magnus188/trimix-analysator/hardware/system-review/electrical/final-power-layout-review/README.md

# Final power-layout review — frozen 9f274 checkpoint

**The board is connected, but its power layout still merits targeted refinement before ordering.** Prioritize the U701 feedback/output-capacitor routes and the U101 bootstrap path; also attempt a properly grounded local REGN capacitor arrangement. These are observed departures from TI's short-loop guidance, not demonstrated instability, damage or invented numerical trace-length failures. No authoritative EDA, CAM or previous receipt was changed by this review.

Source: `hardware/pcb/analyzer/Trimix_Analyzer.kicad_pcb`, SHA256 `9f274fdf198f1bcb871a4fc360e76693f8a5b048553e6a02998141737956514f`. Exact selected parts are U101 BQ25895RTWR, U201 TPS63020DSJR, **U701 TPS61023DRLR**, U114 TPS22950CQDDCRQ1 and U115 TPS259470ARPWR. TPS62840 is absent and was excluded after the requested part name was corrected. The final XML SHA is `4512ae125c98cf091a24bf806f0ca78e14d59bcaffe59626d95386f100e0e609`.

## Four specific refinements

All distances below sum complete native track items along direct pad/track/barrel adjacency witnesses. They are **not** exact clipped terminal-to-terminal lengths, loop inductance, equivalent resistance or current ratings. Pad overlap and segment-entry tails can overcount length; the long paths were also inspected geometrically. Every item UUID and layer is in [native-local-paths.json](native-local-paths.json).

| Priority | Actual frozen geometry | Recommendation and evidence limit |
|---|---|---|
| 1 — U701 feedback | U701.1→R702.1: 29.8415 mm, comprising 3.2866 mm F + 26.5549 mm B, two barrels, 0.15 mm. The pad centres are only about 3.06 mm apart. The B route extends to (25.9226,67.1833), far beyond the local divider. | Bring the divider junction/return close to FB and remove the unnecessary excursion after proving all three FB endpoints remain connected. TI's device-specific SLVAES4 §5 explicitly calls for a short feedback network away from SW/inductor noise. A ground plane between layers provides shielding, but does not justify this excursion. No exact maximum length or achieved regulation error is asserted. |
| 2 — U101 bootstrap C103 | C103 is 0805 F(19,82.3),90°. BTST21→C103.2: 9.1496 mm F/B, two barrels; SW19→C103.1: 9.8375 mm F. | Reposition C103 and coordinate both connections, preserving the direct SW→L101 power path. Straight connections at the existing pose are blocked by SW copper and C108 GND; simply drawing a shorter line would short the board. TI specifies the 47 nF bootstrap connection and short local decoupling; it gives no length-based failure threshold. |
| 3 — U701 output hot loop | U701.6→C702.1: 6.8026 mm of 0.15 mm F routing. It exits left/down, reaches Y58.3836, then returns to C702.1 at (21.9,56.15). C702 GND and U701 GND each have grounded barrel connections. | Review C702 and the SW escape together to shorten/widen the output-capacitor loop. The obvious direct segment intersects CO_SW and fails clearance, even at 0.15 mm; it is not a valid drop-in fix. The output-capacitor return is TI's highest-priority boost switching loop. No load rating follows from the current trace width. |
| 4 — U101 REGN C107 | C107 is 22 µF/25 V X5R1206 at F(8,74.5),90°. U101.22→C107.1: 8.8842 mm total, 2.7097 mm F + 6.1745 mm In2, two barrels; minimum width 0.15 mm. C107 GND reaches the grounded barrel at (8,71.775). | Attempt a local capacitor arrangement with **both** REGN and quiet ground returns completed; retain package/effective-capacitance qualification. The prior B1206 relocation had an unresolved ground return and is not an improvement to adopt. TI requests nearby 4.7 µF/10 V ceramic decoupling for the gate-drive/bias regulator. The nominal full-item DC estimate, 57.47 mΩ, does not bound switching pulse impedance or prove failure. |

Manufacturer basis: [TI TPS61023 datasheet §10.1](https://www.ti.com/lit/ds/symlink/tps61023.pdf), [TI TPS61022/TPS61023 layout application note SLVAES4 §§2,3,5](https://www.ti.com/lit/an/slvaes4/slvaes4.pdf), and [TI BQ25895 pin21/22 and §11.1](https://www.ti.com/lit/ds/symlink/bq25895.pdf). The downloaded application note is included as [slvaes4.pdf](slvaes4.pdf). Straight-segment blocker UUIDs are recorded separately; they prove only that those particular shortcuts fail, not that a local relocation is impossible.

## Switching, capacitors and ground

BQ SW→L101 is entirely F.Cu, with no SW vias or parallel inner-layer power path. L101.2→C104.1 has a direct 4.5358 mm/1.0 mm F witness. The bank is **C104+C105, 44 µF nominal**, plus distributed C201/C202 and the newer local C1084.7 µF. U101.15→C108.1 is 1.5375 mm F. The longer SYS sense/battery/distribution routes must not be mistaken for the complete buck switching hot loop. Nothing here supports adding another arbitrary bulk capacitor; [the existing capacitance audit](../current-path-review/charger-output-audit/README.md) distinguishes typical derating estimates from guaranteed effective capacitance.

U201's two inductor networks remain F-only with no vias. Input C201, output C204–C206 and L201 retain compact front-layer connections: U201.10→C201.1 is 2.6063 mm; U201.4→C204.1 is 2.8374 mm; the two inductor witnesses are 2.85/2.20 mm. Individual pad escapes remain narrower than the power spines. C202 is distributed bulk, not a substitute for C201. FB/VINA and ground connections are present. This accords better with the placement intent in [TI TPS63020 §10.1](https://www.ti.com/lit/ds/symlink/tps63020.pdf), without establishing ripple, stability, current capability or temperature.

The [final root ground/path review](../routing-candidate/final-cleanup/root-review/README.md), independently checked against this source, retains all29 load/monitor witnesses. In1 is one grounded region with105 annular contacts; In2 has eleven grounded regions with21 contacts and is **not continuous**. The final U115 ground barrel (20.75,88.3), C114 ground barrel (11.1,91.1) and C115 ground barrel (12.8,93.95) occupy different local In2 islands, all connected to In1. Global ground continuity does not establish an ideal Kelvin/star return or bound parasitic coupling. Actual ripple/noise remains a separate test.

## USB protection and thermal paths

U115 has C115100 nF input bypass and C1144.7 µF shared output/U114-input capacitance. Input bypass has a 3.5286 mm B witness; output→C114 takes 13.3633 mm over B/F with two barrels. U115 GND→nearest witnessed grounded barrel is 5.347 mm B. The control resistor/capacitor paths are locally connected, but these distances and the split local In2 regions keep bypass/ground transient impedance unqualified. U114 has nearby R119, while its output uses the remotely connected C101; its output→C101 witness is 15.0107 mm F/In2, two barrels. These are genuine limitations to include in the **existing EL11/EL13 source-transition tests**, not a new claim of 6.396 V failure. [TI TPS25947 §8.4](https://www.ti.com/lit/ds/symlink/tps25947.pdf), [TI TPS22950-Q1 §9.4](https://www.ti.com/lit/ds/symlink/tps22950-q1.pdf).

U101 and U201 exposed pads are grounded and have respectively9 and15 package thermal bores. The [separate27-hole process packet](../routing-candidate/final-cleanup/fill-cap-process/README.md) explicitly requires filled, planarized, copper-capped treatment of these24 holes plus3signal VIPPO sites; supplier acceptance and solder-void/flatness results remain pending. U115's heat path is through its IN/OUT lands, not an invented grounded exposed pad; U114 and U701 likewise do not have the U101/U201 exposed-pad arrangement. Geometry/via counts do not determine junction temperature. EL10 still needs the real source/load envelope, PCB copper thermal analysis and enclosure measurements; no current or thermal rating is inferred from DRC.

## Disposition

The four targeted refinements above should be explicitly resolved before ordering, rather than hidden inside the broad EL10 hold. The owner is preparing isolated trials; **this report accepts no new geometry**. Any accepted correction needs native clearance/parity, source-bound conductor/ground witnesses, updated CAM/BOM/process checks and mechanical clearance revalidation. The completed9f274 CAM checkpoint remains intact.

Existing EL10 covers load/thermal and broad ripple testing; EL11 covers the unbounded OVP/cable/short transient envelope; EL13 covers cold/depleted startup. Those holds remain necessary, but do not themselves close avoidable bootstrap/feedback/local-capacitor layout work. No physical test, factory upload, order or release occurred.

Reviewed actual projections: [BQ](bq.png), [TPS63020](tps63020.png), [CO boost](co.png), [USB protection](usb.png). Pale green is the In1 ground projection, not a current-density solution. Both F and B panels use top coordinates.
