magnus188/trimix-analysator/hardware/system-review/software/ota/README.md

# OTA, storage and controlled maintenance review

The existing GitHub/HTTPS updater is retained. Firmware selection now requires the exact pre-v3 or v3 application name for the release version, a matching HTTPS repository URL, a valid release SHA-256 digest and a size fitting the **installed** inactive slot. Metadata may arrive in chunks and is bounded at 32 KiB. The downloaded image descriptor and its flash contents are checked before activation. Normal updates never change partition tables or program the C6.

GitHub documents `digest` in its [release asset API](https://docs.github.com/en/rest/releases/assets). Old releases without this metadata are rejected with a recovery message. This validates integrity relative to the HTTPS release source; it introduces no permanent security fuses or repository signing changes.

## Digital evidence

The latest source-bound rerun and its additional real-ESP-branch storage fixture are documented in [`final-verification/REVIEW.md`](final-verification/REVIEW.md). That pass adds 35 NVS-adapter assertions and concurrent startup-expiry tests. Earlier receipts below remain historical evidence; use the latest source manifest when matching results to code.

- **67** production-core assertions cover metadata, image identity, C6 metadata, update sequencing, injected transfer/activation failures, cancellation, truncation, oversized writes, timeout across clock wrap, storage journal failures, maintenance ownership and whole-startup probation deadlines. AddressSanitizer and UndefinedBehaviorSanitizer pass; the latest run is `ota-startup-sanitizers.log`.
- **24** history checks cover V1/V2 migration, distinct CO/CO₂ meaning, source provenance and new oxygen-cell identity. **13** cylinder checks include malformed input rejection. Both run under the same sanitizers.
- **17** concurrency checks exercise the production storage gate and maintenance coordinator, including 100 competing save/maintenance cycles. AddressSanitizer/UndefinedBehaviorSanitizer and a separate ThreadSanitizer run pass. The original **60** OTA/storage checks also pass after this correction. See `storage-maintenance-race-verification.json` and its three logs.
- `check_nvs_capacity.py` runs Espressif's NVS partition generator against full current journals plus both retained legacy history versions. The synthetic 24 KiB image has 261 free entries; the largest guarded write needs 202 entries including the 128-entry reserve. It contains dummy data and is never flashed.
- `verification.json` records source hashes. Root-level verification supplies fresh integrated firmware builds and the combined suite.
- **13** offline release-validator tests pass. Both existing P4 application binaries pass descriptor/revision/actual-partition checks, and generated release metadata passes the production OTA parser for both families. See `release-startup-review.md`; these checks never publish or install a release.

## Storage and update behavior

One initializer owns NVS and **never erases it automatically**. Settings, history, cylinder profiles and Wi-Fi use CRC-protected, versioned namespaces with inactive-slot writes, readback and a final selector commit. Legacy keys remain readable for rollback. Calibration retains its independent per-channel journal and acquisition compatibility checks. Explicit Forget Wi-Fi removes only credential keys; settings reset never erases calibration/history.

A new OTA image starts with persistence read only. An independent supervisor starts before NVS/LVGL initialization and gives a pending update 60 seconds for essential startup. Acceptance requires observed UI heartbeats, responsive system/acquisition workers and successful NVS initialization, with a 20-second health-check window after service startup inside that overall deadline. Completion and expiry have one atomic winner; late startup cannot accept itself. Optional Wi-Fi initialization runs in its own task. Optional sensors, network association and thermal warm-up are not acceptance requirements. A failing pending image rolls back when a previous image exists; otherwise available recovery UI and wired recovery remain, without erasing data or deliberately causing a reset loop. Changed acquisition revisions deliberately require recalibration rather than relabeling incompatible records.

Maintenance stops measurements and waits for completion before holding storage writes. Failed/cancelled OTA resumes normal work; successful OTA remains held until the coordinated reboot. The GPIO power controller remains responsible for independent held-button shutdown. Current commissioning firmware requires verified battery/charger reserve to install OTA; a bare display without those measurements must use wired recovery.

All application NVS mutations, including calibration slot/selector commits and explicit deletion of legacy Wi-Fi credentials, now use the same storage mutex. A pause request closes admission before waiting for an in-flight transaction. Maintenance reaches its held state only after that transaction completes. If draining exceeds the remaining maintenance budget, maintenance fails and reopens admission; it does not claim that storage is safe to interrupt. Pausing between calibration journal phases rejects the later selector commit and preserves the previous active calibration. A selector commit already in progress completes before the held state is reached.

The lock order is oxygen configuration, then calibration core, then storage. Storage callbacks perform only their low-level persistence operations and never acquire configuration/core locks or call another storage API. Maintenance invokes measurement/flush hooks before taking the storage mutex. This prevents the pause from waiting on a calibration lock while a calibration save waits on storage. The gate's timeout bounds waiting for the mutex, not the underlying flash operation, which cannot be cancelled safely in software.

The C6 recovery build remains separately enabled, hash-pinned and dependent on the staged `slave_fw` partition. Its descriptor checks are now bounded and verify C6 chip identity. No C6 update was performed.

## Remaining physical checks

No firmware flashing, live OTA, flash power cuts, real NVS endurance, C6 programming or device reset was performed. Interruption tests inject failures into the **same installer state machine used by the ESP-IDF adapter**, while the underlying network/flash hardware remains untested. The concurrency tests use the production mutex/gate/coordinator and controlled callbacks representing flash transactions; they do not exercise physical ESP flash timing. A selector commit whose acknowledgement is lost may leave either complete committed version; it must never produce a partial record. Bench-test restart, rollback, saved calibration, low-power updates and recovery with the assembled hardware before treating OTA as qualified.
