magnus188/trimix-analysator/hardware/system-review/electrical/routing-candidate/complete-controls-root-review/README.md

# Completed control routing — parent review

The frozen `b305a4c3…` candidate passes the scoped review needed for isolated final consolidation. Its native KiCad report has zero unconnected items, zero copper/courtyard errors and zero schematic-parity findings. **32 assembly/dangling warnings remain; this is not the manufacturing release.**

[The parent receipt](parent-controls-review.json) verifies every file bound by the controls handoff and records visual inspection of all four actual filled-plane overlays. In1 remains one connected ground region. In2 remains eleven grounded regions; it must not be described as a second continuous plane. The recorded native ground contacts are retained, and the 22 explicit conductor witnesses and seven ordinary-via surface-interface checks pass.

[The independent power-path comparison](power-path-comparison.json) preserves all 29 requested ordered power/monitor witnesses from the completed SYS baseline. Complete trace-item lengths and nominal resistance contributions are diagnostics, not actual equivalent circuit resistance or current/thermal ratings.

The owner may now consolidate exact part metadata, the Q110 manufacturer footprint, C708's ordinary ground-via correction, dead-copper cleanup and markings. That changed source needs fresh native connectivity, ground-contact, parity, ERC-exception, CAM and CAD checks. The three filled/capped interfaces require explicit factory process acceptance; neither their scoped clearance rules nor zero opens establish assembly yield or charging safety.
