magnus188/trimix-analysator/hardware/system-review/electrical/routing-candidate/final-cleanup/README.md

# Completed main routing review checkpoint

The frozen main source is `frozen-bundle/hardware/pcb/analyzer/Trimix_Analyzer.kicad_pcb`, SHA256 `9f274fdf198f1bcb871a4fc360e76693f8a5b048553e6a02998141737956514f`. Native KiCad reports zero violations, zero opens and zero schematic mismatches. It has 169 footprints, 2280 track segments and 301 routed vias. **Manufacturing/physical acceptance remains on HOLD.**

The [geometry manifest](frozen-bundle/review/geometry-handoff-manifest.json) binds PCB, XML, STEP and all 153 maximum-envelope rows. The STEP uses normal pad thickness and unit-scale purchased-part reference models. U110/L201/L701 model files are absent from the installed KiCad model library; their explicit maximum envelopes remain mandatory. No absent or generic model is treated as a dimensional pass.

- [Root power/ground review](root-review/final-power-ground-review.json): all 29 critical conductor witnesses retained, continuous In1, 105 In1 and 21 In2 anchors retained, every In2 region anchored.
- [Aggregate consolidation delta](aggregate-consolidation-delta.json): 519 structural checks; no part, pad, pose or model change during cleanup. The accepted C708 ordinary-via dogbone and dead-copper cleanup are explicit. All 195 physical pad-connectivity partitions are conserved. `prune2/REJECTED.txt` retains the negative control that caught a mistakenly removed live midpoint connection; the accepted source restored it and trimmed only its dead extension.
- [Native routing audit](frozen-bundle/review/routing-audit.json): 12 checks pass. [Via/paste interface audit](frozen-bundle/review/via-assembly-audit.json): all 301 routed vias checked; only the exact three VIPPO sites are permitted in populated SMT paste.
- [Root ERC/firmware contract review](root-review/final-contract-erc-review.json): one precisely reviewed TI-permitted LM66100 ST-ground ERC error, no unexpected ERC findings; all 70 logical firmware-contract checks pass. `source-validation/electrical/electrical-audit.json` has 217 passing assertions; `source-validation/audit-faults/audit-fault-tests.json` accepts the baseline and rejects all 12 injected wiring/value faults.
- [CAM input manifest](frozen-bundle/review/cam-input-manifest.json) binds the unmodified Gerbers, drills, all-component CPL and population ledgers. Independent final CAM results are under `../../main-final-independent/final-9f274fdf/`.

`frozen-bundle/cam/assembly-reference-map.csv` lists every reference, value, MPN, side and position. Separate lists contain 24 factory components, 121 manual components, 6 DNPs and 18 PCB/harness features. `marking-legend.csv` identifies the 146 printed references. The 23 dense assembly-only references have [four locator sheets](assembly-drawings/assembly-only-locators-1.svg); subsequent pages use suffixes 2–4. These show selected pads in blue and use explicit top-view coordinates for both sides. They complement actual CAM silk and the CSV. Raw native Fab exports are retained as diagnostics; their overlapping value text is not claimed to be the clear assembly drawing.

The [factory stencil supplement](factory-stencil/derivation-receipt.json) removes only non-factory paste apertures from a derived copy. The original routed source and full-board paste remain frozen for comparison. The [27-hole process map](fill-cap-process/README.md) requires resin fill and copper cap for all 24 package thermal bores plus 3 signal VIPPO. A quotation must establish drill classification, flatness, stencil thickness/apertures, void/coverage acceptance and double-sided reflow. Neither paste geometry nor a generic capability page proves assembled quality.

Final source-bound enclosure integration, actual sensor/host/harness mating and power entry, cell/NTC identity, USB transient/current/standby/true-off recovery, thermal, EMC, gas and calibration qualification remain separate acceptance gates. No physical test or purchase has been performed.
