magnus188/trimix-analysator/hardware/system-review/electrical/routing-candidate/lower-host-proposal/README.md

# Lower HOST routing scout

The frozen board is unchanged. No patch is proposed. See [blocker.json](blocker.json) for exact search bounds and copper barriers; baseline native DRC is [before-drc.json](before-drc.json). The finite grid search does not prove that every possible freeform route is impossible. The authoritative board was not written.
