magnus188/trimix-analysator/hardware/system-review/electrical/routing-candidate/monitor-root-review/README.md

# Independent review of voltage-monitor routing

The frozen combined candidate `b116e2cce2ee3c3fa5feace5b85cfb85bf47168ddc3b5d846f0f5b15e516bc93` passes this scoped saved-copper and connectivity review. It adds the raw/protected USB voltage-monitor connections and shortens the charger's narrow input-pad escape. The preceding source is `609a6241ce50cbe3d40f7a1676c455092db583875895eeb8236083bf2c5f0ef1`.

[geometry-review.json](geometry-review.json) records unchanged zone definitions, a continuous In1 ground region, anchored In2 ground regions and no lost ground contacts. All three new Ø0.50/0.25 mm vias pass an independent check against every surface-mount land, including same-net lands, with at least 0.05 mm separation. Their closest foreign-copper gaps are 0.2180, 0.4051 and 0.2065 mm, above the 0.20 mm rule. The root reviewer inspected the [ground comparison](ground-and-power.png) and [actual front/back copper overlays](outer-copper.png) on 2026-09-07.

[native-witnesses.json](native-witnesses.json) contains five separate native trace/barrel paths: J101 to R110 and TP1002, U115's protected output to R113, and U114's output to U101 and C101. These paths do not infer conduction through components or filled zones. The raw USB **load** path into U115 remains a separate unfinished connection.

The retained 0.25 mm CAD segment at U101 pin 1 is 0.5375 mm long, but that is not 0.5375 mm of exposed narrow conductor. The adjacent 0.40 mm track directly overlaps the actual pin land, confirmed with native copper shapes; the selected connectivity witness bypasses the nominal narrow segment. Neither track-width arithmetic nor this overlap establishes a thermal or current rating.

The captured owner DRC report has **seven unconnected items**, 14 dangling tracks, seven dangling vias, seven silkscreen overlaps and four silkscreen-over-copper warnings; schematic parity has no findings. These unfinished routes and markings still require correction. The review scripts only read the immutable board snapshots and do not rerun or suppress the owner's DRC.

This result permits continued integration of the bounded change. It is not a fabrication release. Final combined routing, actual electrical limits, manufacturing exports, CAD fit and physical charging/thermal/transient tests remain separate acceptance gates.
