magnus188/trimix-analysator/hardware/system-review/electrical/sensitive-layout-refinement/r504-independent/README.md

# R504 rear excitation-monitor placement — bounded independent review

**Accept the proposal for merged digital review and prototype noise testing; do not describe it as noise-qualified.** There is no demonstrated hard electrical violation from this placement. Keeping the trace outside the inductor projection would be preferable if a short, independently checked route becomes available, but the obvious northern B-layer detours cross the existingHE_3V0 feed. Reopening that topology solely to avoid this projection is not justified by measured evidence currently available.

The read-only source is root's `root-r504/candidate3/Trimix_Analyzer.kicad_pcb`, SHA`c13e2fc459b43f194a146776127d15c0c415135d9d243c21dad3bef570cfc53b`. It does **not** contain the proposed L701 relocation: this review projects the selected [Coilcraft XGL4020-102MEC](https://www.coilcraft.com/pdfs/xgl4020.pdf), max4.3×4.3mm, at the supplied futurecentre(19.5,50.65). Its north edge isY48.5 at maximum body size. The component is specified as a shielded power inductor; no guaranteed external magnetic-field limit was located in its datasheet.

R504 remains10k0.1%, physicallyB(18.25,48),180°. HE_EXC_DIVwrapY48.95 crosses beneath the projected northern part of L701: about.518mm² of the .15mm-wide routed copper lies under the maximum body projection. **Every part of that overlapping copper has continuous In1GND between the F-layer powerstage and B trace** in this frozen source. The local route has a small.084mm² area outside In1 elsewhere near its transition/antipad; the area under the inductor outsideIn1 iszero. A copperplane and shielded core reduce coupling risks but do not prove magnetic isolation or an interference-amplitude bound.

This node is the **excitation diagnostic** (R504/R50510kdivider, C504100nF, U502.7/AIN2); it is separate from the RN501 helium bridge midpoint and its differential measurement. Ideal low-frequencyThevenin resistance is5kΩ, nominaltimeconstant.5ms andcorner318Hz. That RC calculation does not bound noise coupled after the filter, ground bounce, high-frequency parasitics or rectification. [TI ADS122C04 §11.1](https://www.ti.com/lit/ds/symlink/ads122c04.pdf) recommends separating noisy and analog routing, minimizing source/return loop area and preserving good ground-return paths. No manufacturer numerical keep-out distance was found that makes this particular projection an automatic pass or failure.

Firmware `main/sensors/acquisition_engine.cpp:61` doubles the sampled monitor voltage; line65 latches an excitation fault outside2.9–3.1V. Consequently the practical failure to test is false or missed excitation qualification as the CO boost switches between start-up, light-load and normal-load operation. Exercise those states while logging rawAIN2, excitation fault behavior and helium raw differential samples. Observe REGN/HEsupply stability separately; do not infer concentration accuracy from absence of a fault. Check actual transient/ripple response at C504 with an appropriate short-ground probe and compare ADCreadings with COconverterdisabled/enabled.

Two purely geometric northern wraps atY47.2 andY46.4 both intersect HE_3V0copper at the required.20clearance. `review.json` records those blockers and the exact source/firmwarehash; these are read-only rejected suggestions, not new routes or nativeDRC results. No authoritative file or candidate was modified. The merged board still needs the owner's finalnativecheck and fresh source-bound plane coverage inspection.
