magnus188/trimix-analysator/hardware/system-review/electrical/routing-candidate/final-cleanup/root-review/README.md

# Independent final routing review

The frozen main board `9f274fdf…6514f` passes the scoped power and ground review. [The receipt](final-power-ground-review.json) binds all nine geometry-handoff files, the source board, reader, native path inventory and inspected renders. The source files were not modified.

All 29 requested power and voltage-monitor paths have explicit native pad/track/barrel witnesses, with the same ordered physical items as the completed routing checkpoint. One voltage-monitor branch has a shortened unused trace tail; its complete-item diagnostic decreases from 154.291 to 152.210 mΩ. This is not a measured or equivalent path resistance, load-current rating or thermal prediction.

The saved In1 ground fill remains one connected region with all 105 prior annular contacts. In2 has eleven separate grounded regions and retains all 21 prior contacts; it is not a second continuous ground plane. No In1 signal track was introduced. Source geometry shows effectively no removed ground fill beyond polygon numerical precision and 5.508 / 0.351 mm² additional fill on In1 / In2 after unused copper cleanup. Both comparison images were inspected.

Native DRC/parity, the exact ERC exception, manufacturing process inspection and Fusion fit have separate receipts. The manufacturing package is on hold, including explicit factory treatment of the selected signal and package-thermal holes, downstream transient evidence, power-entry qualification, actual cells and connector/seal measurements. This scoped result is not an order release.
