magnus188/trimix-analysator/hardware/system-review/electrical/routing-candidate/sensitive-layout-refinement/root-final-review/README.md

# Independent review of the local power-layout refinement

**Passed digitally for the stated electrical layout scope. Prototype order remains HOLD.**

This review binds the frozen PCB `0962ad86f9834ce71b6439d0f95db603753801153490e78f387a88521e582788`, compared with the preserved routed `9f274fdf…6514f` board. All nine files in its geometry handoff match their declared hashes and sizes. The authoritative board, final CAD integration, manufacturing exports and physical qualification have separate gates.

The four layout concerns identified in the previous inspection have been corrected. These are lengths of complete native trace items, including portions overlapping lands; they are **not extracted loop inductance, equivalent resistance or manufacturer distance limits**.

| Connection | Earlier trace length | Refined trace length |
|---|---:|---:|
| U101 bootstrap pin → C103 | 9.150 mm | 1.356 mm |
| U101 switch pin → C103 | 9.838 mm | 5.621 mm |
| U101 REGN pin → C107 | 8.884 mm | 2.921 mm |
| U701 output pin → C702 | 6.803 mm | 1.603 mm |
| U701 feedback pin → R702 | 29.841 mm | 1.040 mm |

C702 also has a direct front-layer ground connection to U701, independently traced without a barrel transition. The return uses a 0.35 mm trunk and a short 0.20 mm escape at the IC pin; its existing ground anchors are retained and an ordinary ground stitch is added. The feedback trace and output-capacitor connection also remain on the front layer. These changes follow the compact-loop guidance in the [TI BQ25895 datasheet](https://www.ti.com/lit/ds/symlink/bq25895.pdf), [TPS61023 datasheet](https://www.ti.com/lit/ds/symlink/tps61023.pdf) and [TI boost-converter layout note](https://www.ti.com/lit/an/slvaes4/slvaes4.pdf). No claim of measured stability or EMI performance follows from the geometry alone.

All **29 main power and voltage-monitor paths retain exactly the earlier ordered native copper edges**. All 35 inspected local paths are connected. The saved In1 ground fill remains one connected region with 107 grounded anchors. No retained anchor loses contact. The removed C107 front-ground via at (8,71.775) is replaced by the short rear connection to (16.05,78.05). The other new anchors serve the local CO feedback/ground-return area. In2 retains exactly its previous filled geometry: 11 grounded regions and 21 anchors; it is not described as a second continuous ground plane. No signal tracks were introduced on In1 and zone definitions are unchanged.

The full saved-ground comparisons and labeled BQ/CO copper views were visually inspected. Native KiCad reports zero violations, zero unconnected items and zero schematic mismatches for this frozen source. The root receipt is `root-power-layout-review.json`; reproducible native-contact and independent saved-polygon readers are bound there.

The exact C107 replacement, its typical DC-bias comparison and higher startup charge are reviewed separately in `electrical/sensitive-layout-refinement/c107-0805/`. Its 47 µF label must not be mistaken for guaranteed capacitance under voltage, temperature and aging. R504's rear-side excitation-monitor routing is covered by the primary ground plane where it crosses the inductor's northern projection; the separate review in `electrical/sensitive-layout-refinement/r504-independent/` retains switching-noise and false/missed excitation-limit tests. The gas sensors and RN501 bridge reference remain unchanged.

Fresh source/ ERC verification, independent manufacturing-file checks and the real carrier openings for C103/C107/R504 remain separately required. Source-current and transient protection, Guition power entry, actual cells and connector mates, supplier fill/cap/stencil approval and all physical testing remain open. This report does not release an order.
