magnus188/trimix-analysator/hardware/system-review/software/power/off-charge-review/standby-evidence/README.md

The current receipt.json was refreshed from ../../input-isolation/evidence/receipt.json after rerunning the complete prior standby/backlight/maintenance scope plus HIZ tests on current sources. Its log paths identify the authoritative current logs. Older log files in this directory are historical; the complete pre-HIZ receipt/log set is archived in ../archive-before-hiz/standby-evidence/.
