magnus188/trimix-analysator/hardware/cad/previews/front.png

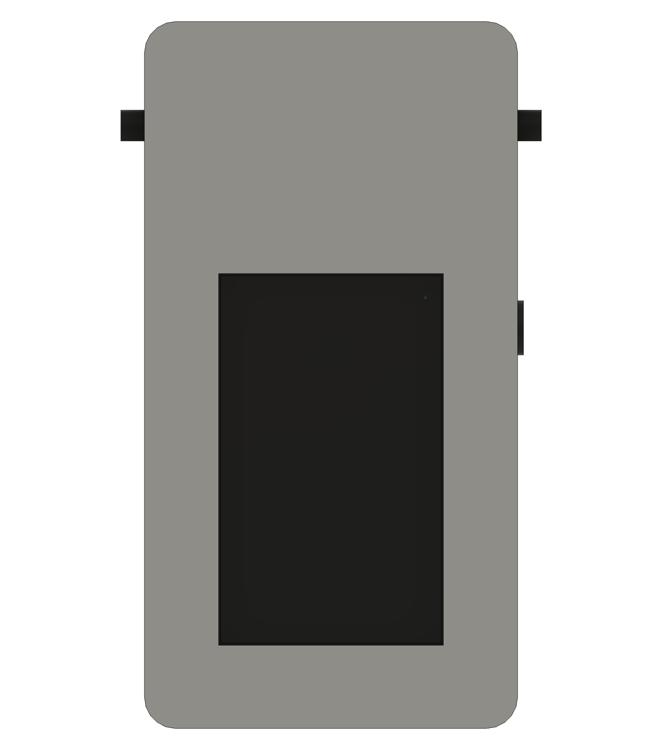
hardware/cad/previews/front.png
