magnus188/trimix-analysator/hardware/cad/previews/rear-open.png

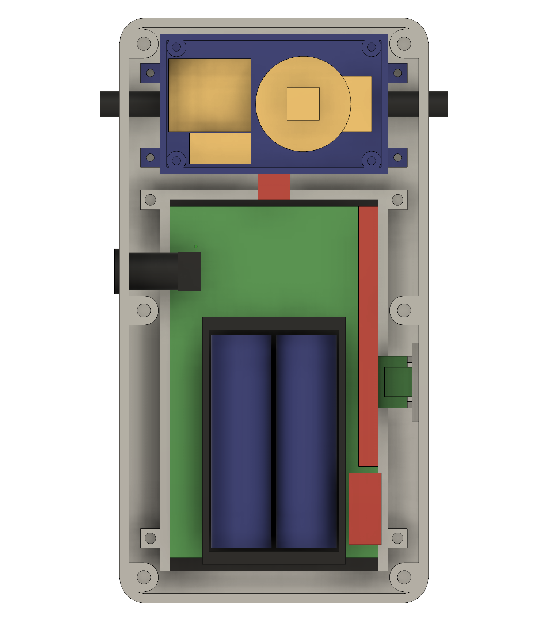
hardware/cad/previews/rear-open.png
