magnus188/trimix-analysator/hardware/cad/previews/rear.png

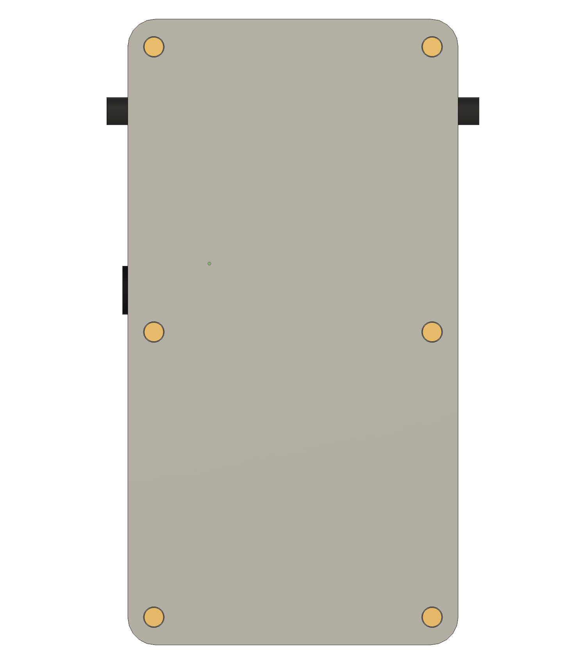
hardware/cad/previews/rear.png
