magnus188/trimix-analysator/hardware/cad/previews/section.png

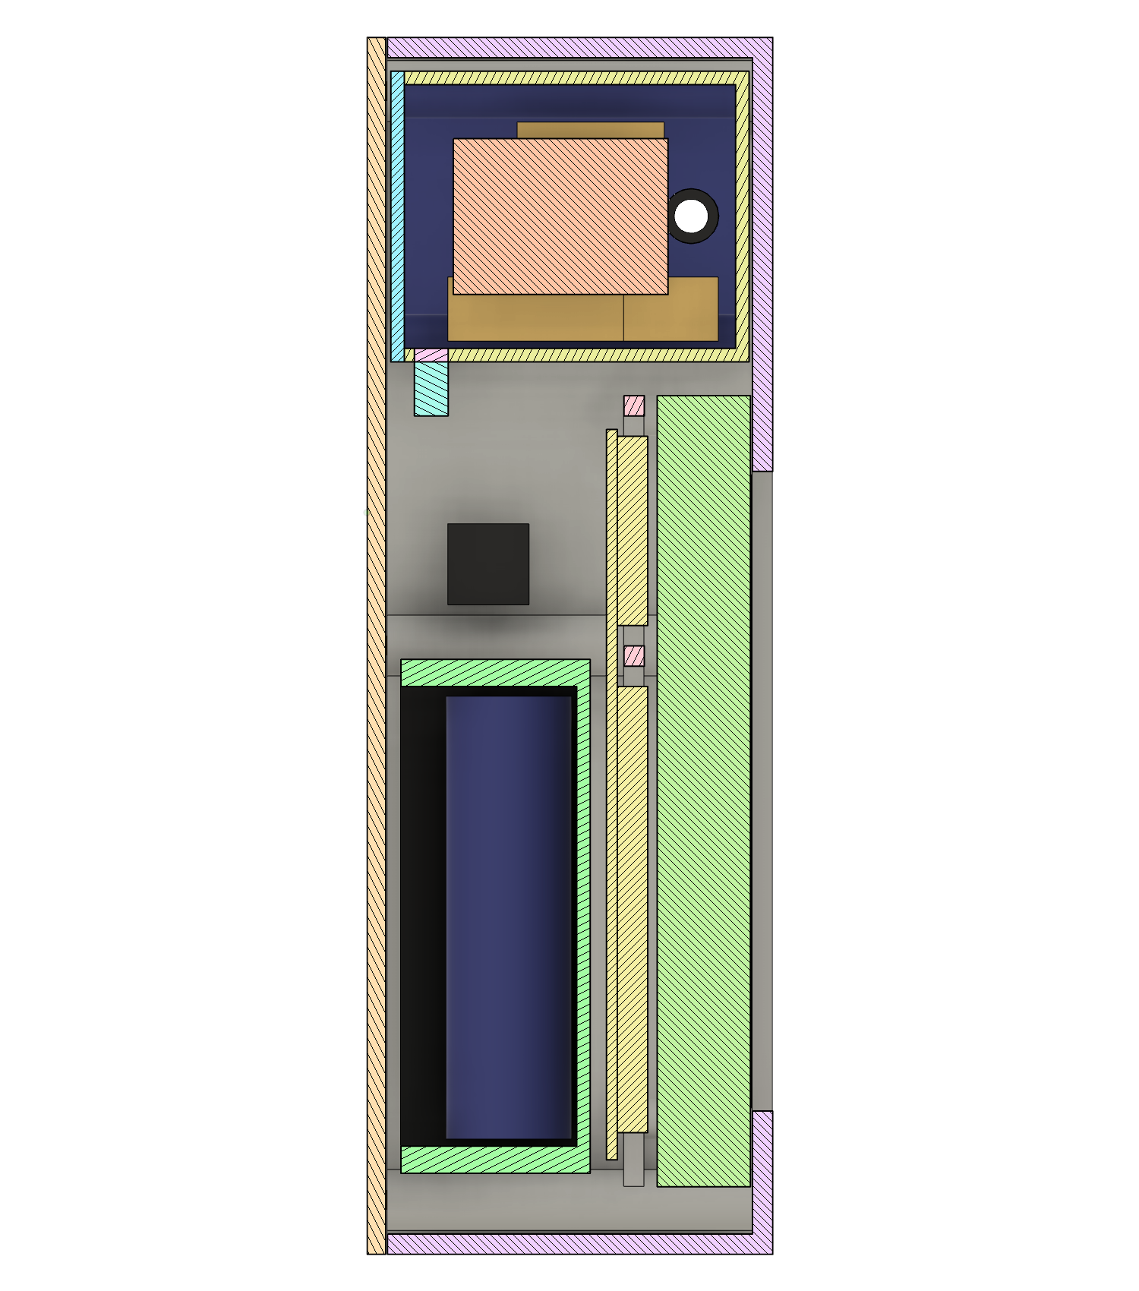
hardware/cad/previews/section.png
