magnus188/trimix-analysator/hardware/cad/rev04/previews/exploded.png

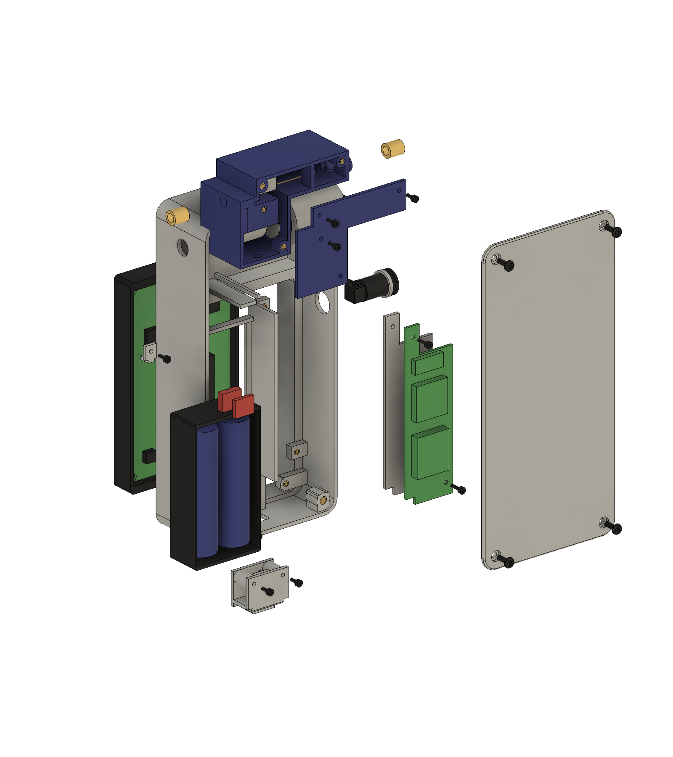
hardware/cad/rev04/previews/exploded.png
