magnus188/trimix-analysator/hardware/cad/rev04/previews/front.png

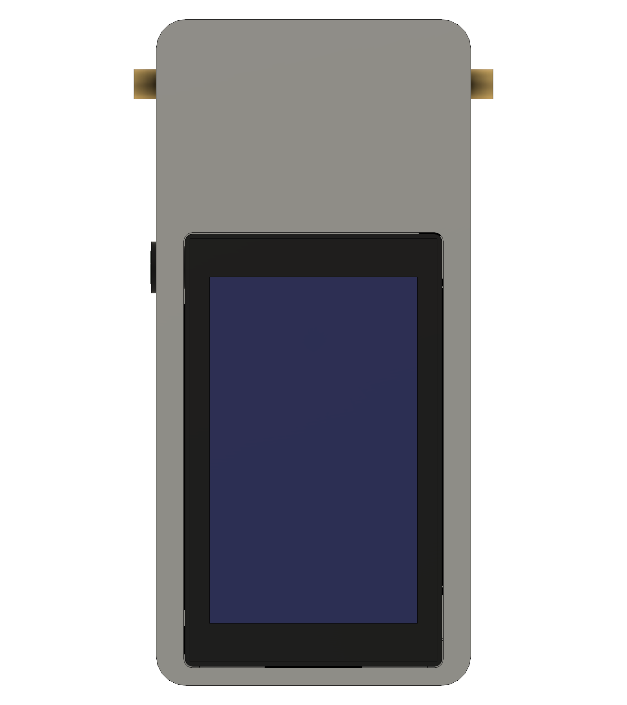
hardware/cad/rev04/previews/front.png
