magnus188/trimix-analysator/hardware/cad/rev04/previews/left.png

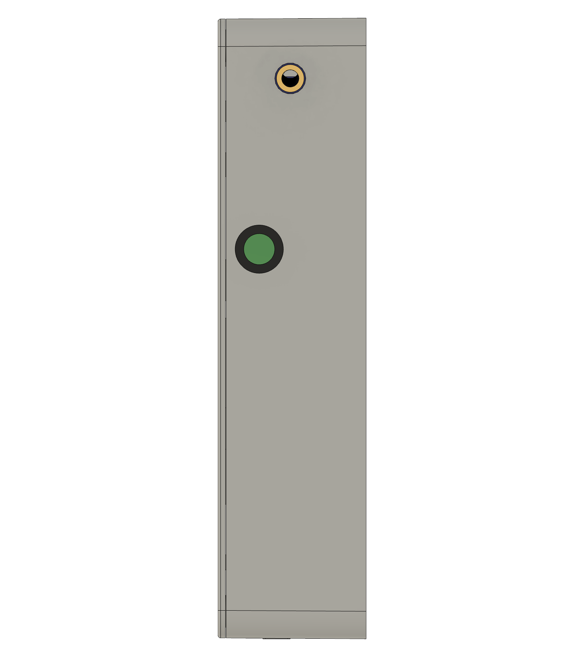
hardware/cad/rev04/previews/left.png
