magnus188/trimix-analysator/hardware/cad/rev04/previews/section-bb.png

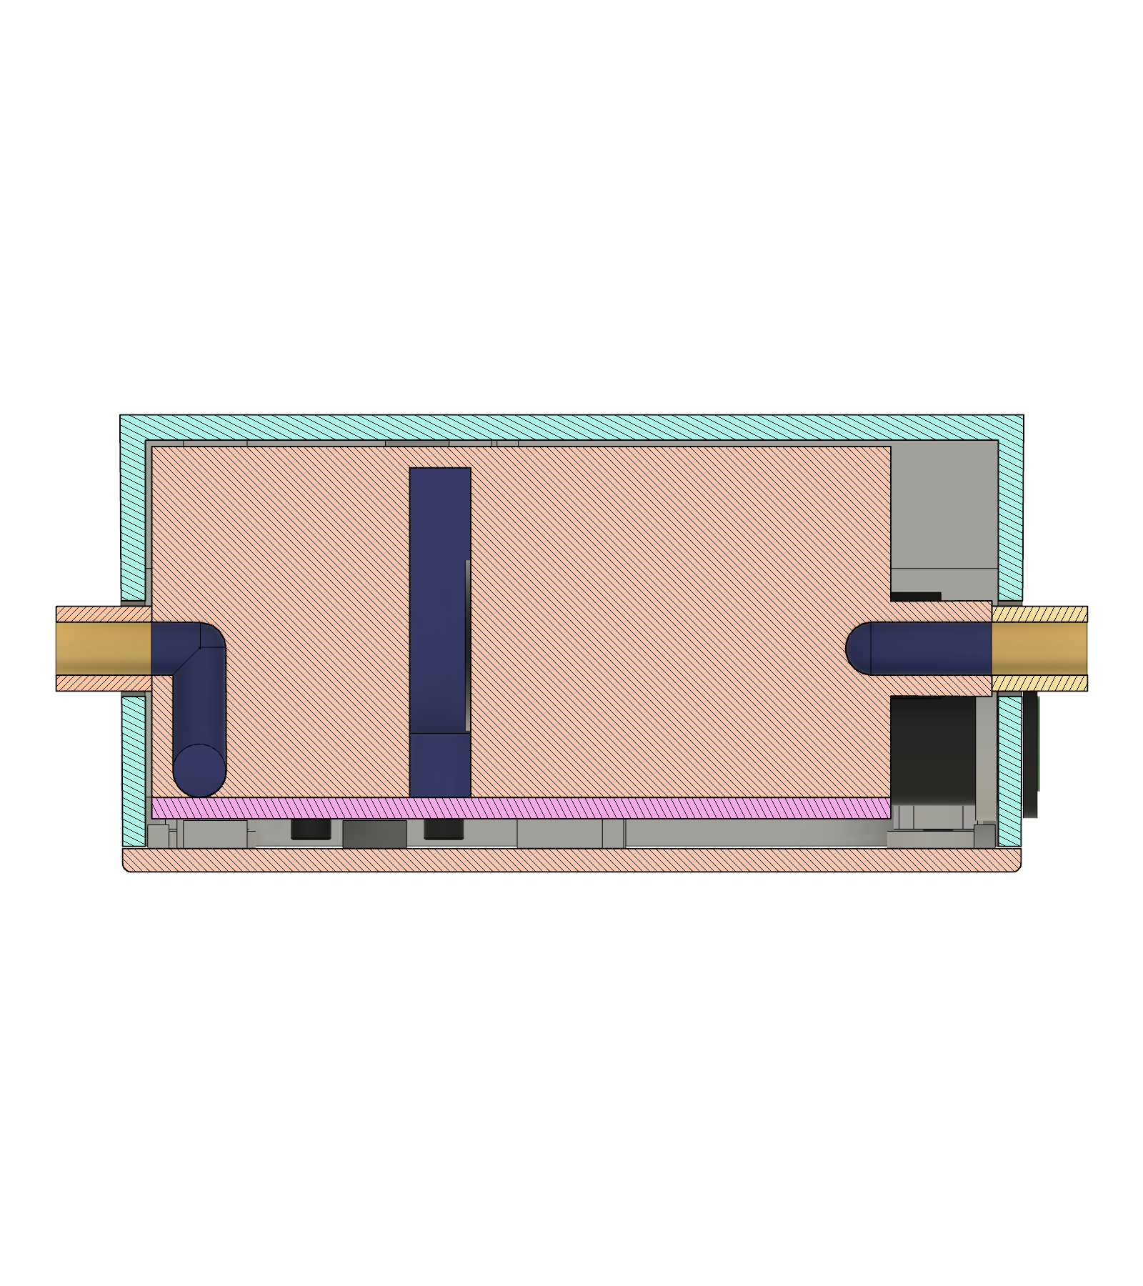
hardware/cad/rev04/previews/section-bb.png
