magnus188/trimix-analysator/hardware/pcb/integration/exports/USB_Input-top.png

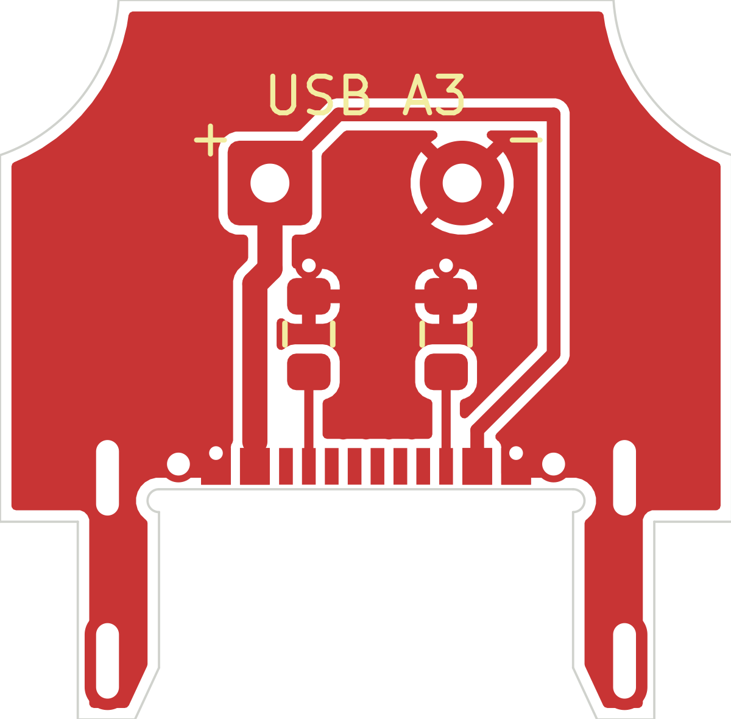
hardware/pcb/integration/exports/USB_Input-top.png
