magnus188/trimix-analysator/hardware/pcb/integration/reference/main-back.png

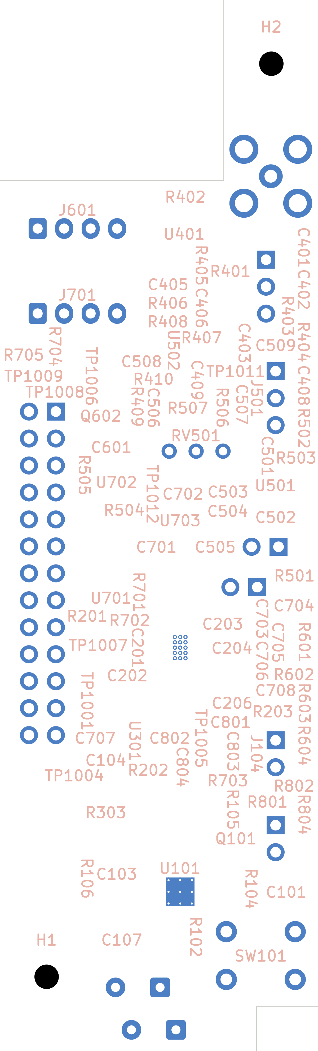
hardware/pcb/integration/reference/main-back.png
