magnus188/trimix-analysator/hardware/pcb/integration/reference/main-front.png

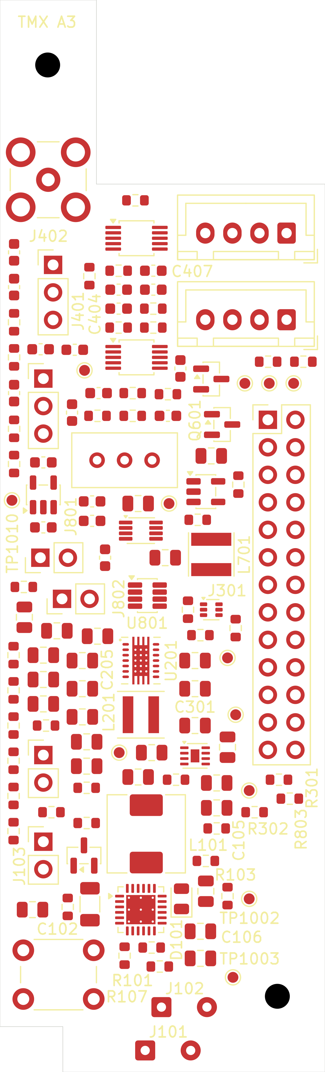
hardware/pcb/integration/reference/main-front.png
