magnus188/trimix-analysator/hardware/pcb/integration/reference/usb-back.png

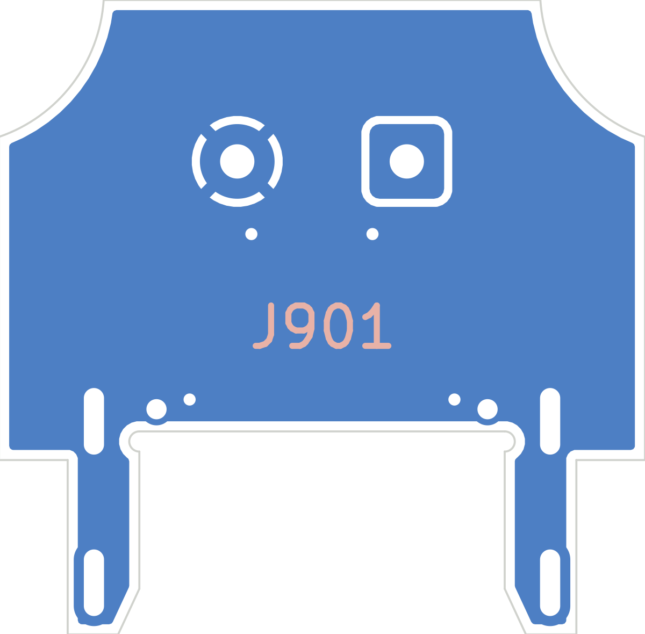
hardware/pcb/integration/reference/usb-back.png
