magnus188/trimix-analysator/hardware/pcb/integration/verification/software-calibration/schematic-views/Helium.png

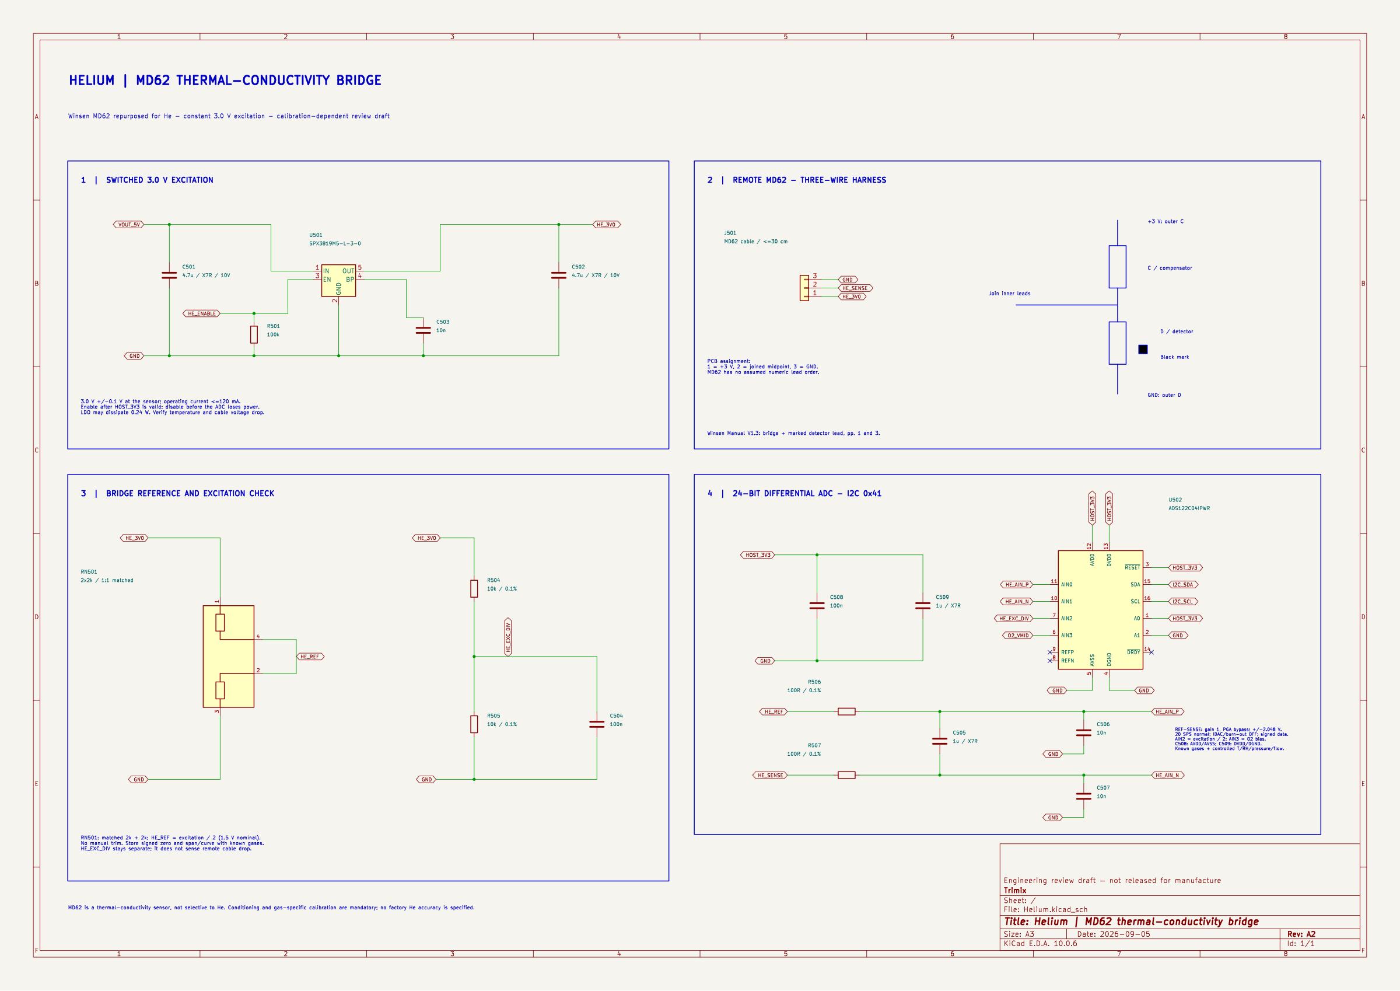
hardware/pcb/integration/verification/software-calibration/schematic-views/Helium.png
