magnus188/trimix-analysator/hardware/pcb/integration/verification/software-calibration/schematic-views/Trimix_Analyzer.png

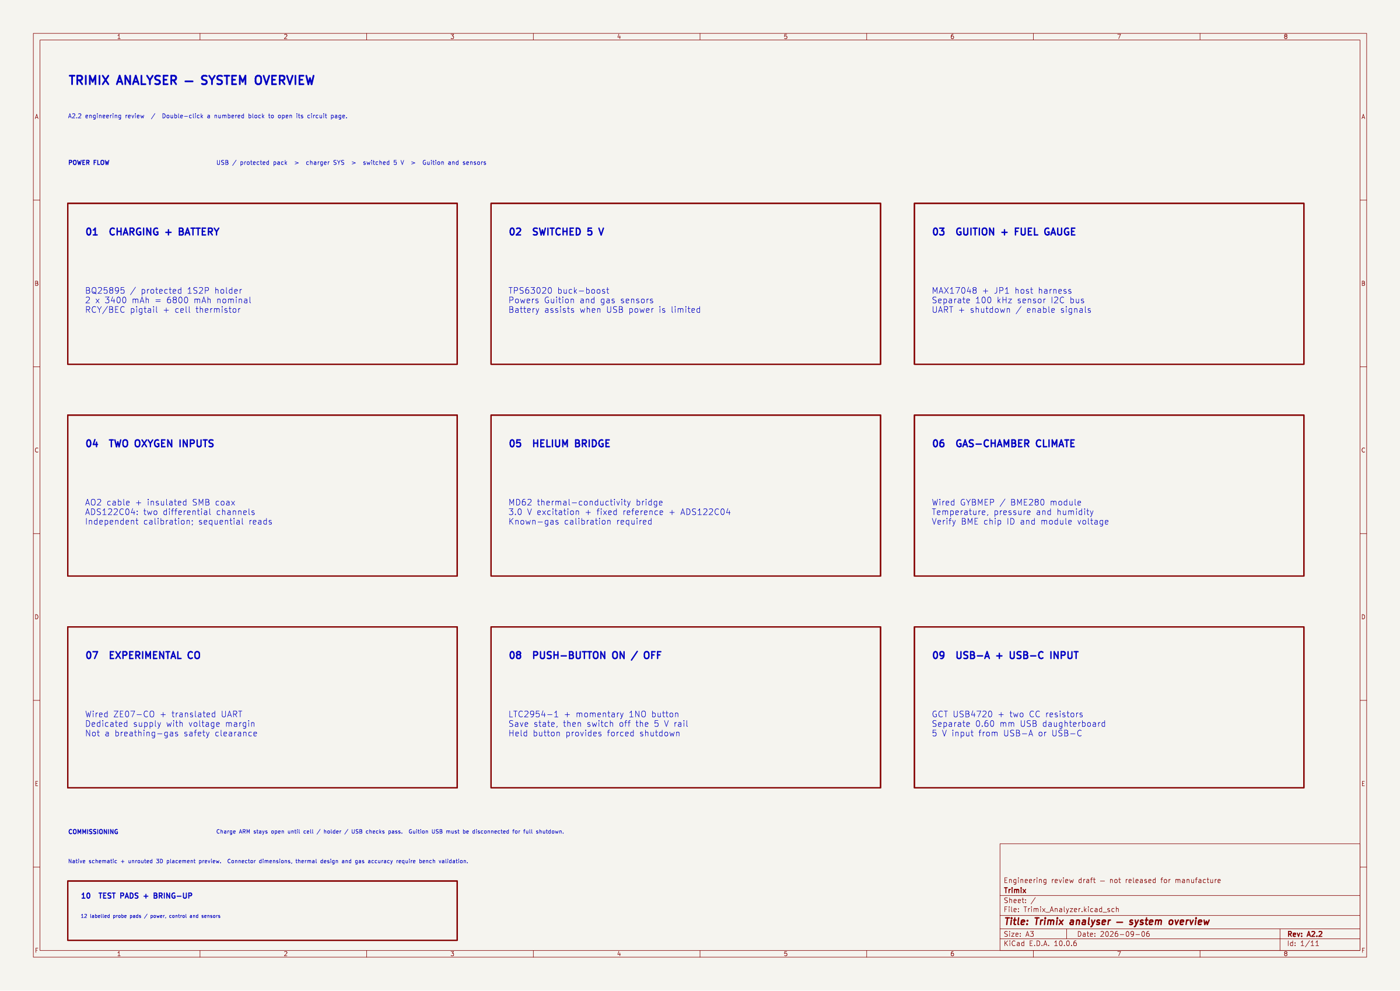
hardware/pcb/integration/verification/software-calibration/schematic-views/Trimix_Analyzer.png
