magnus188/trimix-analysator/hardware/pcb/verification/power/overview.png

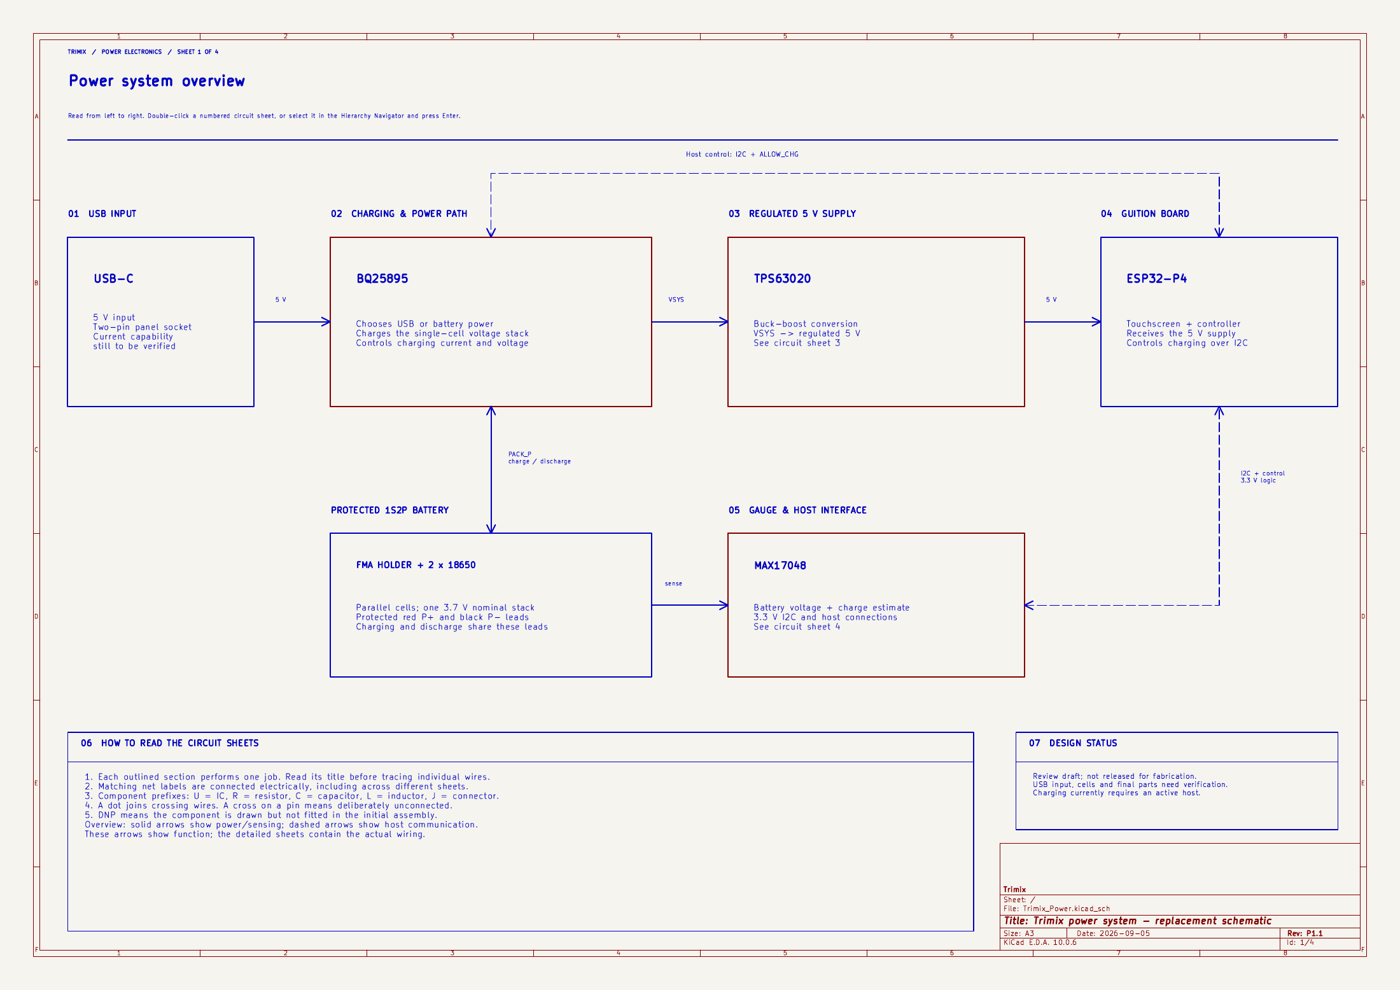
hardware/pcb/verification/power/overview.png
