magnus188/trimix-analysator/hardware/system-review/electrical/analogue-simulation/filter-study.png

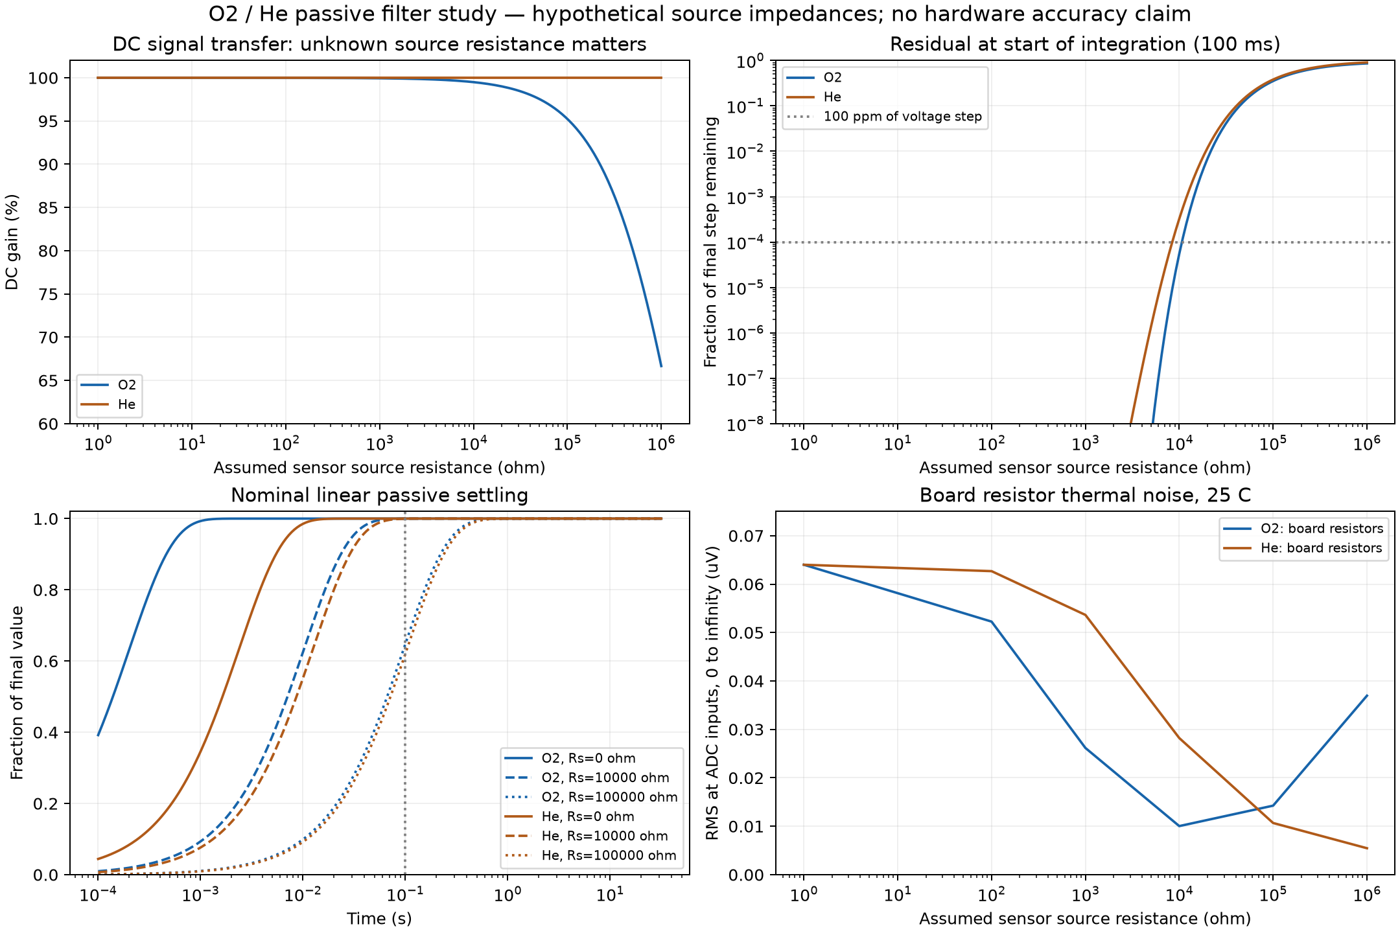
hardware/system-review/electrical/analogue-simulation/filter-study.png
