magnus188/trimix-analysator/hardware/system-review/electrical/capacitor-research/C0805C103K5RACTU-curves.png

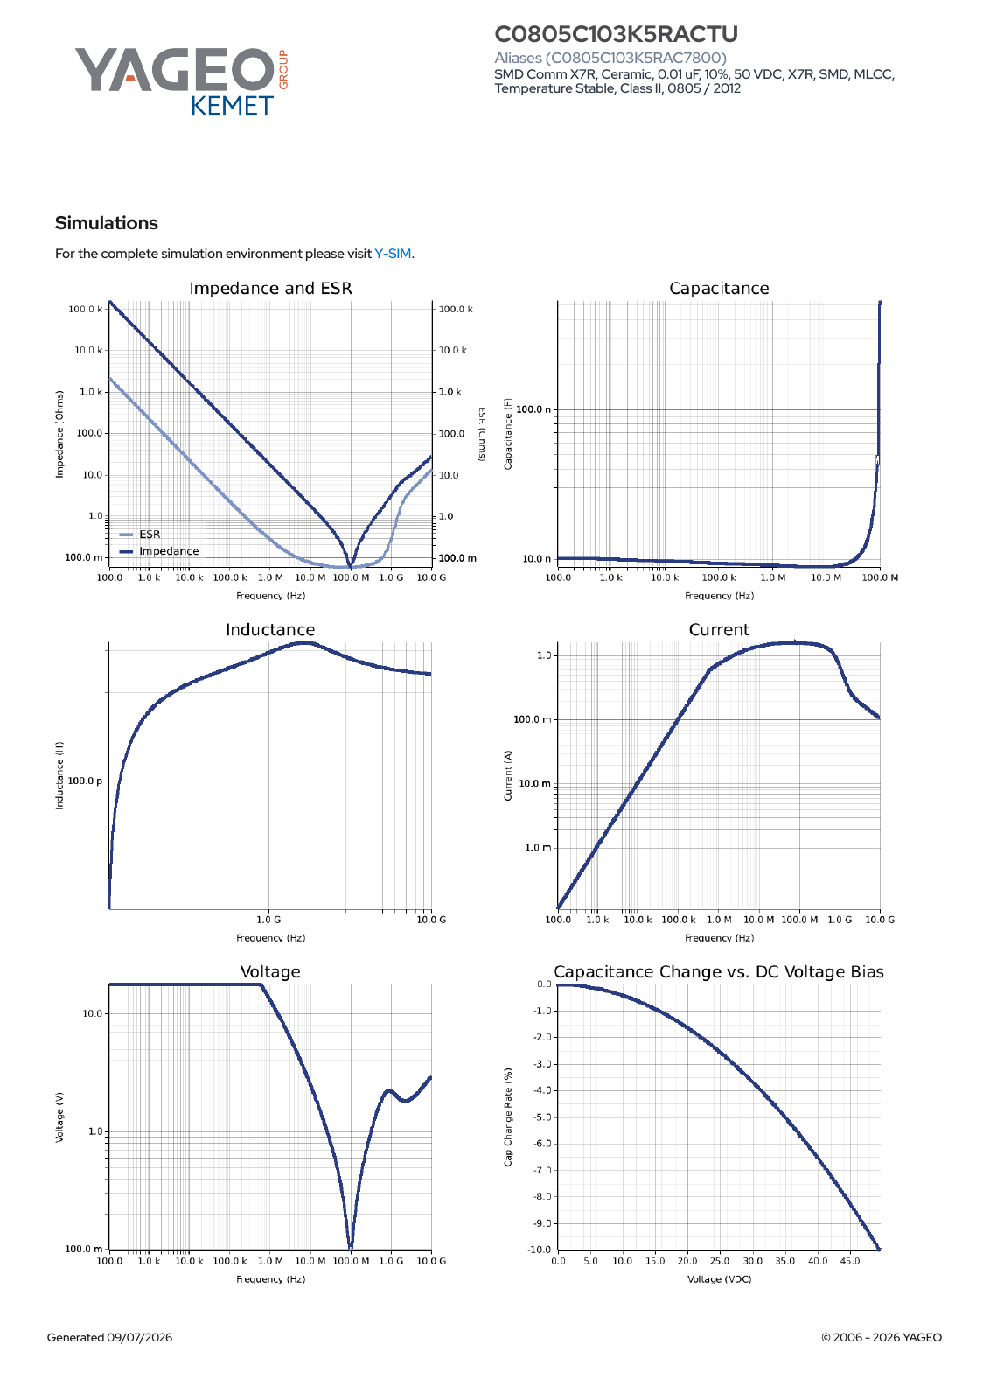
hardware/system-review/electrical/capacitor-research/C0805C103K5RACTU-curves.png
