magnus188/trimix-analysator/hardware/system-review/electrical/host-harness-review/harwin-drawing.png

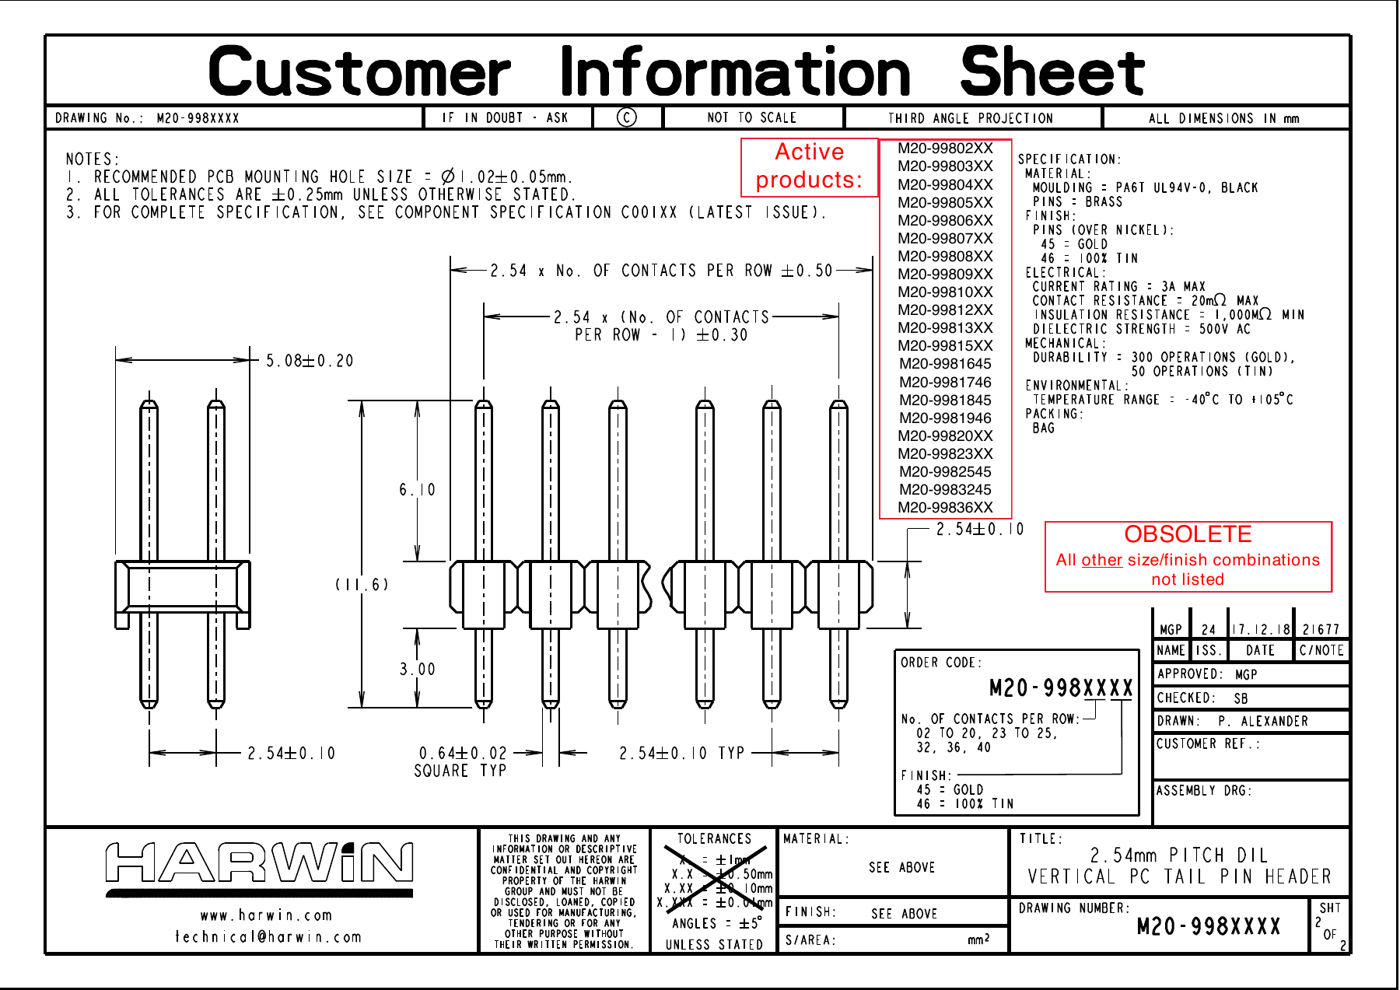
hardware/system-review/electrical/host-harness-review/harwin-drawing.png
