magnus188/trimix-analysator/hardware/system-review/electrical/host-harness-review/samtec-tsw-footprint.png

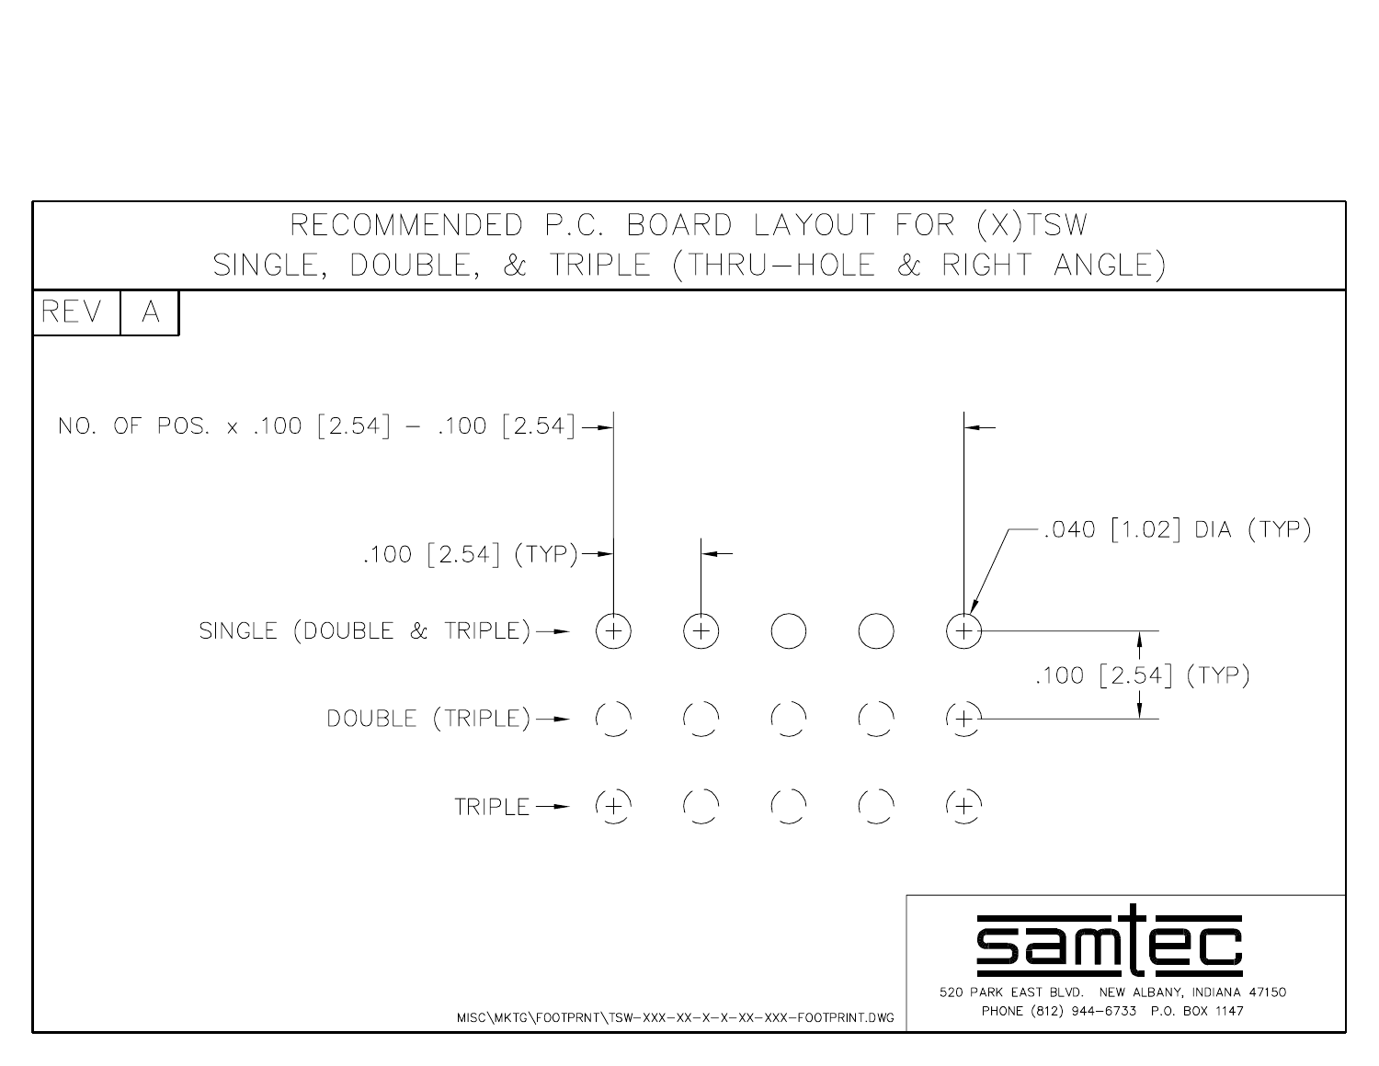
hardware/system-review/electrical/host-harness-review/samtec-tsw-footprint.png
