magnus188/trimix-analysator/hardware/system-review/electrical/host-harness-review/samtec-tsw-page6.png

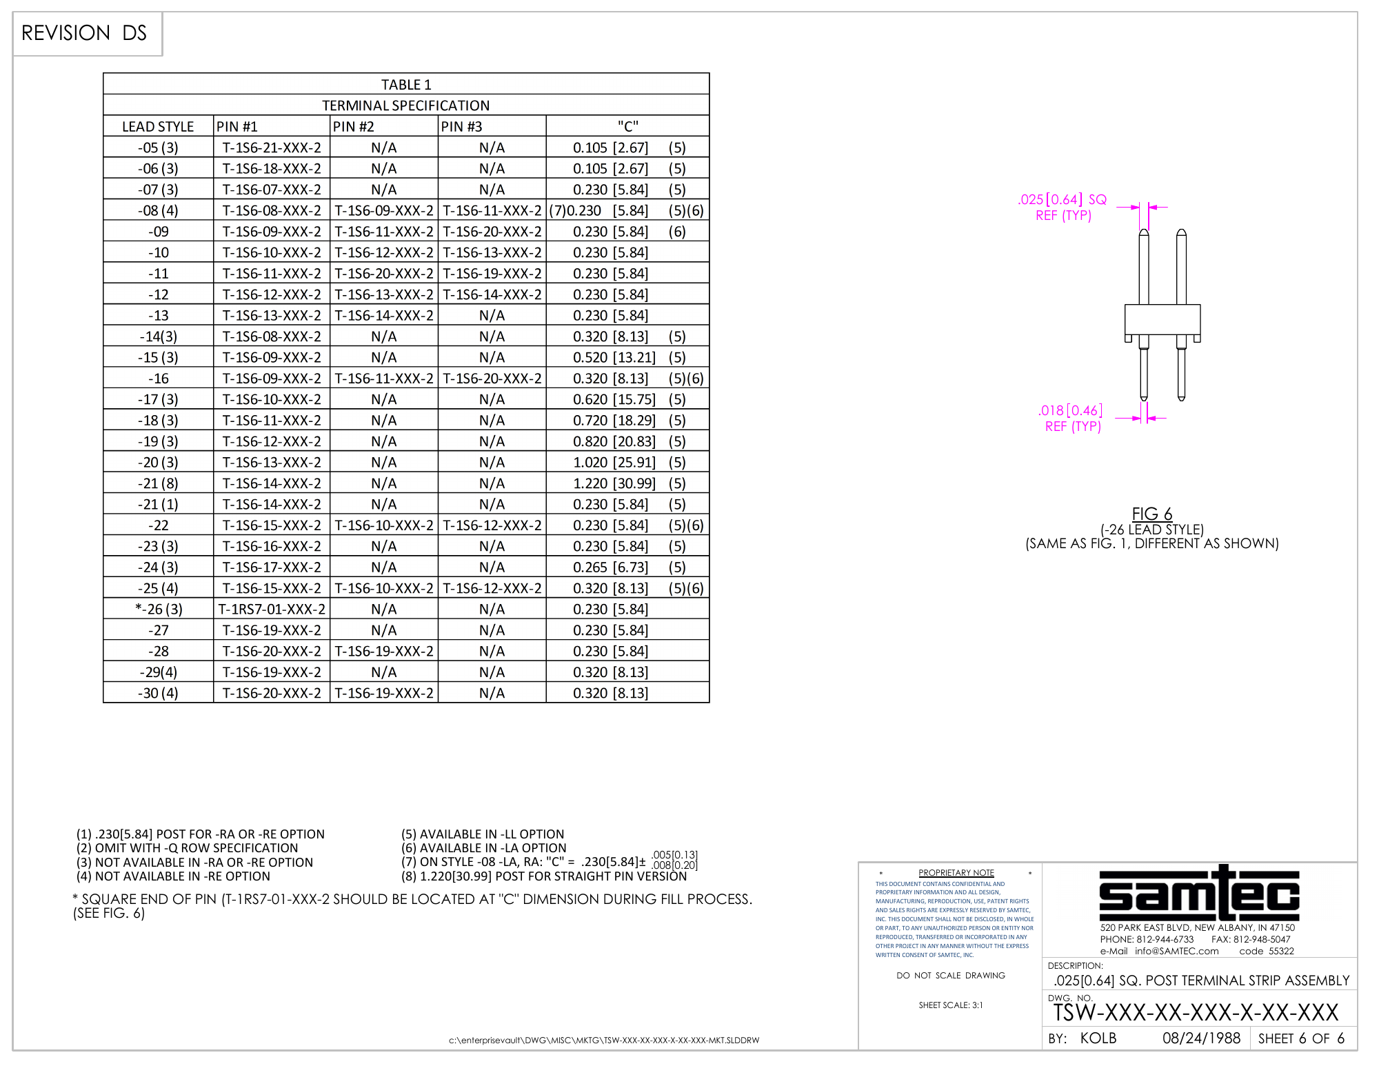
hardware/system-review/electrical/host-harness-review/samtec-tsw-page6.png
