magnus188/trimix-analysator/hardware/system-review/electrical/main-back-copper-review-power.png

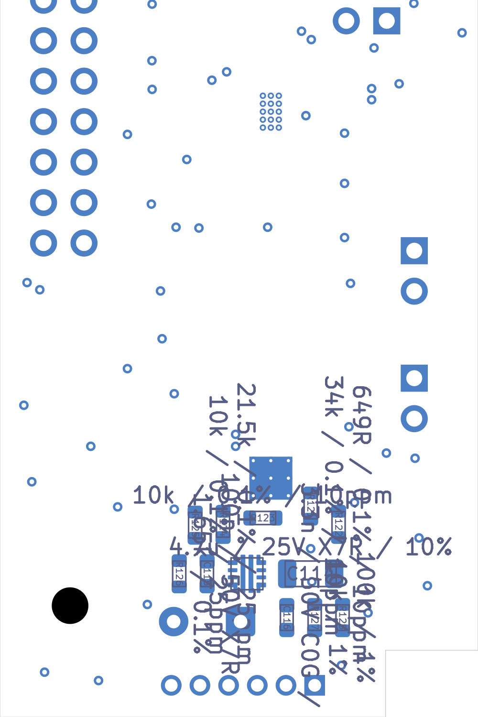
hardware/system-review/electrical/main-back-copper-review-power.png
