magnus188/trimix-analysator/hardware/system-review/electrical/main-final-independent/diagnostic/review/B-Cu.png

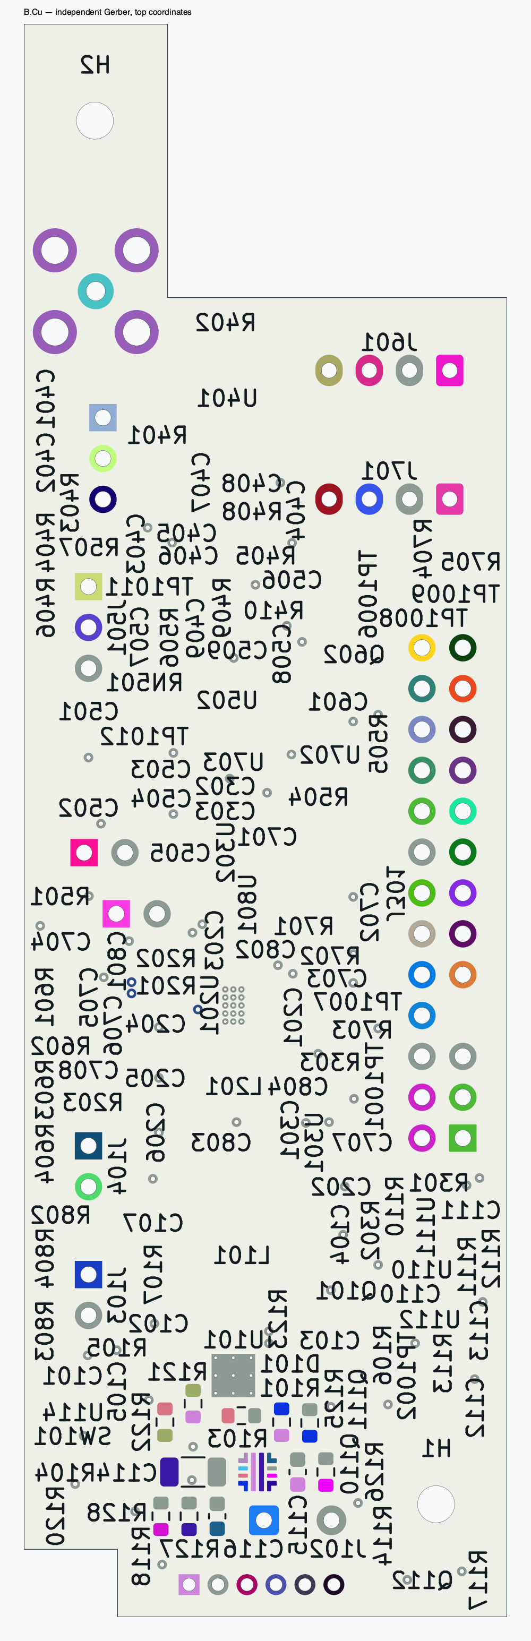
hardware/system-review/electrical/main-final-independent/diagnostic/review/B-Cu.png
