magnus188/trimix-analysator/hardware/system-review/electrical/main-final-independent/final-9f274fdf/U115-copper-paste.png

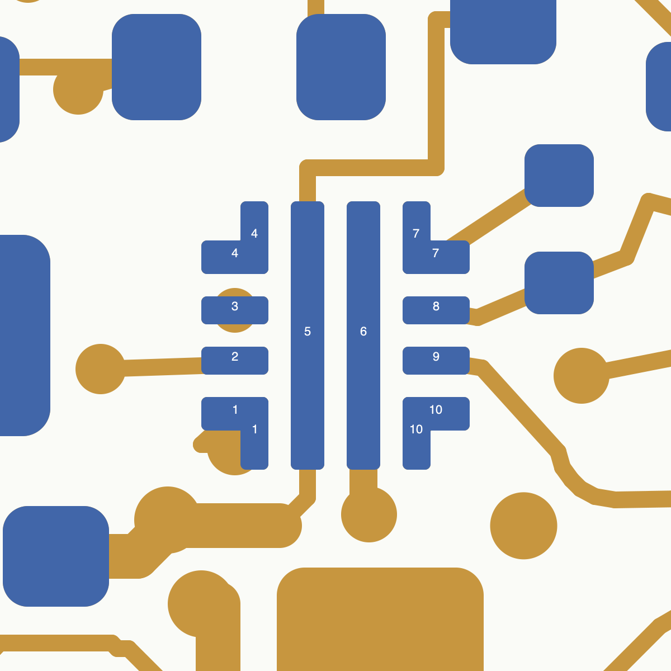
hardware/system-review/electrical/main-final-independent/final-9f274fdf/U115-copper-paste.png
