magnus188/trimix-analysator/hardware/system-review/electrical/main-final-independent/final-0962ad86/Factory-F-Paste.png

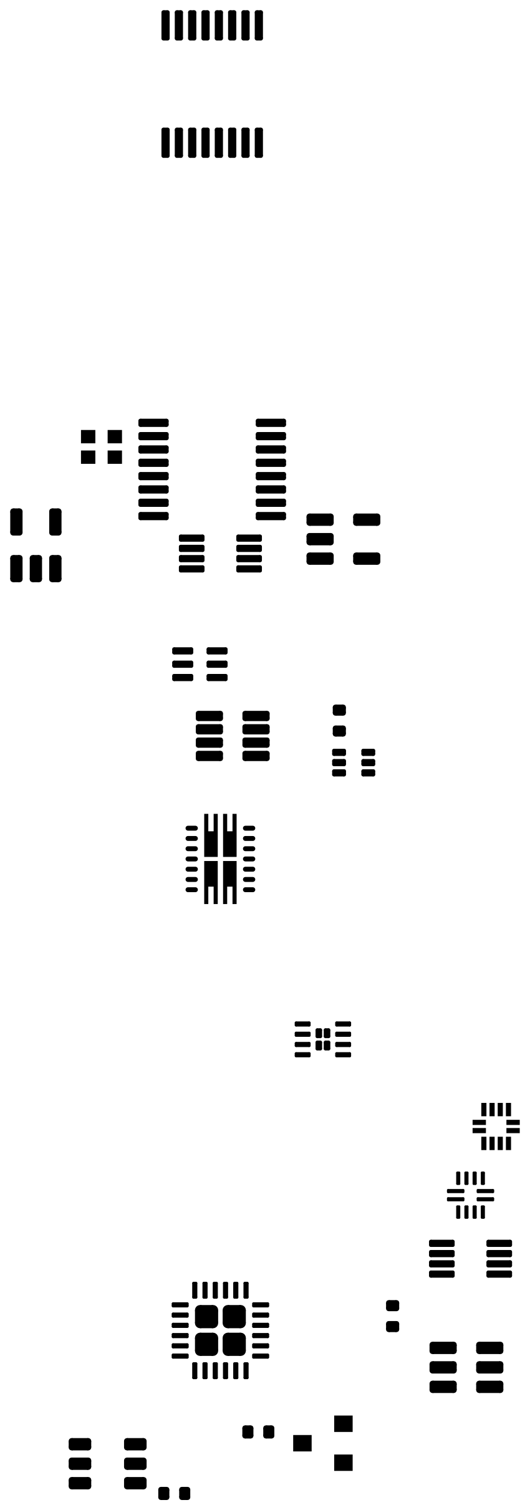
hardware/system-review/electrical/main-final-independent/final-0962ad86/Factory-F-Paste.png
