magnus188/trimix-analysator/hardware/system-review/electrical/main-final-independent/final-0962ad86/In2-Cu.png

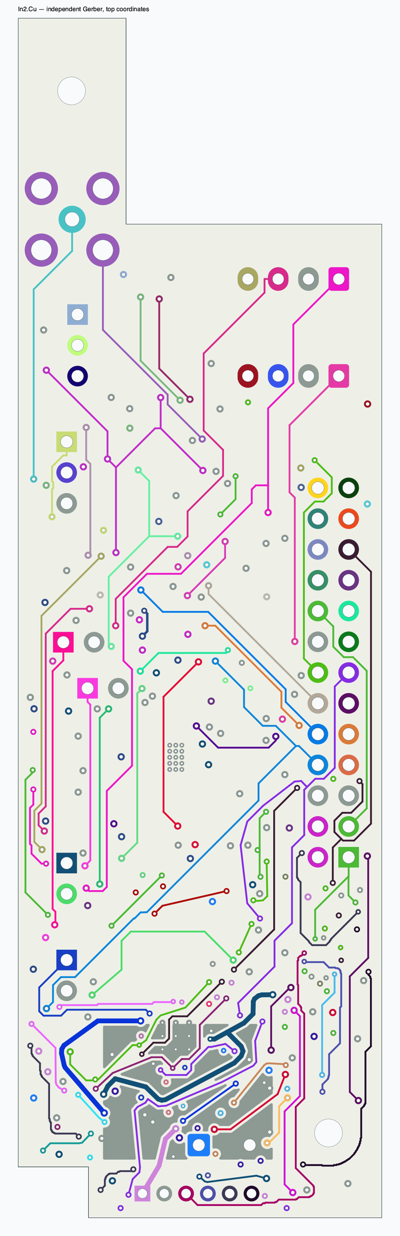
hardware/system-review/electrical/main-final-independent/final-0962ad86/In2-Cu.png
