magnus188/trimix-analysator/hardware/system-review/electrical/main-front-copper-review.png

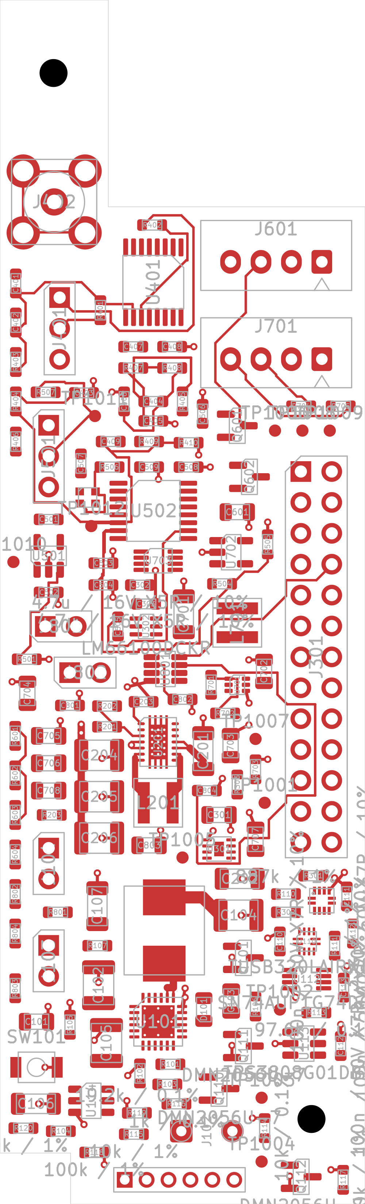
hardware/system-review/electrical/main-front-copper-review.png
