magnus188/trimix-analysator/hardware/system-review/electrical/routing-candidate/bq-stat-slot-proposal.png

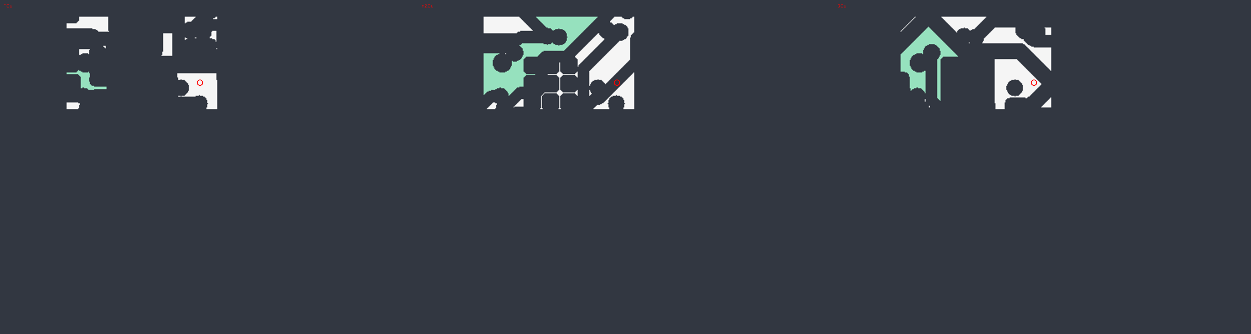
hardware/system-review/electrical/routing-candidate/bq-stat-slot-proposal.png
