magnus188/trimix-analysator/hardware/system-review/electrical/routing-candidate/bypass-route-proposal/power-final.png

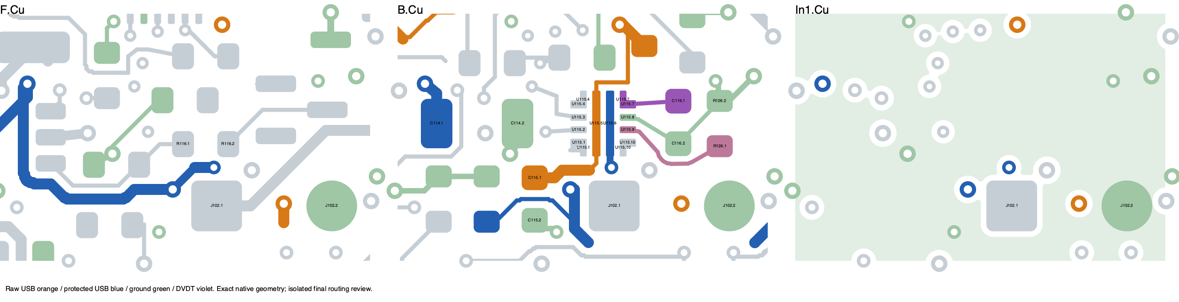
hardware/system-review/electrical/routing-candidate/bypass-route-proposal/power-final.png
