magnus188/trimix-analysator/hardware/system-review/electrical/routing-candidate/bypass-route-proposal/power-stage.png

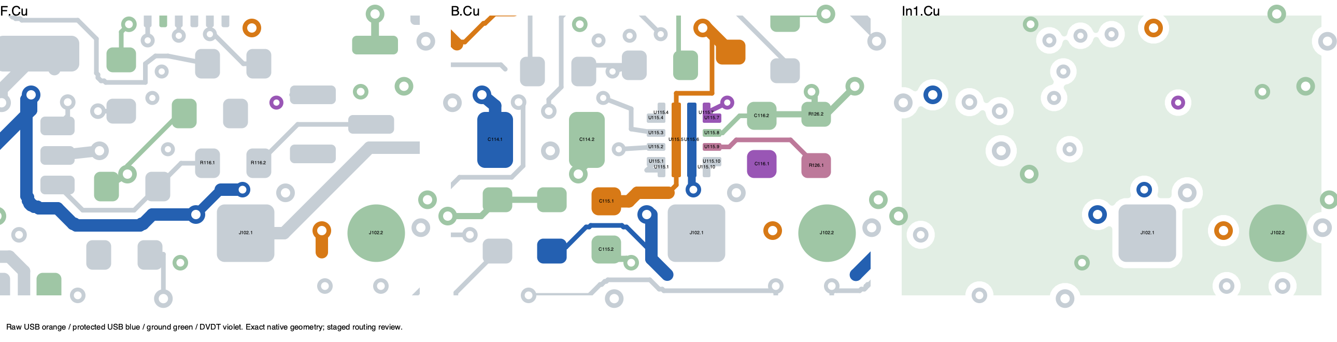
hardware/system-review/electrical/routing-candidate/bypass-route-proposal/power-stage.png
