magnus188/trimix-analysator/hardware/system-review/electrical/routing-candidate/c105-sys-route-proposal/synchronized-r101/ground-review/via-1-ligaments.png

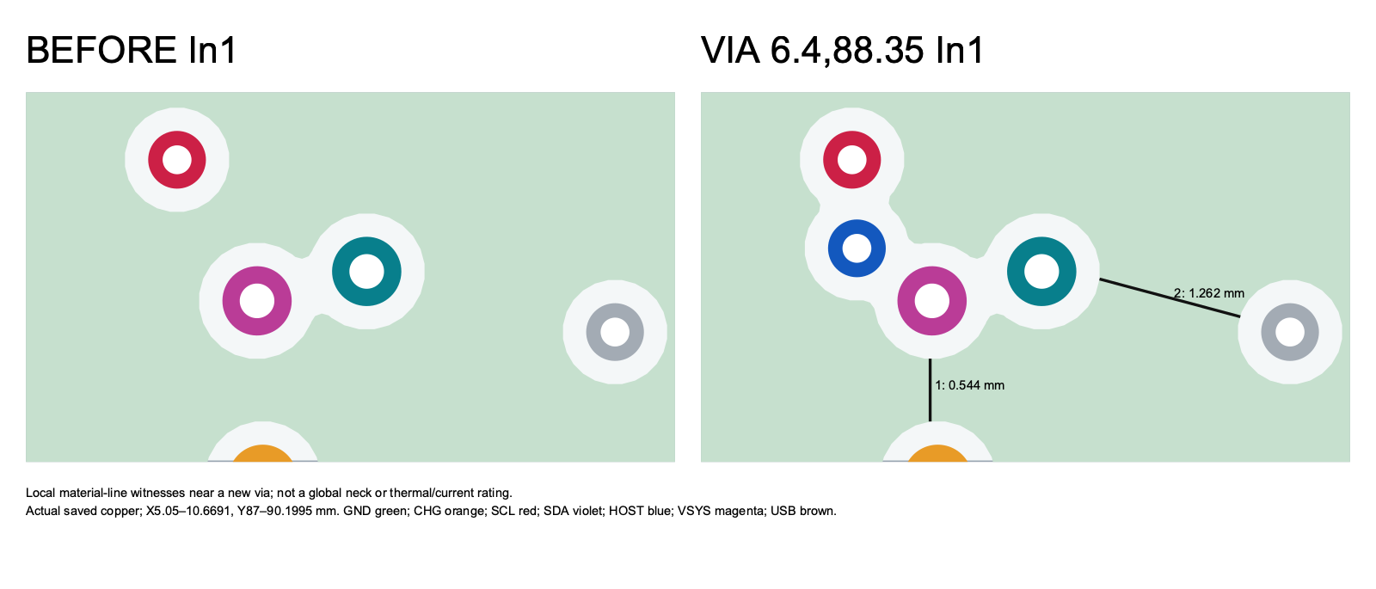
hardware/system-review/electrical/routing-candidate/c105-sys-route-proposal/synchronized-r101/ground-review/via-1-ligaments.png
