magnus188/trimix-analysator/hardware/system-review/electrical/routing-candidate/c105-upper-feed.png

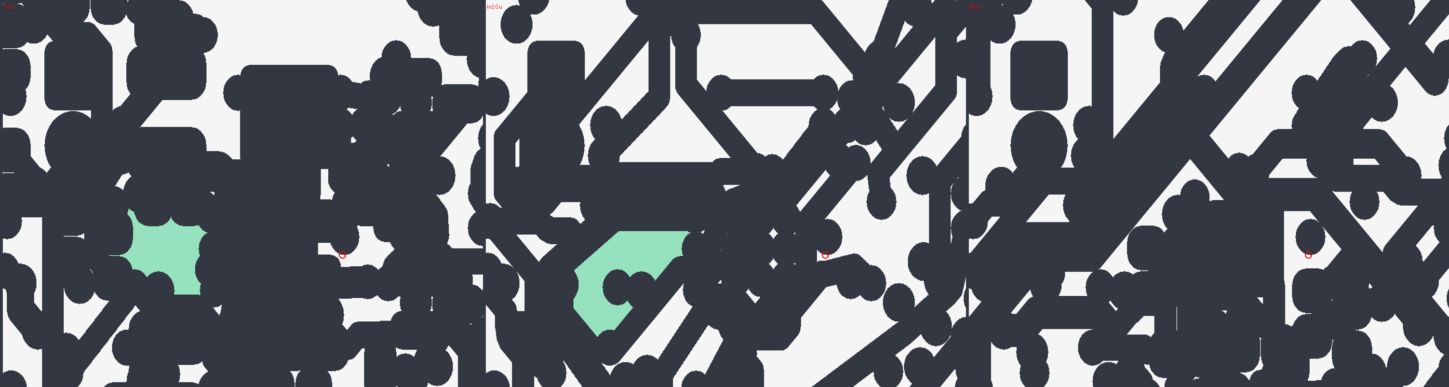
hardware/system-review/electrical/routing-candidate/c105-upper-feed.png
