magnus188/trimix-analysator/hardware/system-review/electrical/routing-candidate/c116-cc-source-route.png

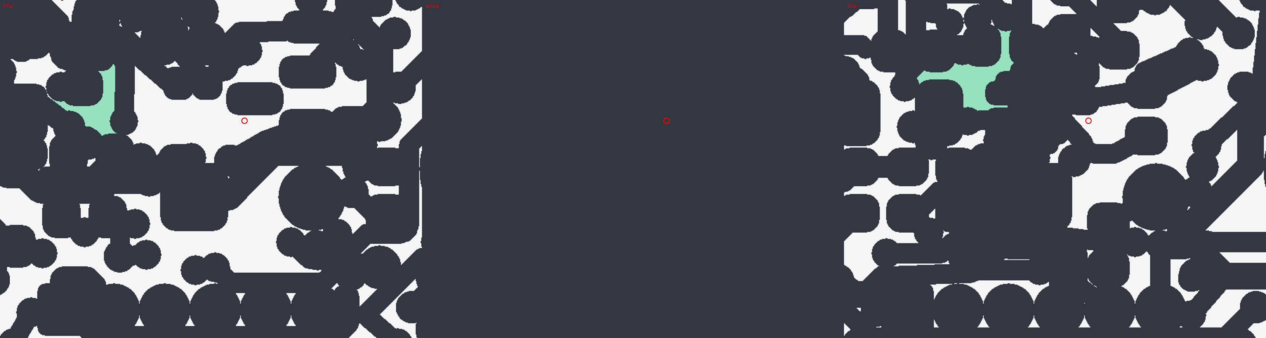
hardware/system-review/electrical/routing-candidate/c116-cc-source-route.png
