magnus188/trimix-analysator/hardware/system-review/electrical/routing-candidate/cap-signal-reconnect/pullup-swap/independent-ground/all-board-power-overlays.png

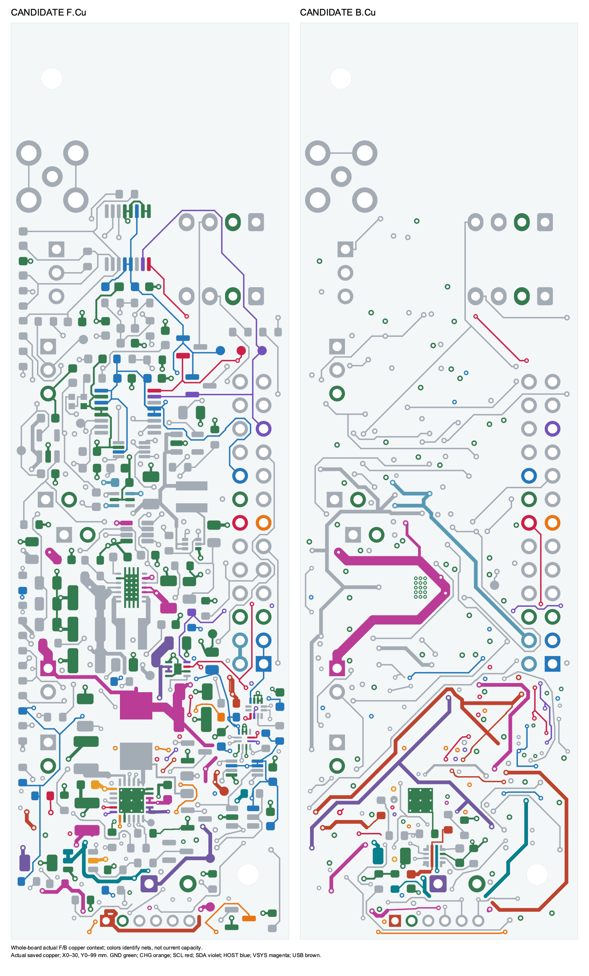
hardware/system-review/electrical/routing-candidate/cap-signal-reconnect/pullup-swap/independent-ground/all-board-power-overlays.png
