magnus188/trimix-analysator/hardware/system-review/electrical/routing-candidate/cap-signal-reconnect/pullup-swap/independent-ground/local-plane-comparison.png

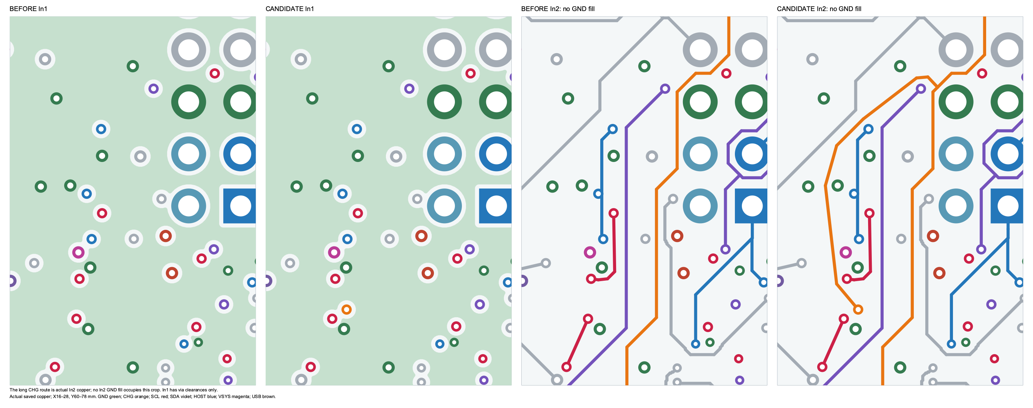
hardware/system-review/electrical/routing-candidate/cap-signal-reconnect/pullup-swap/independent-ground/local-plane-comparison.png
