magnus188/trimix-analysator/hardware/system-review/electrical/routing-candidate/cc-dense-via-scout.png

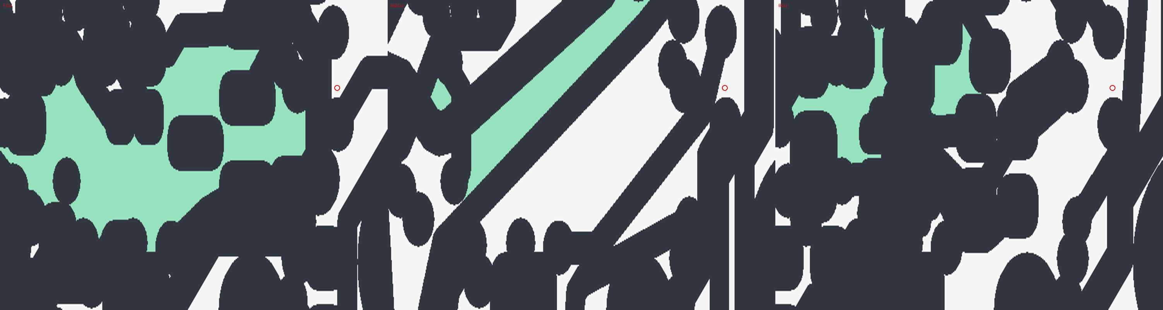
hardware/system-review/electrical/routing-candidate/cc-dense-via-scout.png
