magnus188/trimix-analysator/hardware/system-review/electrical/routing-candidate/ce-gateway-outer.png

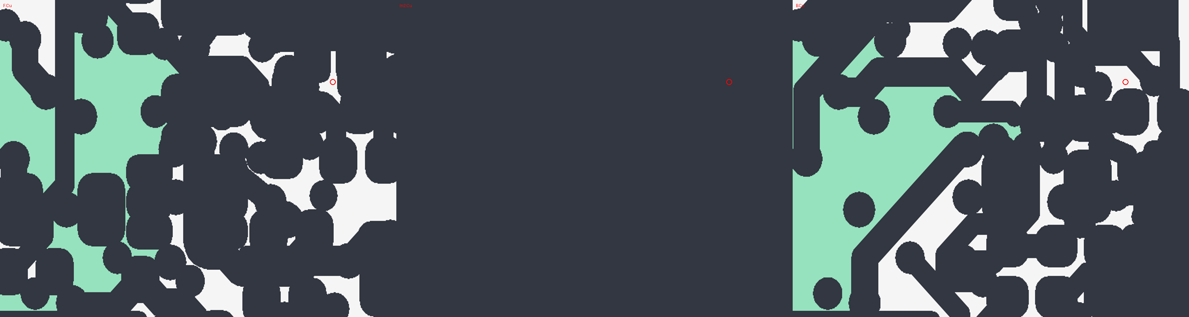
hardware/system-review/electrical/routing-candidate/ce-gateway-outer.png
