magnus188/trimix-analysator/hardware/system-review/electrical/routing-candidate/charger-cap-trunk.png

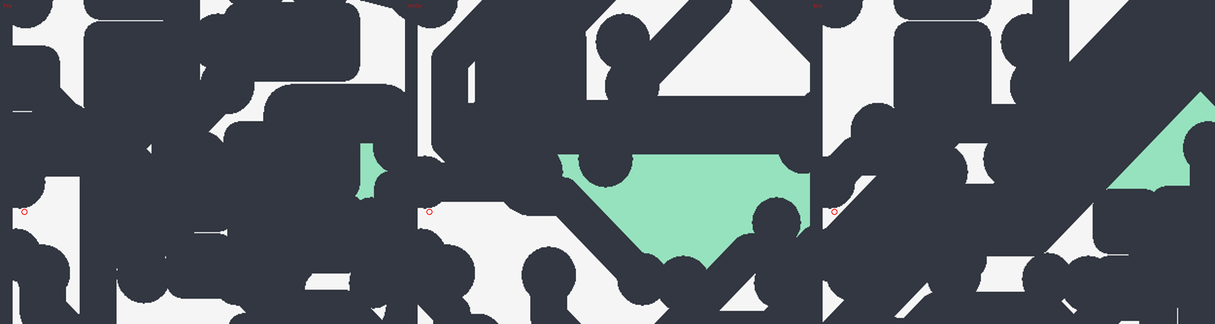
hardware/system-review/electrical/routing-candidate/charger-cap-trunk.png
