magnus188/trimix-analysator/hardware/system-review/electrical/routing-candidate/charger-output-cap-path.png

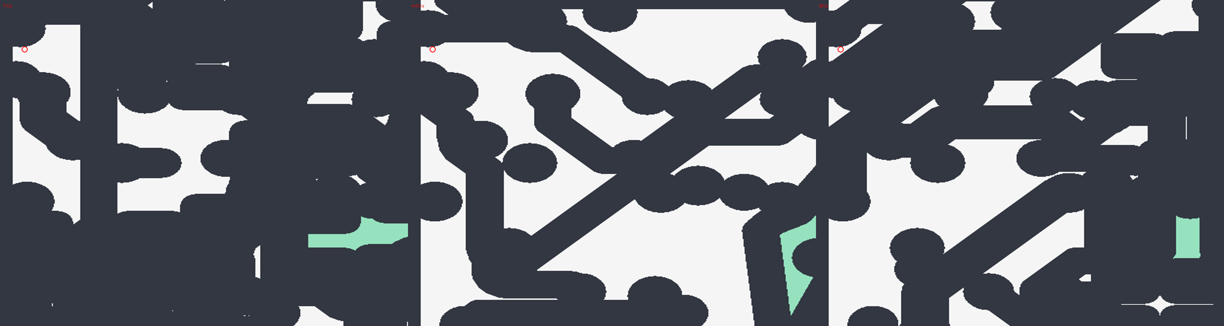
hardware/system-review/electrical/routing-candidate/charger-output-cap-path.png
