magnus188/trimix-analysator/hardware/system-review/electrical/routing-candidate/dm-ground-strip-proposal.png

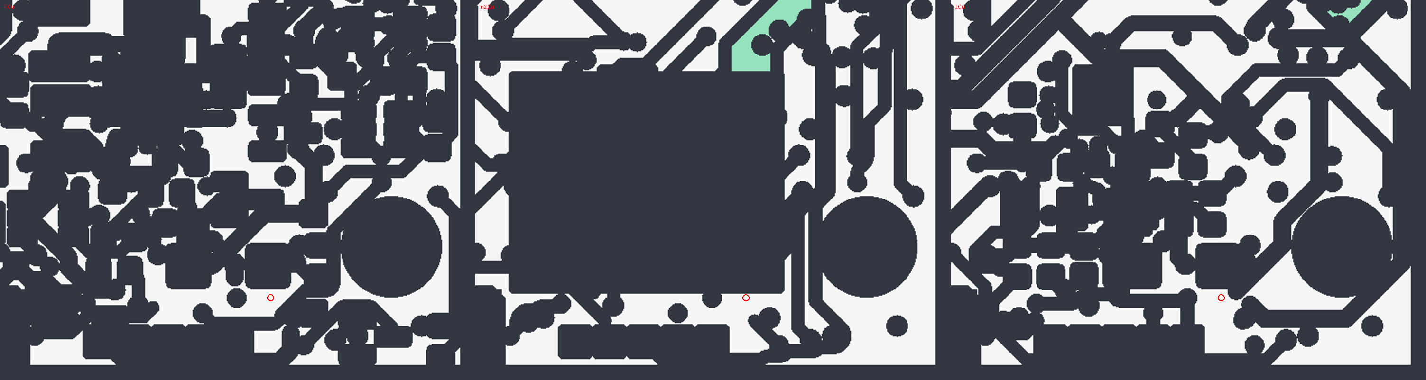
hardware/system-review/electrical/routing-candidate/dm-ground-strip-proposal.png
