magnus188/trimix-analysator/hardware/system-review/electrical/routing-candidate/final-cleanup/prune2a/c708-ground-comparison.png

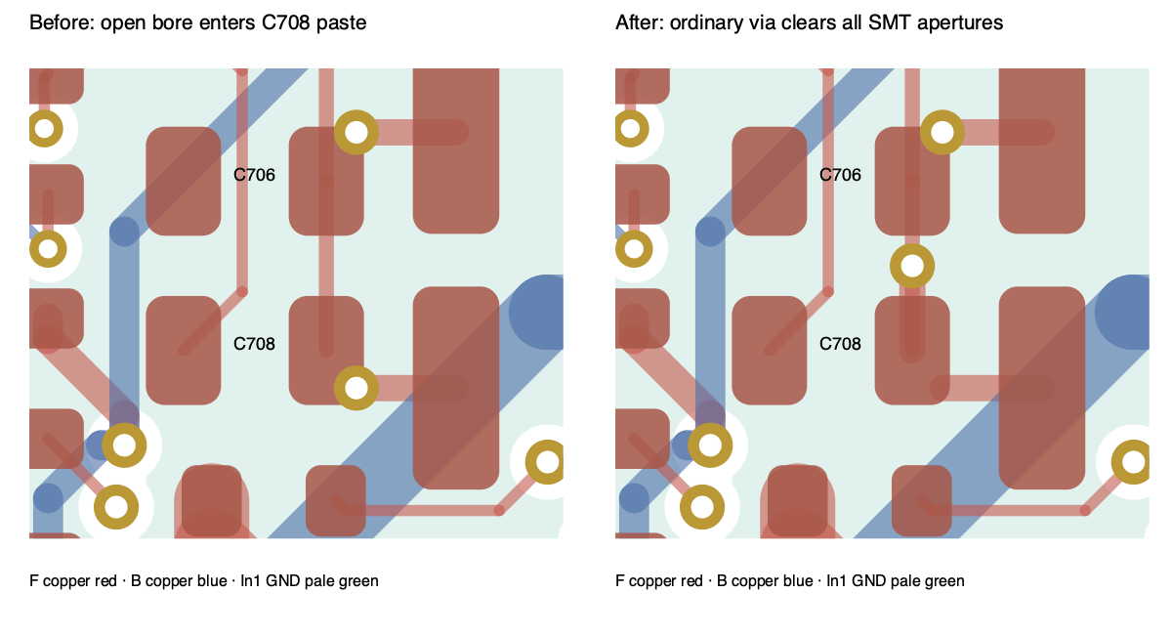
hardware/system-review/electrical/routing-candidate/final-cleanup/prune2a/c708-ground-comparison.png
