magnus188/trimix-analysator/hardware/system-review/electrical/routing-candidate/hypothetical-cc-series-only.png

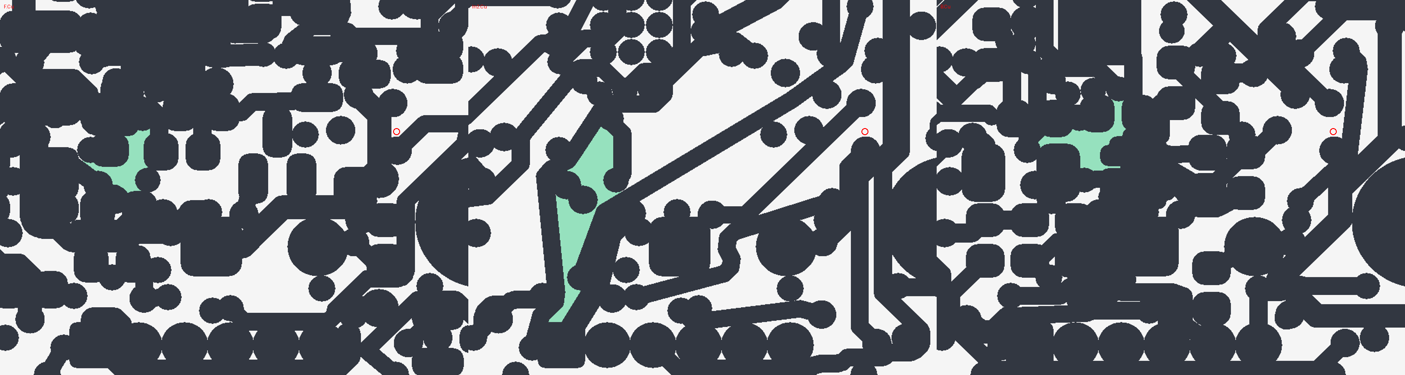
hardware/system-review/electrical/routing-candidate/hypothetical-cc-series-only.png
