magnus188/trimix-analysator/hardware/system-review/electrical/routing-candidate/hypothetical-regn-cc-bridge.png

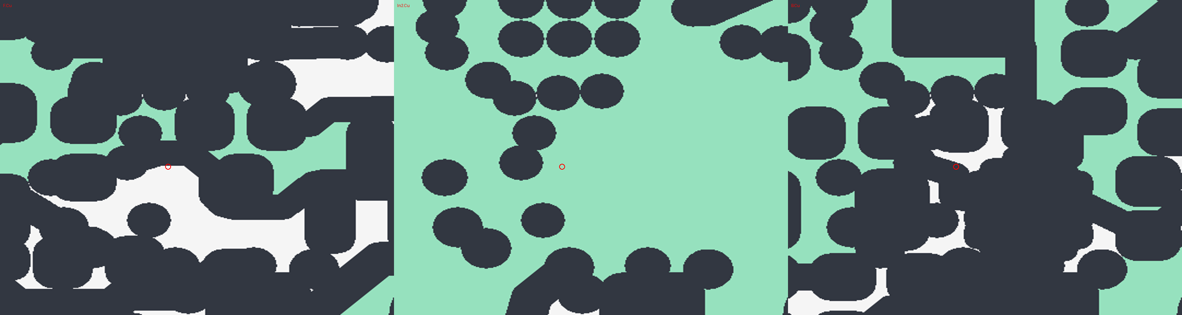
hardware/system-review/electrical/routing-candidate/hypothetical-regn-cc-bridge.png
