magnus188/trimix-analysator/hardware/system-review/electrical/routing-candidate/independent-bq/B-pocket.png

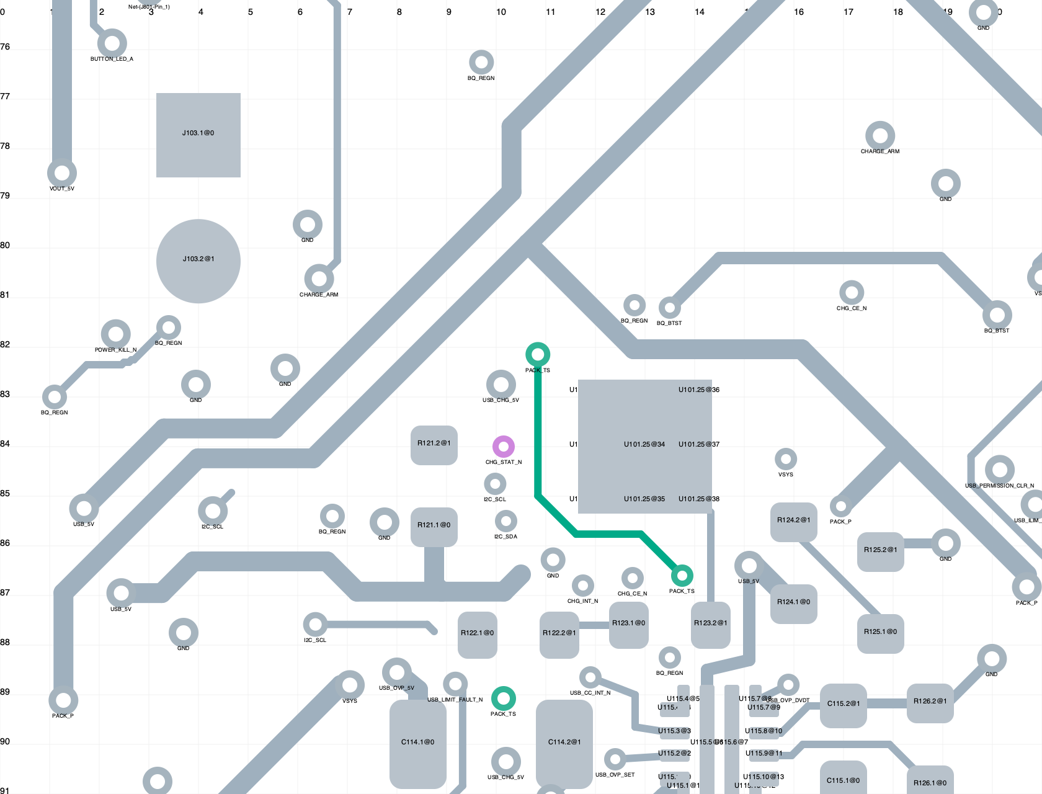
hardware/system-review/electrical/routing-candidate/independent-bq/B-pocket.png
