magnus188/trimix-analysator/hardware/system-review/electrical/routing-candidate/independent-bq/local.png

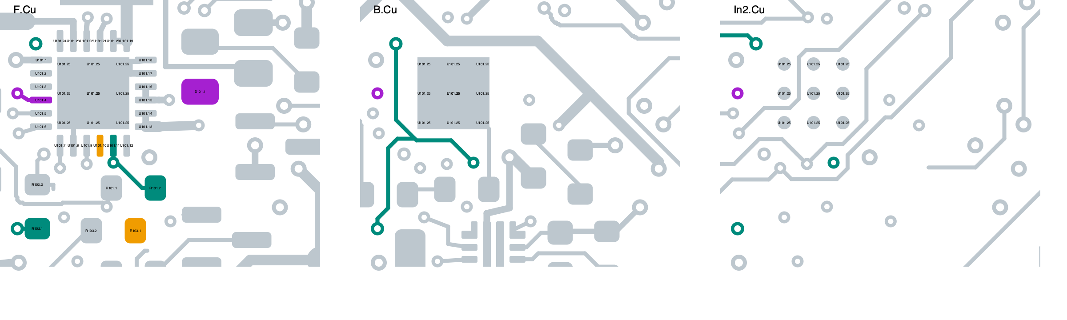
hardware/system-review/electrical/routing-candidate/independent-bq/local.png
