magnus188/trimix-analysator/hardware/system-review/electrical/routing-candidate/independent-dvdt/dvdt-copper.png

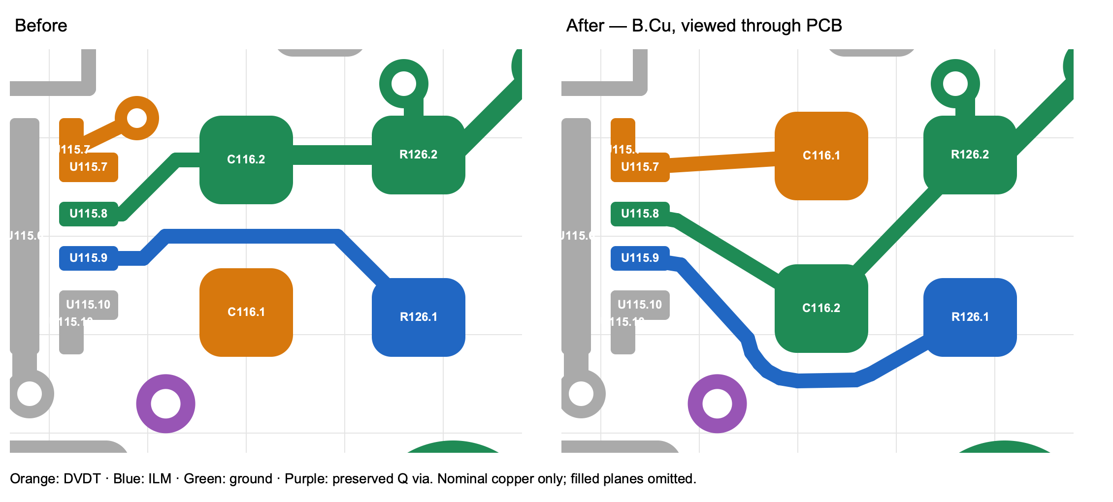
hardware/system-review/electrical/routing-candidate/independent-dvdt/dvdt-copper.png
