magnus188/trimix-analysator/hardware/system-review/electrical/routing-candidate/independent-upper-power/upper-copper.png

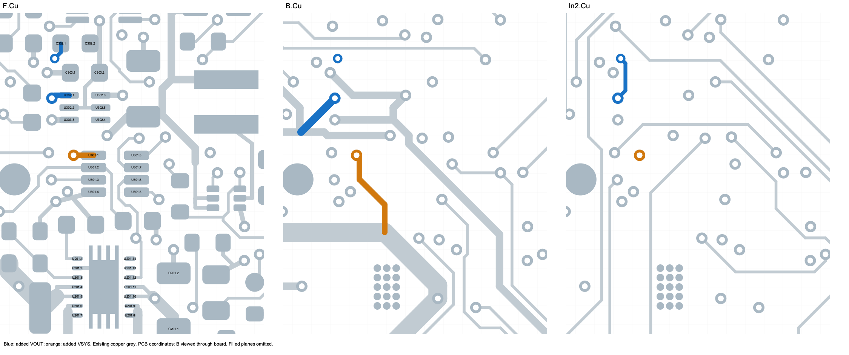
hardware/system-review/electrical/routing-candidate/independent-upper-power/upper-copper.png
