magnus188/trimix-analysator/hardware/system-review/electrical/routing-candidate/local-set-ground-bcopper-review.png

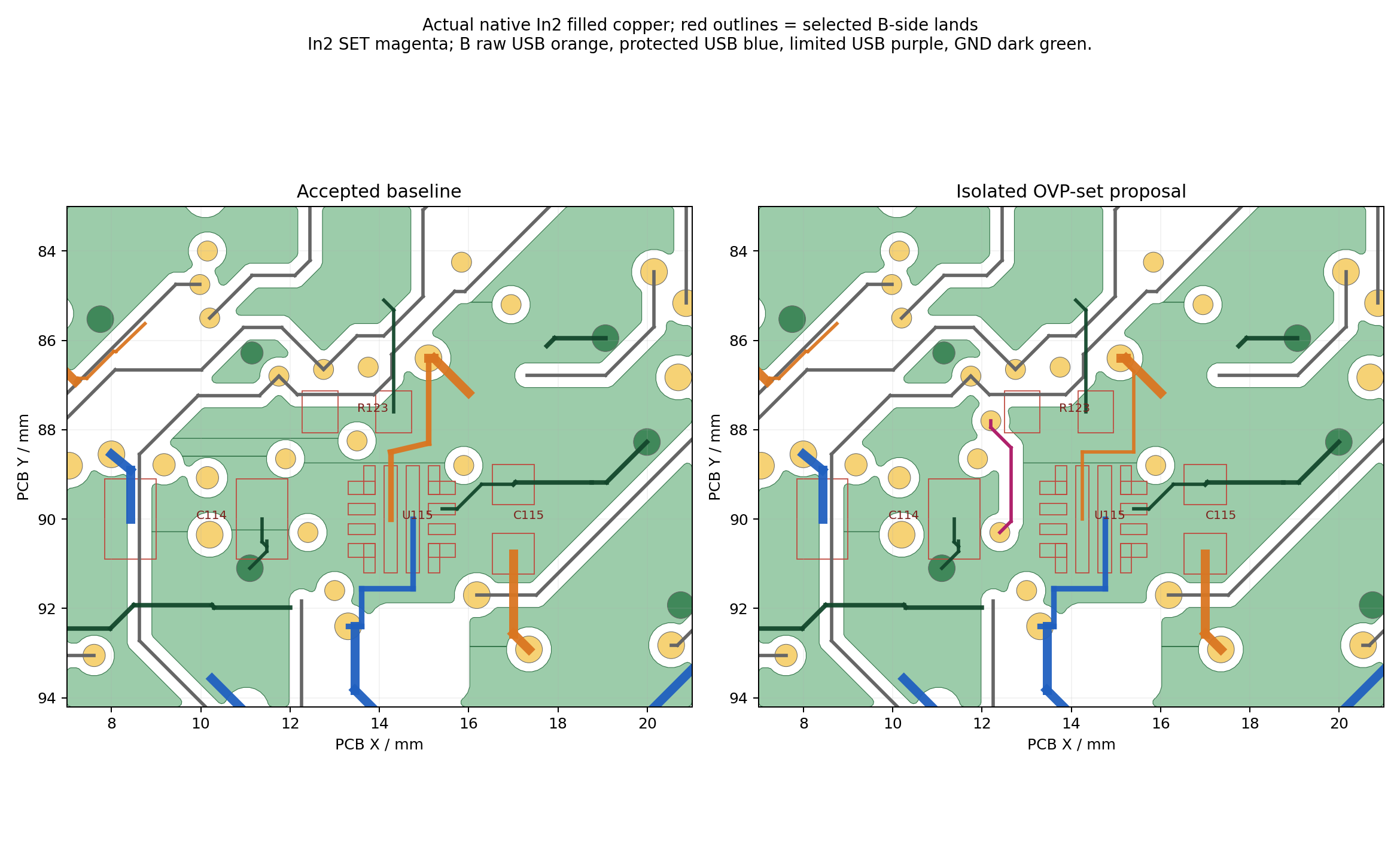
hardware/system-review/electrical/routing-candidate/local-set-ground-bcopper-review.png
