magnus188/trimix-analysator/hardware/system-review/electrical/routing-candidate/lower-chg-route-proposal/ground-comparison.png

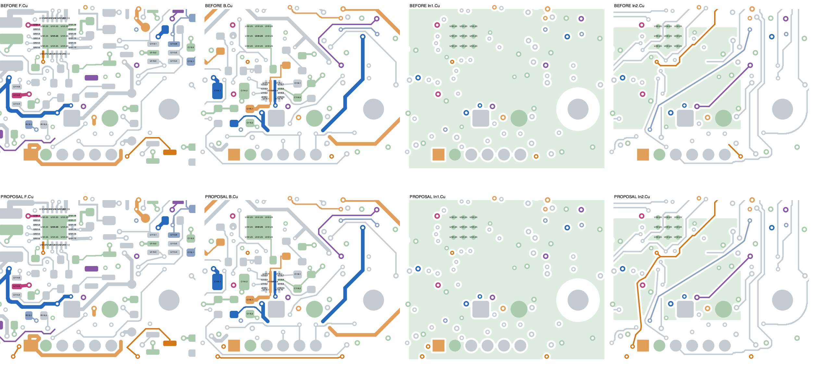
hardware/system-review/electrical/routing-candidate/lower-chg-route-proposal/ground-comparison.png
