magnus188/trimix-analysator/hardware/system-review/electrical/routing-candidate/ovp-sense-upper.png

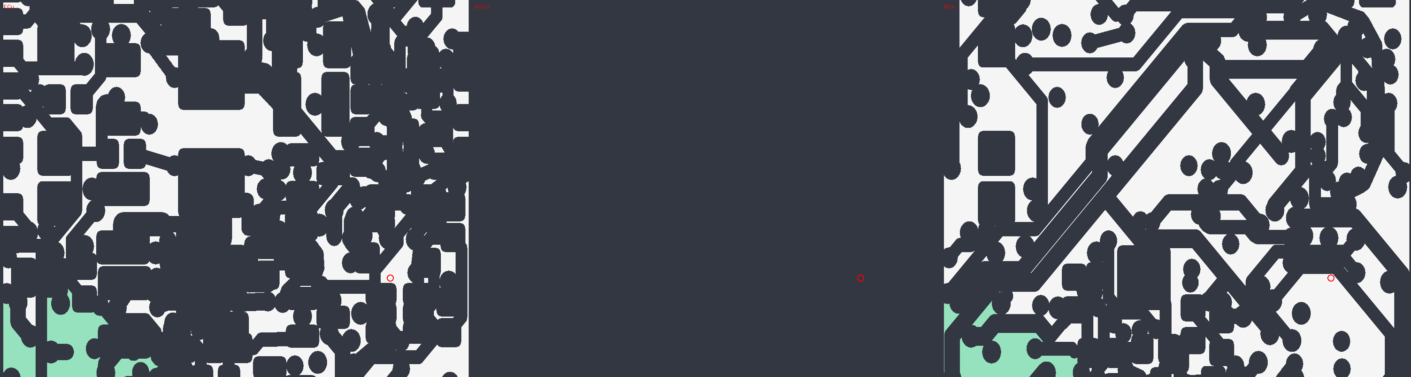
hardware/system-review/electrical/routing-candidate/ovp-sense-upper.png
