magnus188/trimix-analysator/hardware/system-review/electrical/routing-candidate/ovp-set-dense.png

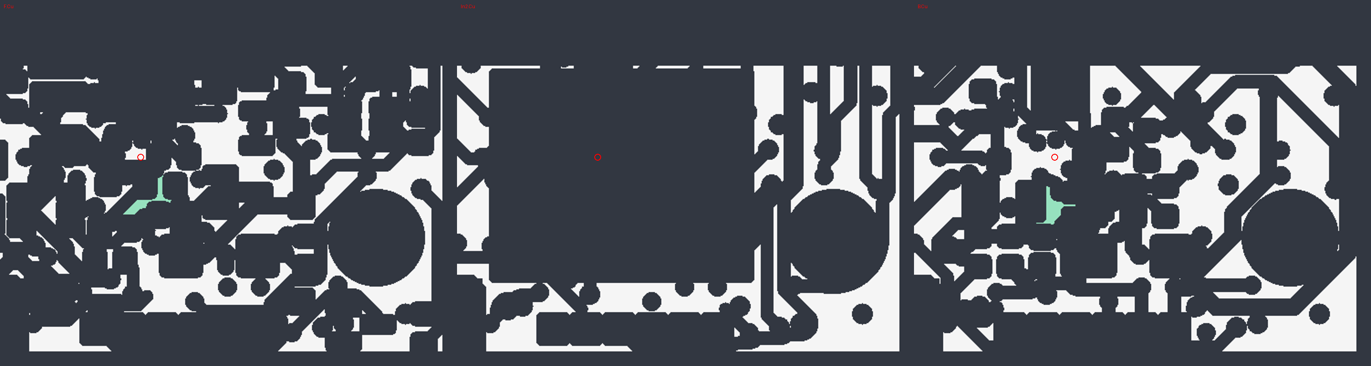
hardware/system-review/electrical/routing-candidate/ovp-set-dense.png
