magnus188/trimix-analysator/hardware/system-review/electrical/routing-candidate/ovp-set-slot.png

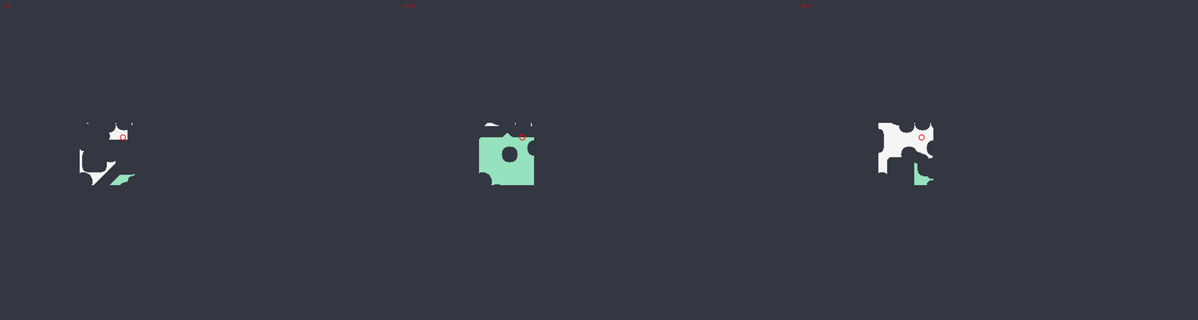
hardware/system-review/electrical/routing-candidate/ovp-set-slot.png
