magnus188/trimix-analysator/hardware/system-review/electrical/routing-candidate/permission-links-proposal/0402-fault-completion/now-In2-Cu.png

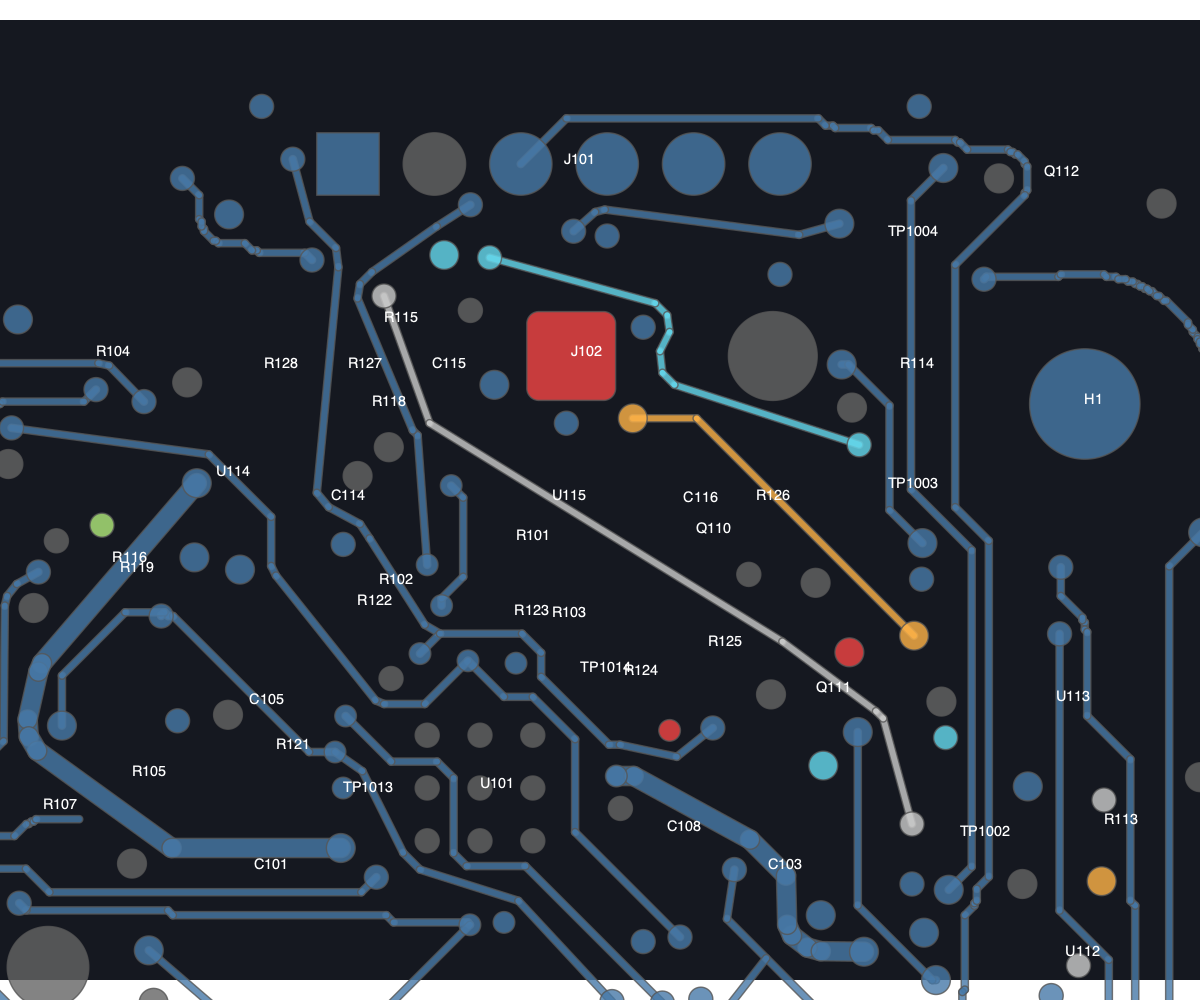
hardware/system-review/electrical/routing-candidate/permission-links-proposal/0402-fault-completion/now-In2-Cu.png
