magnus188/trimix-analysator/hardware/system-review/electrical/routing-candidate/permission-links-proposal/host-shared-bridge/r115-local/In1_Cu_B_Cu.png

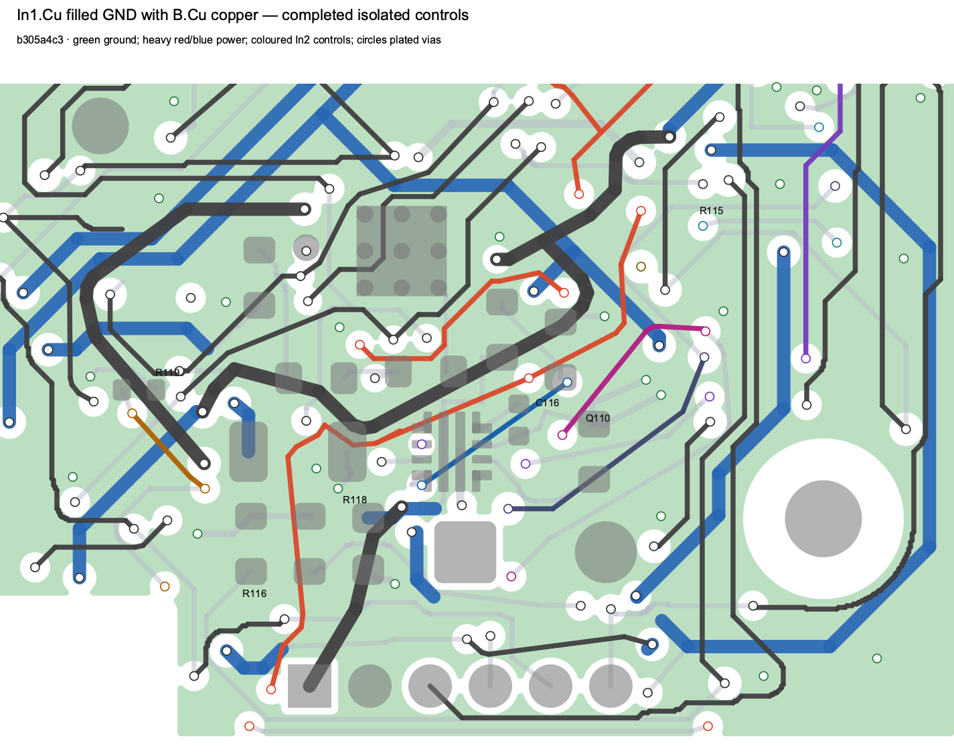
hardware/system-review/electrical/routing-candidate/permission-links-proposal/host-shared-bridge/r115-local/In1_Cu_B_Cu.png
