magnus188/trimix-analysator/hardware/system-review/electrical/routing-candidate/permission-links-proposal/local-pocket.png

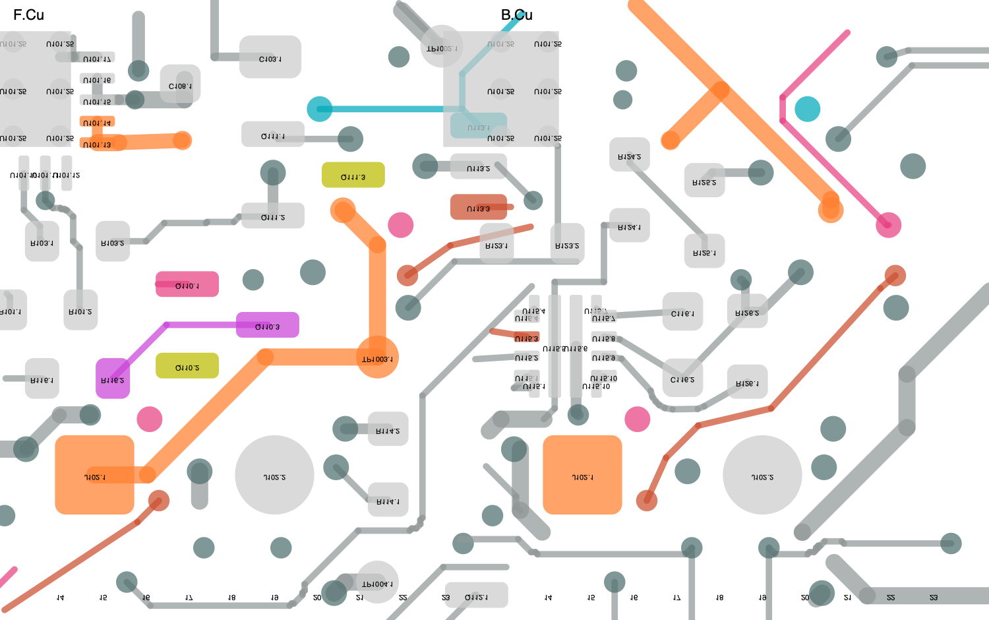
hardware/system-review/electrical/routing-candidate/permission-links-proposal/local-pocket.png
