magnus188/trimix-analysator/hardware/system-review/electrical/routing-candidate/permission-links-proposal/replanned/now-B-Cu.png

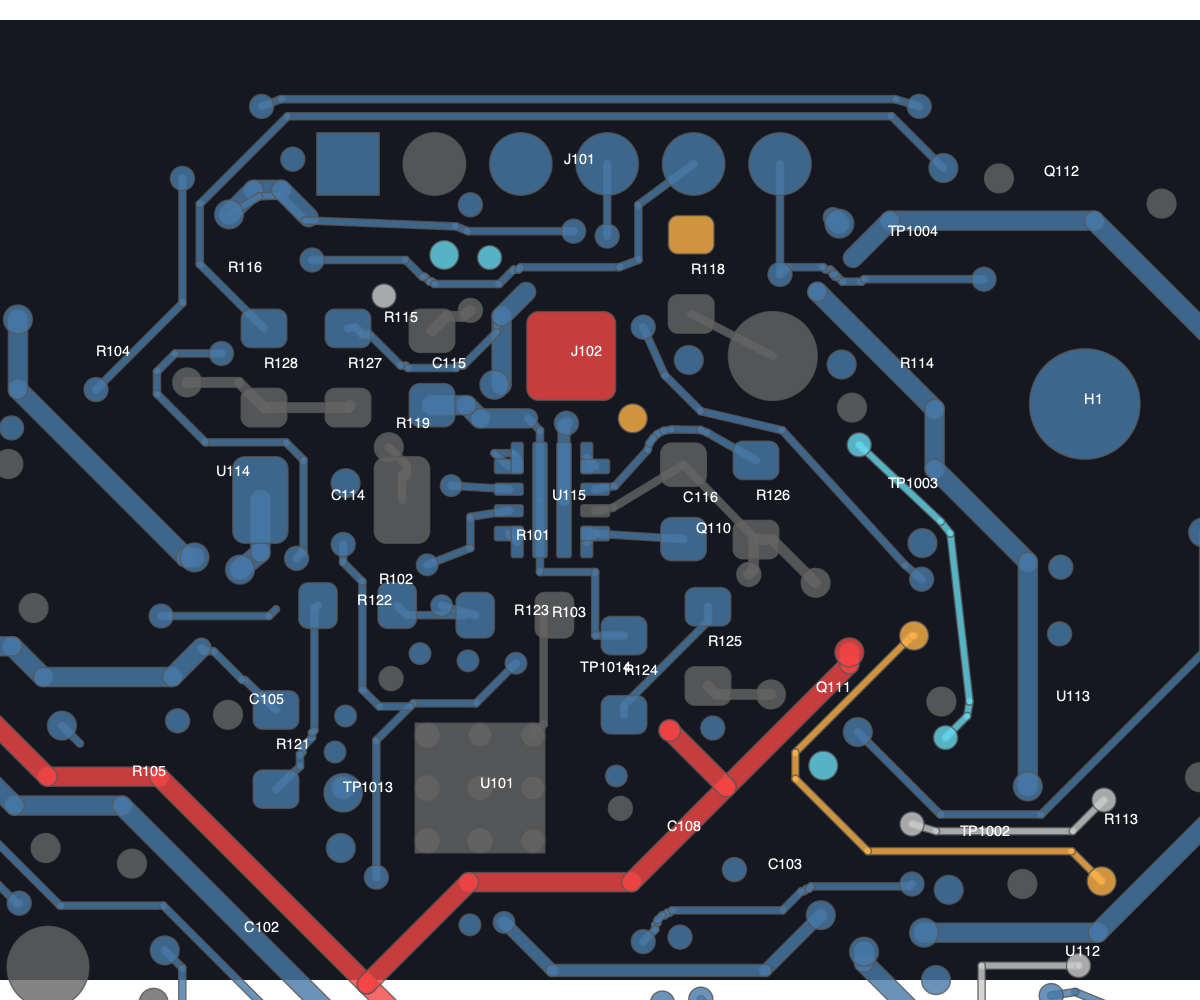
hardware/system-review/electrical/routing-candidate/permission-links-proposal/replanned/now-B-Cu.png
