magnus188/trimix-analysator/hardware/system-review/electrical/routing-candidate/power-local-1.png

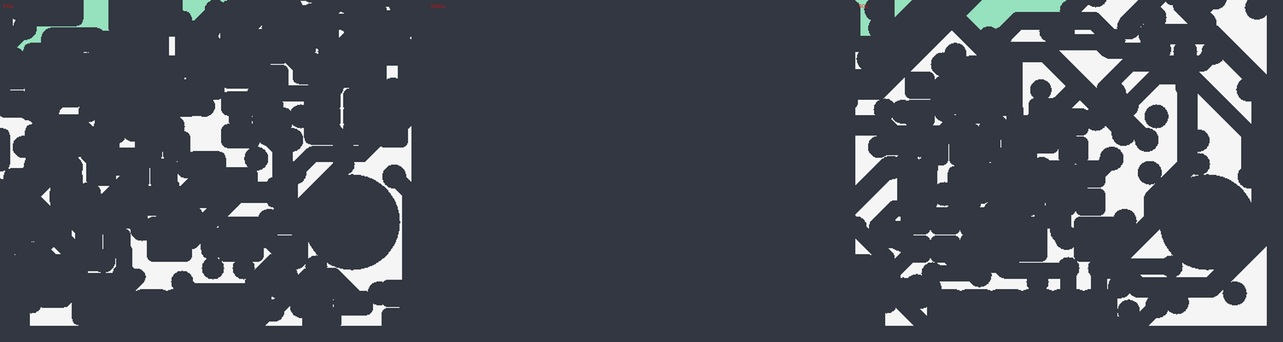
hardware/system-review/electrical/routing-candidate/power-local-1.png
