magnus188/trimix-analysator/hardware/system-review/electrical/routing-candidate/power-lower-review.png

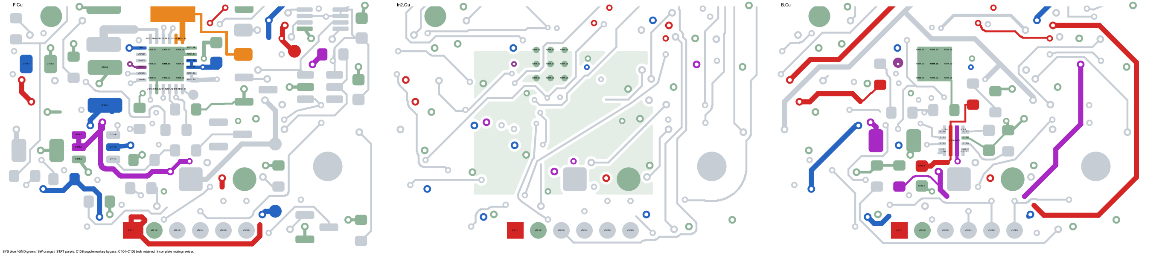
hardware/system-review/electrical/routing-candidate/power-lower-review.png
