magnus188/trimix-analysator/hardware/system-review/electrical/routing-candidate/qon-densevia-trial.png

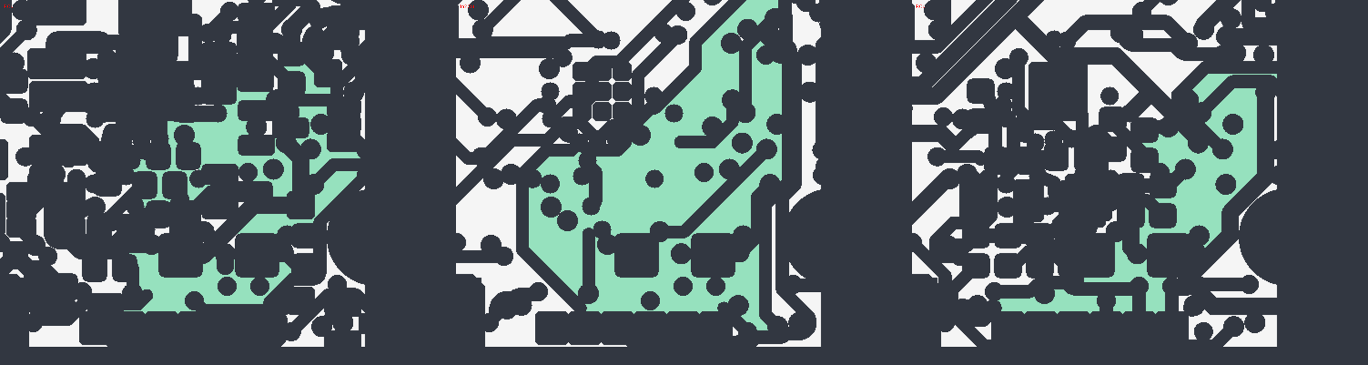
hardware/system-review/electrical/routing-candidate/qon-densevia-trial.png
