magnus188/trimix-analysator/hardware/system-review/electrical/routing-candidate/qon-neck-trial.png

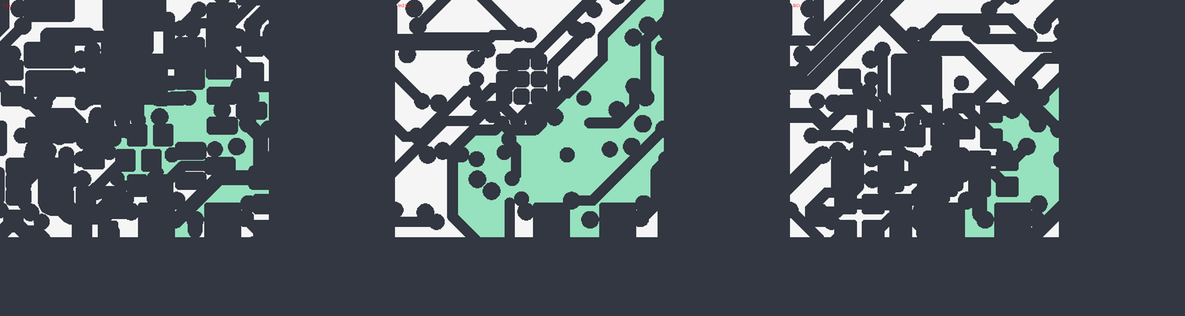
hardware/system-review/electrical/routing-candidate/qon-neck-trial.png
