magnus188/trimix-analysator/hardware/system-review/electrical/routing-candidate/r101-qcore-cc.png

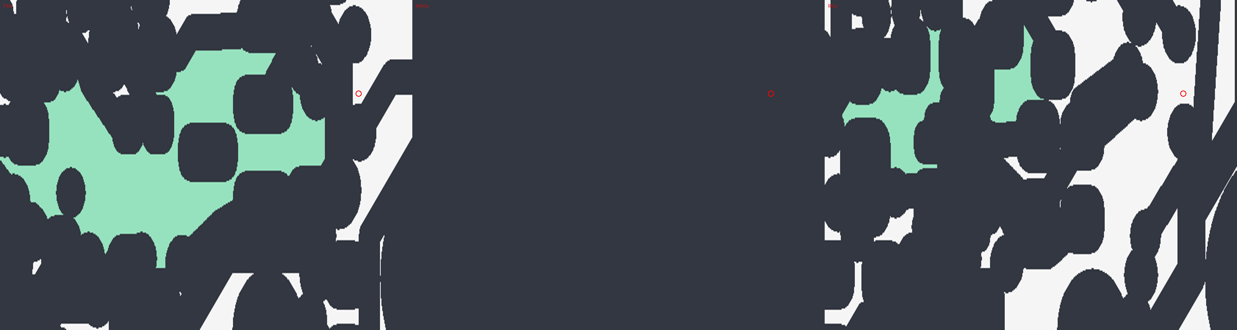
hardware/system-review/electrical/routing-candidate/r101-qcore-cc.png
