magnus188/trimix-analysator/hardware/system-review/electrical/routing-candidate/r101-right-regn.png

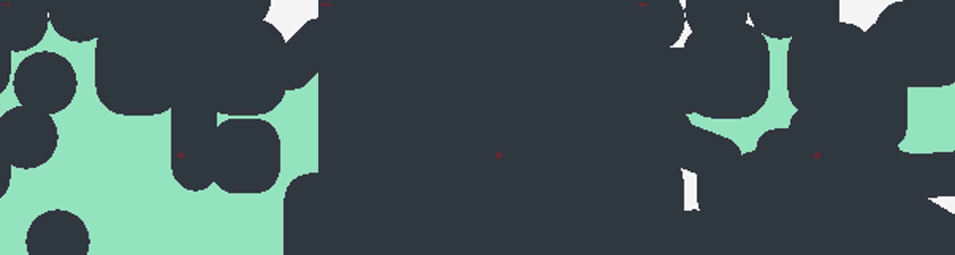
hardware/system-review/electrical/routing-candidate/r101-right-regn.png
