magnus188/trimix-analysator/hardware/system-review/electrical/routing-candidate/raw-cc-bridge.png

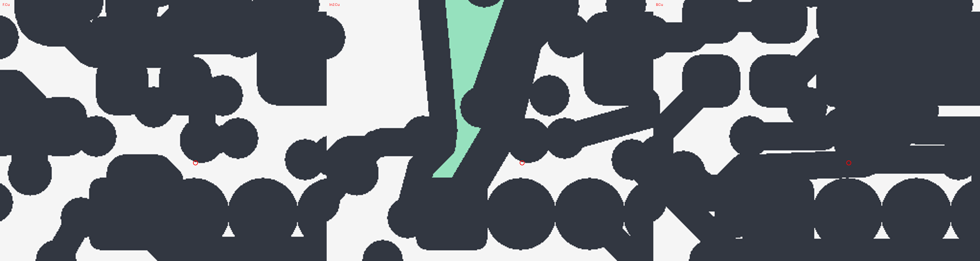
hardware/system-review/electrical/routing-candidate/raw-cc-bridge.png
