magnus188/trimix-analysator/hardware/system-review/electrical/routing-candidate/raw-cc-via-detour.png

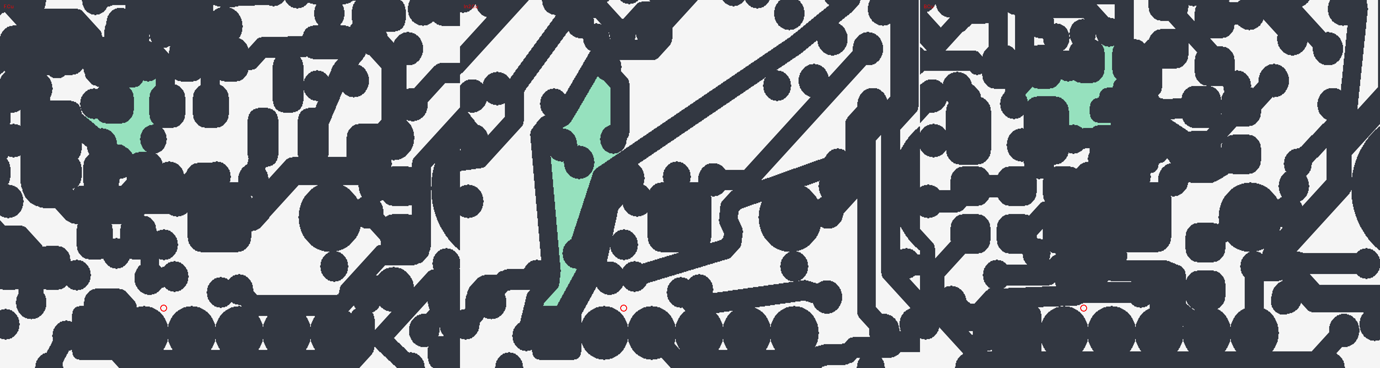
hardware/system-review/electrical/routing-candidate/raw-cc-via-detour.png
