magnus188/trimix-analysator/hardware/system-review/electrical/routing-candidate/raw-current-real-pads.png

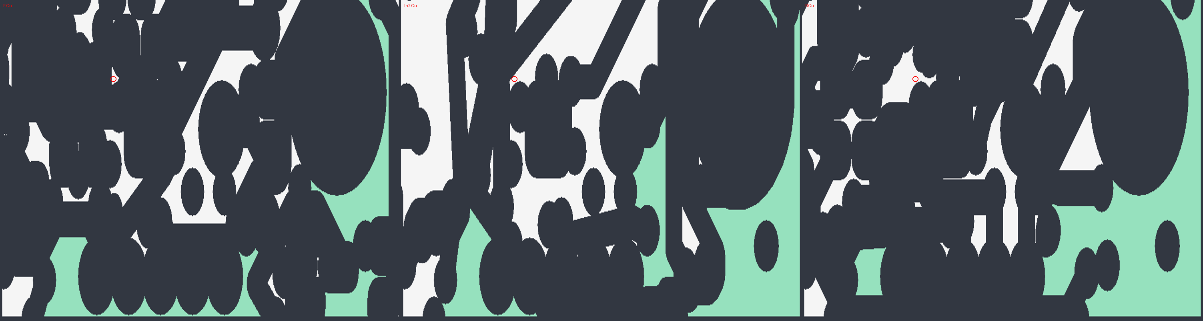
hardware/system-review/electrical/routing-candidate/raw-current-real-pads.png
