magnus188/trimix-analysator/hardware/system-review/electrical/routing-candidate/raw-current-trunk.png

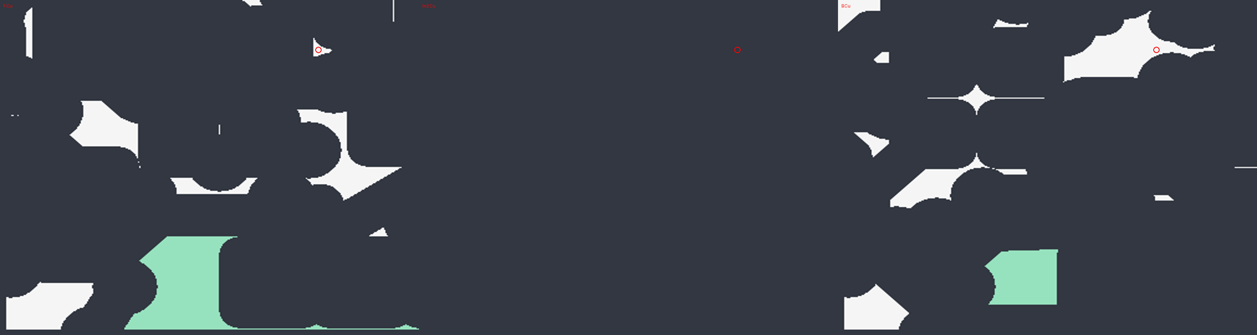
hardware/system-review/electrical/routing-candidate/raw-current-trunk.png
