magnus188/trimix-analysator/hardware/system-review/electrical/routing-candidate/raw-input-local.png

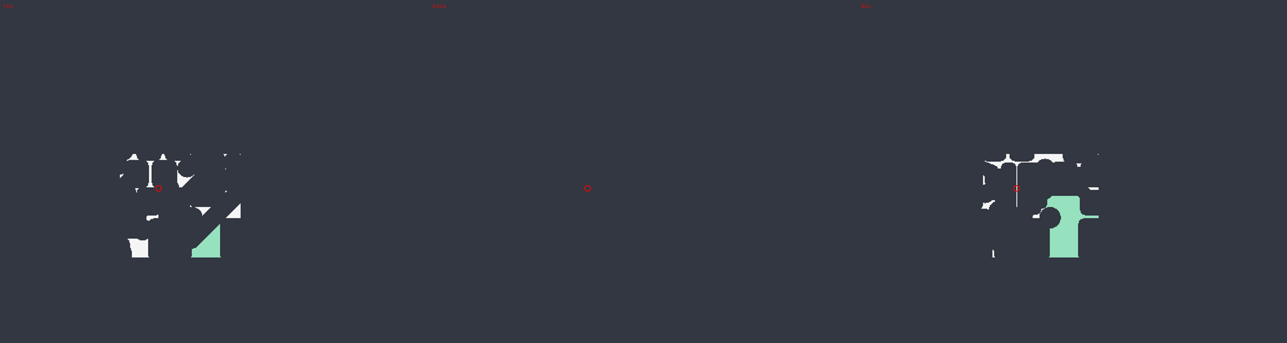
hardware/system-review/electrical/routing-candidate/raw-input-local.png
