magnus188/trimix-analysator/hardware/system-review/electrical/routing-candidate/regn-cc-bridge-scout.png

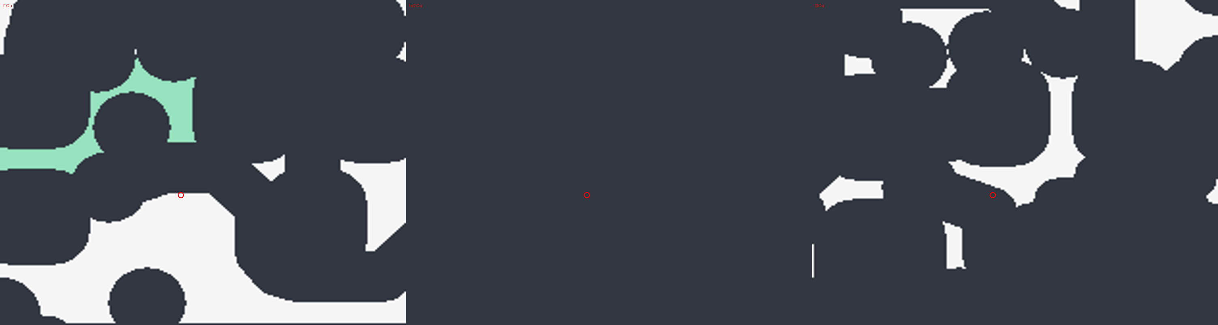
hardware/system-review/electrical/routing-candidate/regn-cc-bridge-scout.png
