magnus188/trimix-analysator/hardware/system-review/electrical/routing-candidate/regn-gateway-outer.png

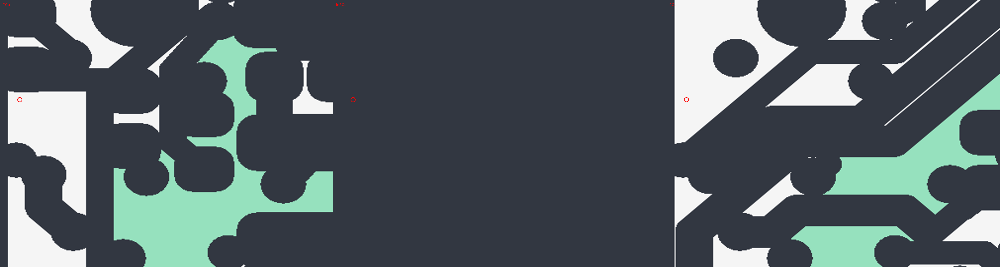
hardware/system-review/electrical/routing-candidate/regn-gateway-outer.png
