magnus188/trimix-analysator/hardware/system-review/electrical/routing-candidate/regn-slot-free-dogbone.png

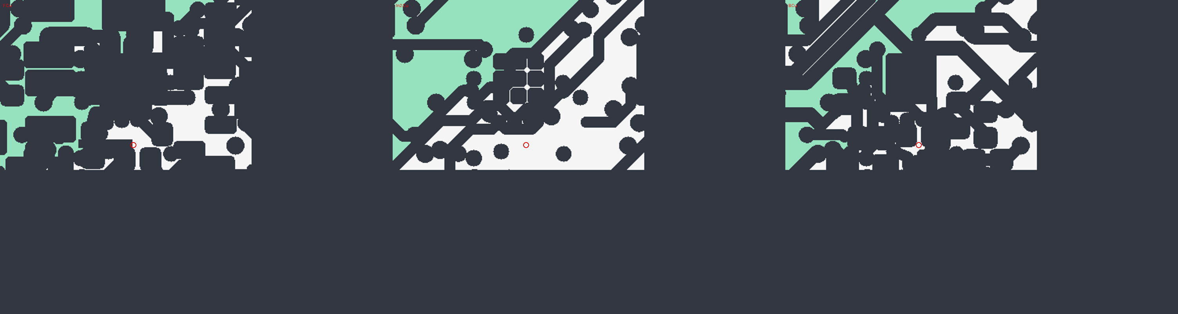
hardware/system-review/electrical/routing-candidate/regn-slot-free-dogbone.png
