magnus188/trimix-analysator/hardware/system-review/electrical/routing-candidate/regn-slot-in2-ts-proposal.png

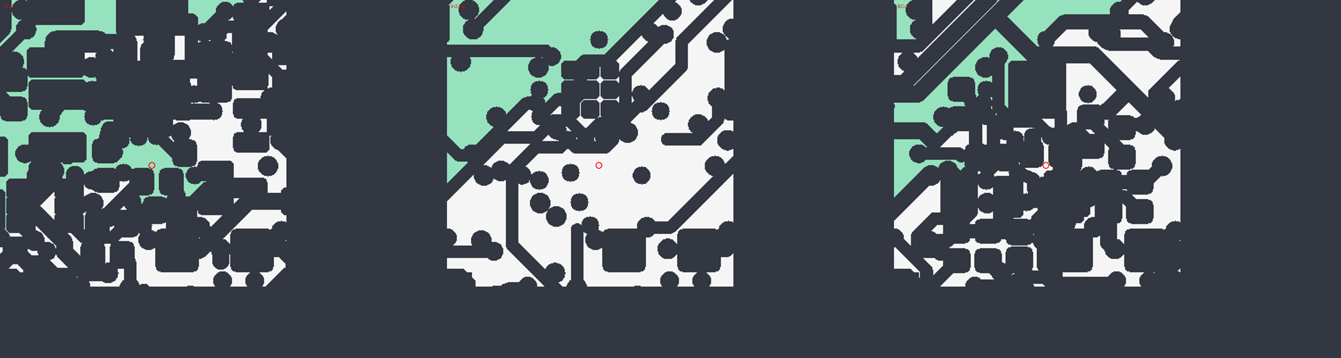
hardware/system-review/electrical/routing-candidate/regn-slot-in2-ts-proposal.png
