magnus188/trimix-analysator/hardware/system-review/electrical/routing-candidate/regn-slot-proposal.png

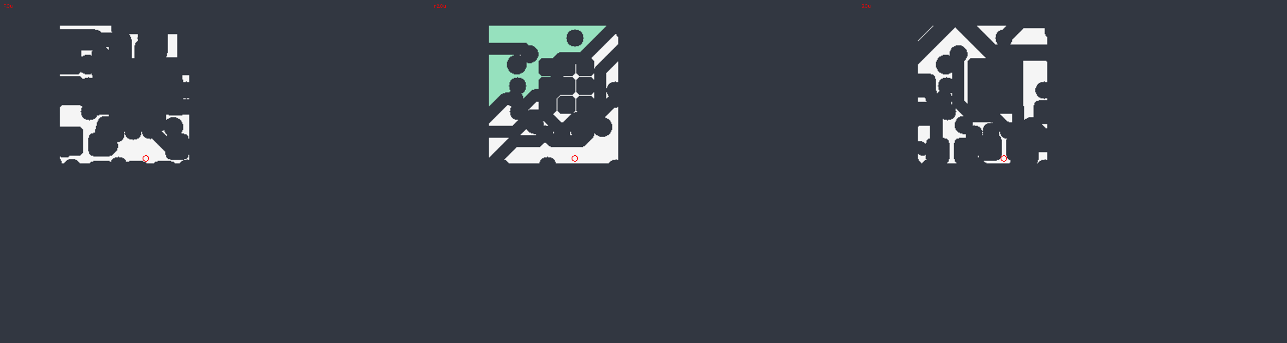
hardware/system-review/electrical/routing-candidate/regn-slot-proposal.png
