magnus188/trimix-analysator/hardware/system-review/electrical/routing-candidate/remote-cc-route-proposal/standalone-plane-views.png

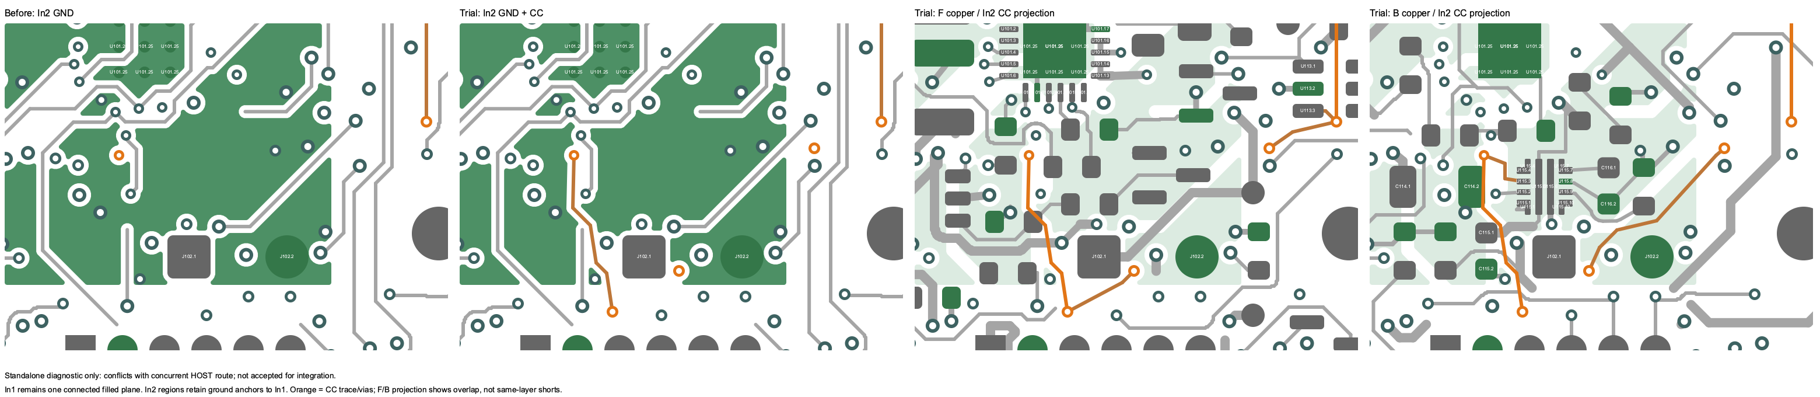
hardware/system-review/electrical/routing-candidate/remote-cc-route-proposal/standalone-plane-views.png
