magnus188/trimix-analysator/hardware/system-review/electrical/routing-candidate/sensitive-layout-refinement/before-local-promotion/main-final-9f274fdf/fill-cap-process/fill-cap-map.png

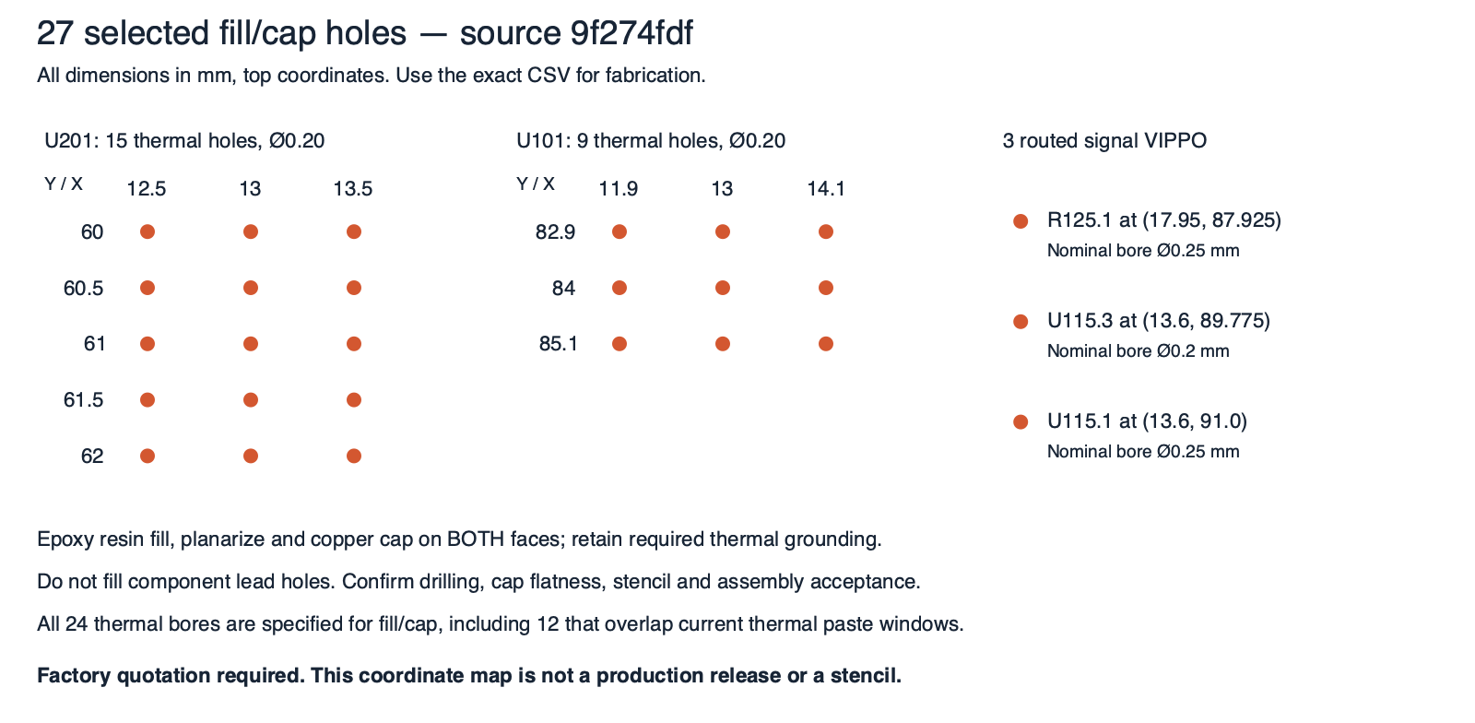
hardware/system-review/electrical/routing-candidate/sensitive-layout-refinement/before-local-promotion/main-final-9f274fdf/fill-cap-process/fill-cap-map.png
