magnus188/trimix-analysator/hardware/system-review/electrical/routing-candidate/sensitive-layout-refinement/c103-source/tdk-land.png

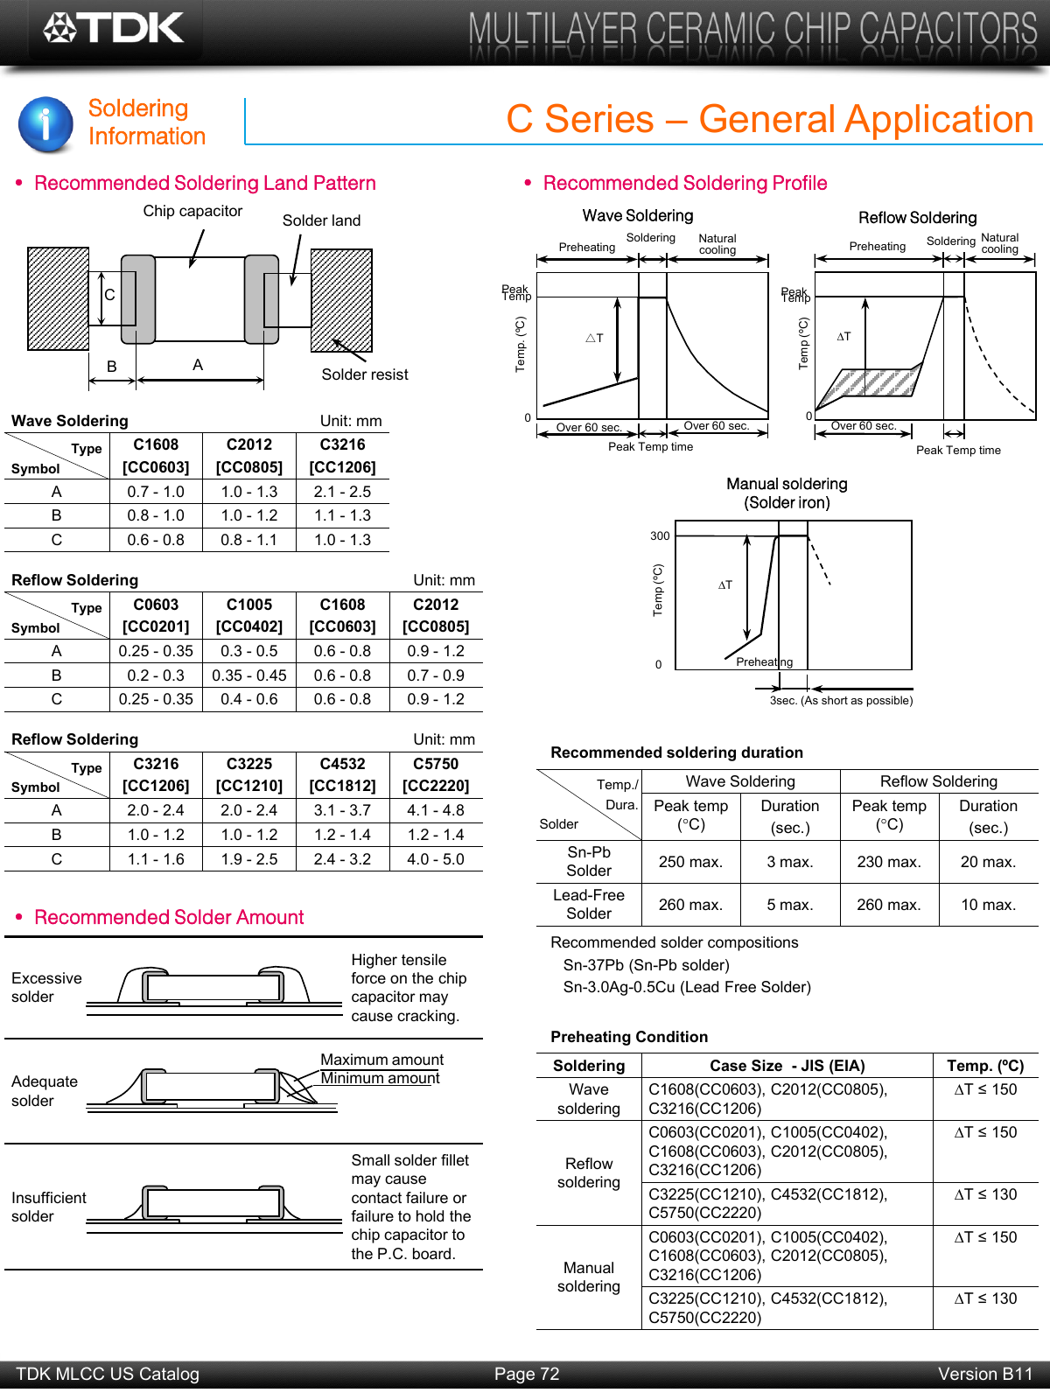
hardware/system-review/electrical/routing-candidate/sensitive-layout-refinement/c103-source/tdk-land.png
