magnus188/trimix-analysator/hardware/system-review/electrical/routing-candidate/sensitive-layout-refinement/frozen-local-bundle/review/co.png

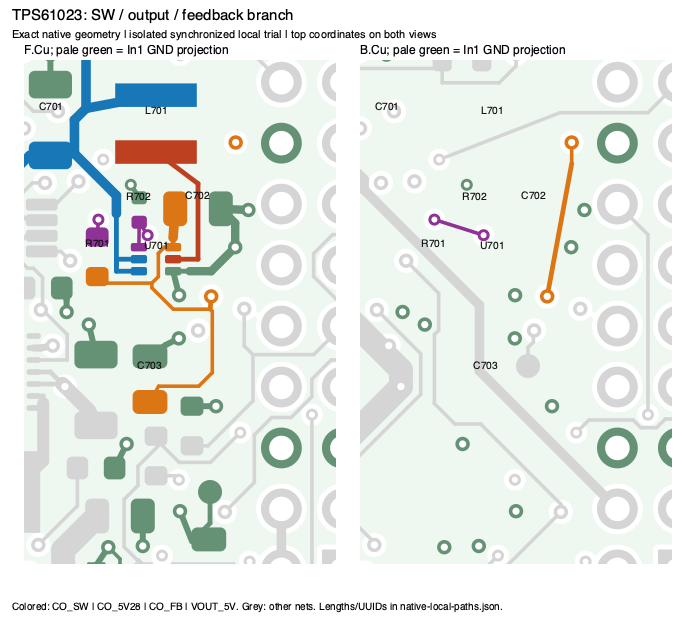
hardware/system-review/electrical/routing-candidate/sensitive-layout-refinement/frozen-local-bundle/review/co.png
