magnus188/trimix-analysator/hardware/system-review/electrical/routing-candidate/sensitive-layout-refinement/frozen-local-bundle/review/tps63020.png

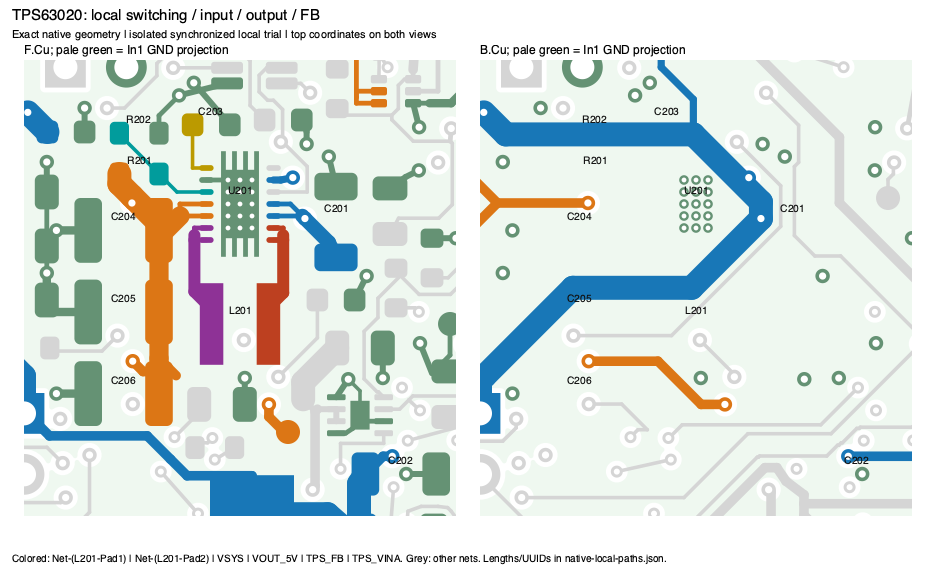
hardware/system-review/electrical/routing-candidate/sensitive-layout-refinement/frozen-local-bundle/review/tps63020.png
