magnus188/trimix-analysator/hardware/system-review/electrical/routing-candidate/sensitive-layout-refinement/synchronized-clean/bq.png

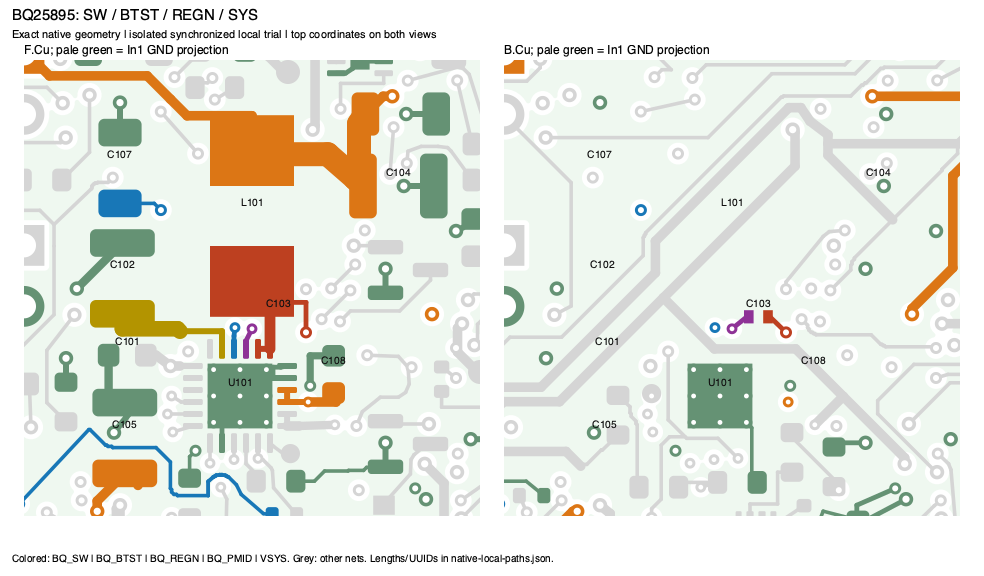
hardware/system-review/electrical/routing-candidate/sensitive-layout-refinement/synchronized-clean/bq.png
