magnus188/trimix-analysator/hardware/system-review/electrical/routing-candidate/set-cc-root-proposal/vippo-cc/ground-review/cc-ground-before-after.png

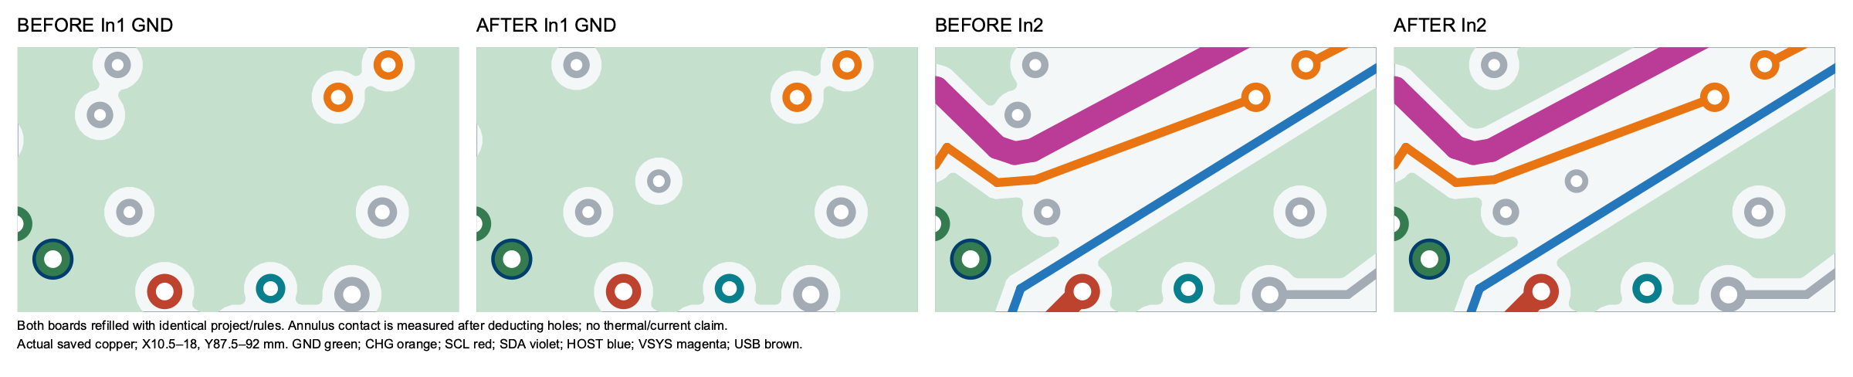
hardware/system-review/electrical/routing-candidate/set-cc-root-proposal/vippo-cc/ground-review/cc-ground-before-after.png
