magnus188/trimix-analysator/hardware/system-review/electrical/routing-candidate/sys-bulk-slot-scout.png

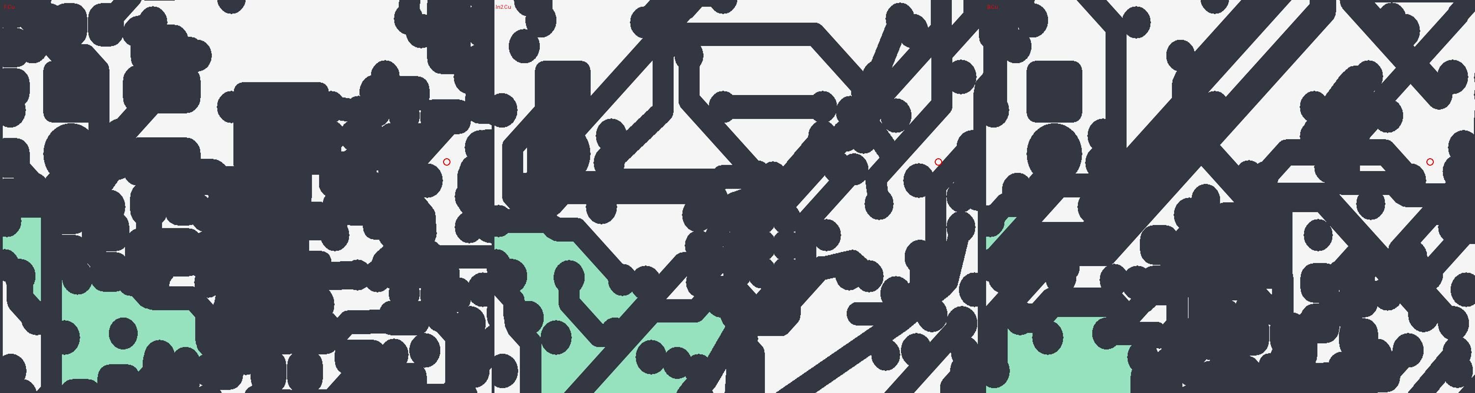
hardware/system-review/electrical/routing-candidate/sys-bulk-slot-scout.png
