magnus188/trimix-analysator/hardware/system-review/electrical/routing-candidate/uvlo-vippo-upper-inner.png

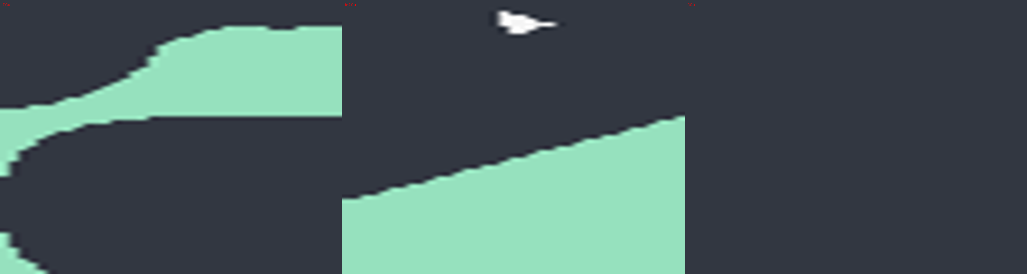
hardware/system-review/electrical/routing-candidate/uvlo-vippo-upper-inner.png
