magnus188/trimix-analysator/hardware/system-review/electrical/routing-candidate/uvlo-vippo-upper-route.png

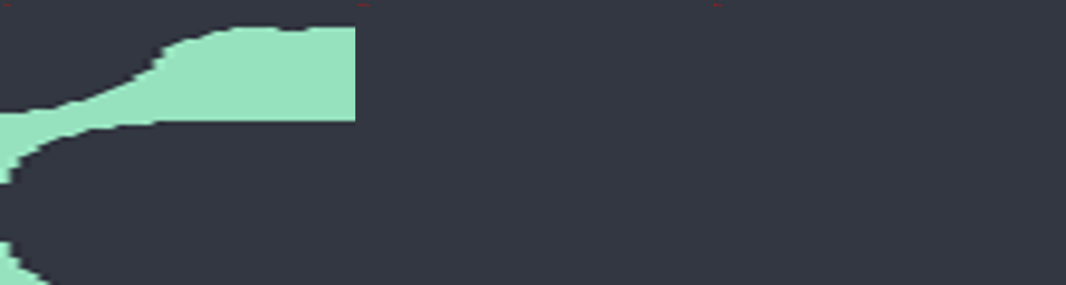
hardware/system-review/electrical/routing-candidate/uvlo-vippo-upper-route.png
