magnus188/trimix-analysator/hardware/system-review/electrical/sensitive-layout-refinement/c107-0805/c107.png

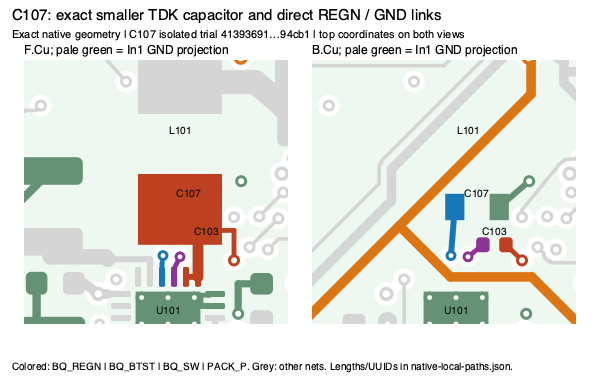
hardware/system-review/electrical/sensitive-layout-refinement/c107-0805/c107.png
