magnus188/trimix-analysator/hardware/system-review/electrical/sensitive-layout-refinement/c107-0805/sources/murata-typical.png

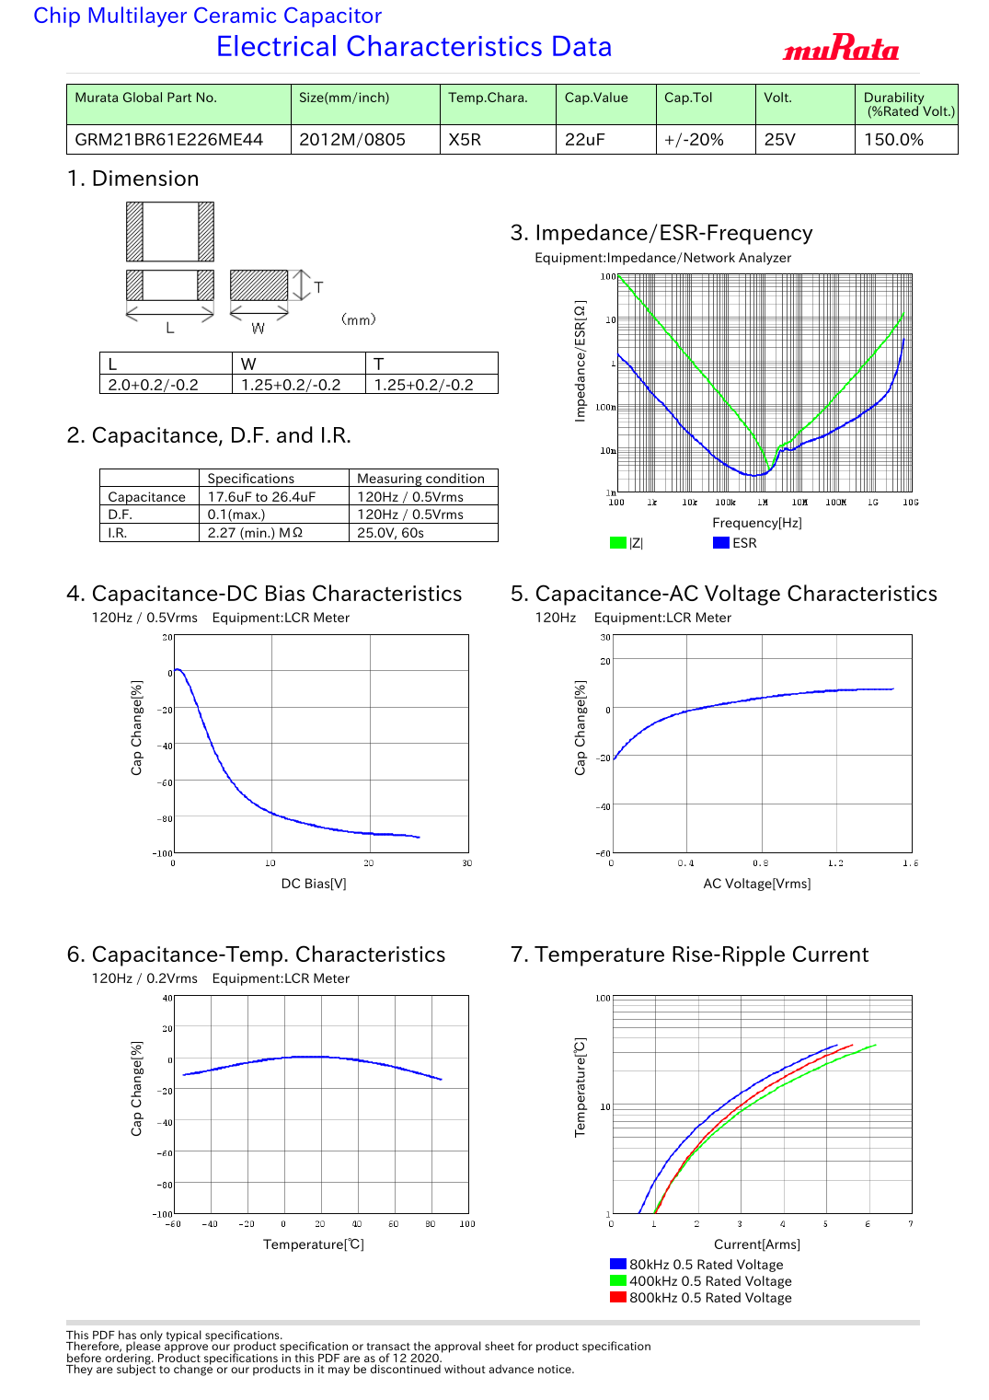
hardware/system-review/electrical/sensitive-layout-refinement/c107-0805/sources/murata-typical.png
