magnus188/trimix-analysator/hardware/system-review/electrical/sensitive-layout-refinement/c107-0805/sources/original-tdk-22u25v.png

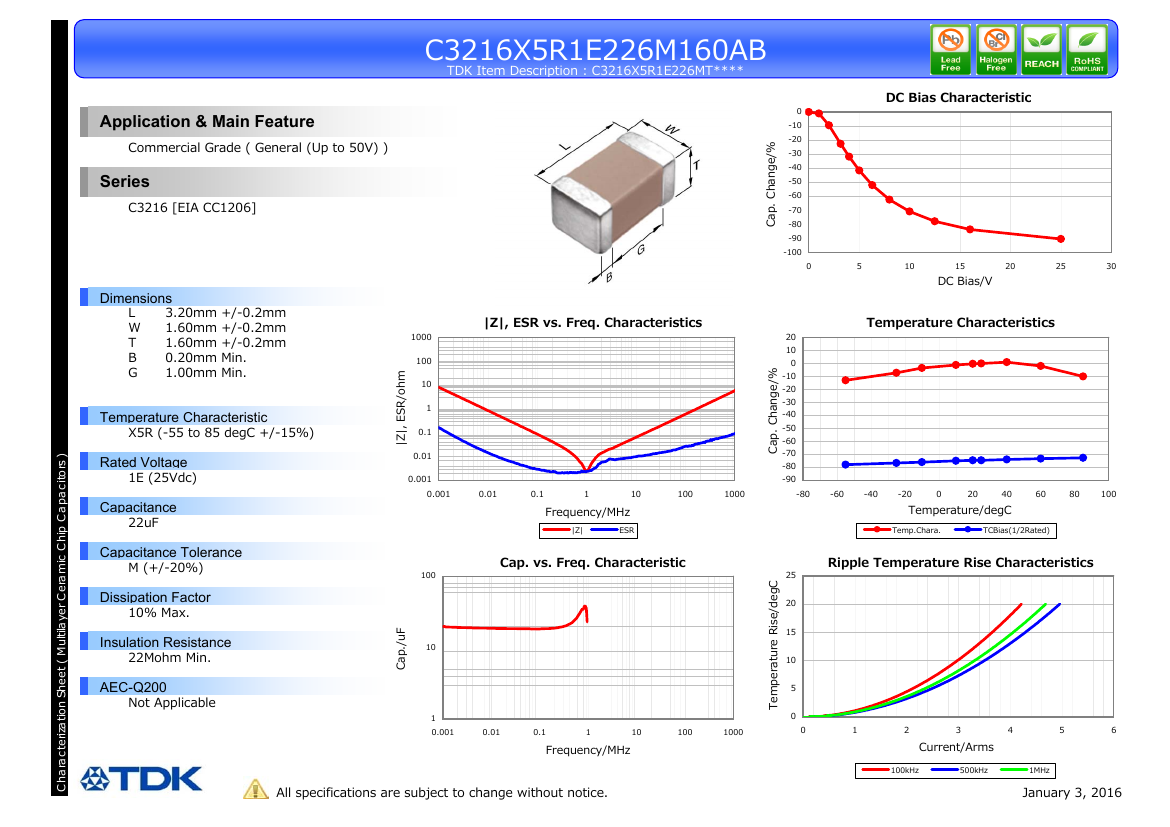
hardware/system-review/electrical/sensitive-layout-refinement/c107-0805/sources/original-tdk-22u25v.png
