magnus188/trimix-analysator/hardware/system-review/electrical/sources/c3216x5r1e476m160ac_20190710.png

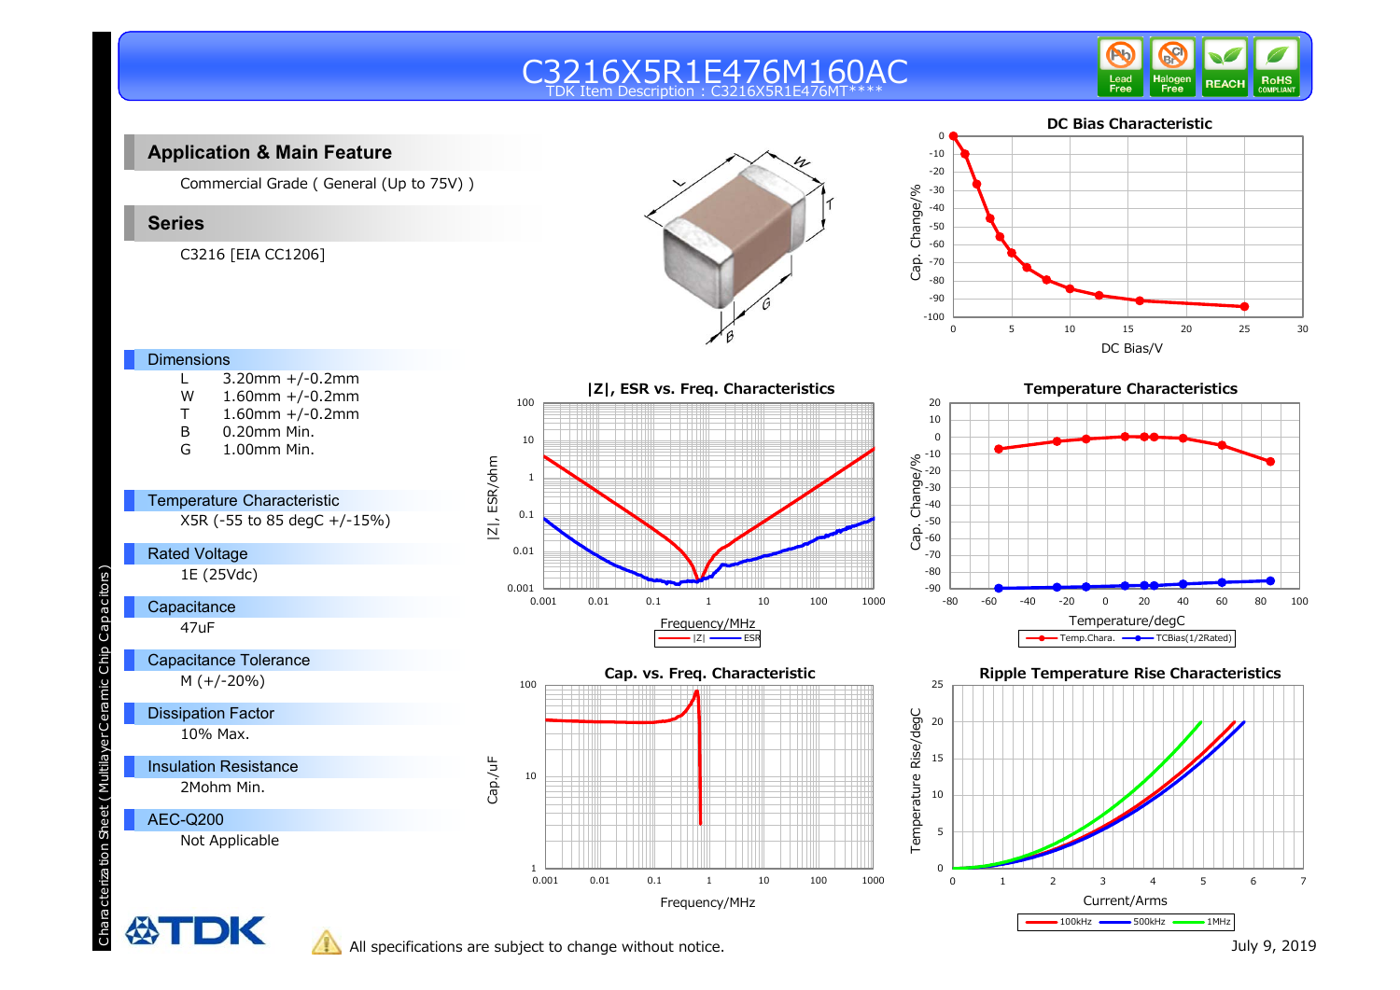
hardware/system-review/electrical/sources/c3216x5r1e476m160ac_20190710.png
