magnus188/trimix-analysator/hardware/system-review/electrical/sources/pi3usb9201-8.png

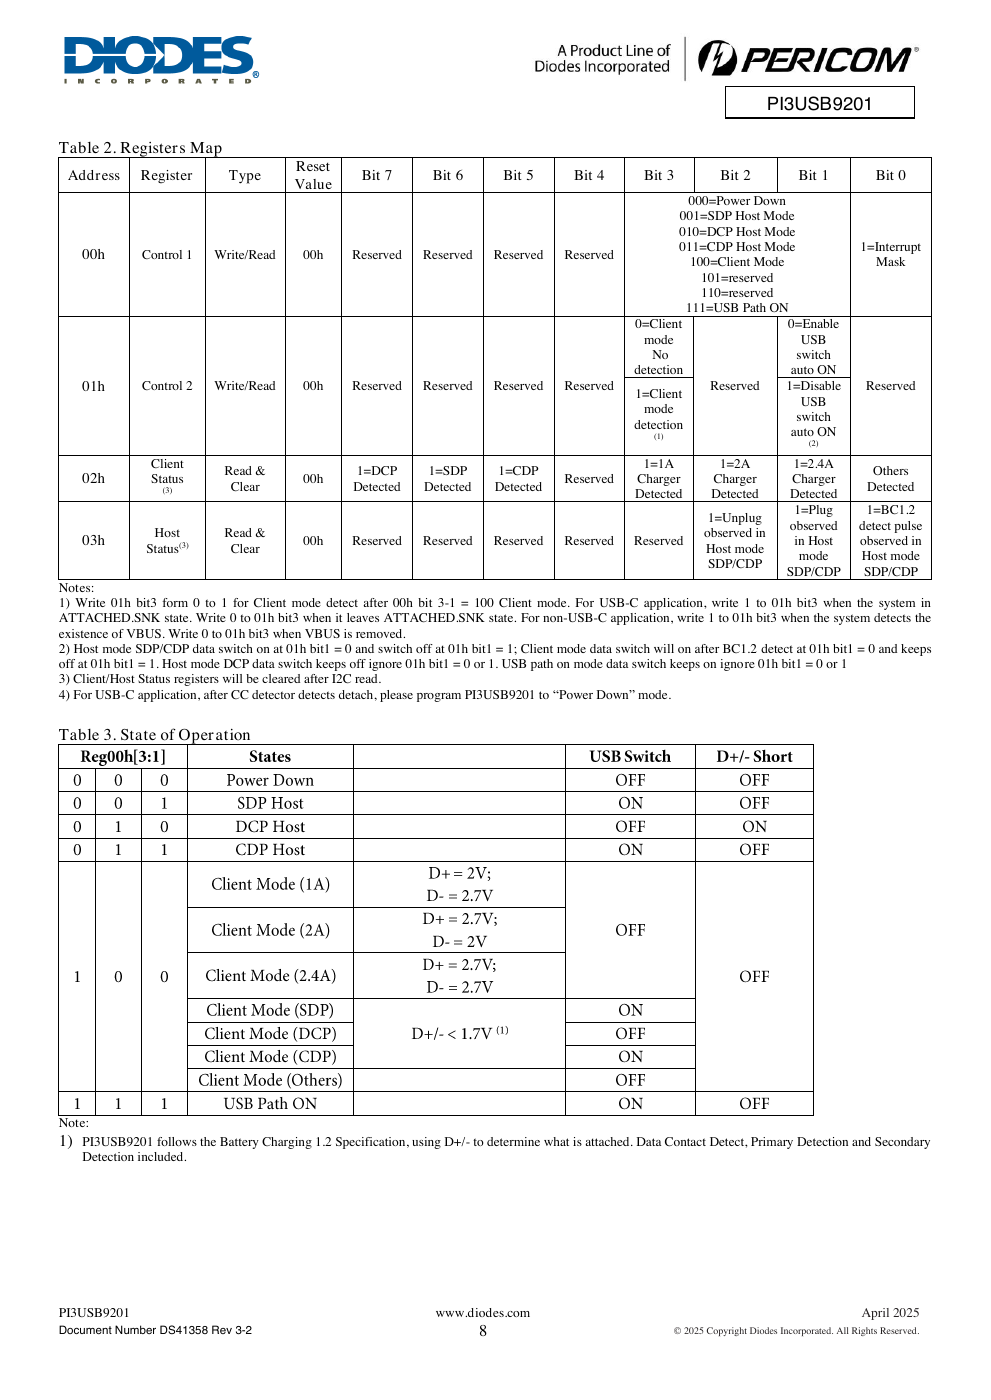
hardware/system-review/electrical/sources/pi3usb9201-8.png
