magnus188/trimix-analysator/hardware/system-review/electrical/sources/pi3usb9201-11.png

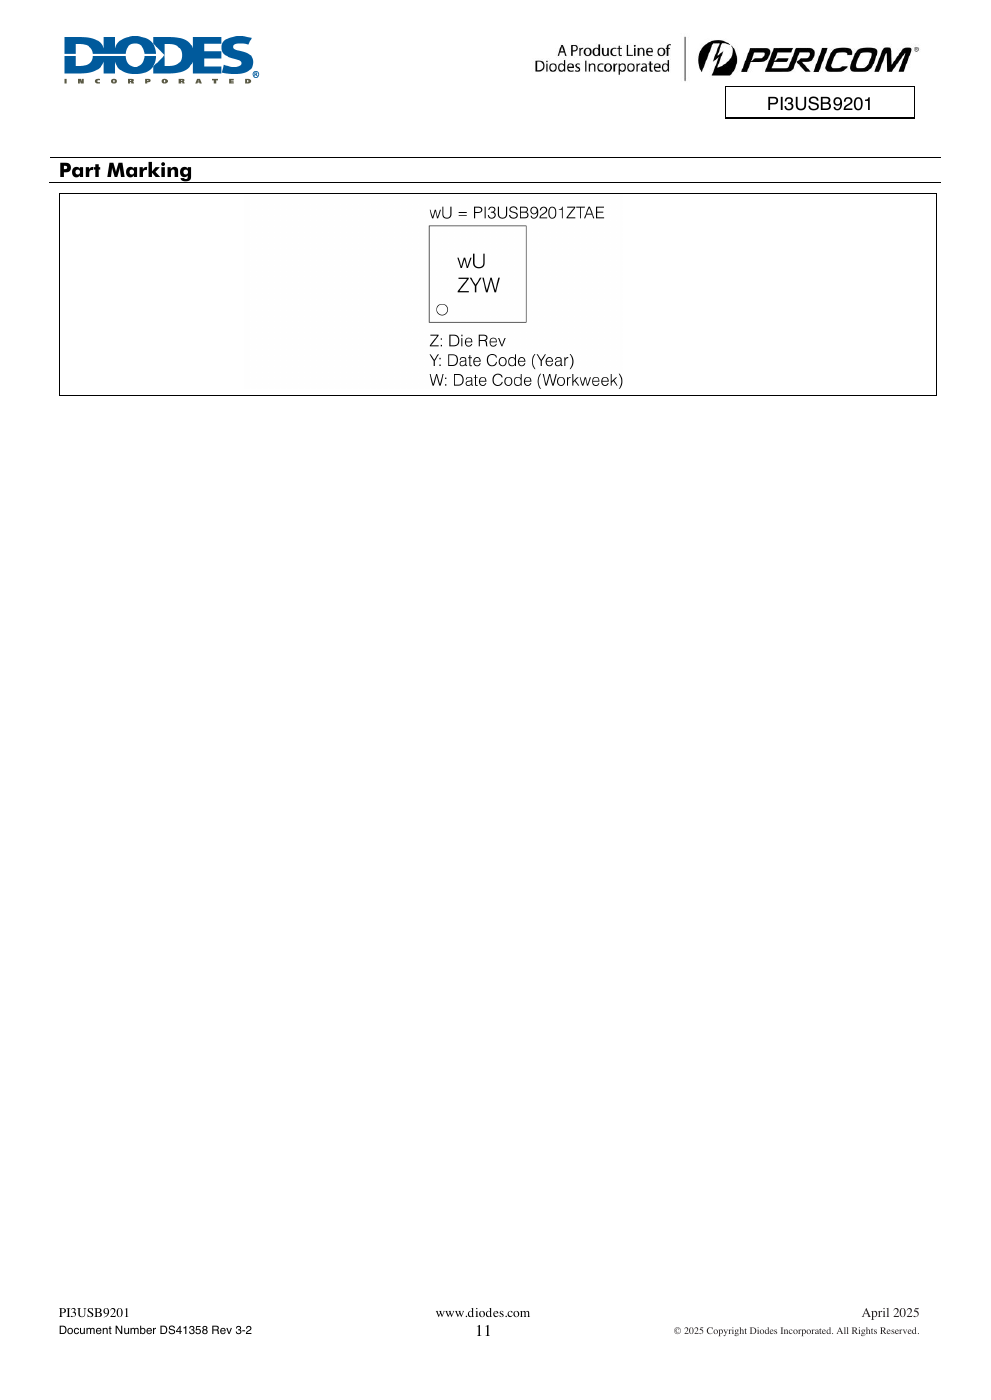
hardware/system-review/electrical/sources/pi3usb9201-11.png
