magnus188/trimix-analysator/hardware/system-review/electrical/usb-final-independent/gerber-bottom.png

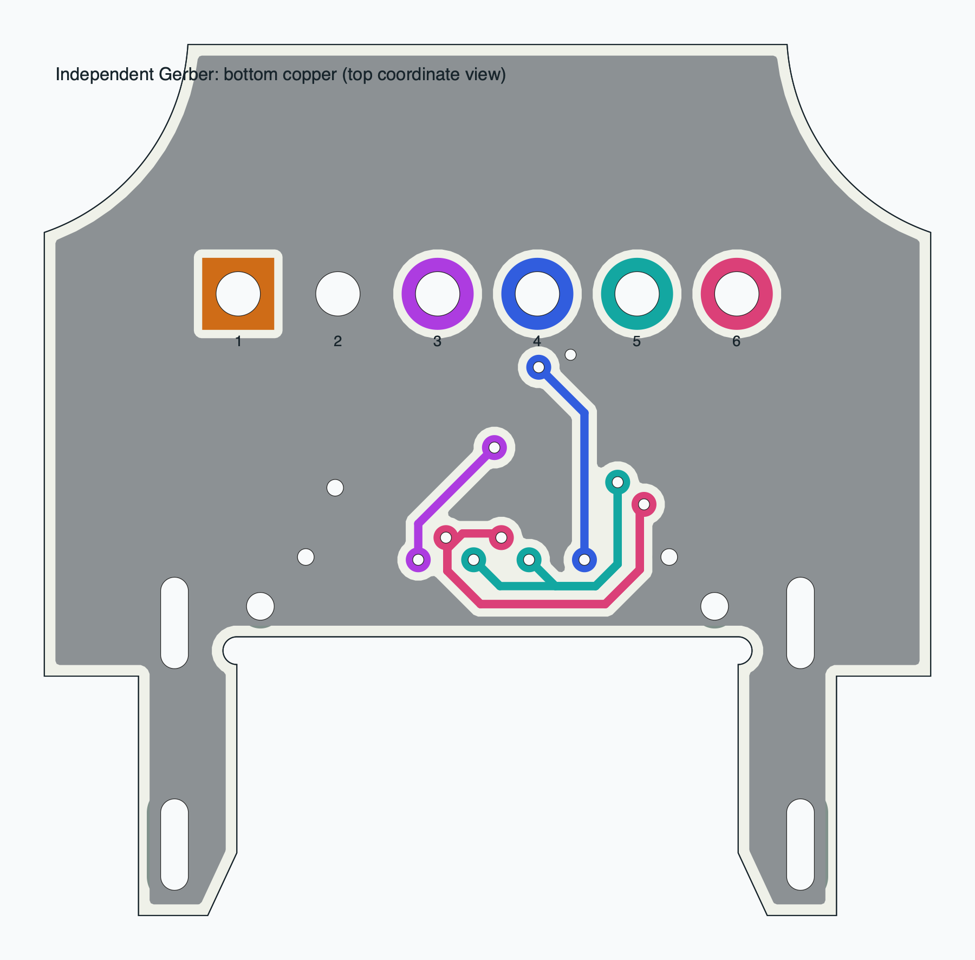
hardware/system-review/electrical/usb-final-independent/gerber-bottom.png
