magnus188/trimix-analysator/hardware/system-review/electrical/usb-final-independent/gerber-top.png

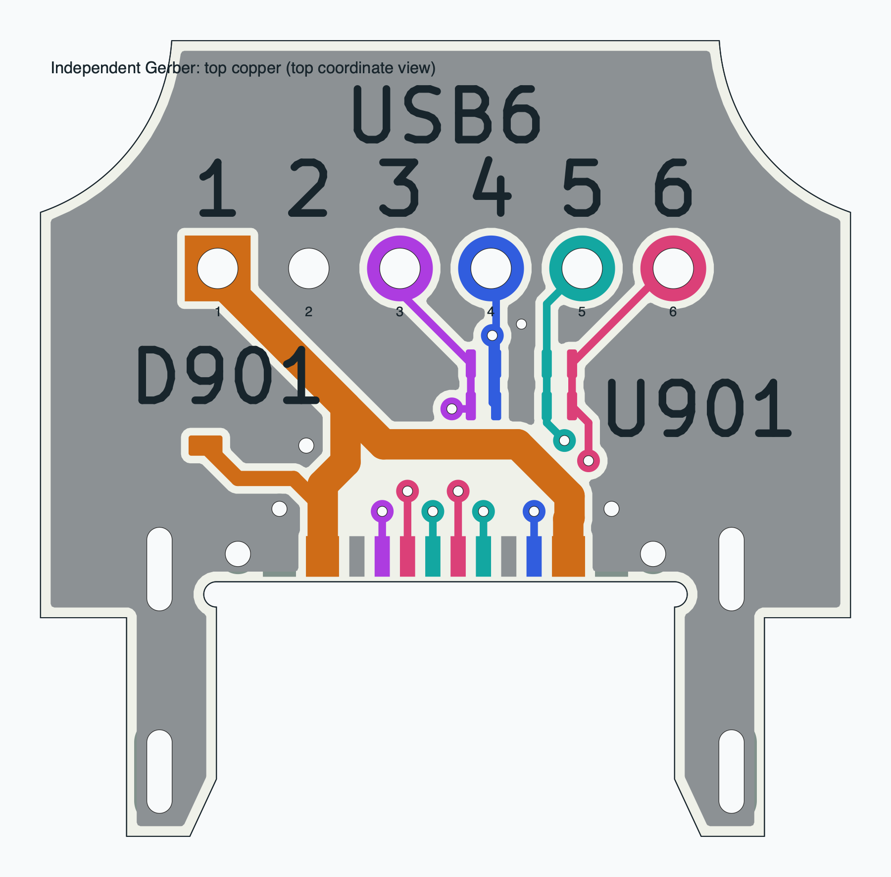
hardware/system-review/electrical/usb-final-independent/gerber-top.png
