magnus188/trimix-analysator/hardware/system-review/electrical/usb-final/usb-schematic.png

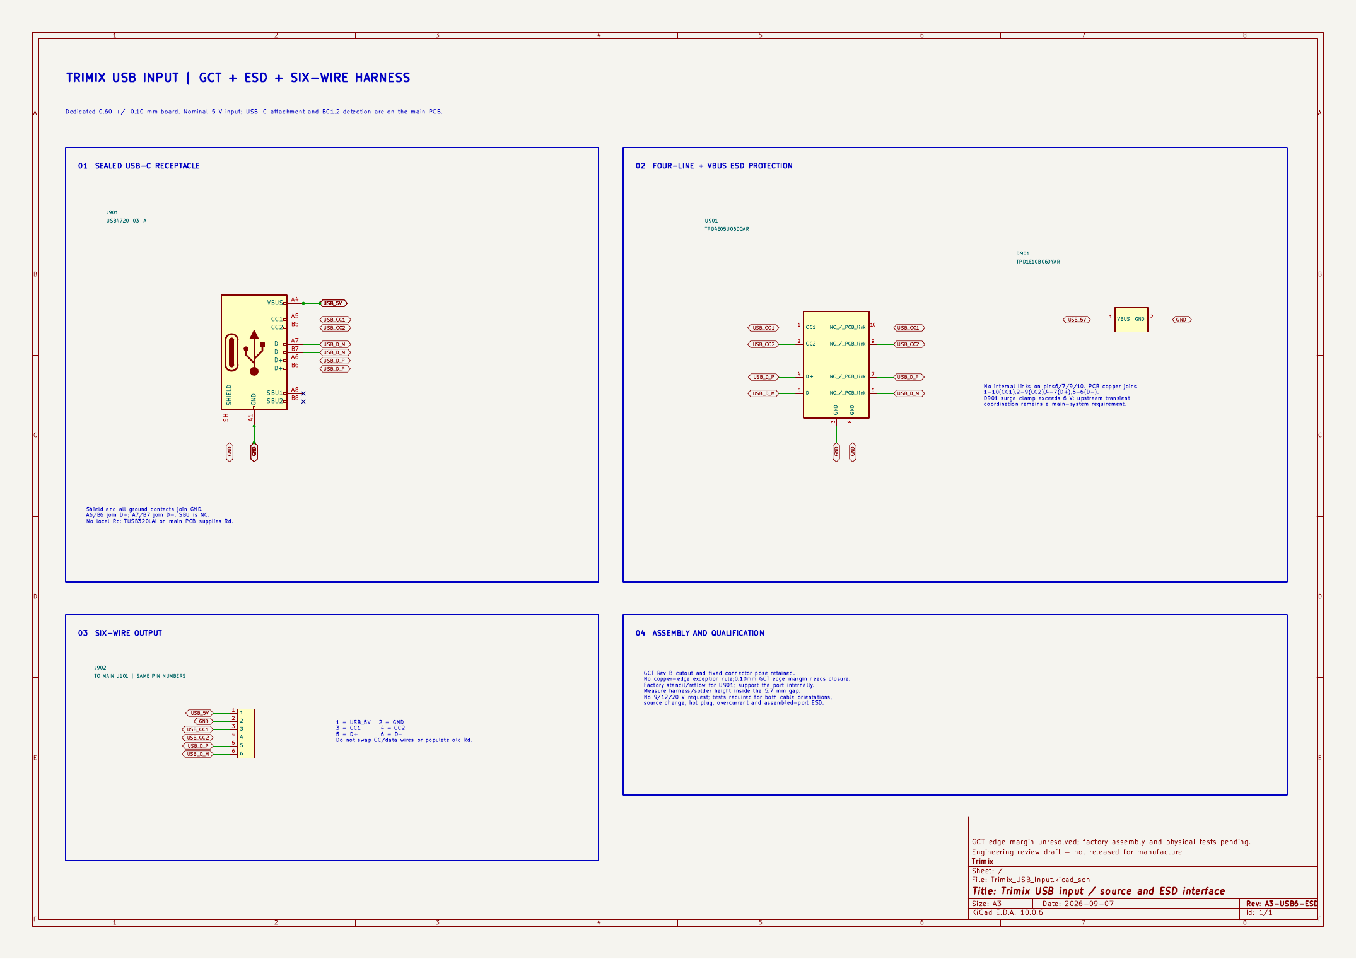
hardware/system-review/electrical/usb-final/usb-schematic.png
