magnus188/trimix-analysator/hardware/system-review/electrical/usb-final/usb-top.png

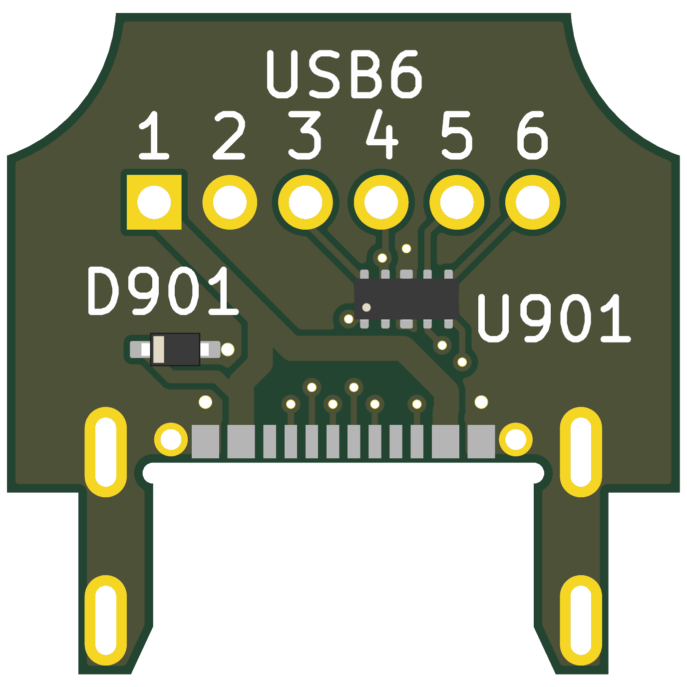
hardware/system-review/electrical/usb-final/usb-top.png
