magnus188/trimix-analysator/hardware/system-review/electrical/usb-protection-research/tps22950-q1-review-package.png

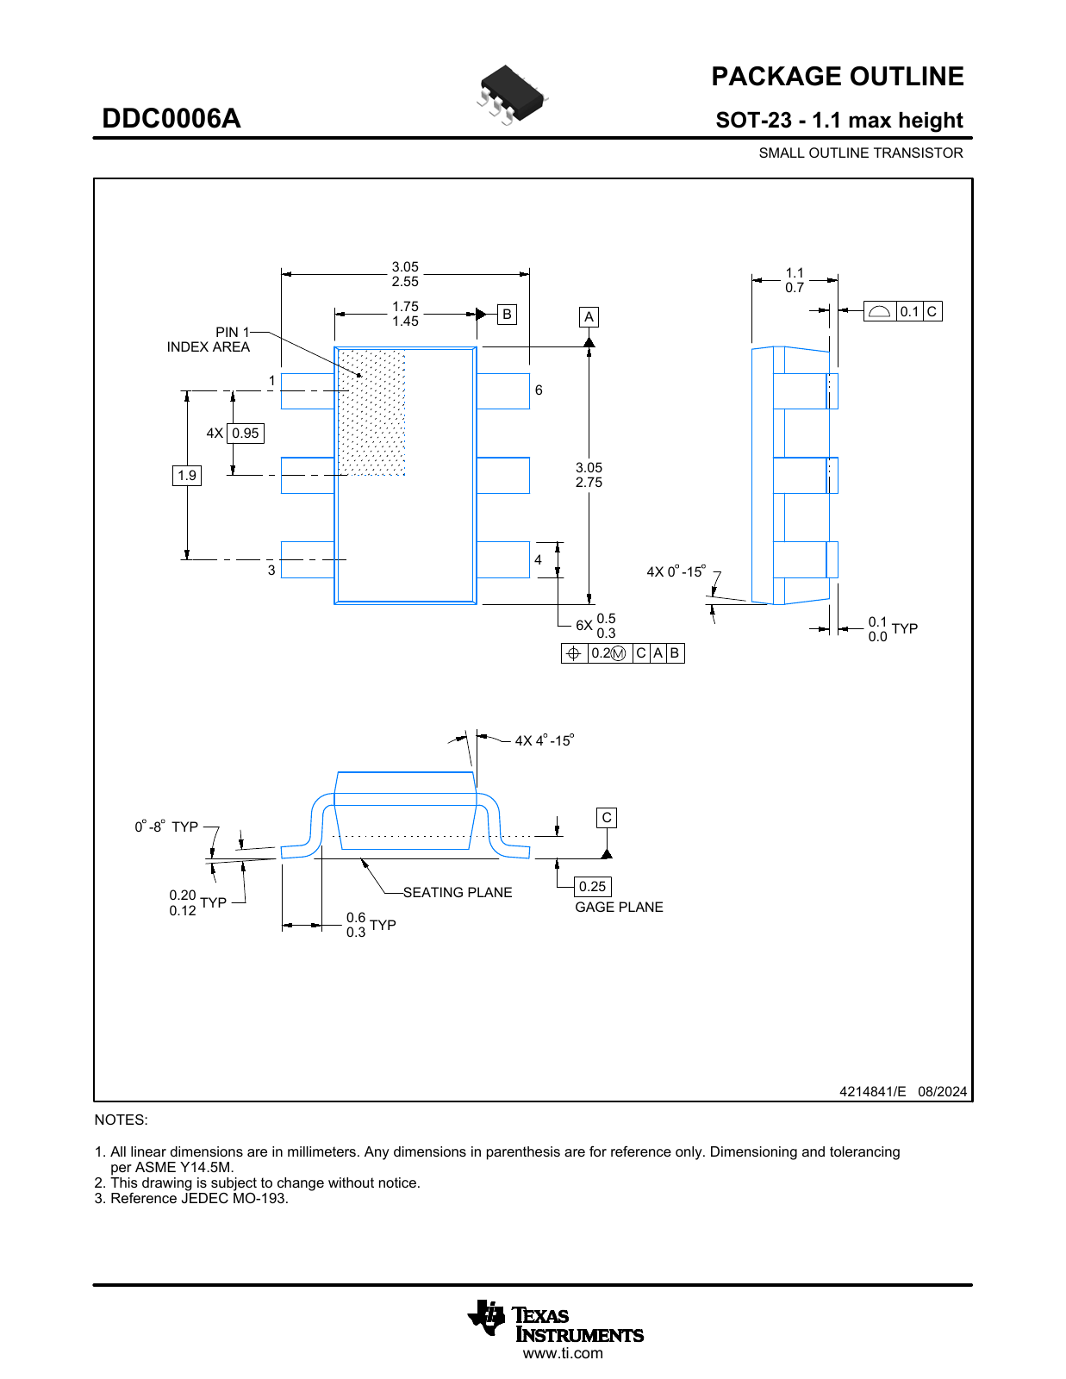
hardware/system-review/electrical/usb-protection-research/tps22950-q1-review-package.png
