magnus188/trimix-analysator/hardware/system-review/integration-photo/IMG_0571.png

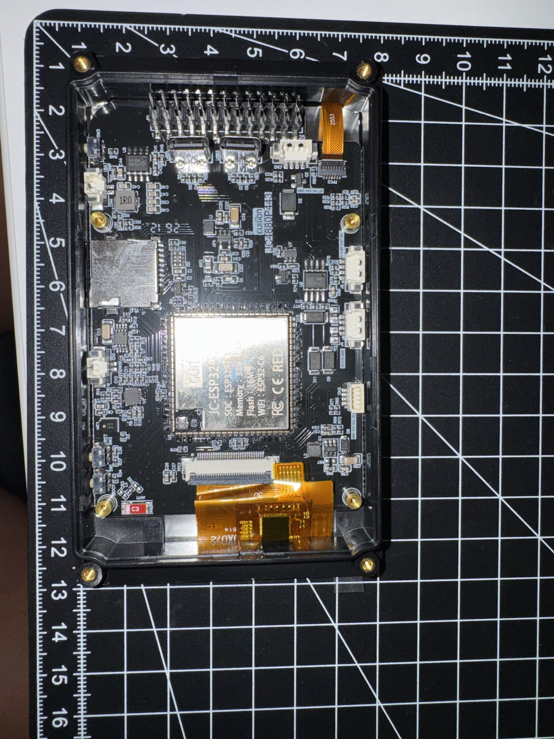
hardware/system-review/integration-photo/IMG_0571.png
