magnus188/trimix-analysator/hardware/system-review/interface-renders/page-1.png

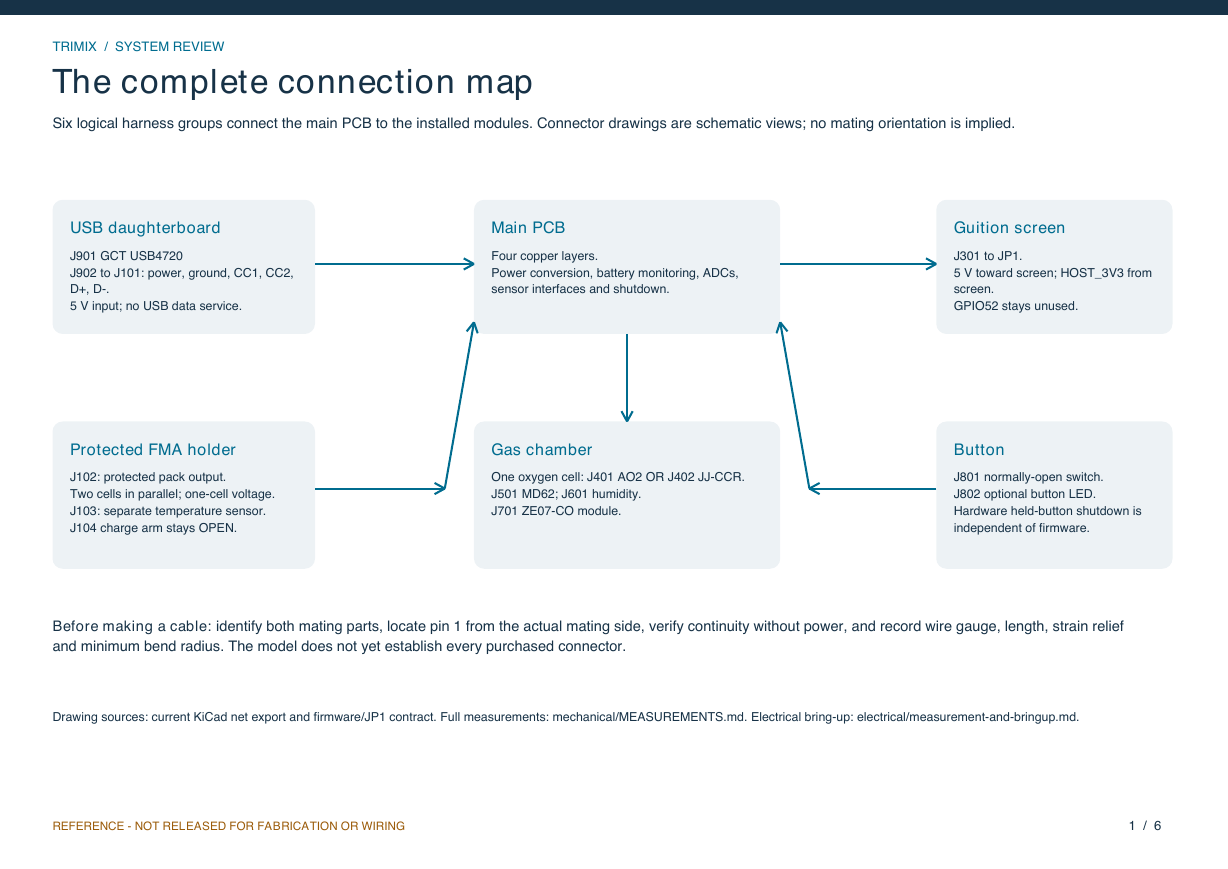
hardware/system-review/interface-renders/page-1.png
