magnus188/trimix-analysator/hardware/system-review/interface-renders/page-2.png

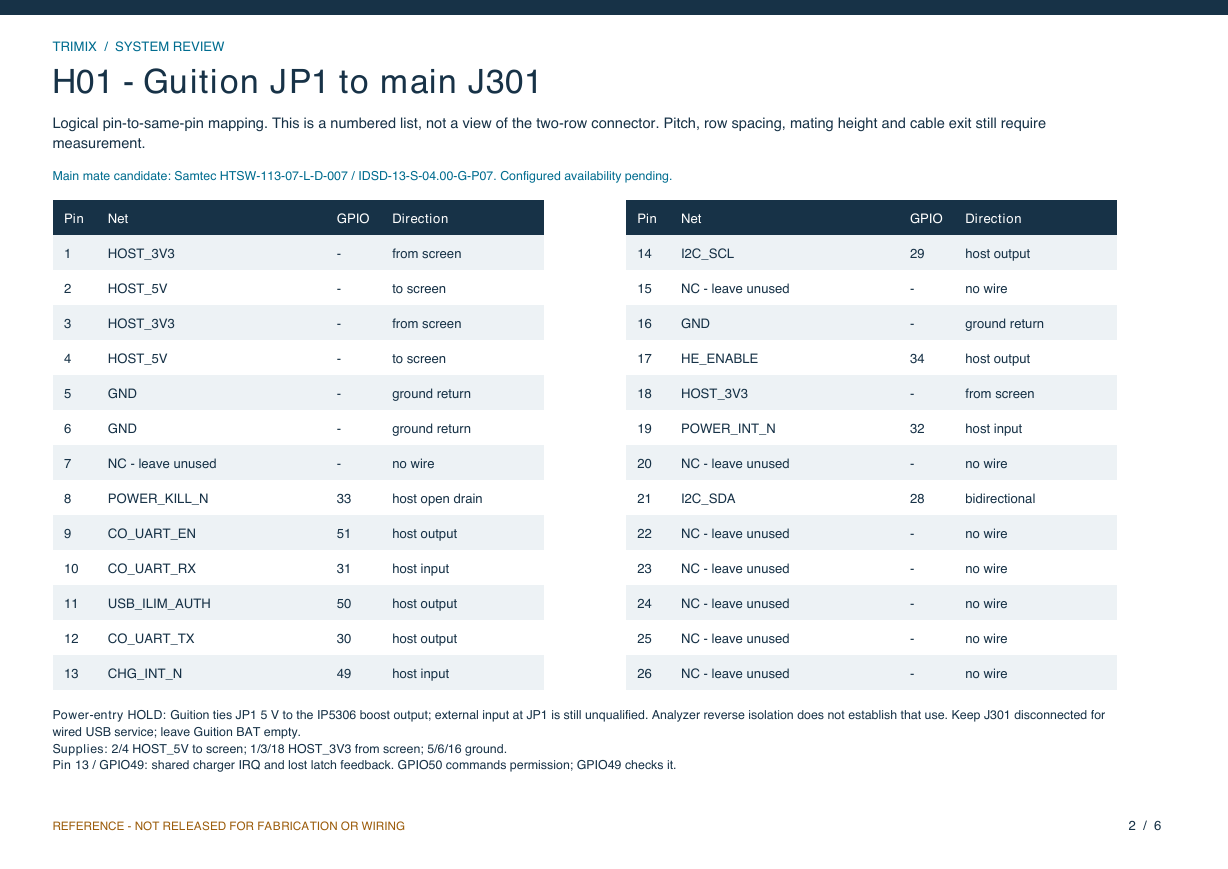
hardware/system-review/interface-renders/page-2.png
