magnus188/trimix-analysator/hardware/system-review/interface-renders/page-3.png

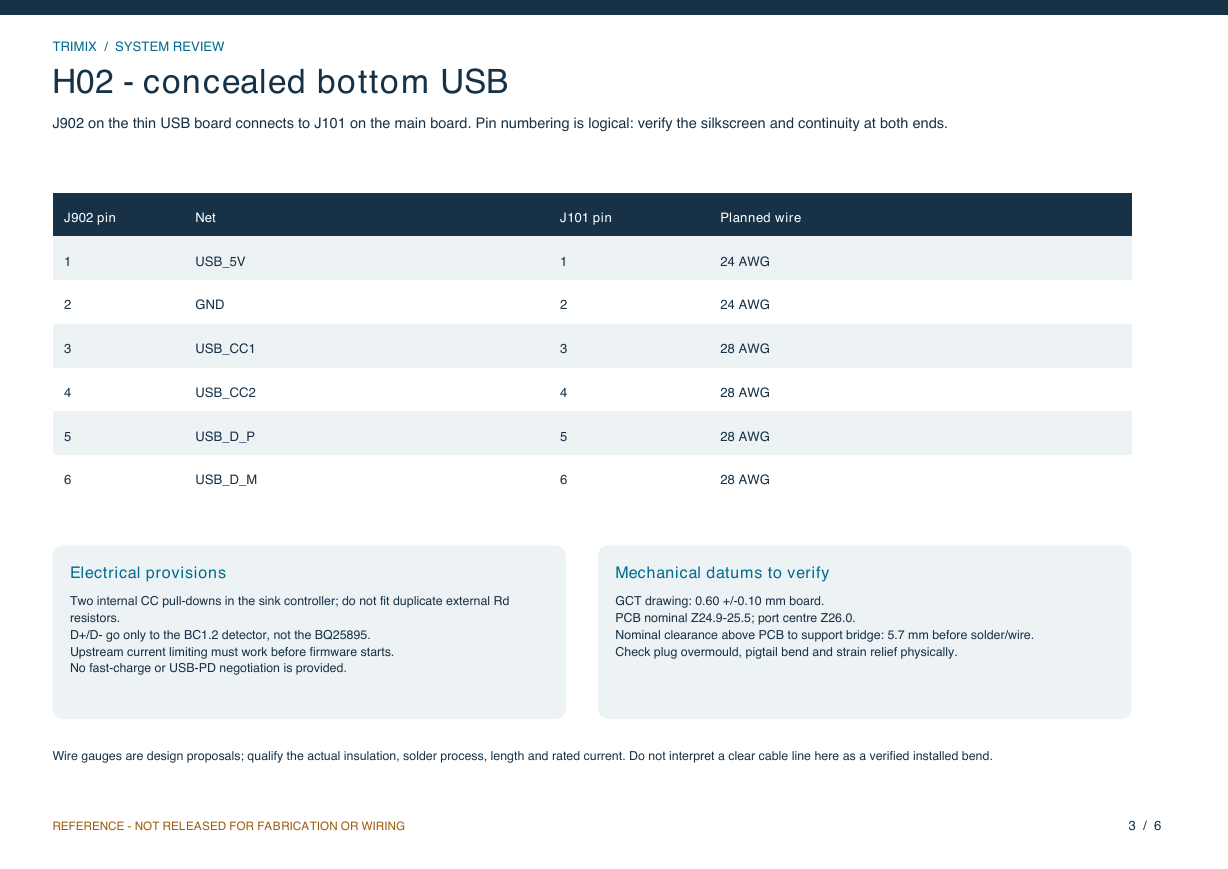
hardware/system-review/interface-renders/page-3.png
