magnus188/trimix-analysator/hardware/system-review/interface-renders/page-4.png

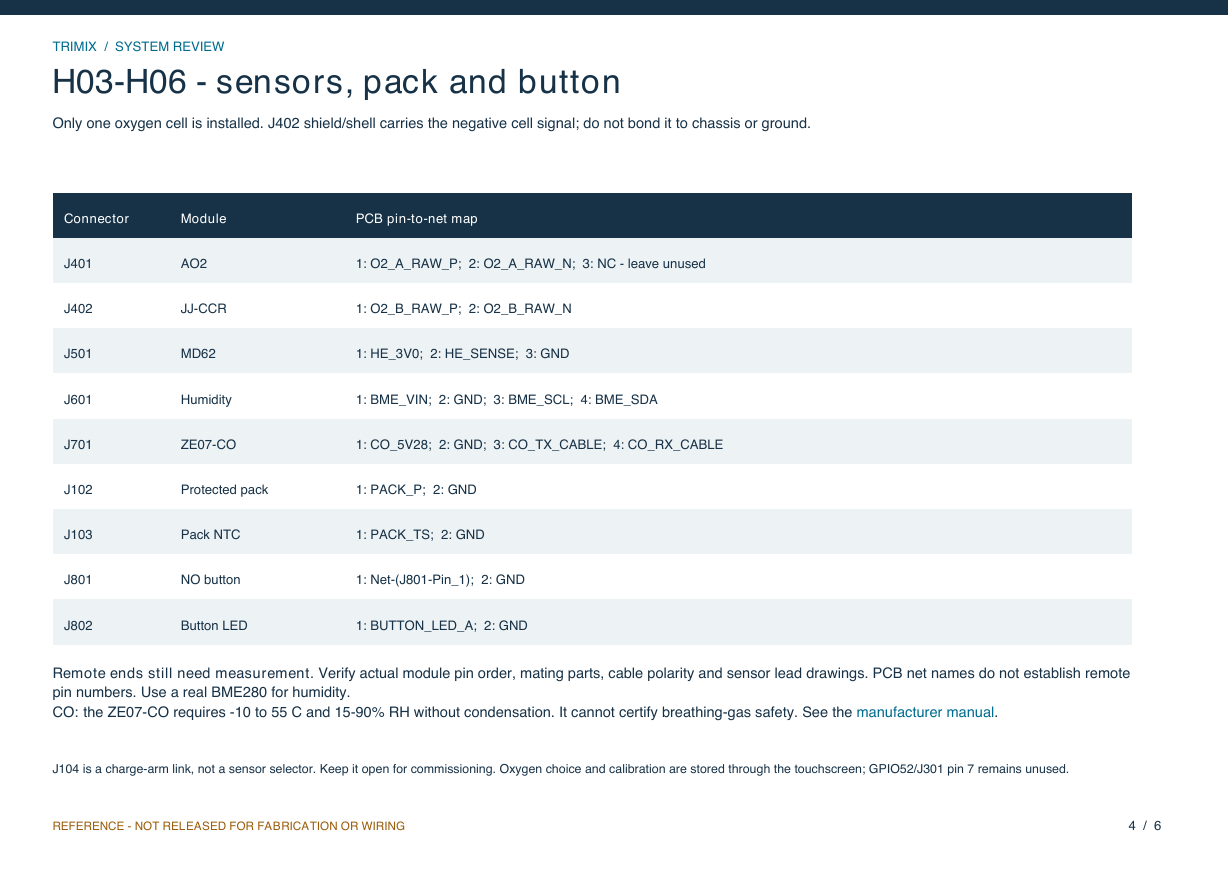
hardware/system-review/interface-renders/page-4.png
