magnus188/trimix-analysator/hardware/system-review/interface-renders/page-5.png

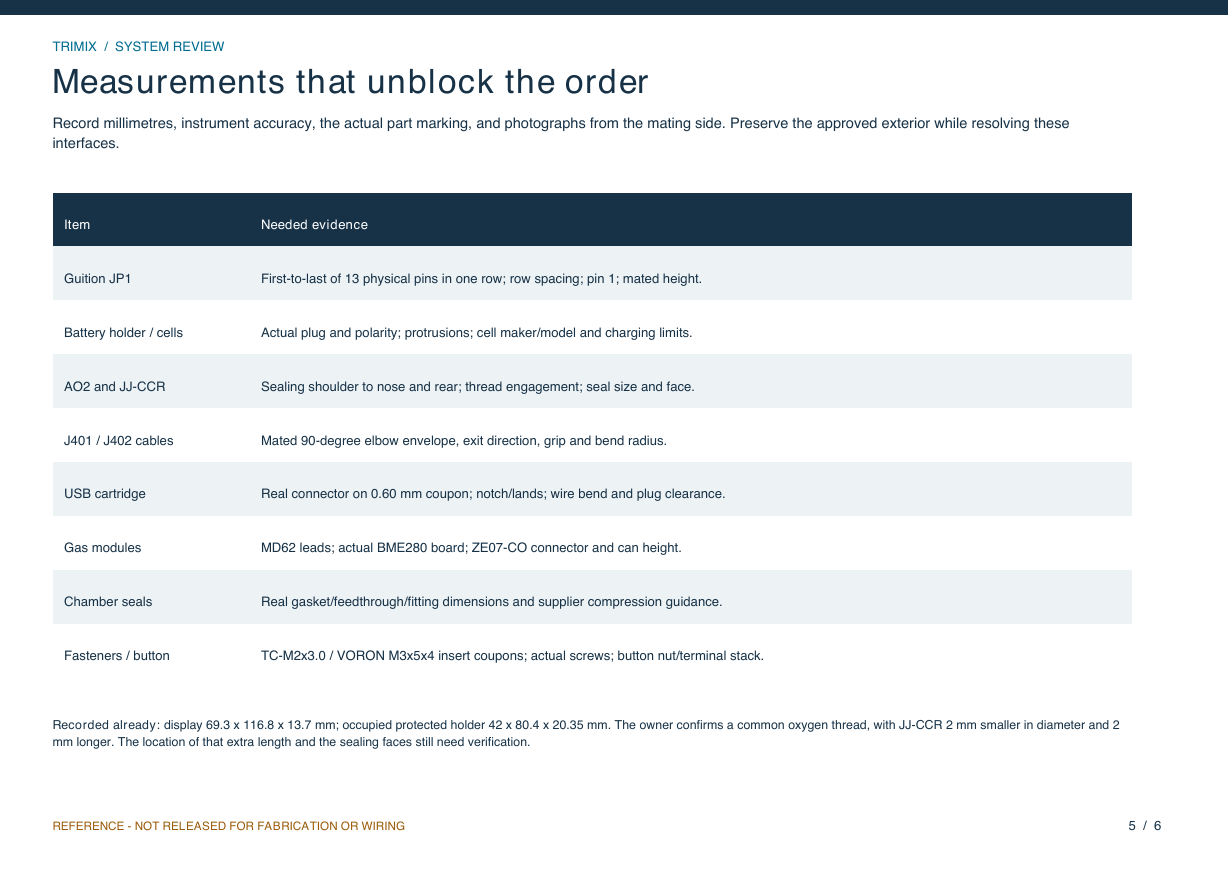
hardware/system-review/interface-renders/page-5.png
