magnus188/trimix-analysator/hardware/system-review/interface-renders/page-6.png

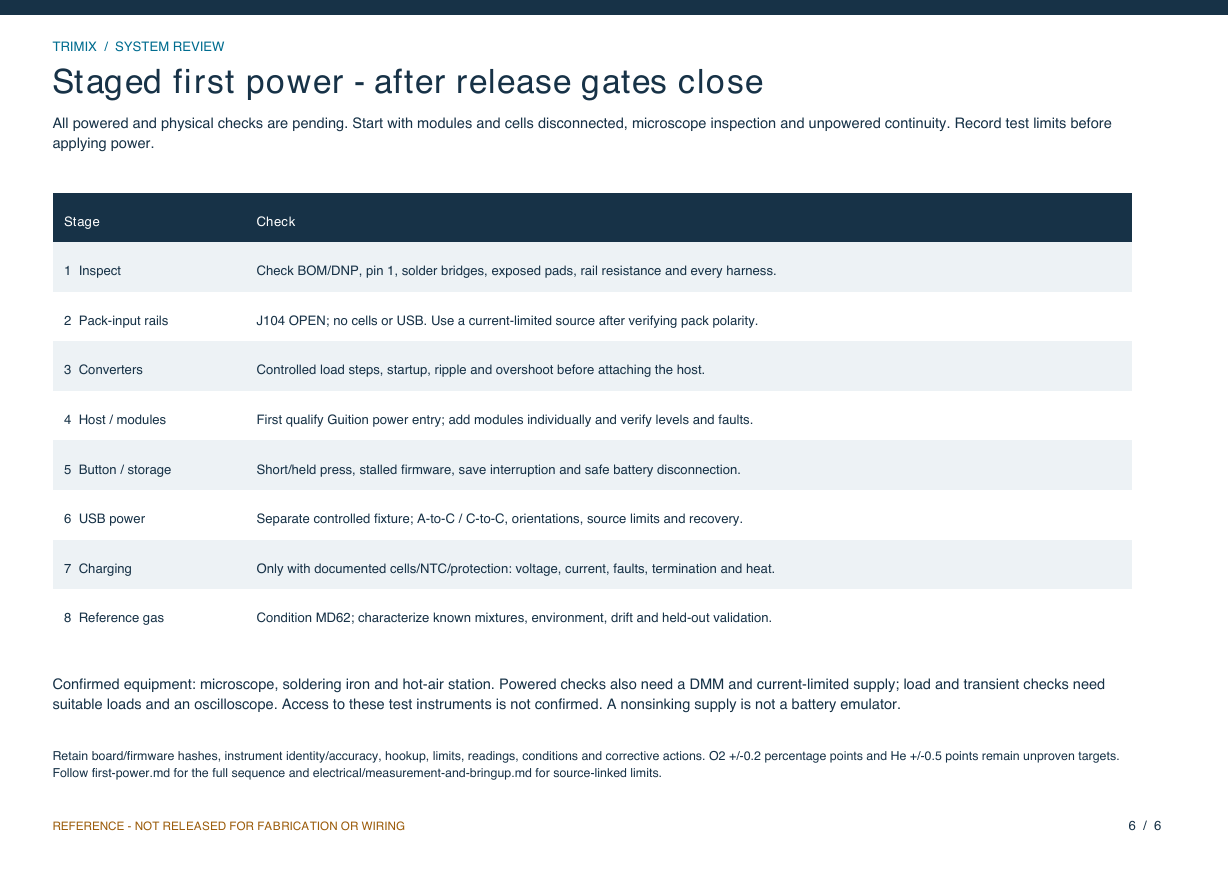
hardware/system-review/interface-renders/page-6.png
