magnus188/trimix-analysator/hardware/system-review/mechanical/connector-review/guition-photo-oblique.png

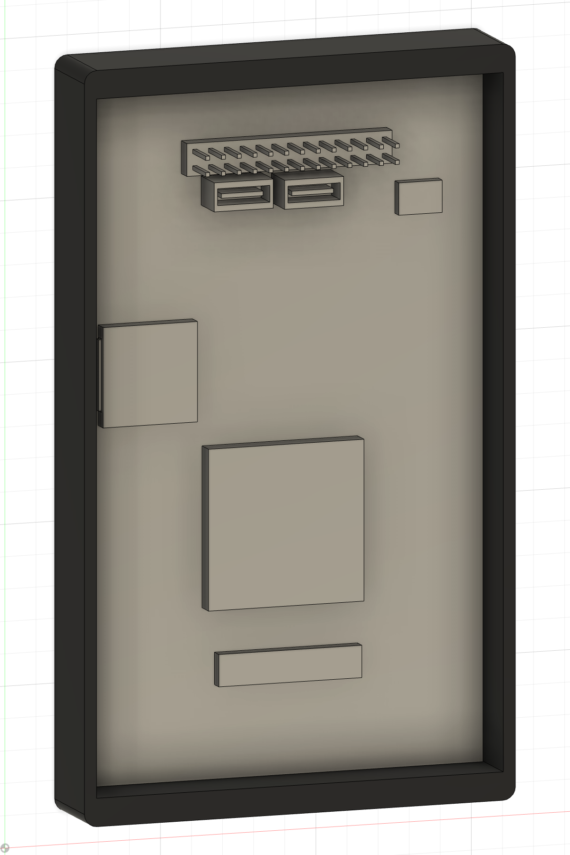
hardware/system-review/mechanical/connector-review/guition-photo-oblique.png
