magnus188/trimix-analysator/hardware/system-review/mechanical/views/carrier-backside-allocation.png

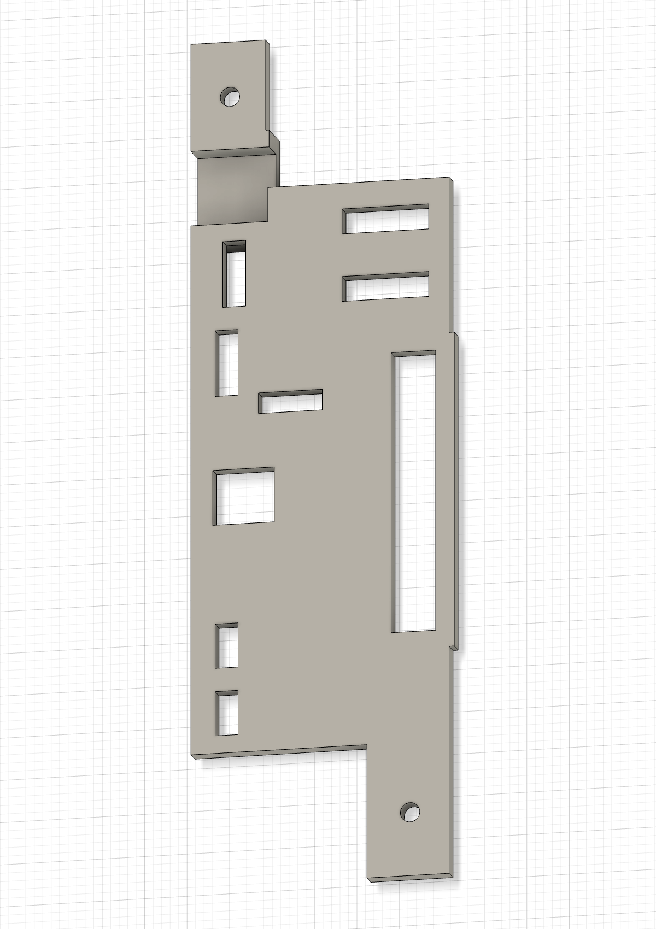
hardware/system-review/mechanical/views/carrier-backside-allocation.png
