magnus188/trimix-analysator/hardware/system-review/software/oxygen/views/oxygen-air-check.png

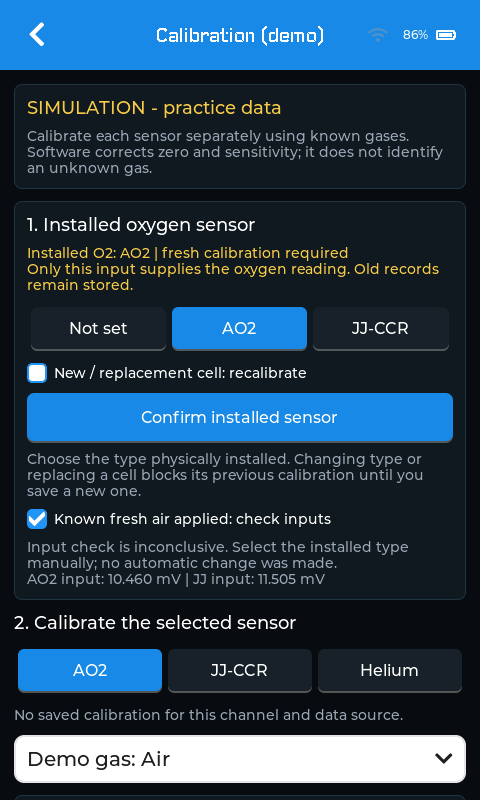
hardware/system-review/software/oxygen/views/oxygen-air-check.png
