magnus188/trimix-analysator/simulator/build-sanitize/Testing/Temporary/CTestCostData.txt

gas_calculator 10 0.00624043
analysis_calculator 10 0.00555965
sensor_interface 10 0.00609574
gas_acquisition 10 0.00549494
analysis_history 10 0.00532647
cylinder_profiles 10 0.0057319
ui_smoke 9 0.164645
test_oxygen_selection 10 0.00559976
test_ota_storage 10 0.00562209
test_power_environment 10 0.00561427
acquisition_engine 10 0.0485239
storage_maintenance_race 10 0.00986712
usb_source 10 0.00560118
bc12_source 10 0.00562405
usb_input_policy 10 0.00519569
esp_storage_no-free-pages 9 0.0061831
esp_storage_new-nvs-version 9 0.00566669
esp_storage_pending-rollback 9 0.00573391
esp_storage_accepted-upgrade 9 0.00568161
esp_storage_valid-image 9 0.00573383
system_review_tools 7 0.0286697
charge_standby 5 0.0120408
backlight_standby 5 0.0142273
power_worker_normal 5 0.0111963
power_worker_maintenance 5 0.0106674
power_worker_maintenance-last 5 0.0102817
power_worker_bus-loss 5 0.00980787
power_worker_probation 5 0.0105503
power_worker_charger-irq 5 0.0103497
power_worker_kill-retry 5 0.00983066
usb_input_path 4 0.0139021
power_worker_hiz-requalify 4 0.0134085
power_worker_hiz-ignored 4 0.0135869
power_worker_hiz-maintenance 4 0.013193
power_worker_hiz-maintenance-wait 4 0.0131174
power_worker_hiz-delay 4 0.0123387
power_worker_hiz-timeout 4 0.0136683
power_worker_hiz-adc-ignored 4 0.0123228
power_worker_legacy-dcp 3 0.116549
power_worker_legacy-cdp 3 0.116381
power_worker_legacy-gap 3 0.0170293
power_worker_legacy-detach 3 0.0185902
power_worker_legacy-replug 3 0.0170019
power_worker_legacy-reset 3 0.0170634
power_worker_legacy-before-detection 2 0.0246585
power_worker_legacy-during-detection 2 0.0254842
power_worker_legacy-after-collection 2 0.0245476
co_qualification 1 0.191244
co_hardware_worker 1 0.178551
co_optional_uart_absent 1 0.0610639
---
