magnus188/trimix-analysator/hardware/cad/rev04/3d-print/FILE_INDEX.csv

path | bytes | sha256 | format | role
README.md | 4536 | 3c3b2205b8ac59fc91670f10e6ee40a6aff08febc497b9339eaf8d6881901a33 | md | artifact or editable source
Trimix_Enclosure_A3_PrintReview.f3d | 2710489 | 4b96520e53cada5e54fdb7040b42f5d6c936345fef0a05a021a3819fd364bebb | f3d | artifact or editable source
Trimix_Enclosure_A3_PrintReview.step | 1842570 | 98d86d36f8525fa6acf3612a33275f23ef257cbfe873215dd1111ae29494d820 | step | artifact or editable source
VERIFICATION.md | 5506 | 864e9c5713dc26288398ece5d8a96a2126d16608efca6e26be0ecca0c8859fa7 | md | artifact or editable source
docs/EXPORT_NOTES.md | 1723 | 5475a9a2e9e8ce477040484ce58528669e38649f5b29351f815b68b98d06aabc | md | artifact or editable source
docs/FIT_CHECKLIST.md | 2957 | 3627e3724c5c9bf3ee798ce33cac327c74502346e5501ebe4a658d22608cb64c | md | artifact or editable source
docs/README.md | 5934 | 113d3b2e0d15183cffca84de7ea18049f0eff0dc0f800401aa1d85edf458987f | md | artifact or editable source
docs/source/assembly-supplies.csv | 958 | b1b02d5ade33d400374afc8752dc3af3cf445aec619b7df02ccf99cde938aa1b | csv | artifact or editable source
docs/source/printed-parts.csv | 4979 | b8fb09d0259a1c2cb8fed73873ce72ee0aa9e37d12d65b4aaa2d1120a4808efd | csv | artifact or editable source
docs/source/procurement-bom.csv | 9084 | 14001550755fd699340186274b4f58c9bad224e5ab04edb69fc62edce9873f5d | csv | artifact or editable source
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
scripts/release_inventory.py | 5266 | d4ceaf9a2cfbf81f03bc87373e021019b373d14a420c756a6f27efb15e636bf4 | py | artifact or editable source
scripts/release_step.py | 15231 | c7fe27a7f2b6084690ac4d136484ef843bfb161d106cf4e261b9d9cbc85a0713 | py | artifact or editable source
