magnus188/trimix-analysator/hardware/system-review/electrical/main-final/fill-cap-process/required-fill-cap-holes.csv

ID | Native_UUID | Reference | Pin | PCB_X_mm | PCB_Y_mm | Bore_mm | Net | Type | Bore_overlap_with_paste_mm2 | Required_process | Native_flag_note
via299 | 4a85dc30-3037-4222-be94-396b63231ef1 | R125 | 1 | 17.95 | 87.925 | 0.25 | USB_OVP_UVLO | routed signal VIPPO | see independent exported CAM audit | nonconductive epoxy resin fill, planarize and copper cap both faces; retain original SMT mask/paste | explicit native filling yes / capping yes; coordinate-bound audit separately checks flags
U101.25@28 | 54bc8f57-5ed8-4529-b1c5-414914b019c1 | U101 | 25 | 11.9 | 82.9 | 0.2 | GND | package thermal hole represented as a plated pad | 0.031102327331544076 | nonconductive epoxy resin fill, planarize and copper cap both faces; ENIG on exposed caps | represented as plated package pad; fill/cap must be specified by this coordinate list, not inferred from routed-via flags
U101.25@29 | e4ecb0fd-46de-43e9-9e0d-9b2b31e3a2e6 | U101 | 25 | 11.9 | 84.0 | 0.2 | GND | package thermal hole represented as a plated pad | 0.0 | nonconductive epoxy resin fill, planarize and copper cap both faces; ENIG on exposed caps | represented as plated package pad; fill/cap must be specified by this coordinate list, not inferred from routed-via flags
U101.25@30 | 391e0442-fb4a-427e-b000-55be960bc76b | U101 | 25 | 11.9 | 85.1 | 0.2 | GND | package thermal hole represented as a plated pad | 0.031102327331544062 | nonconductive epoxy resin fill, planarize and copper cap both faces; ENIG on exposed caps | represented as plated package pad; fill/cap must be specified by this coordinate list, not inferred from routed-via flags
U101.25@31 | dae1696b-bcc5-4b35-b050-705de09a8636 | U101 | 25 | 13.0 | 82.9 | 0.2 | GND | package thermal hole represented as a plated pad | 0.0 | nonconductive epoxy resin fill, planarize and copper cap both faces; ENIG on exposed caps | represented as plated package pad; fill/cap must be specified by this coordinate list, not inferred from routed-via flags
U101.25@32 | f685e1fc-4f48-4058-8428-b30b40526df7 | U101 | 25 | 13.0 | 84.0 | 0.2 | GND | package thermal hole represented as a plated pad | 0.0 | nonconductive epoxy resin fill, planarize and copper cap both faces; ENIG on exposed caps | represented as plated package pad; fill/cap must be specified by this coordinate list, not inferred from routed-via flags
U101.25@35 | 159cd6c8-d9ce-4edc-8fce-219cf1acc933 | U101 | 25 | 13.0 | 85.1 | 0.2 | GND | package thermal hole represented as a plated pad | 0.0 | nonconductive epoxy resin fill, planarize and copper cap both faces; ENIG on exposed caps | represented as plated package pad; fill/cap must be specified by this coordinate list, not inferred from routed-via flags
U101.25@36 | 8f24e3f9-48bd-4221-91d2-a86ae10c441a | U101 | 25 | 14.1 | 82.9 | 0.2 | GND | package thermal hole represented as a plated pad | 0.03110232733154408 | nonconductive epoxy resin fill, planarize and copper cap both faces; ENIG on exposed caps | represented as plated package pad; fill/cap must be specified by this coordinate list, not inferred from routed-via flags
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
