magnus188/trimix-analysator/hardware/cad/rev04/3d-print/printing/bambu-studio/petg/C08_ao2_thread/C08_ao2_thread_petg.3mf

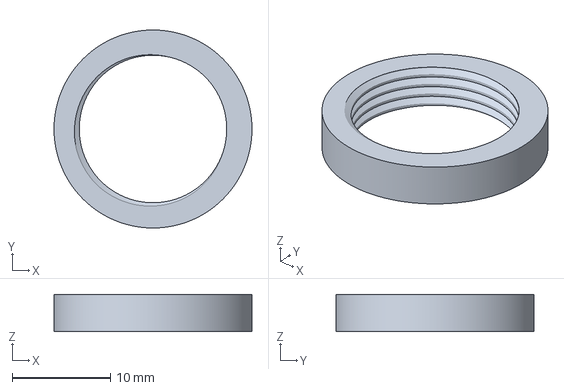
[picture p134: CAD file, 2026-09-07]
hardware/cad/rev04/3d-print/printing/bambu-studio/petg/C08_ao2_thread/C08_ao2_thread_petg.3mf
20.2 x 20.2 x 3.80 mm
