magnus188/trimix-analysator/hardware/cad/rev04/3d-print/printing/bambu-studio/petg/TMX-A3-P01/TMX-A3-P01_petg.3mf

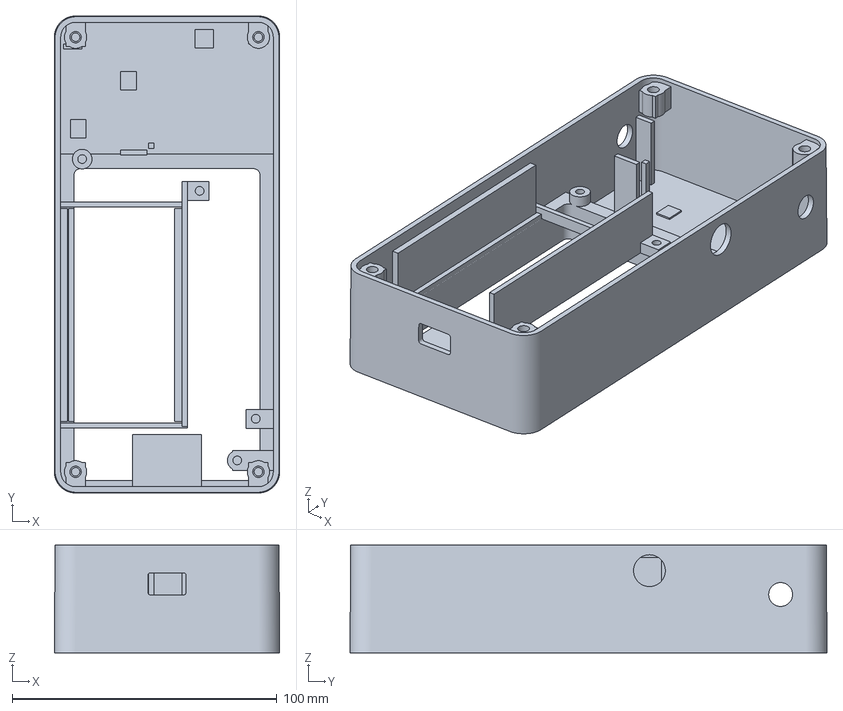
[picture p135: CAD file, 2026-09-07]
hardware/cad/rev04/3d-print/printing/bambu-studio/petg/TMX-A3-P01/TMX-A3-P01_petg.3mf
85.0 x 180.0 x 40.6 mm
