magnus188/trimix-analysator/hardware/cad/rev04/3d-print/printing/bambu-studio/petg/TMX-A3-P02/TMX-A3-P02_petg.3mf

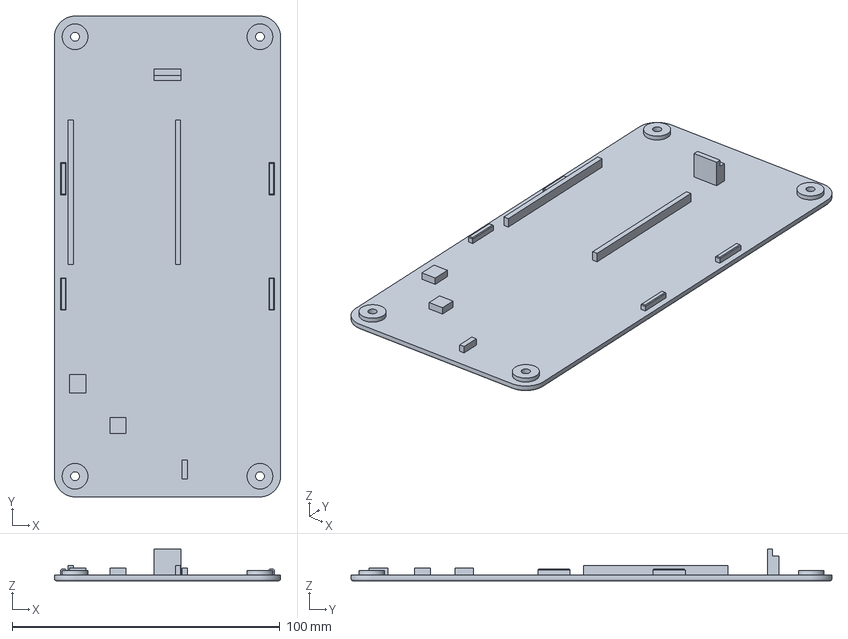
[picture p136: CAD file, 2026-09-07]
hardware/cad/rev04/3d-print/printing/bambu-studio/petg/TMX-A3-P02/TMX-A3-P02_petg.3mf
84.5 x 179.5 x 11.8 mm
