magnus188/trimix-analysator/hardware/cad/rev04/3d-print/printing/bambu-studio/petg/TMX-A3-P03/TMX-A3-P03_petg.3mf

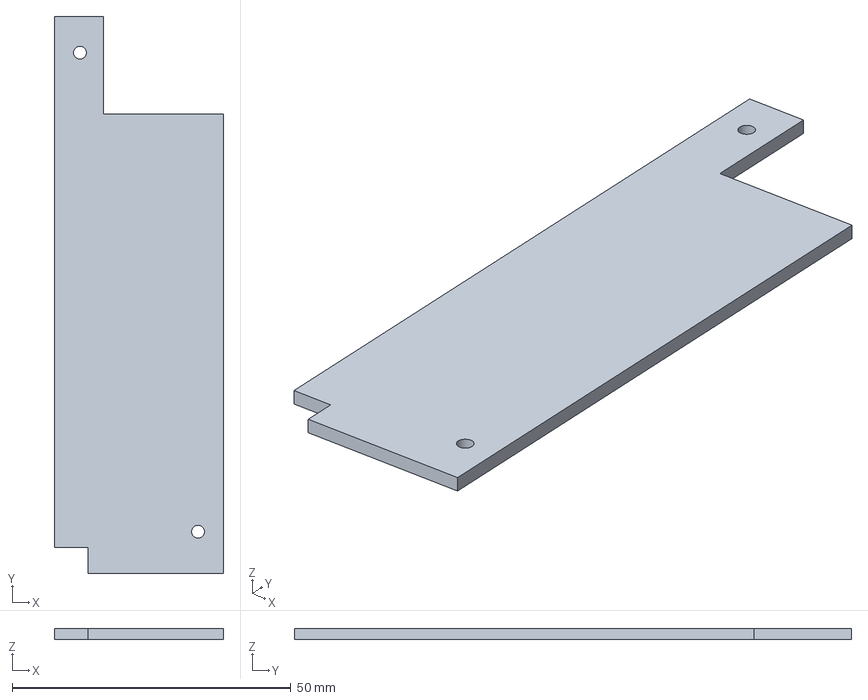
[picture p137: CAD file, 2026-09-07]
hardware/cad/rev04/3d-print/printing/bambu-studio/petg/TMX-A3-P03/TMX-A3-P03_petg.3mf
30.4 x 100.0 x 2.00 mm
