magnus188/trimix-analysator/hardware/cad/rev04/3d-print/printing/bambu-studio/petg/TMX-A3-P04/TMX-A3-P04_petg.3mf

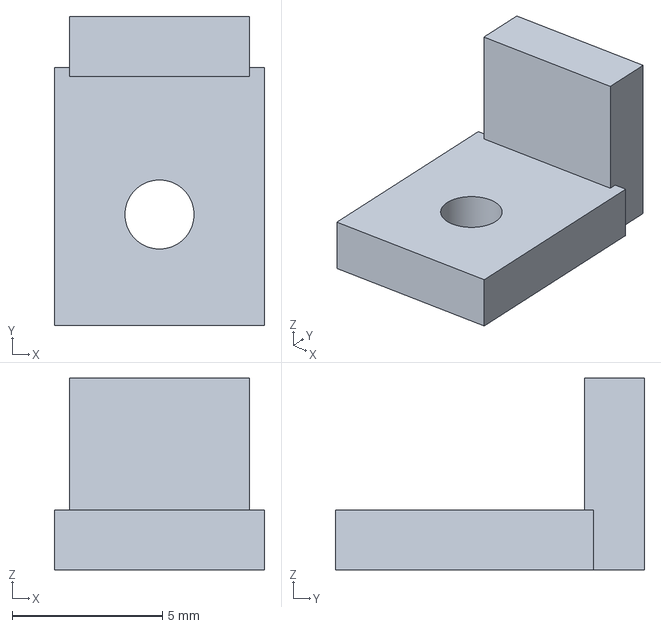
[picture p138: CAD file, 2026-09-07]
hardware/cad/rev04/3d-print/printing/bambu-studio/petg/TMX-A3-P04/TMX-A3-P04_petg.3mf
7.00 x 10.3 x 6.40 mm
