magnus188/trimix-analysator/hardware/cad/rev04/3d-print/printing/bambu-studio/petg/TMX-A3-P05/TMX-A3-P05_petg.3mf

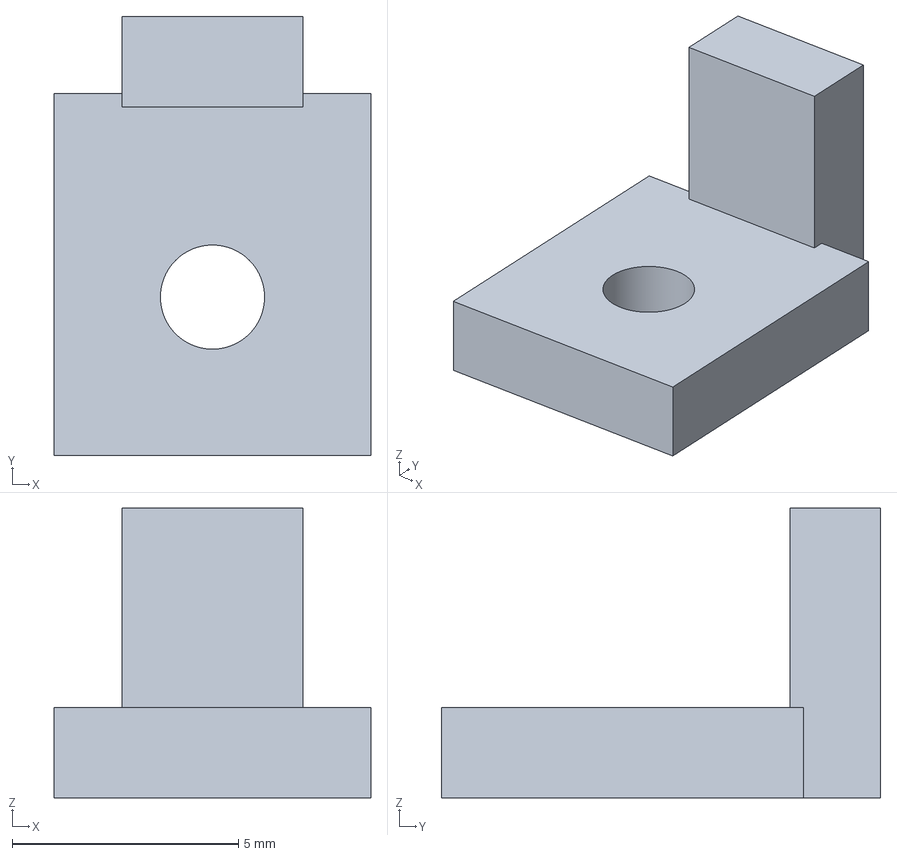
[picture p139: CAD file, 2026-09-07]
hardware/cad/rev04/3d-print/printing/bambu-studio/petg/TMX-A3-P05/TMX-A3-P05_petg.3mf
7.00 x 9.70 x 6.40 mm
