magnus188/trimix-analysator/hardware/cad/rev04/3d-print/printing/bambu-studio/petg/TMX-A3-P07/TMX-A3-P07_petg.3mf

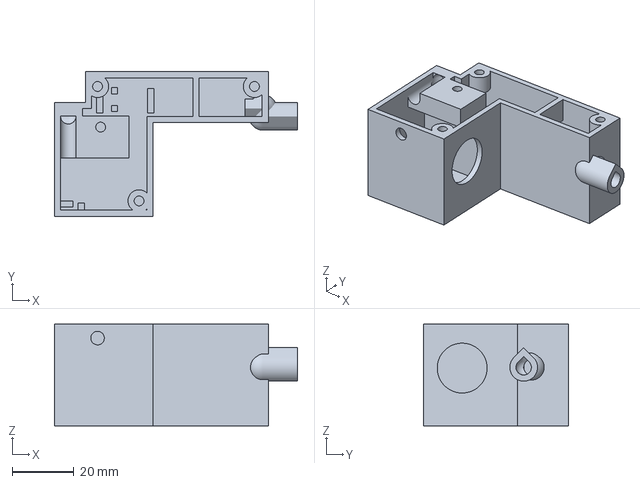
[picture p140: CAD file, 2026-09-07]
hardware/cad/rev04/3d-print/printing/bambu-studio/petg/TMX-A3-P07/TMX-A3-P07_petg.3mf
79.0 x 47.0 x 33.0 mm
