magnus188/trimix-analysator/hardware/cad/rev04/3d-print/printing/bambu-studio/petg/TMX-A3-P08/TMX-A3-P08_petg.3mf

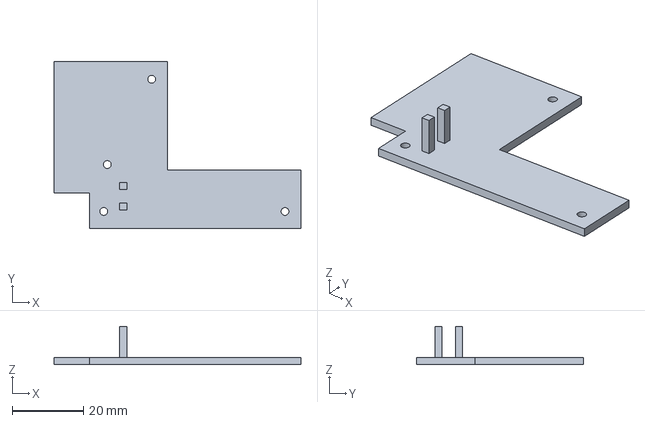
[picture p141: CAD file, 2026-09-07]
hardware/cad/rev04/3d-print/printing/bambu-studio/petg/TMX-A3-P08/TMX-A3-P08_petg.3mf
69.5 x 47.0 x 10.7 mm
