magnus188/trimix-analysator/hardware/cad/rev04/3d-print/printing/bambu-studio/petg/TMX-A3-P10/TMX-A3-P10_petg.3mf

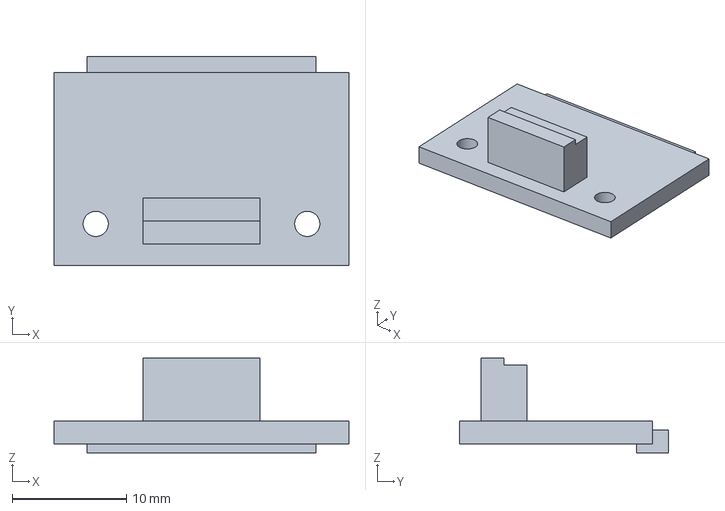
[picture p142: CAD file, 2026-09-07]
hardware/cad/rev04/3d-print/printing/bambu-studio/petg/TMX-A3-P10/TMX-A3-P10_petg.3mf
25.8 x 18.3 x 8.30 mm
