magnus188/trimix-analysator/hardware/cad/rev04/3d-print/printing/diagnostics/projects/petg/pipeline_cube/pipeline_cube_petg.3mf

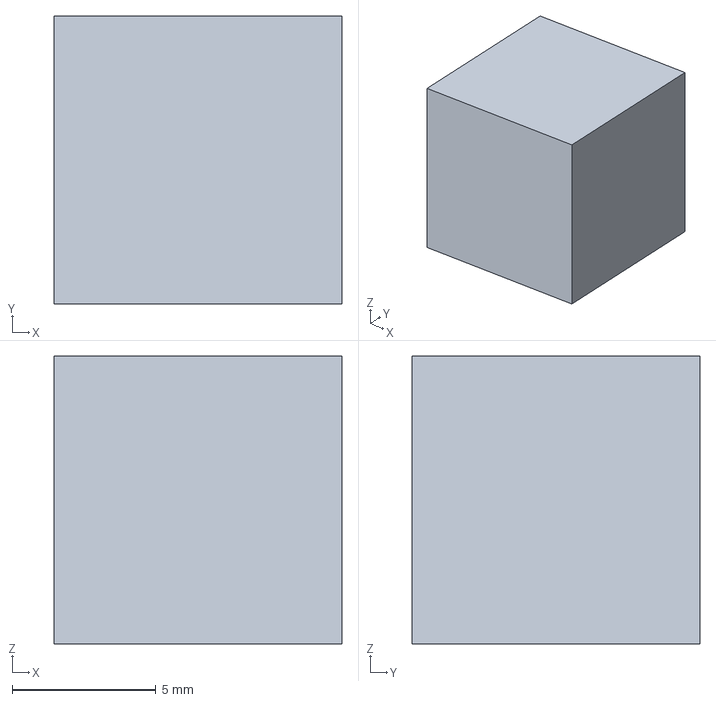
[picture p143: CAD file, 2026-09-07]
hardware/cad/rev04/3d-print/printing/diagnostics/projects/petg/pipeline_cube/pipeline_cube_petg.3mf
10.0 x 10.0 x 10.0 mm
