magnus188/trimix-analysator/hardware/cad/rev04/3d-print/printing/diagnostics/projects/pla/pipeline_blocker/pipeline_blocker_pla.3mf

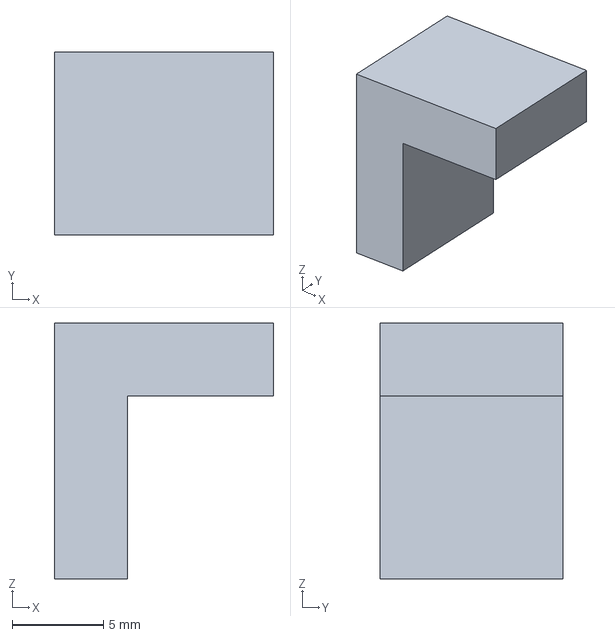
[picture p144: CAD file, 2026-09-07]
hardware/cad/rev04/3d-print/printing/diagnostics/projects/pla/pipeline_blocker/pipeline_blocker_pla.3mf
12.0 x 10.0 x 14.0 mm
