magnus188/trimix-analysator/hardware/cad/rev04/3d-print/Trimix_Enclosure_A3_PrintReview.step

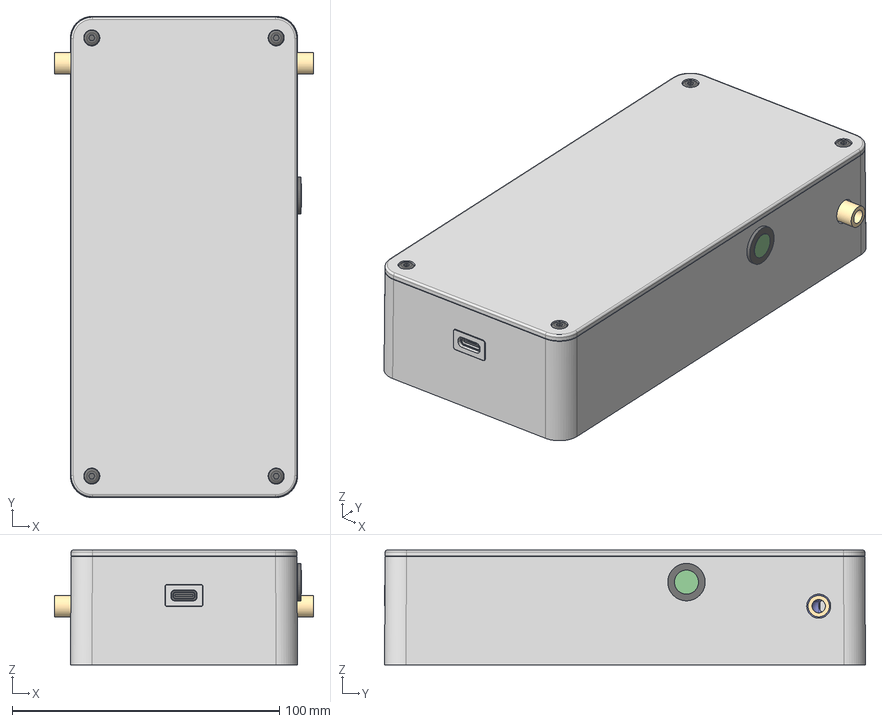
[picture p145: CAD file, 2026-09-07]
hardware/cad/rev04/3d-print/Trimix_Enclosure_A3_PrintReview.step
97.0 x 180.0 x 43.0 mm
TMX-A3-P01
TMX-A3-P02
TMX-A3-F01 x 4
TMX-A3-F04 x 4
TMX-A3-P03
TMX-A3-B01
TMX-A3-F03 x 2
TMX-A3-F05 x 10
TMX-A3-P04
TMX-A3-P05
TMX-A3-F02 x 8
TMX-A3-C02
TMX-A3-C03-V01
TMX-A3-C03-V02
TMX-A3-C10-V01
TMX-A3-C10-V02
TMX-A3-P09
TMX-A3-P06
TMX-A3-P10
TMX-A3-B02
TMX-A3-P07
TMX-A3-P08
TMX-A3-P11
TMX-A3-C06
TMX-A3-C12
TMX-A3-C09
TMX-A3-C07
TMX-A3-C08
TMX-A3-C11-V01
TMX-A3-C11-V02
TMX-A3-S02
TMX-A3-S01
TMX-A3-C01-V01
TMX-A3-C01-V02
TMX-A3-C01-V03
TMX-A3-C01-V04
TMX-A3-C04-V01
TMX-A3-C04-V02
TMX-A3-C04-V03
TMX-A3-C05-V01
TMX-A3-C05-V02
TMX-A3-C05-V03
TMX-A3-C05-V04
