magnus188/trimix-analysator/hardware/cad/Trimix_Enclosure_A1.step

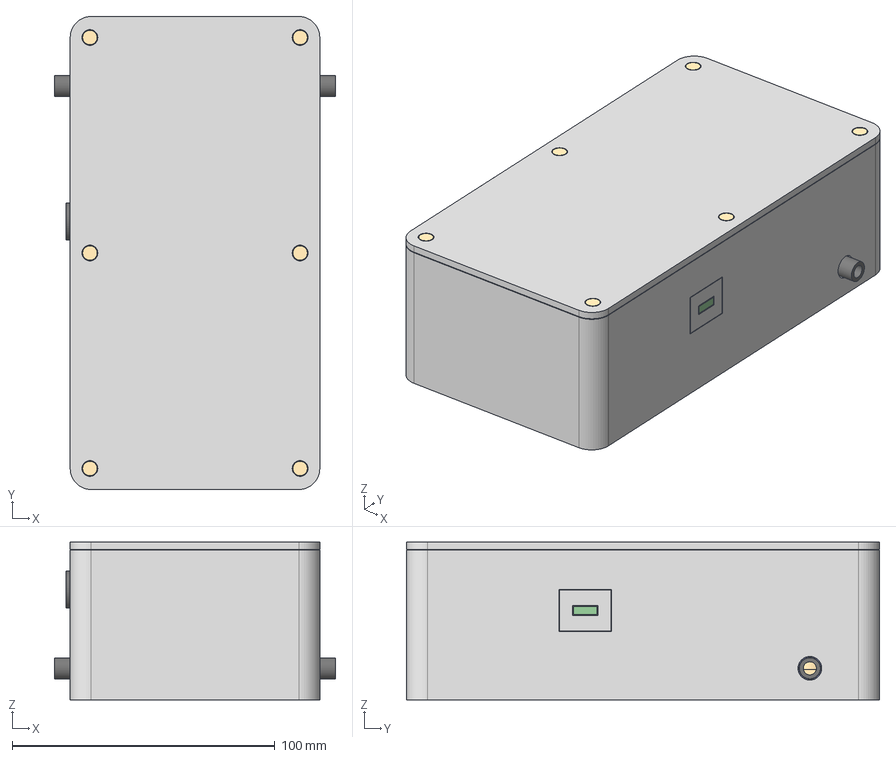
[picture p146: CAD file, 2026-09-07]
hardware/cad/Trimix_Enclosure_A1.step
107.0 x 180.0 x 60.0 mm
01 Main housing
02 Single rear cover
03 Removable sampling chamber
04 Internal chamber lid
05 Feedthrough seal envelope TBD
06 Gas fitting envelopes TBD
07 Guition 4.3in envelope — depth TBD
08 Active display reference
09 Removable electronics carrier
10 Future PCB and component envelope TBD
11 Protected FMA holder envelope TBD
12 Two 18650 cell envelopes
13 Battery plug and cable clearance TBD
14 Supported USB-C mounting insert TBD
15 USB daughterboard envelope 0.60mm
16 Right momentary button envelope TBD
18 Wiring route clearance envelopes
17 Chamber sensor envelopes TBD
19 Rear M3 fastener envelopes TBD
