magnus188/trimix-analysator/hardware/system-review/electrical/routing-candidate/final-cleanup/frozen-bundle/hardware/system-review/mechanical/components/Samtec_HTSW_113_07_L_D_007_Drawing_Reconstruction.step

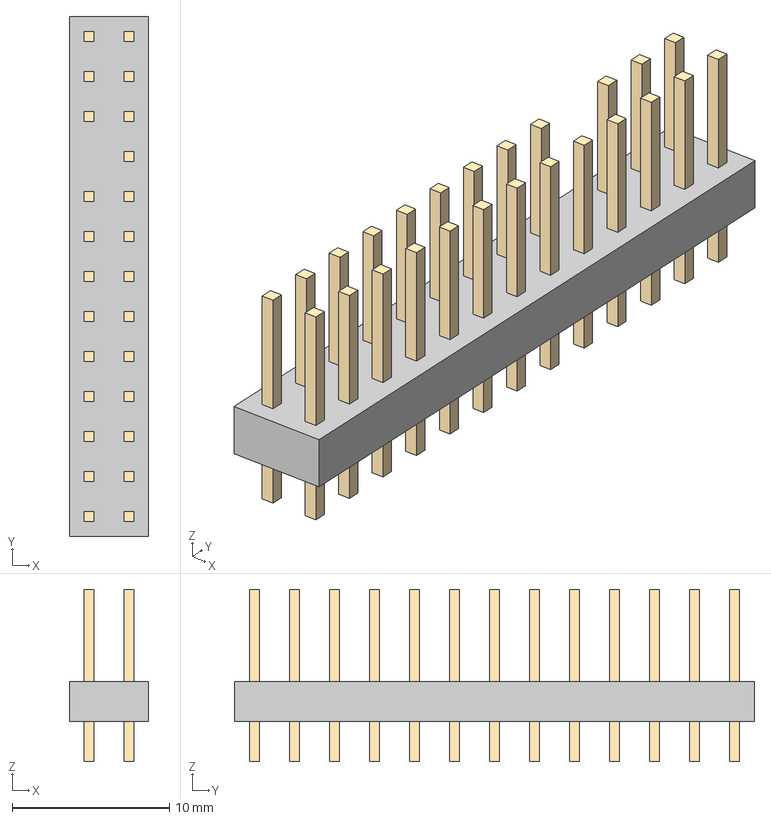
[picture p147: CAD file, 2026-09-09]
hardware/system-review/electrical/routing-candidate/final-cleanup/frozen-bundle/hardware/system-review/mechanical/components/Samtec_HTSW_113_07_L_D_007_Drawing_Reconstruction.step
5.03 x 33.0 x 10.9 mm
