magnus188/trimix-analysator/hardware/system-review/electrical/routing-candidate/sensitive-layout-refinement/frozen-local-bundle/hardware/system-review/mechanical/components/Amphenol_RF_142138_Drawing_Reconstruction.step

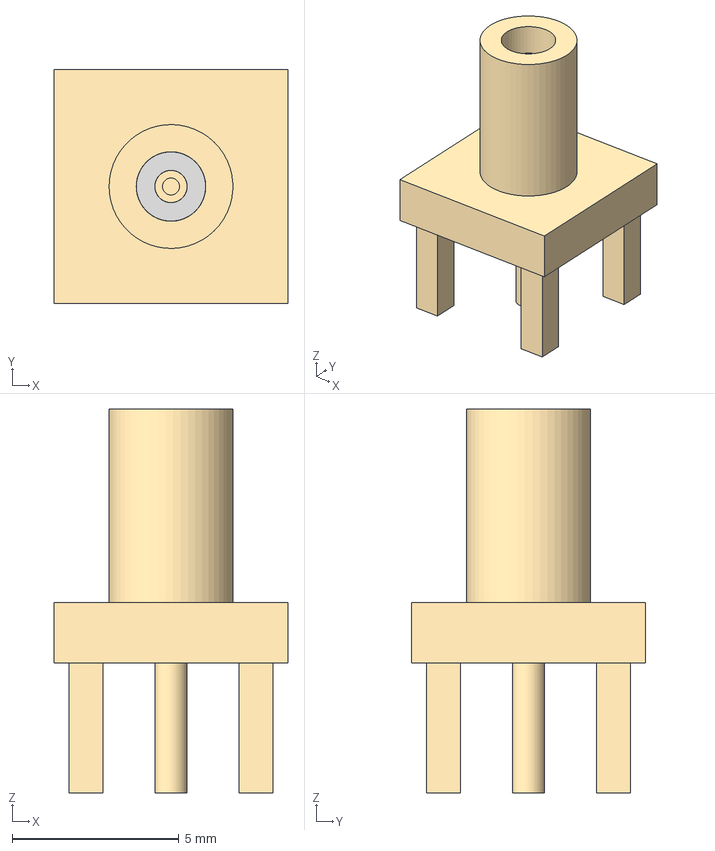
[picture p148: CAD file, 2026-09-09]
hardware/system-review/electrical/routing-candidate/sensitive-layout-refinement/frozen-local-bundle/hardware/system-review/mechanical/components/Amphenol_RF_142138_Drawing_Reconstruction.step
7.00 x 7.00 x 11.5 mm
