magnus188/trimix-analysator/hardware/system-review/electrical/usb-final/Trimix_USB_Input.step

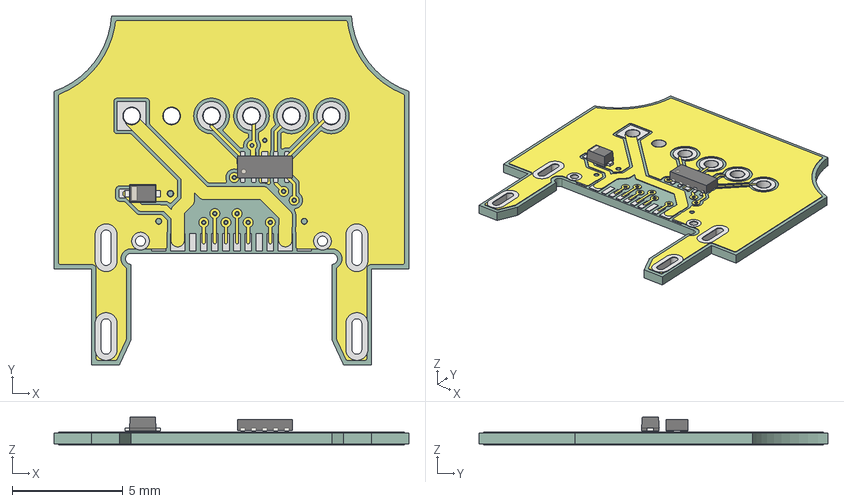
[picture p149: CAD file, 2026-09-09]
hardware/system-review/electrical/usb-final/Trimix_USB_Input.step
16.0 x 15.7 x 1.26 mm
D_SOD_523
USON_10_25x10mm_Pitch05mm
Trimix_USB_Input_copper
Trimix_USB_Input_pad
Trimix_USB_Input_via
Trimix_USB_Input_PCB
