magnus188/trimix-analysator/hardware/system-review/mechanical/components/cnckitchen-m2-review/TC-M2x3.0_manufacturer.step

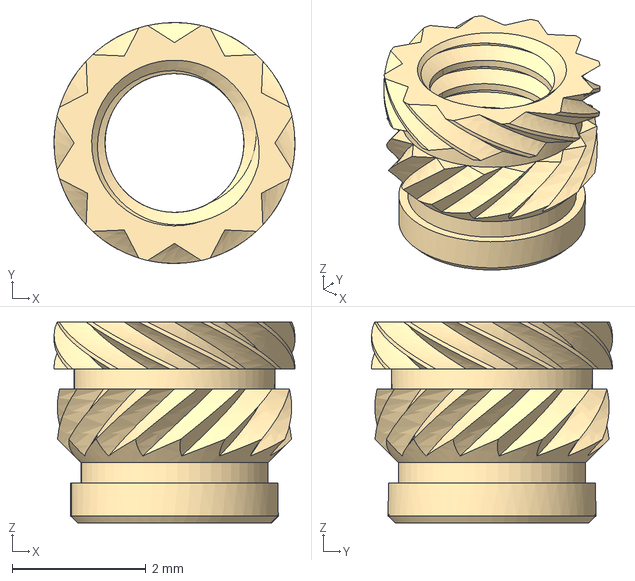
[picture p150: CAD file, 2026-09-09]
hardware/system-review/mechanical/components/cnckitchen-m2-review/TC-M2x3.0_manufacturer.step
3.60 x 3.60 x 3.00 mm
