magnus188/trimix-analysator/hardware/system-review/mechanical/components/ruthex-review/ruthex_RX-M2x4.step

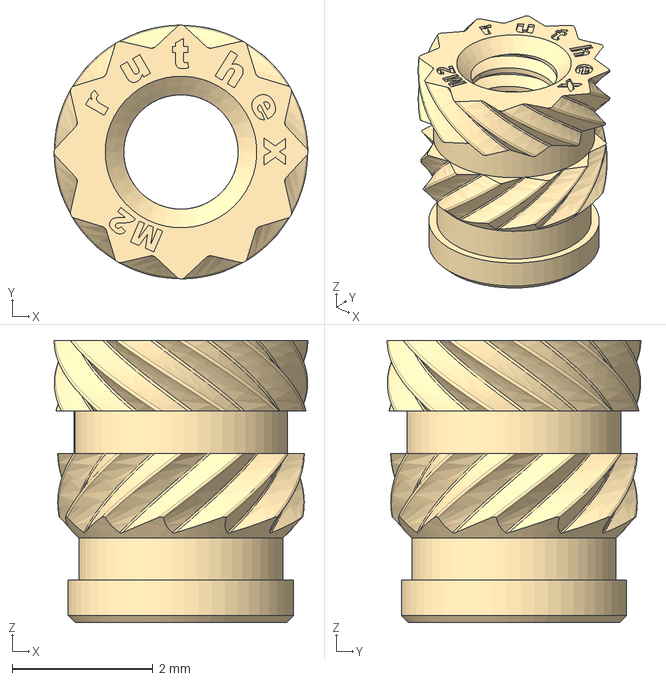
[picture p151: CAD file, 2026-09-09]
hardware/system-review/mechanical/components/ruthex-review/ruthex_RX-M2x4.step
3.60 x 3.60 x 4.00 mm
