magnus188/trimix-analysator/hardware/system-review/mechanical/diagnostic-printing/backside-allocation/oriented-stl/TMX-A3-P03_rear_down.stl

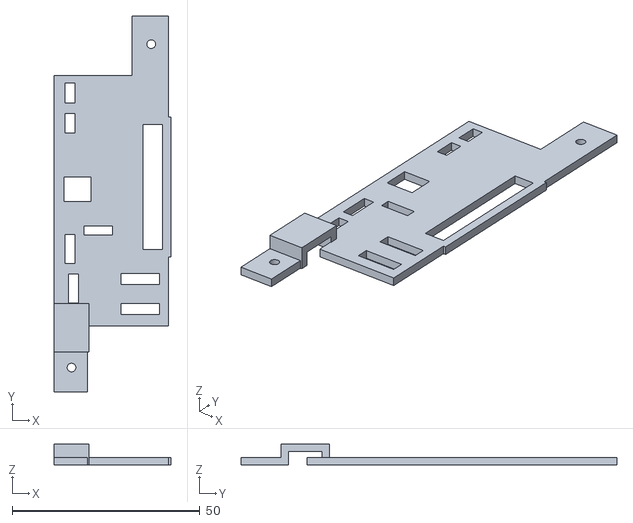
[picture p152: CAD file, 2026-09-09]
hardware/system-review/mechanical/diagnostic-printing/backside-allocation/oriented-stl/TMX-A3-P03_rear_down.stl
31.0 x 100.0 x 5.50
