magnus188/trimix-analysator/hardware/system-review/mechanical/diagnostic-printing/projects/petg/TMX-A3-P03_systemreview_diagnostic/TMX-A3-P03_systemreview_diagnostic_petg.3mf

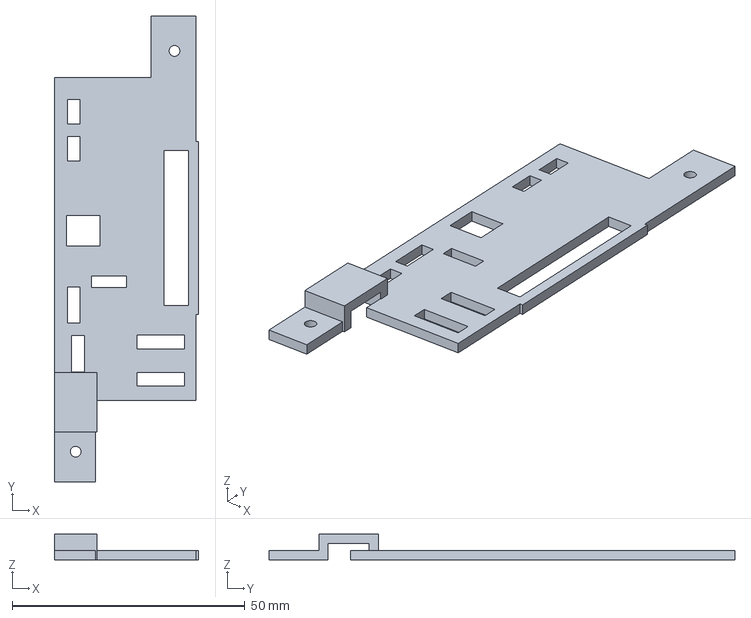
[picture p153: CAD file, 2026-09-09]
hardware/system-review/mechanical/diagnostic-printing/projects/petg/TMX-A3-P03_systemreview_diagnostic/TMX-A3-P03_systemreview_diagnostic_petg.3mf
31.0 x 100.0 x 5.50 mm
