magnus188/trimix-analysator/hardware/system-review/mechanical/diagnostic-printing/projects/petg/TMX-A3-P10_systemreview_diagnostic/TMX-A3-P10_systemreview_diagnostic_petg.3mf

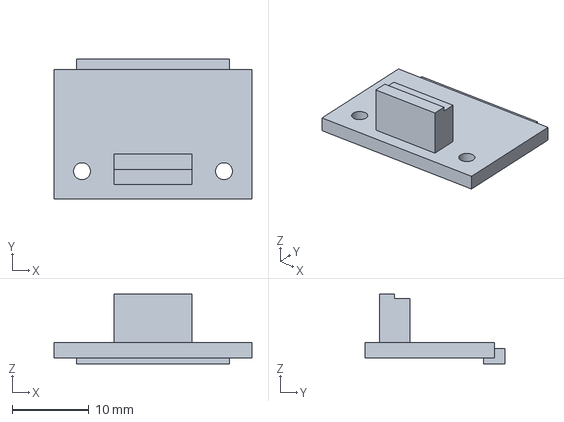
[picture p154: CAD file, 2026-09-09]
hardware/system-review/mechanical/diagnostic-printing/projects/petg/TMX-A3-P10_systemreview_diagnostic/TMX-A3-P10_systemreview_diagnostic_petg.3mf
25.8 x 18.3 x 9.10 mm
