magnus188/trimix-analysator/hardware/system-review/mechanical/diagnostic-printing/source-stl/TMX-A3-P06.stl

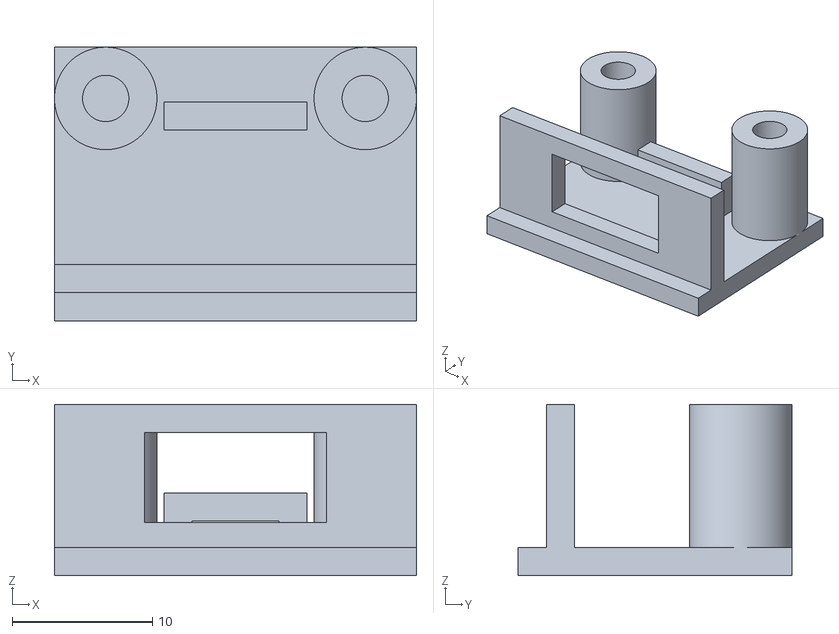
[picture p155: CAD file, 2026-09-09]
hardware/system-review/mechanical/diagnostic-printing/source-stl/TMX-A3-P06.stl
25.8 x 19.5 x 12.2
