magnus188/trimix-analysator/hardware/pcb/integration/exports/Trimix_Enclosure_A3_PCBFit.step

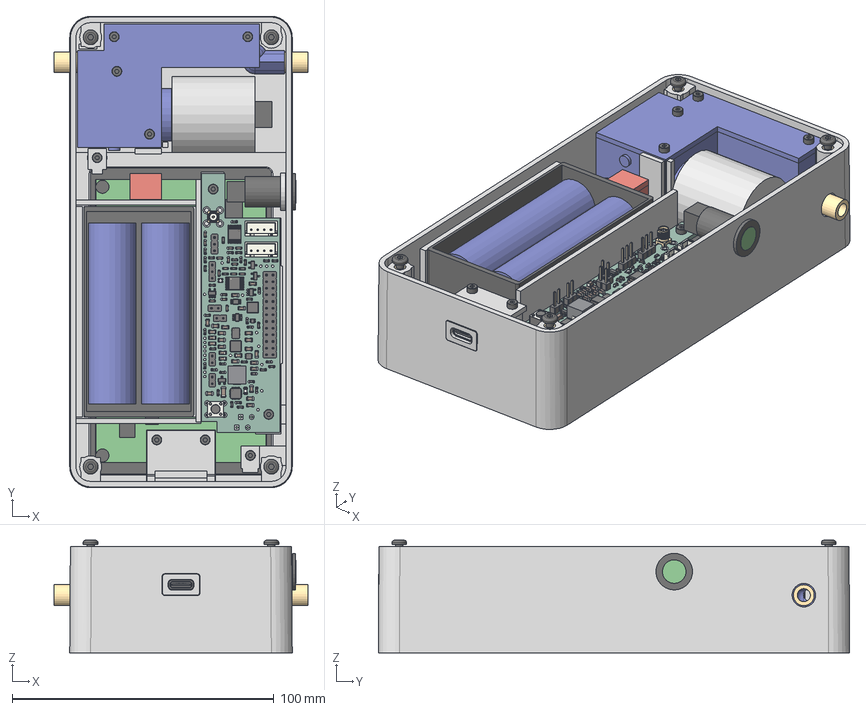
[picture p156: CAD file, 2026-09-09]
hardware/pcb/integration/exports/Trimix_Enclosure_A3_PCBFit.step
97.0 x 180.0 x 43.0 mm
TMX-A3-P01
TMX-A3-F01 x 4
TMX-A3-F04 x 4
TMX-A3-P03
TMX-A3-F03 x 2
TMX-A3-F05 x 10
TMX-A3-P04
TMX-A3-P05
TMX-A3-F02 x 8
TMX-A3-C02
TMX-A3-C03-V01
TMX-A3-C03-V02
TMX-A3-C10-V01
TMX-A3-C10-V02
TMX-A3-P09
TMX-A3-P06
TMX-A3-P10
TMX-A3-P07
TMX-A3-P08
TMX-A3-P11
TMX-A3-C06
TMX-A3-C12
TMX-A3-C09
TMX-A3-C07
TMX-A3-C08
TMX-A3-C11-V01
TMX-A3-C11-V02
TMX-A3-S02
TMX-A3-S01
TMX-A3-C01-V01
TMX-A3-C01-V02
TMX-A3-C01-V03
TMX-A3-C01-V04
TMX-A3-C04-V01
TMX-A3-C04-V02
TMX-A3-C04-V03
TMX-A3-C05-V01
TMX-A3-C05-V02
TMX-A3-C05-V03
TMX-A3-C05-V04
R_0603_1608Metric_1 x 2
Trimix_USB_Input_pad
Trimix_USB_Input_PCB
C_0603_1608Metric_1 x 18
C_0805_2012Metric_1 x 26
R_0603_1608Metric_3 x 37
PinHeader_1x03_P254mm_Vertical x 2
JST_B4B_XH_A x 2
SW_PUSH_6mm_1
SOT-23_1 x 3
SOT-23-5_1 x 2
L_Wuerth_HCM-7050_1
LED_0805_2012Metric_1
PinHeader_1x02_P254mm_Vertical x 4
SMA_Amphenol_132134-10_Vertical_1
(Unsaved)
SOT_563
L_Coilcraft_XAL4020-XXX_1 x 2
VSSOP-8_2.3x2mm_P0.5mm_1
TSOT-23-8_1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
