magnus188/trimix-analysator/hardware/system-review/mechanical/components/Amphenol_RF_142138_Nominal_Upper_Envelope.step

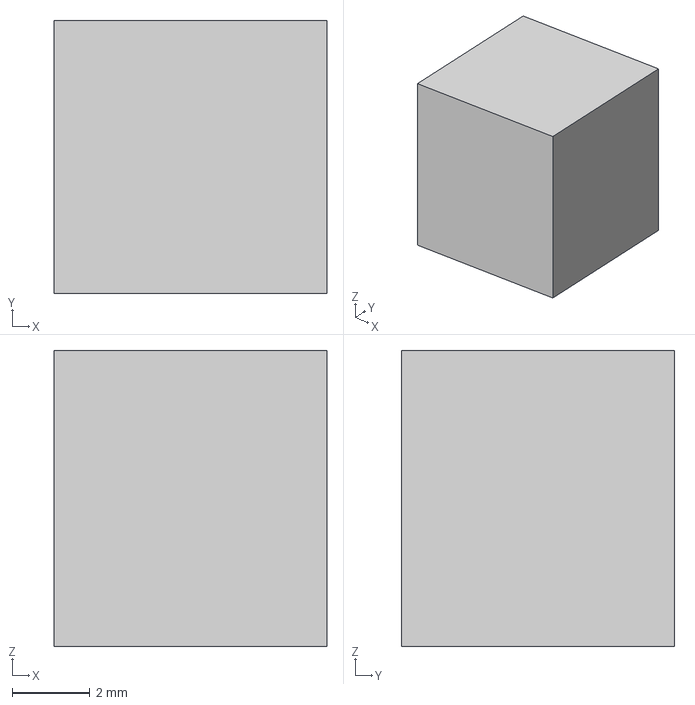
[picture p157: CAD file, 2026-09-09]
hardware/system-review/mechanical/components/Amphenol_RF_142138_Nominal_Upper_Envelope.step
7.00 x 7.00 x 7.60 mm
