magnus188/trimix-analysator/hardware/pcb/integration/exports/Trimix_USB_Input.step

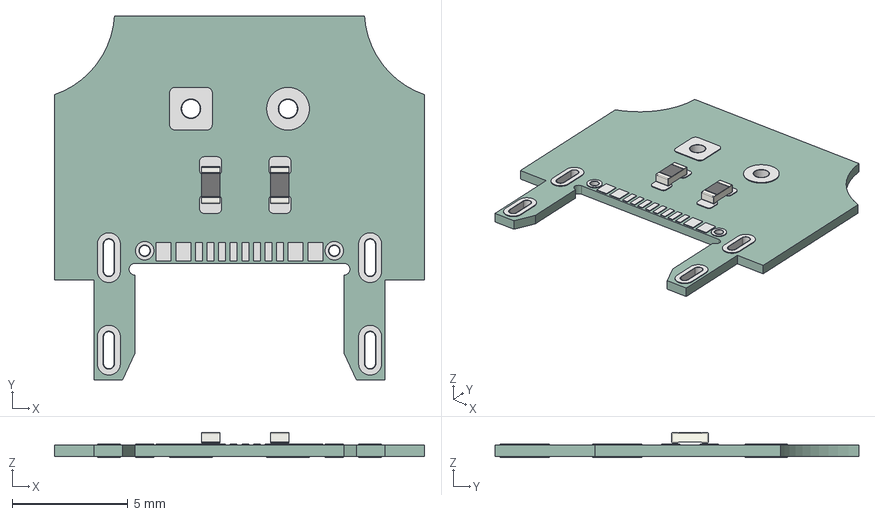
[picture p158: CAD file, 2026-09-07]
hardware/pcb/integration/exports/Trimix_USB_Input.step
16.0 x 15.7 x 1.08 mm
R_0603_1608Metric x 2
Trimix_USB_Input_pad
Trimix_USB_Input_PCB
