magnus188/trimix-analysator/hardware/cad/rev04/3d-print/docs/FIT_CHECKLIST.md

# A3 enclosure fit record

Release / native design revision:

Builder / date:

Printer / nozzle / filament / profile:

Use an unpowered assembly for the first fit. Record actual values rather than a
pass alone. Leave untested items pending. Photograph interference before
changing a printed part, and identify it using its TMX-A3 part ID.

Use the PLA project for dimensional fit and the PETG project for the target
material trial. Select the actual insert SKU and qualify its coupon before
heat installation in full parts. Current M2 holes around 3.2/3.3 mm and M3
holes around 4.3 mm are clearance references. Record the qualified hole size
and update the part before installing the inserts.

| Check | Actual value or observation | Status |
| --- | --- | --- |
| Print scale, main dimensions and warping | | Pending |
| P01/P02 rear locating interface and screw alignment | | Pending |
| C01 actual factory-cased display and frame lip | | Pending |
| P04/P05 frame contact, glass clearance and movement | | Pending |
| Display removal forward after retainer release | | Pending |
| C02 occupied holder, protection PCB and wire exit | | Pending |
| C03 exact cell model, dimensions and manufacturer limits | | Pending |
| C10 battery connector mate and accessible release | | Pending |
| P03 carrier and actual/dummy PCB with both notches | | Pending |
| C04 button barrel, nut and terminals | | Pending |
| C05/P06/P09/P10 USB fit, plug overmould and load path | | Pending |
| USB cartridge inward 2.5 mm, then rearward removal | | Pending |
| Selected F01-F05 SKUs, insert coupon retention and qualified hole size | | Pending |
| Full-part pilot update before heat installation and engagement test | | Pending |
| Actual sensor faces, leads, connectors and support areas | | Pending |
| P11 actual AO2 thread, stop and sealing datum | | Pending |
| P07/P08 land flatness and divider sealing | | Pending |
| Harness closure, insulation, routing and strain relief | | Pending |
| Both gas fittings, tubing and disconnection method | | Pending |
| Cover closes without moving parts or trapping wires | | Pending |
| Closed cartridge withdraws with fittings/harness free | | Pending |
| Sensor and cartridge installation on the bench | | Pending |

Keep the following physical qualification records separate from dimensional fit:

| Qualification | Method, conditions and result | Status |
| --- | --- | --- |
| Seal material, compression and leak test | | Pending |
| Gas flow, sample renewal, pressure and thermal response | | Pending |
| Final service material and environmental exposure | | Pending |
| Electrical layout and manufacturing checks | | Pending |
| USB attachment, charging, temperature and power isolation | | Pending |
| Real firmware, fault handling and calibration | | Pending |

For a useful change proposal, include the measured issue, affected part ID,
photographs, printer settings, proposed dimension change and its retest result.
