magnus188/trimix-analysator/hardware/system-review/electrical/vippo-process-review/native-v3-independent/baseline/NOT_FOR_FABRICATION.txt

Independent process counterexample or diagnostic. Never fabricate.
