magnus188/trimix-analysator/hardware/cad/previews/assembled.png

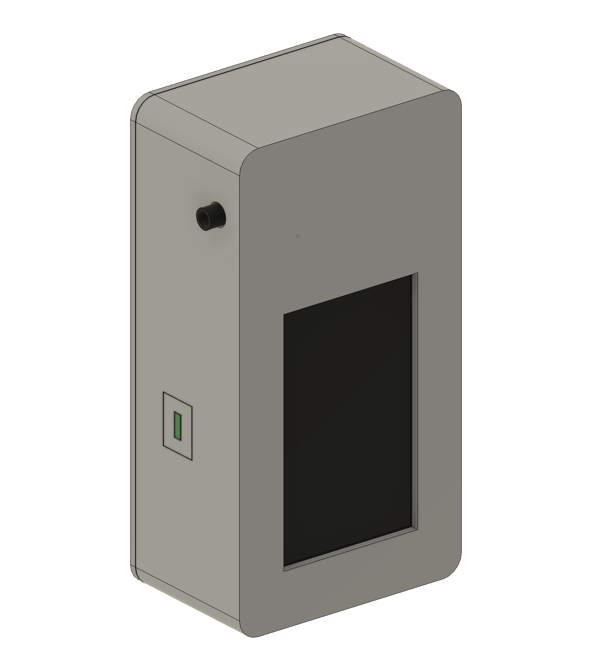
hardware/cad/previews/assembled.png
