magnus188/trimix-analysator/hardware/cad/rev04/3d-print/previews/button_carrier.png

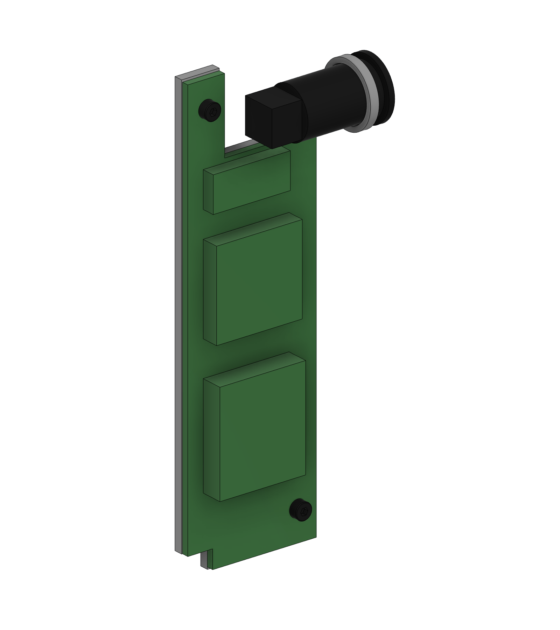
hardware/cad/rev04/3d-print/previews/button_carrier.png
