magnus188/trimix-analysator/hardware/cad/rev04/3d-print/previews/chamber_open_rear.png

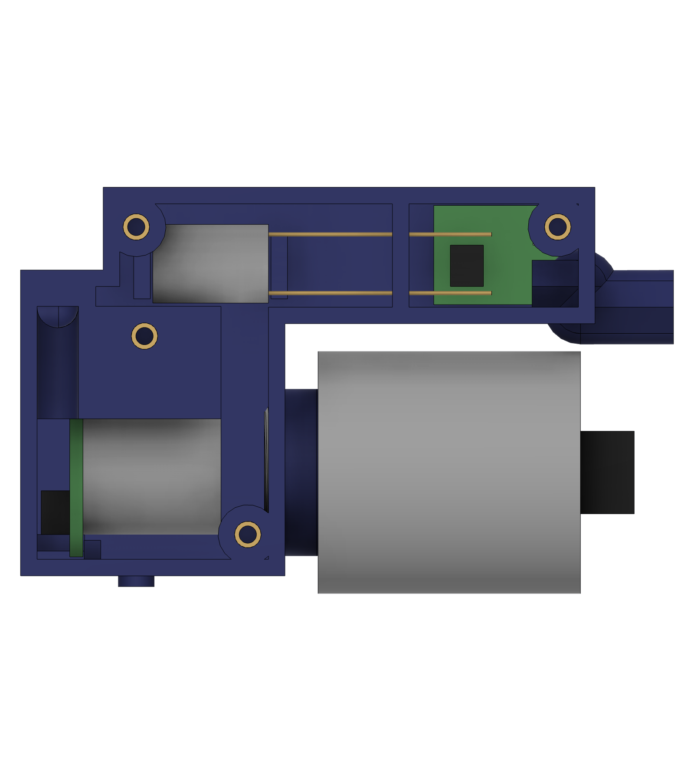
hardware/cad/rev04/3d-print/previews/chamber_open_rear.png
