magnus188/trimix-analysator/hardware/cad/rev04/3d-print/previews/cover_leadins.png

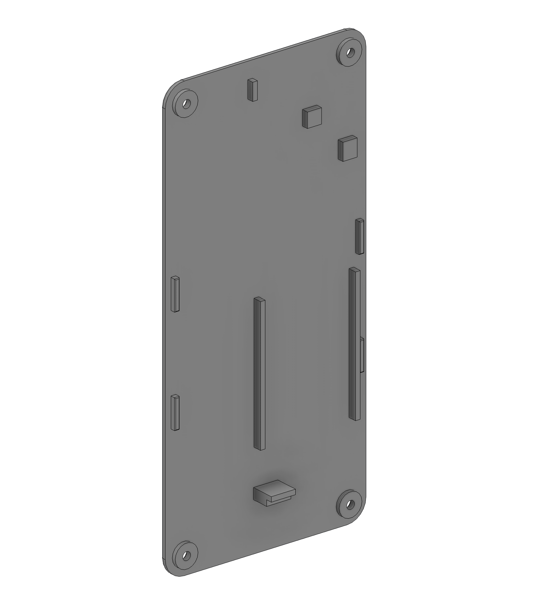
hardware/cad/rev04/3d-print/previews/cover_leadins.png
