magnus188/trimix-analysator/hardware/cad/rev04/3d-print/previews/display_install.png

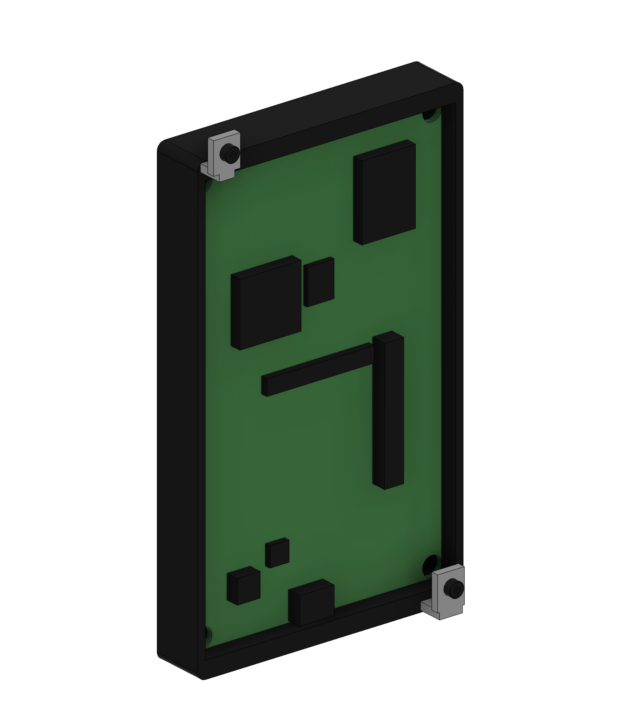
hardware/cad/rev04/3d-print/previews/display_install.png
