magnus188/trimix-analysator/hardware/cad/rev04/3d-print/previews/lid_adapter.png

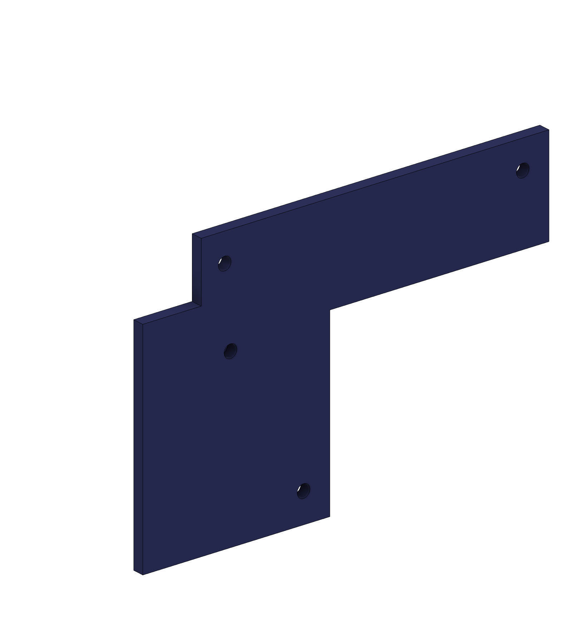
hardware/cad/rev04/3d-print/previews/lid_adapter.png
