magnus188/trimix-analysator/hardware/cad/rev04/3d-print/previews/rear_cable_space.png

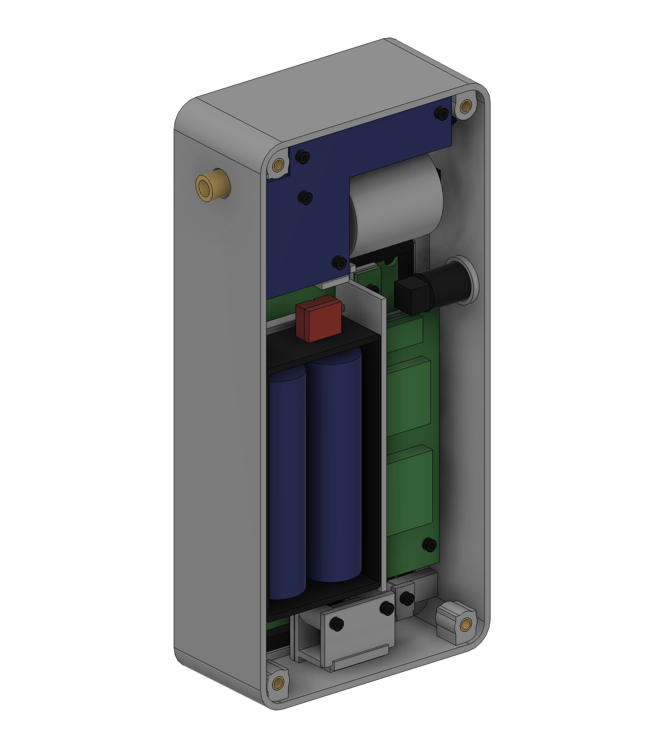
hardware/cad/rev04/3d-print/previews/rear_cable_space.png
