magnus188/trimix-analysator/hardware/cad/rev04/3d-print/previews/sensor_layout.png

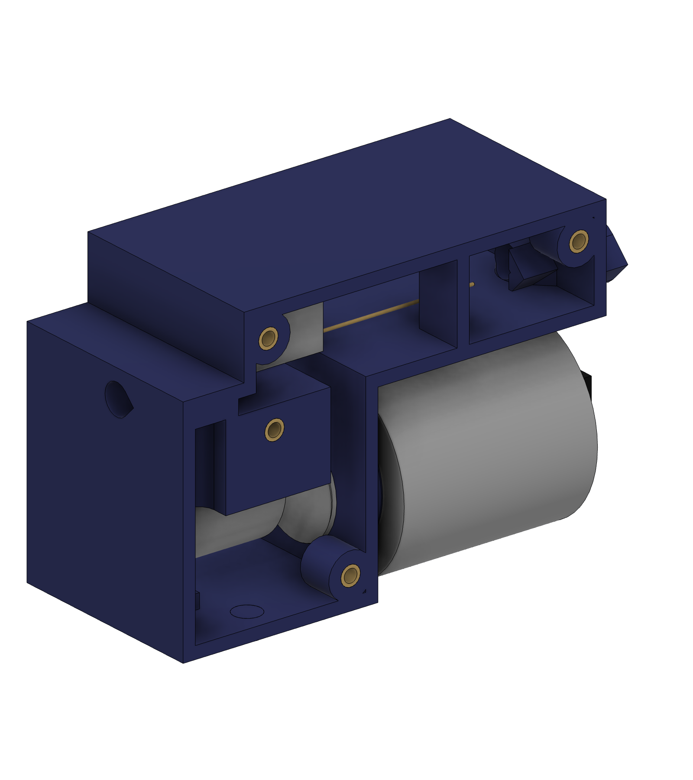
hardware/cad/rev04/3d-print/previews/sensor_layout.png
