magnus188/trimix-analysator/hardware/cad/rev04/3d-print/previews/sensors_only.png

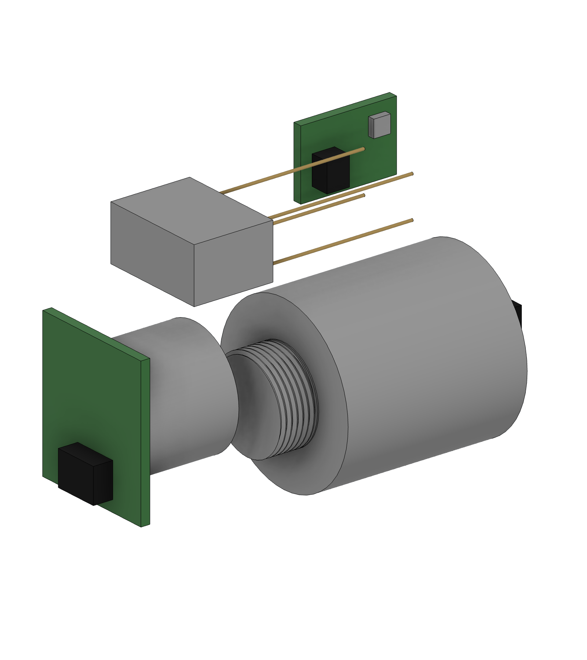
hardware/cad/rev04/3d-print/previews/sensors_only.png
