magnus188/trimix-analysator/hardware/cad/rev04/3d-print/previews/TMX-A3-P09.png

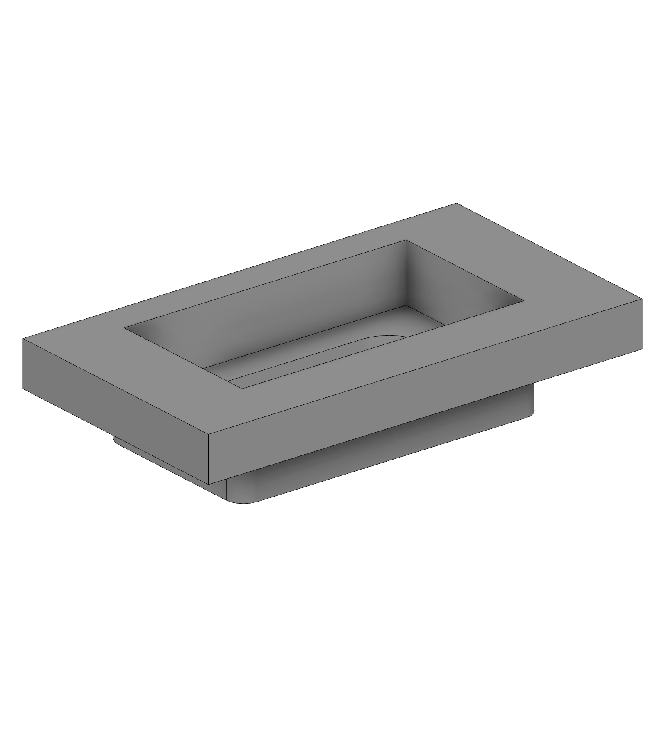
hardware/cad/rev04/3d-print/previews/TMX-A3-P09.png
