magnus188/trimix-analysator/hardware/cad/rev04/3d-print/previews/usb_cartridge.png

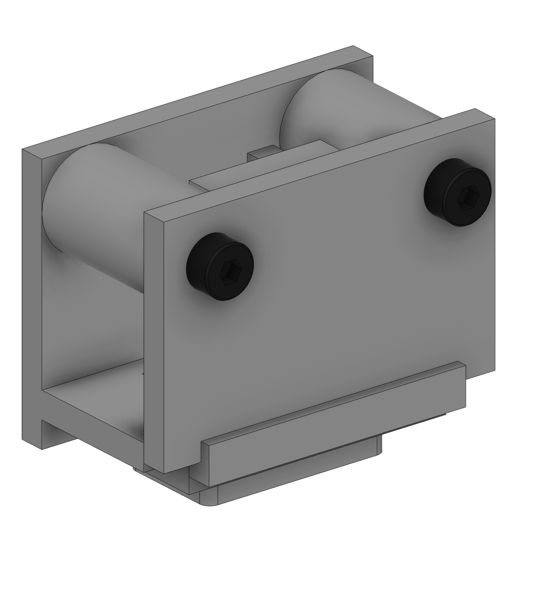
hardware/cad/rev04/3d-print/previews/usb_cartridge.png
