magnus188/trimix-analysator/hardware/cad/rev04/3d-print/printing/bambu-studio/petg/C01_gas_inlet/inspection/layers.png

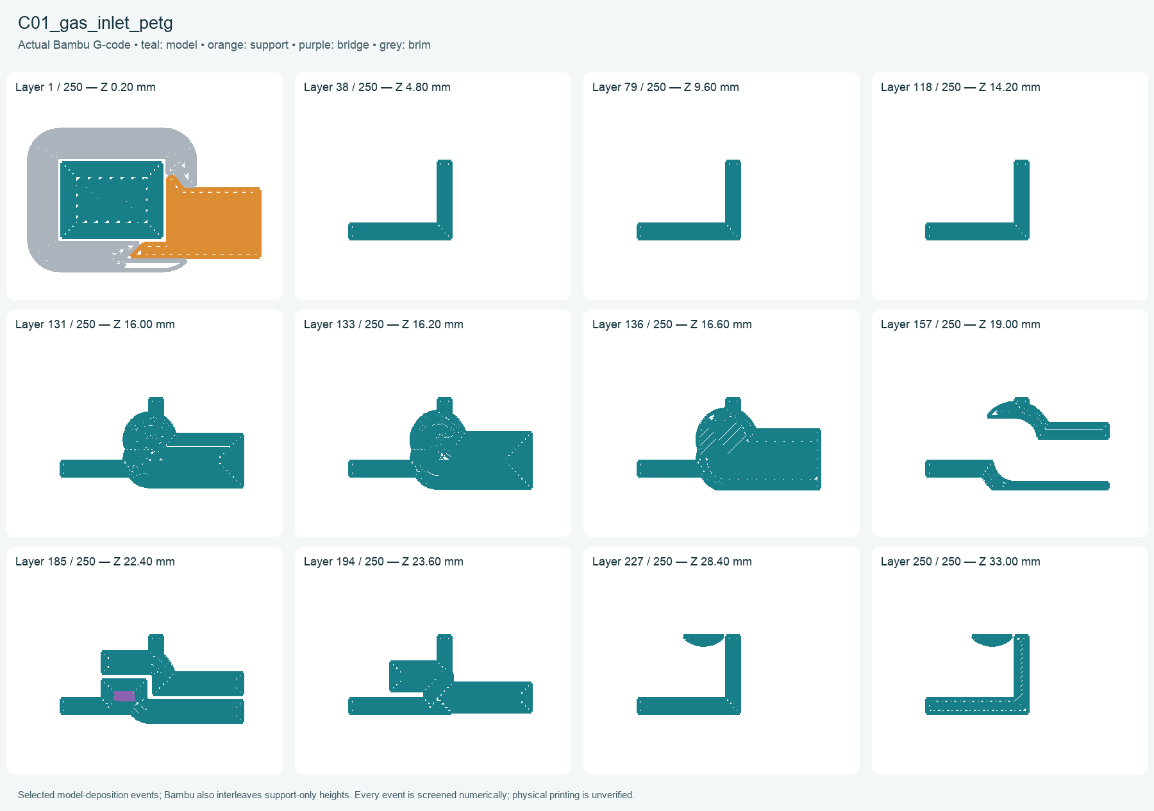
hardware/cad/rev04/3d-print/printing/bambu-studio/petg/C01_gas_inlet/inspection/layers.png
