magnus188/trimix-analysator/hardware/cad/rev04/3d-print/printing/bambu-studio/petg/C02_gas_return/inspection/top_1.png

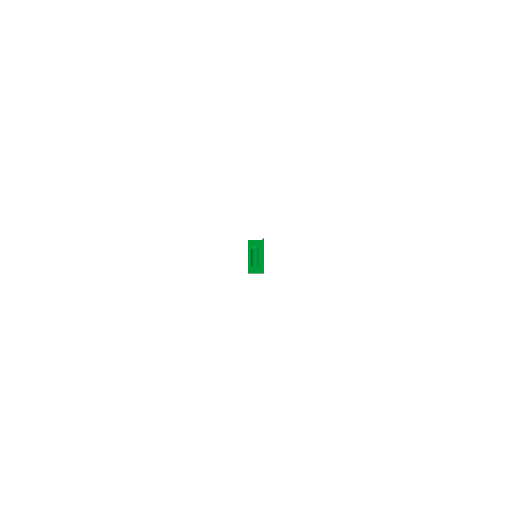
hardware/cad/rev04/3d-print/printing/bambu-studio/petg/C02_gas_return/inspection/top_1.png
