magnus188/trimix-analysator/hardware/cad/rev04/3d-print/printing/bambu-studio/petg/C03_m3_boss/inspection/layers.png

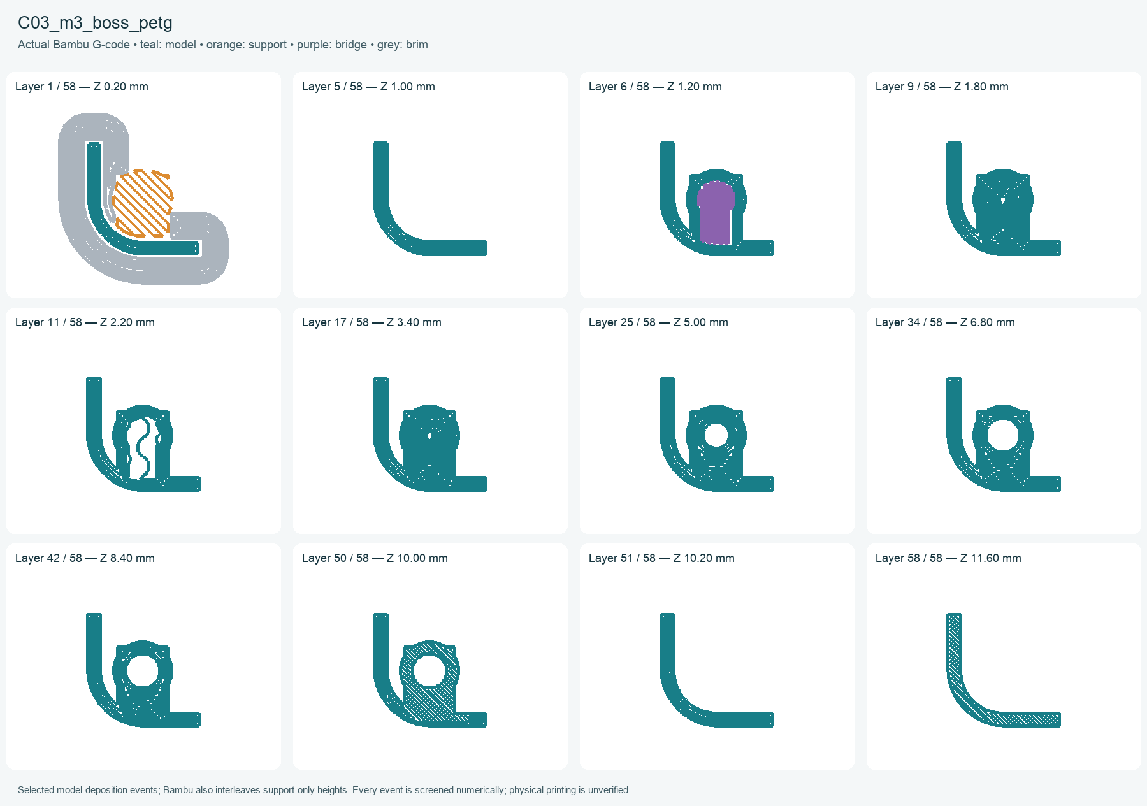
hardware/cad/rev04/3d-print/printing/bambu-studio/petg/C03_m3_boss/inspection/layers.png
