magnus188/trimix-analysator/hardware/cad/rev04/3d-print/printing/bambu-studio/petg/C04_holder_rail/inspection/plate_1.png

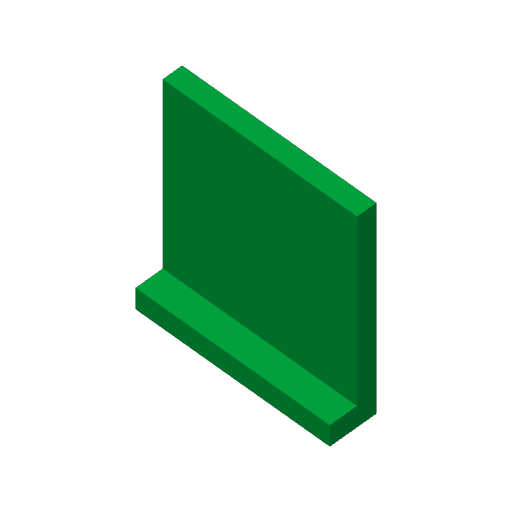
hardware/cad/rev04/3d-print/printing/bambu-studio/petg/C04_holder_rail/inspection/plate_1.png
