magnus188/trimix-analysator/hardware/cad/rev04/3d-print/printing/bambu-studio/petg/C06_usb_m2_frame/inspection/layers.png

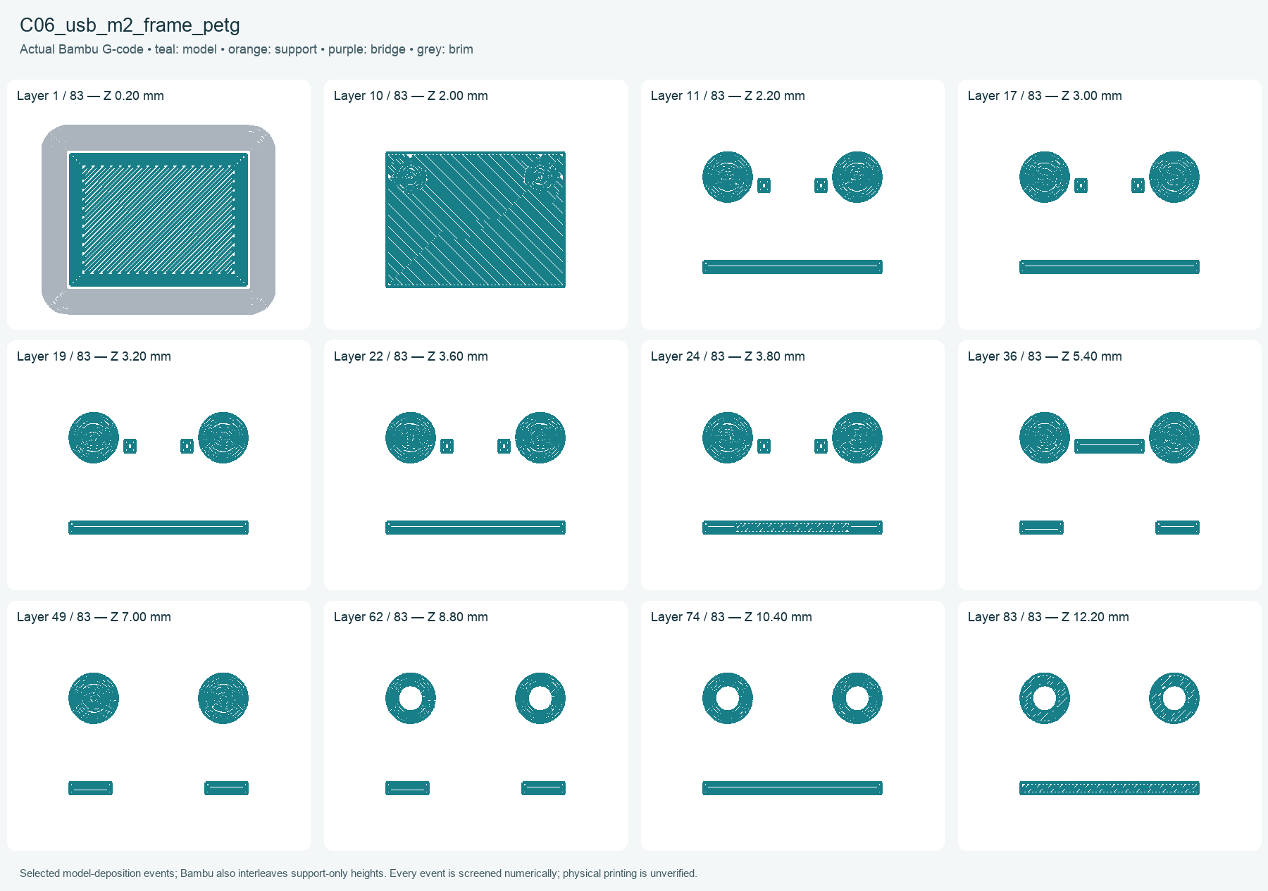
hardware/cad/rev04/3d-print/printing/bambu-studio/petg/C06_usb_m2_frame/inspection/layers.png
