magnus188/trimix-analysator/hardware/cad/rev04/3d-print/printing/bambu-studio/petg/C07_usb_bezel/inspection/layers.png

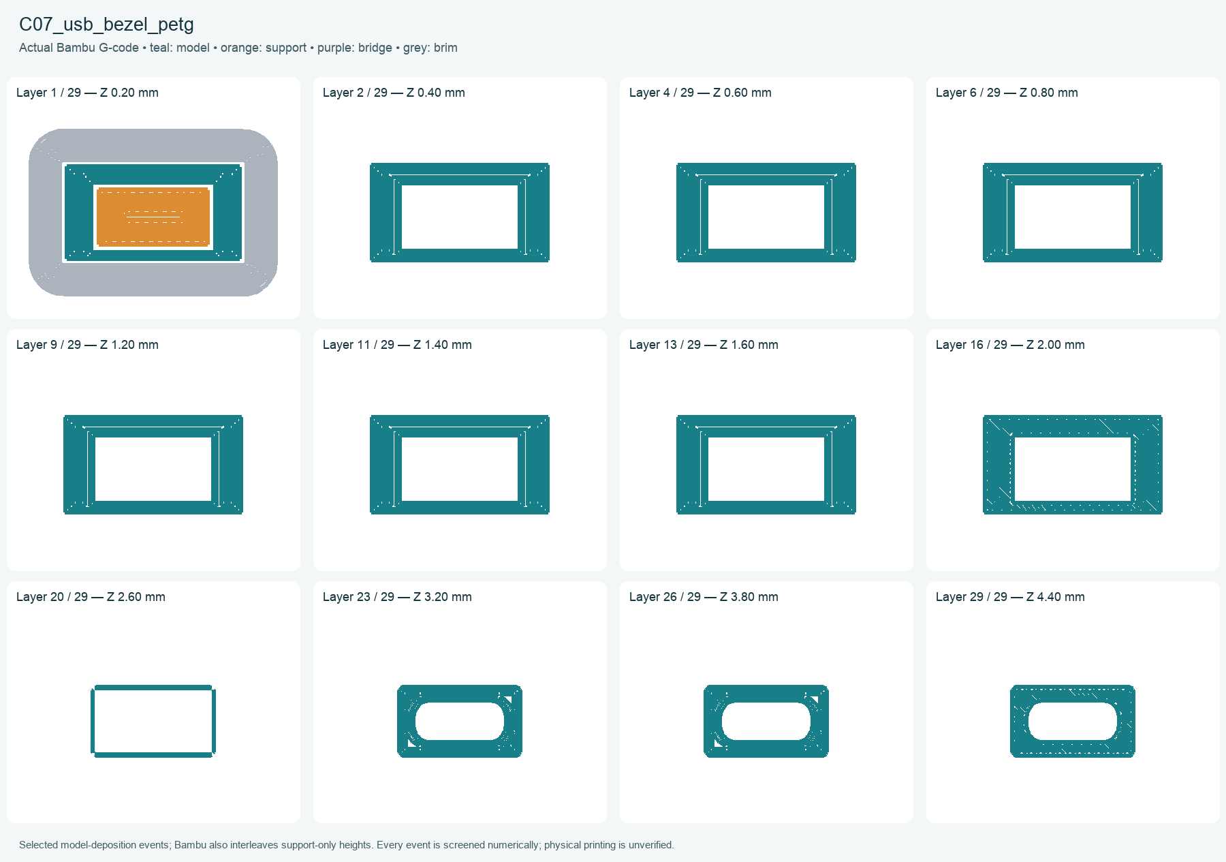
hardware/cad/rev04/3d-print/printing/bambu-studio/petg/C07_usb_bezel/inspection/layers.png
