magnus188/trimix-analysator/hardware/cad/rev04/3d-print/printing/bambu-studio/petg/C08_ao2_thread/inspection/plate_1.png

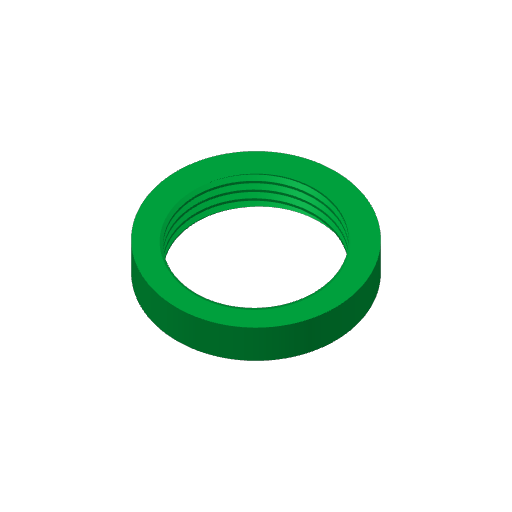
hardware/cad/rev04/3d-print/printing/bambu-studio/petg/C08_ao2_thread/inspection/plate_1.png
