magnus188/trimix-analysator/hardware/cad/rev04/3d-print/printing/bambu-studio/petg/TMX-A3-P01/inspection/layers.png

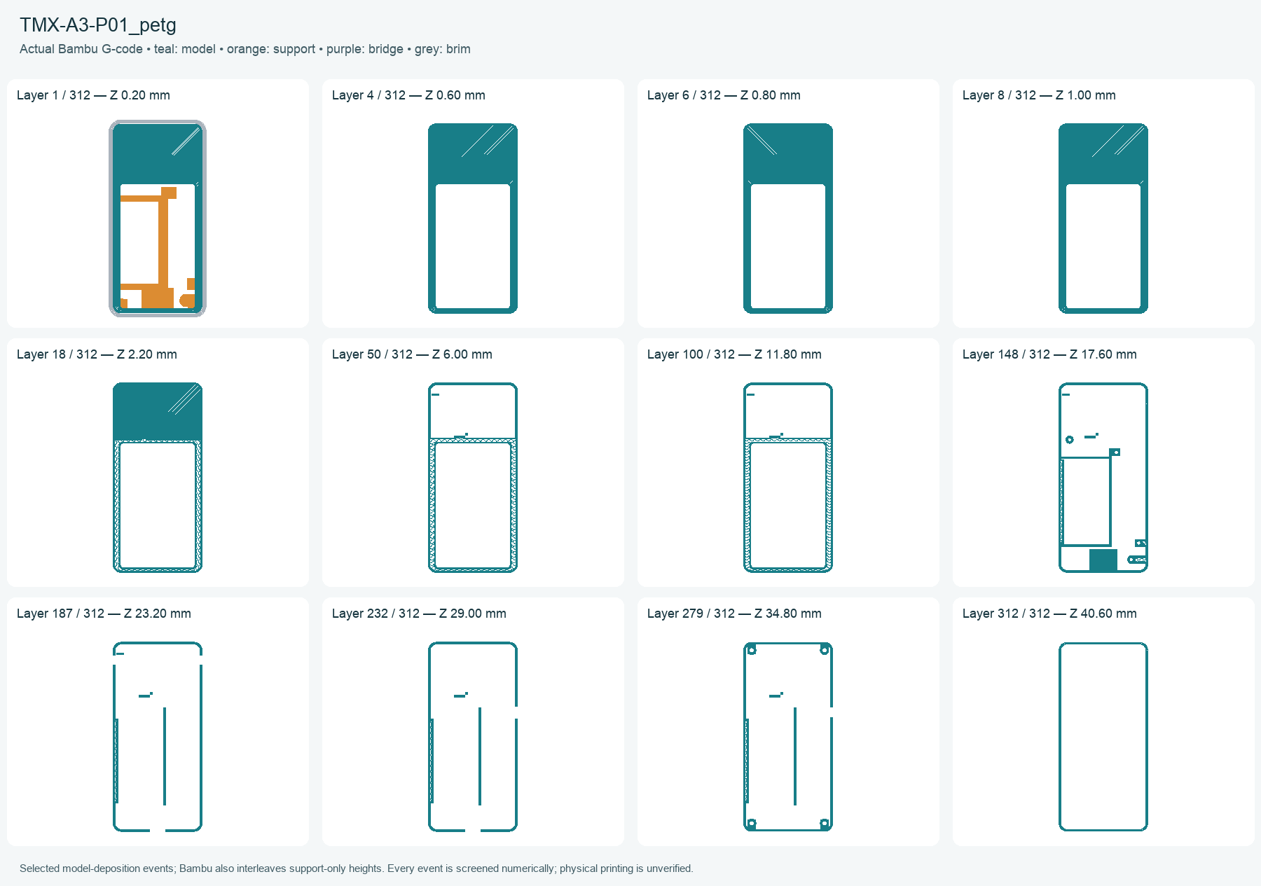
hardware/cad/rev04/3d-print/printing/bambu-studio/petg/TMX-A3-P01/inspection/layers.png
