magnus188/trimix-analysator/hardware/cad/rev04/3d-print/printing/bambu-studio/petg/TMX-A3-P10/inspection/plate_1.png

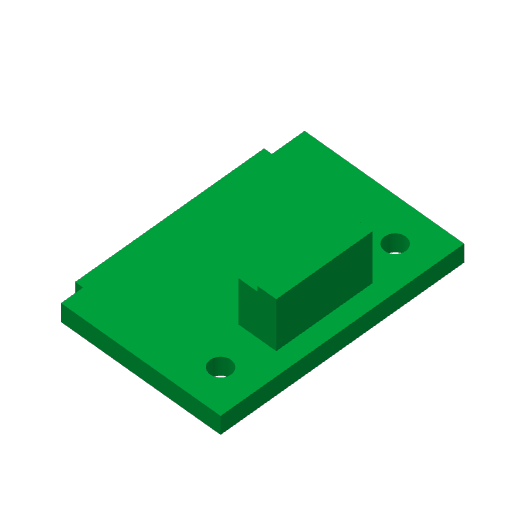
hardware/cad/rev04/3d-print/printing/bambu-studio/petg/TMX-A3-P10/inspection/plate_1.png
