magnus188/trimix-analysator/hardware/cad/rev04/3d-print/printing/bambu-studio/pla/C07_usb_bezel/inspection/plate_1.png

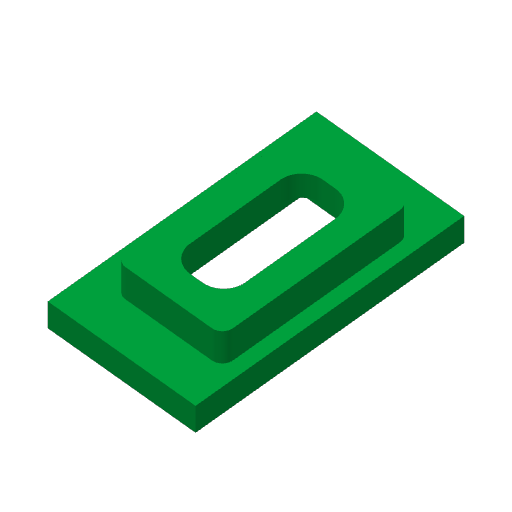
hardware/cad/rev04/3d-print/printing/bambu-studio/pla/C07_usb_bezel/inspection/plate_1.png
