magnus188/trimix-analysator/hardware/cad/rev04/3d-print/printing/bambu-studio/pla/TMX-A3-P07/inspection/section-candidate-194.png

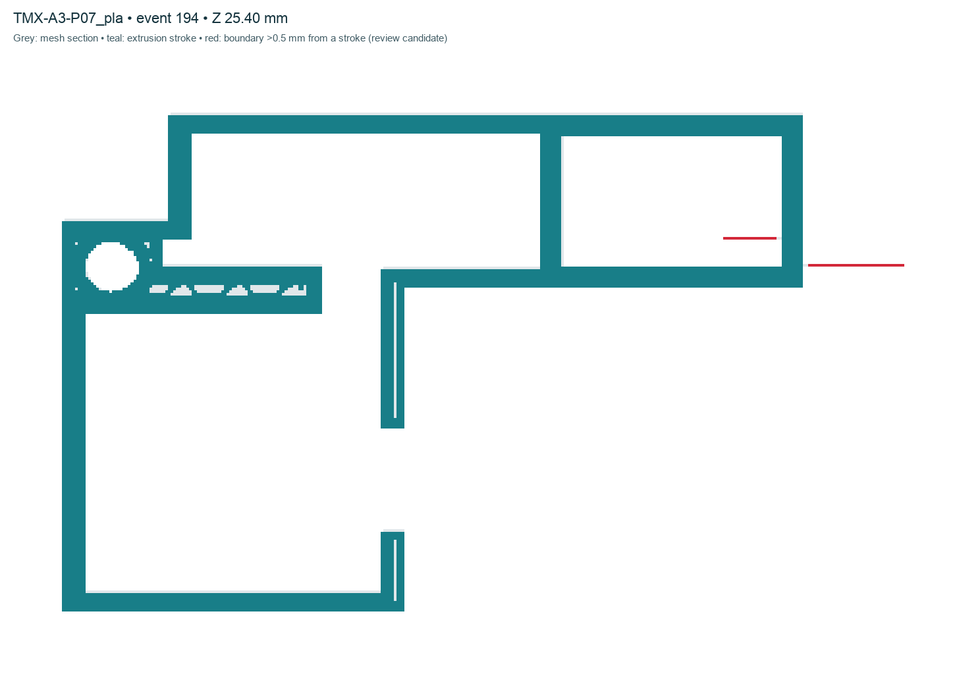
hardware/cad/rev04/3d-print/printing/bambu-studio/pla/TMX-A3-P07/inspection/section-candidate-194.png
