magnus188/trimix-analysator/hardware/system-review/electrical/main-final/assembly-drawings/assembly-only-locators-3.png

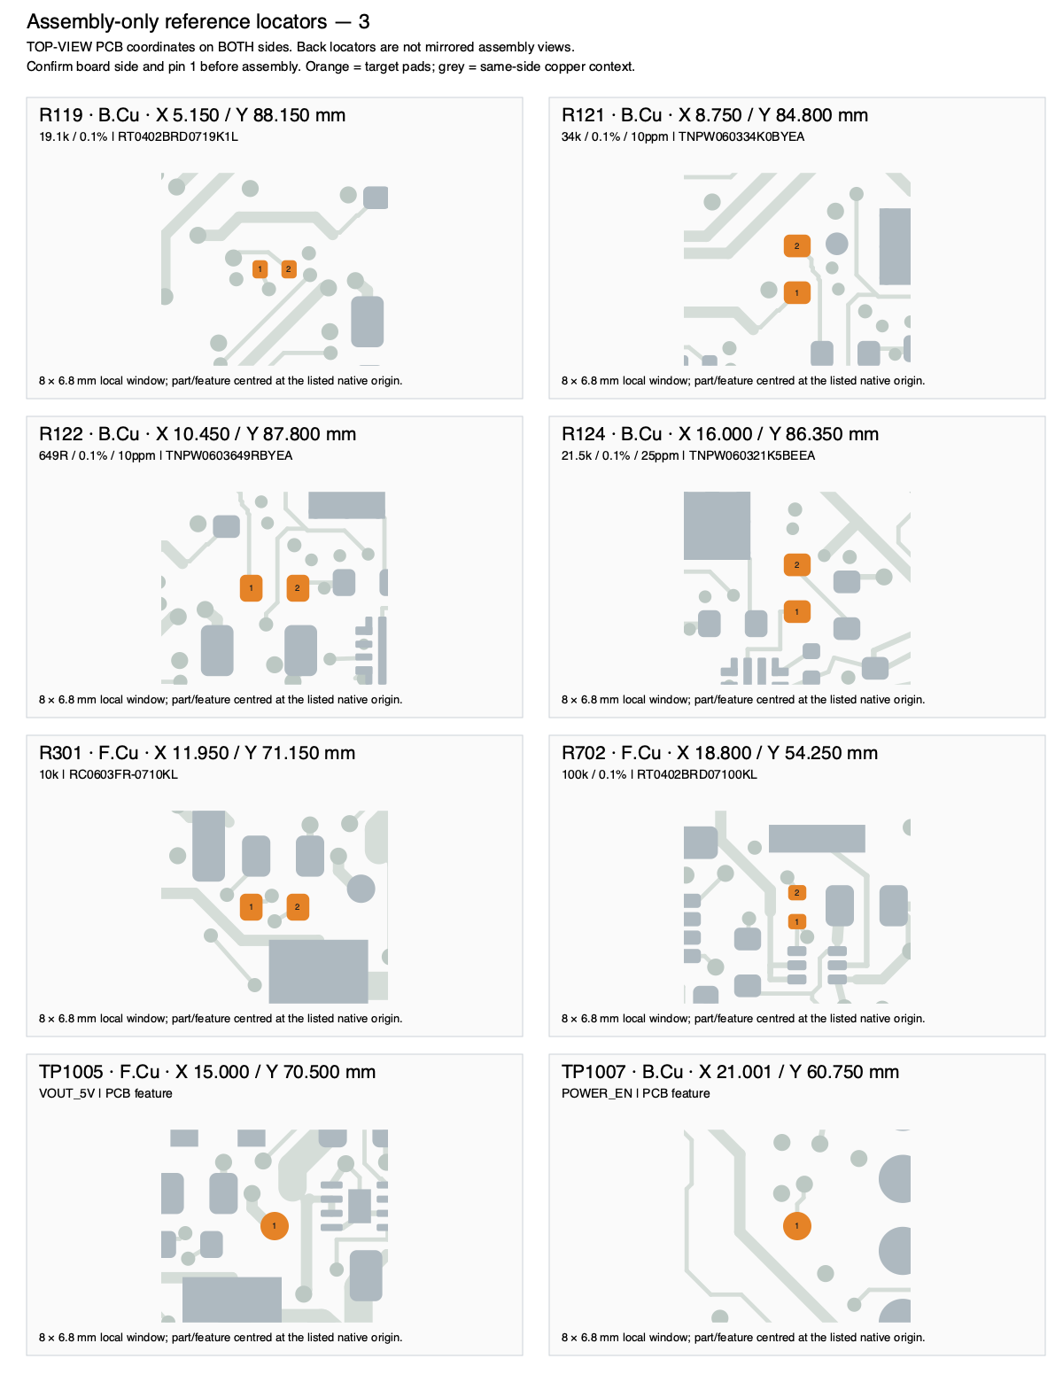
hardware/system-review/electrical/main-final/assembly-drawings/assembly-only-locators-3.png
