magnus188/trimix-analysator/hardware/system-review/electrical/routing-candidate/final-cleanup/assembly-drawings/assembly-only-locators-4.png

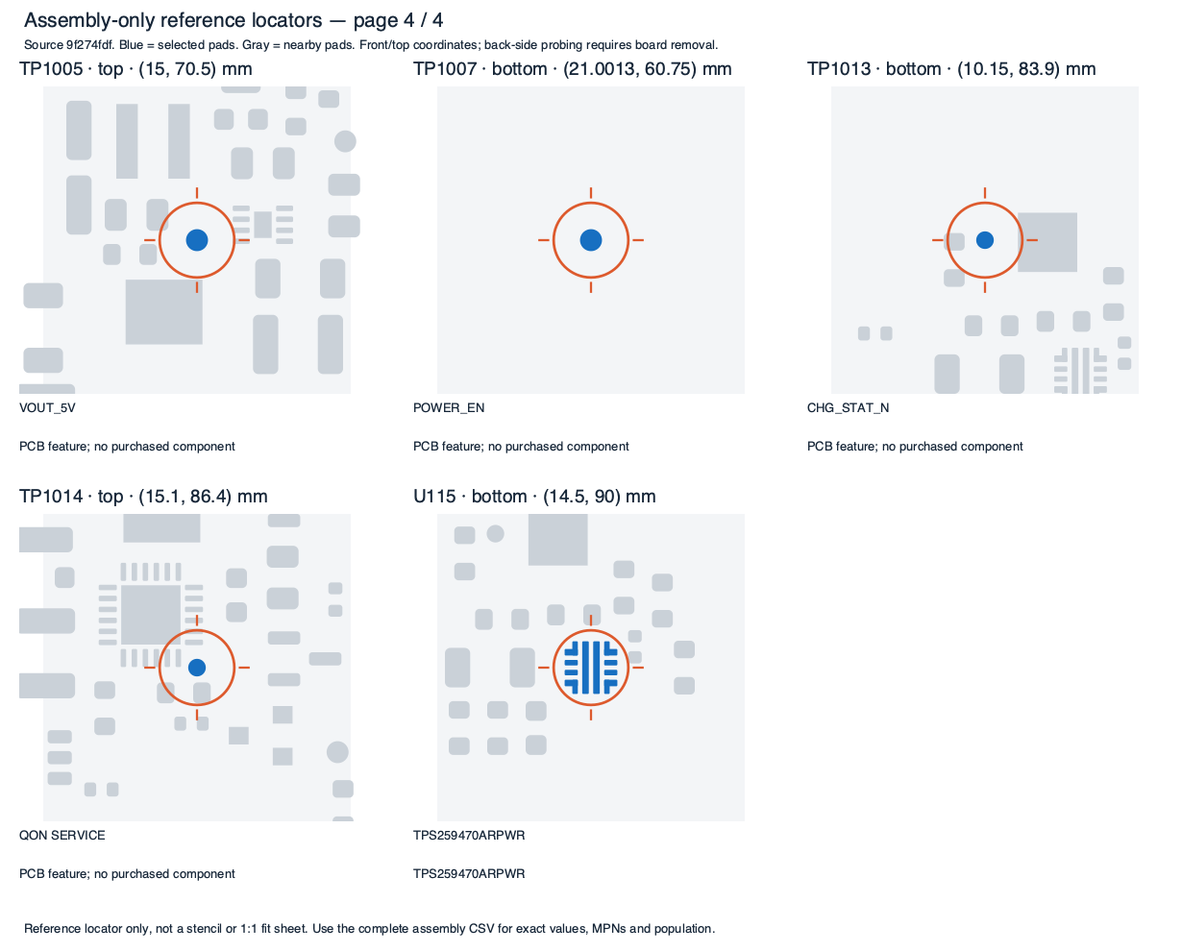
hardware/system-review/electrical/routing-candidate/final-cleanup/assembly-drawings/assembly-only-locators-4.png
