magnus188/trimix-analysator/hardware/system-review/electrical/routing-candidate/final-cleanup/assembly-drawings/Trimix_Analyzer-F_Fab.png

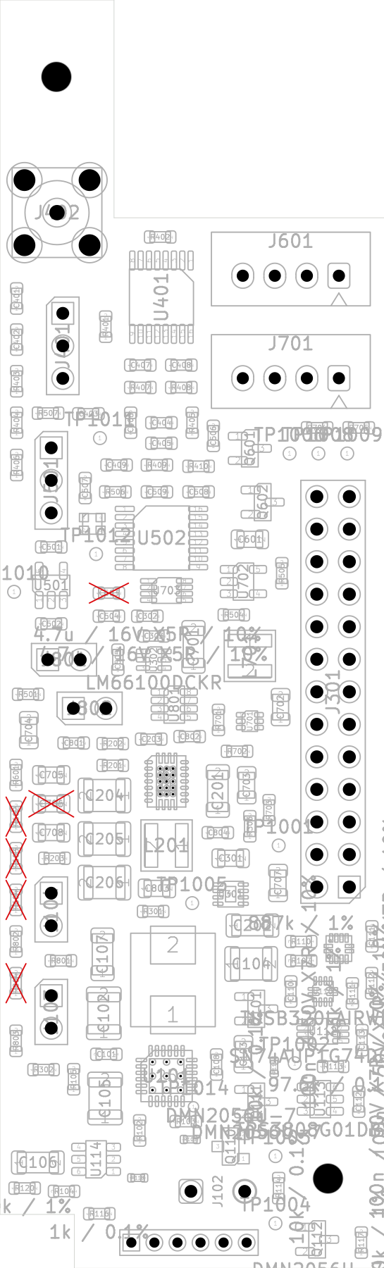
hardware/system-review/electrical/routing-candidate/final-cleanup/assembly-drawings/Trimix_Analyzer-F_Fab.png
