magnus188/trimix-analysator/hardware/system-review/mechanical/components/cnckitchen-m2-review/guidelines-page2.png

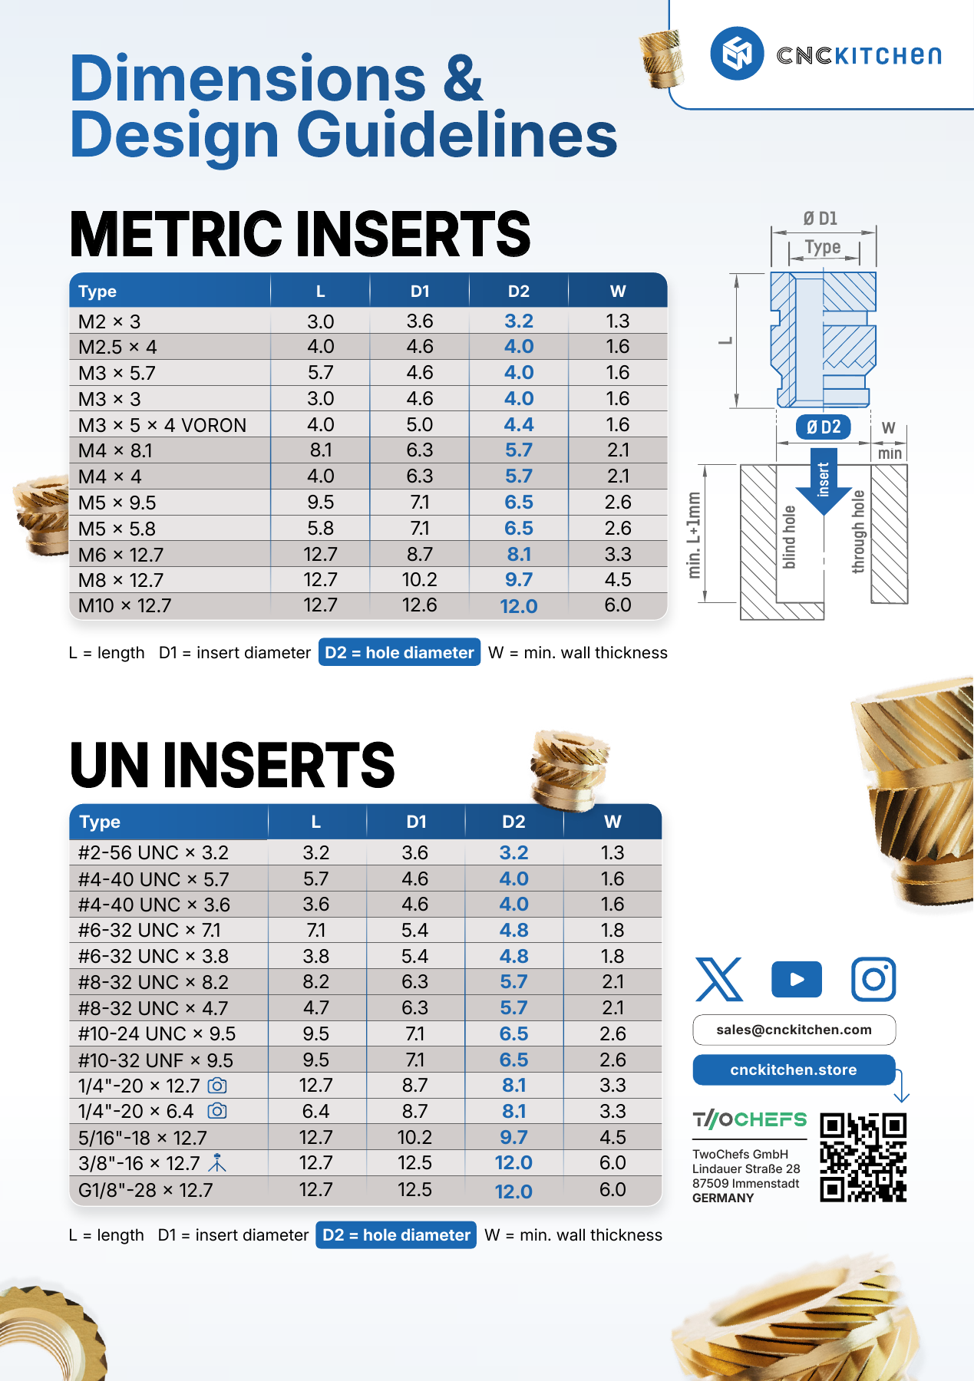
hardware/system-review/mechanical/components/cnckitchen-m2-review/guidelines-page2.png
