magnus188/trimix-analysator/hardware/system-review/mechanical/diagnostic-printing/backside-allocation/projects/petg/TMX-A3-P03_backside_allocation_diagnostic/inspection/plate_1.png

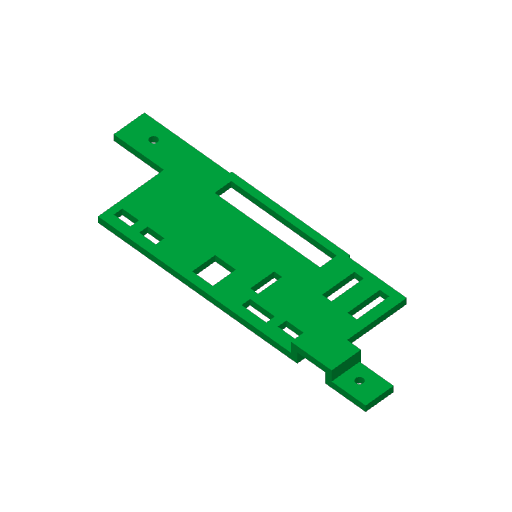
hardware/system-review/mechanical/diagnostic-printing/backside-allocation/projects/petg/TMX-A3-P03_backside_allocation_diagnostic/inspection/plate_1.png
