magnus188/trimix-analysator/hardware/system-review/mechanical/diagnostic-printing/projects/petg/TMX-A3-P10_systemreview_diagnostic/inspection/layers.png

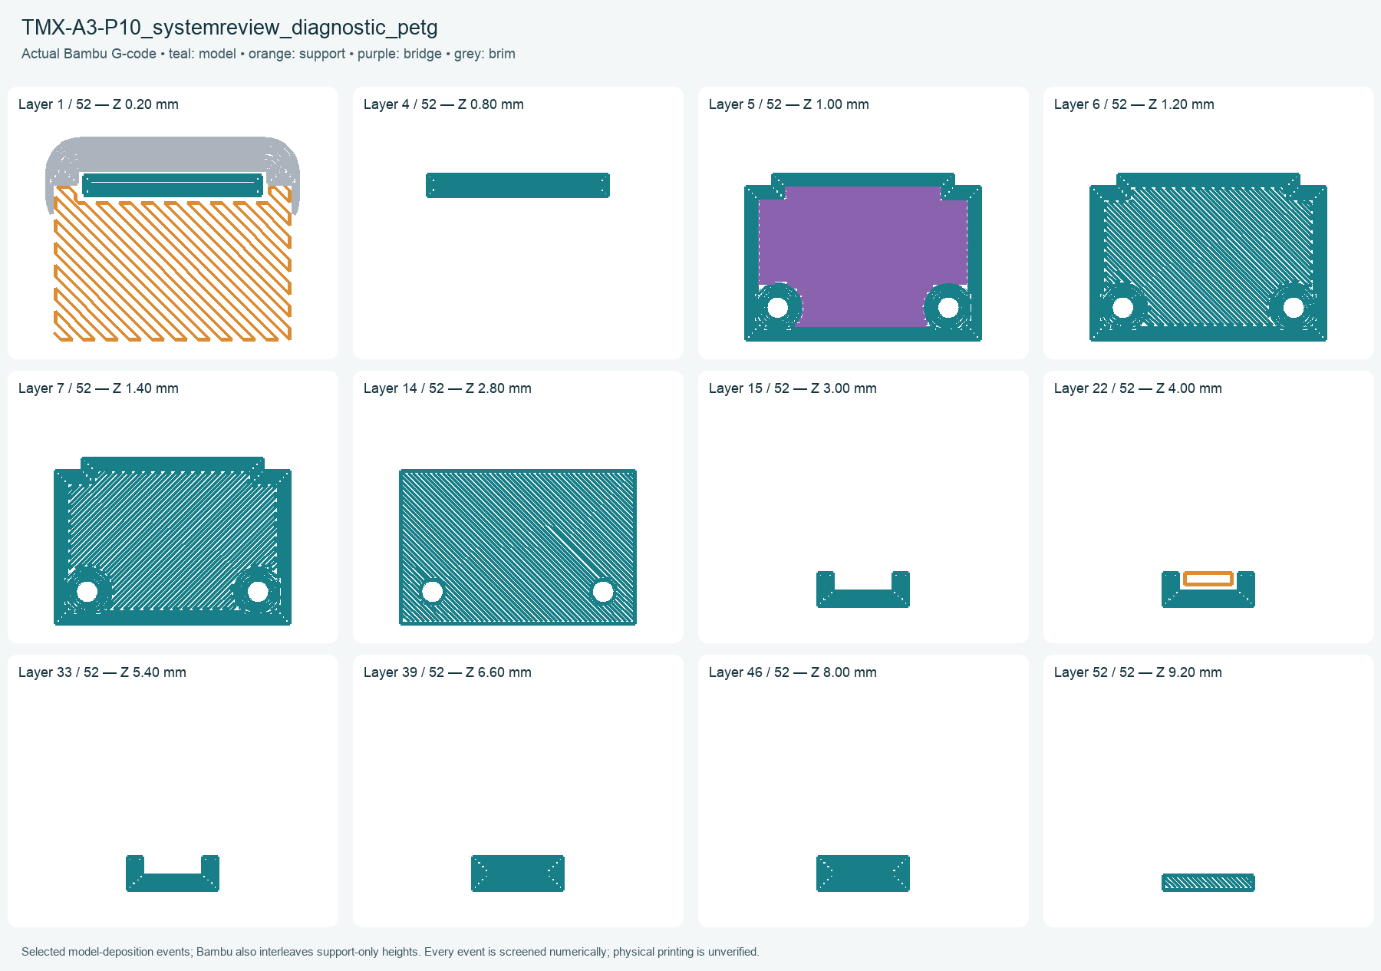
hardware/system-review/mechanical/diagnostic-printing/projects/petg/TMX-A3-P10_systemreview_diagnostic/inspection/layers.png
