magnus188/trimix-analysator/hardware/system-review/verification/before-routed-integration-interface/README.md

# Previous interface-packet output

Preserved before the routed-board integration refresh. PDF and inspected-render hashes match the historical receipt. Its source paths describe the earlier working inputs and are not a claim that those inputs still match the current project. No source hash has been rewritten to turn stale input into a passed review.
