magnus188/trimix-analysator/hardware/system-review/mechanical/verification/final-local-slices/README.md

# Final local diagnostic slice review

**Four changed parts passed mesh screening and all eight PLA/PETG diagnostic projects passed 50 slice checks.** Every selected actual layer contact sheet was visually inspected. These are fit and process diagnostics, not production print files or proof of enclosure safety, sealing or sensor performance.

The frozen Fusion handoff is `7b603ea51647ce96caf31efe5036b33dc0287b54c4f862cf1e7456005ee6540e`. It binds the verified SystemReview v10 housing/USB-frame/chamber and the adopted final carrier to main PCB `0962ad86…2788`. Unscaled STL copies and the native bounds/volume records are in `bound-inputs/` and `input-manifest.json`. Original meshes and all prior evidence were preserved. No Fusion calls, CAD changes, physical printer commands or print jobs were used by this review.

| Part | Orientation | Triangles | PLA / PETG deposition events | Final deposited top |
| --- | --- | ---: | ---: | ---: |
| P01 housing | Front down; rear opening up | 115,184 | 312 / 312 | 40.60 mm |
| P03 carrier | Rear down | 8,952 | 37 / 37 | 5.40 mm |
| P06 USB support frame | Floor down | 24,852 | 85 / 85 | 12.20 mm |
| P07 sampling chamber | Floor down; lid opening up | 224,554 | 242 / 242 | 33.00 mm |

Event counts include interleaved support heights; they are not all full 0.20 mm model layers. The carrier's native 5.50 mm extent is discretized to a 5.40 mm deposited top at the starting layer setting. Physical dimensions, seating and clearances must therefore be measured on the prototype, rather than treating the nominal CAD extent as a guaranteed printed size.

## Digital checks

- All four meshes contain one edge-connected component, positive volume, and zero boundary edges, nonmanifold edges or degenerate triangles. Maximum native/mesh bound difference is 0.0000031 mm. Maximum relative volume difference is 0.0000196, below the existing 0.001 comparison limit. Edge welding uses 0.000001 mm and does not prove the absence of every possible self-intersection.
- Bambu Studio 02.08.02.61 used the existing H2D 0.4 mm nozzle / 0.20 mm layer profiles, four walls and the existing accessible-support settings. All generated profile files are byte-identical to the earlier diagnostic workflow. Their actual bytes and the executable were bound immediately before and after each slice.
- All eight final projects have intact 3MF ZIP contents, matching declared/event counts, correct material/nozzle/layer settings, zero slice-info warnings, no unhandled extruding moves and zero detected disconnected-island candidates.
- Every deposition event was screened with the existing 0.25 mm raster method, using the prior-deposit 0.5 mm window and one-pixel contact margin. This is a screening heuristic, not a full unsupported-area, bridge-strength or minimum-wall proof. The eight selected contact sheets were reviewed separately.
- P07 uses three native-owner-confirmed support blockers with 0.35 mm halos. All three blockers survive in both final projects, and no support bead intersects their protected cores. Two intermediate no-support projects were generated only to provide valid Bambu metadata for the protected projects; they are not intended print selections.

## Visual findings and physical checks

The housing retains its screen opening, side ports, rear insert-boss annuli and deposited wall paths. Supports beneath the internal rails and lower ledges are accessible through the loose housing openings. Check broad-face warping, support removal and actual insert retention before module installation.

The carrier clearance windows remain open with continuous deposited webs. Supports beneath the lowered coax bridge can be reached from the unassembled carrier sides. Remove them before fitting the PCB, then measure actual rear-component and solder-tail clearance. The slice does not establish the remaining web's mechanical strength.

The USB frame retains both bosses and its backing ledges. The upper insertion regions of the blind pilot holes remain open; gyroid below their designed blind floors is structural infill, not a through-hole obstruction. Local bridge supports are exposed before cartridge assembly. Test insert fit and USB insertion loads physically.

The chamber retains its four boss tops, walls, sampled lateral passages and roof closures. Generated supports occur beneath the external inlet and in lid-open sensor pockets; the three protected passage cores remain free of generated support beads. Remove accessible supports and loose debris before fitting sensors. Selected layer images and exclusion checks do not certify flow, porosity, sealing or cleanliness. Leak, thermal and gas-response testing remain pending.

These observations are recorded per material in `visual-review.json`. The native plate previews supplement actual G-code layer drawings; they are not themselves toolpath proof.

## Runtime and reproducibility

The first sandboxed Bambu archive export aborted with exit -6 after the mesh gate passed. That failed attempt is preserved in `runtime-attempts/sandbox-abort/`. The identical source and profiles succeeded with approved local desktop execution. No geometry or preset workaround was applied. CLI logs contain inherited proprietary T-command diagnostics also seen in previous successful runs; final CLI exits are zero and the separate slice-info warning lists are empty. No claim about physical printer execution follows from this.

Run from the repository root:

```sh
/tmp/trimix-gerbonara-venv/bin/python hardware/system-review/mechanical/verification/final-local-slices/run_diagnostics.py --manifest hardware/system-review/mechanical/verification/final-local-slices/input-manifest.json
```

All outputs, the isolated slicer data directory, profiles and oriented meshes stay under this diagnostic directory. `diagnostic-slice-review.json` contains actual CLI arguments and per-project profile hashes. `verification-receipt.json` binds the final reports, meshes, projects, toolpaths, inspection evidence and reader code. `prepared-workflow.json` records the earlier preparation checkpoint; it is not the final result.

PLA remains a fit prototype; PETG remains an unqualified target-material prototype. Final module installation, support removal, insert retention, screw fit, cable handling, leakage and temperature testing have not been performed.
