magnus188/trimix-analysator/hardware/pcb/integration/verification/markings/final-independent-audit.md

# Final independent marking audit

**Passed.** Both saved boards changed only annotations and benign hidden-field stroke serialization. Footprint positions, rotations, sides, pads, nets, models, tracks, zones, outlines and board rules are unchanged. All guarded schematic/project hashes are unchanged.

| Board | Front references | Back references | Total |
|---|---:|---:|---:|
| Main | 33 | 100 | 133 |
| USB | 3 | 1 | 4 |

All 137 native reference fields are visible on a silkscreen layer at **1.0 mm text height / 0.15 mm stroke**, with correct reverse-side mirroring. The CSV reference identities and sides match the saved boards exactly. The full assembly SVG contains all 133 main-board identifiers exactly once.

The initial H1/H2 placement inside the NPTH holes was corrected by root. The independent final check tests every main reference's actual native ink bounding box against both Ø2.3 mm holes and both Ø5 mm head reserves: **266 pair checks, zero intersections**. Minimum clearance over all labels is 1.775 mm to a hole and 0.425 mm to a head reserve. H1 and H2 themselves each clear the hole edge by **1.775 mm** and the head reserve by **0.425 mm**.

Saved-board DRC is exactly unchanged, including individual findings and ignored-check lists. Main: **39 existing fabrication-rule violations, 288 unconnected items, zero schematic-parity issues**. USB: **zero violations, zero unconnected items, zero parity issues**. No new silkscreen finding appears. The main board is still unrouted.

All five refreshed PNGs were visually inspected: main front/back, USB front/back and the full assembly map. Text is readable at the provided enlarged scale, dense groups remain distinct, polarity marks remain visible, and reverse artwork reads normally. This is screen-based artwork QA, not a physical print test. Back-side references may be hidden by the installed carrier; use the assembly map during in-enclosure work.

The only additional serialization change is an explicit 0.15 mm stroke on 35 hidden metadata fields. Their names, values, visibility and all other attributes remain unchanged. The comparator records this narrow normalization; it does not waive any electrical or mechanical difference.

[Detailed independent receipt](final-independent-audit.json) · [Main annotation comparison](main-annotation-only.json) · [USB annotation comparison](usb-annotation-only.json)
