magnus188/trimix-analysator/hardware/pcb/verification/analyzer/Trimix_Analyzer.pdf

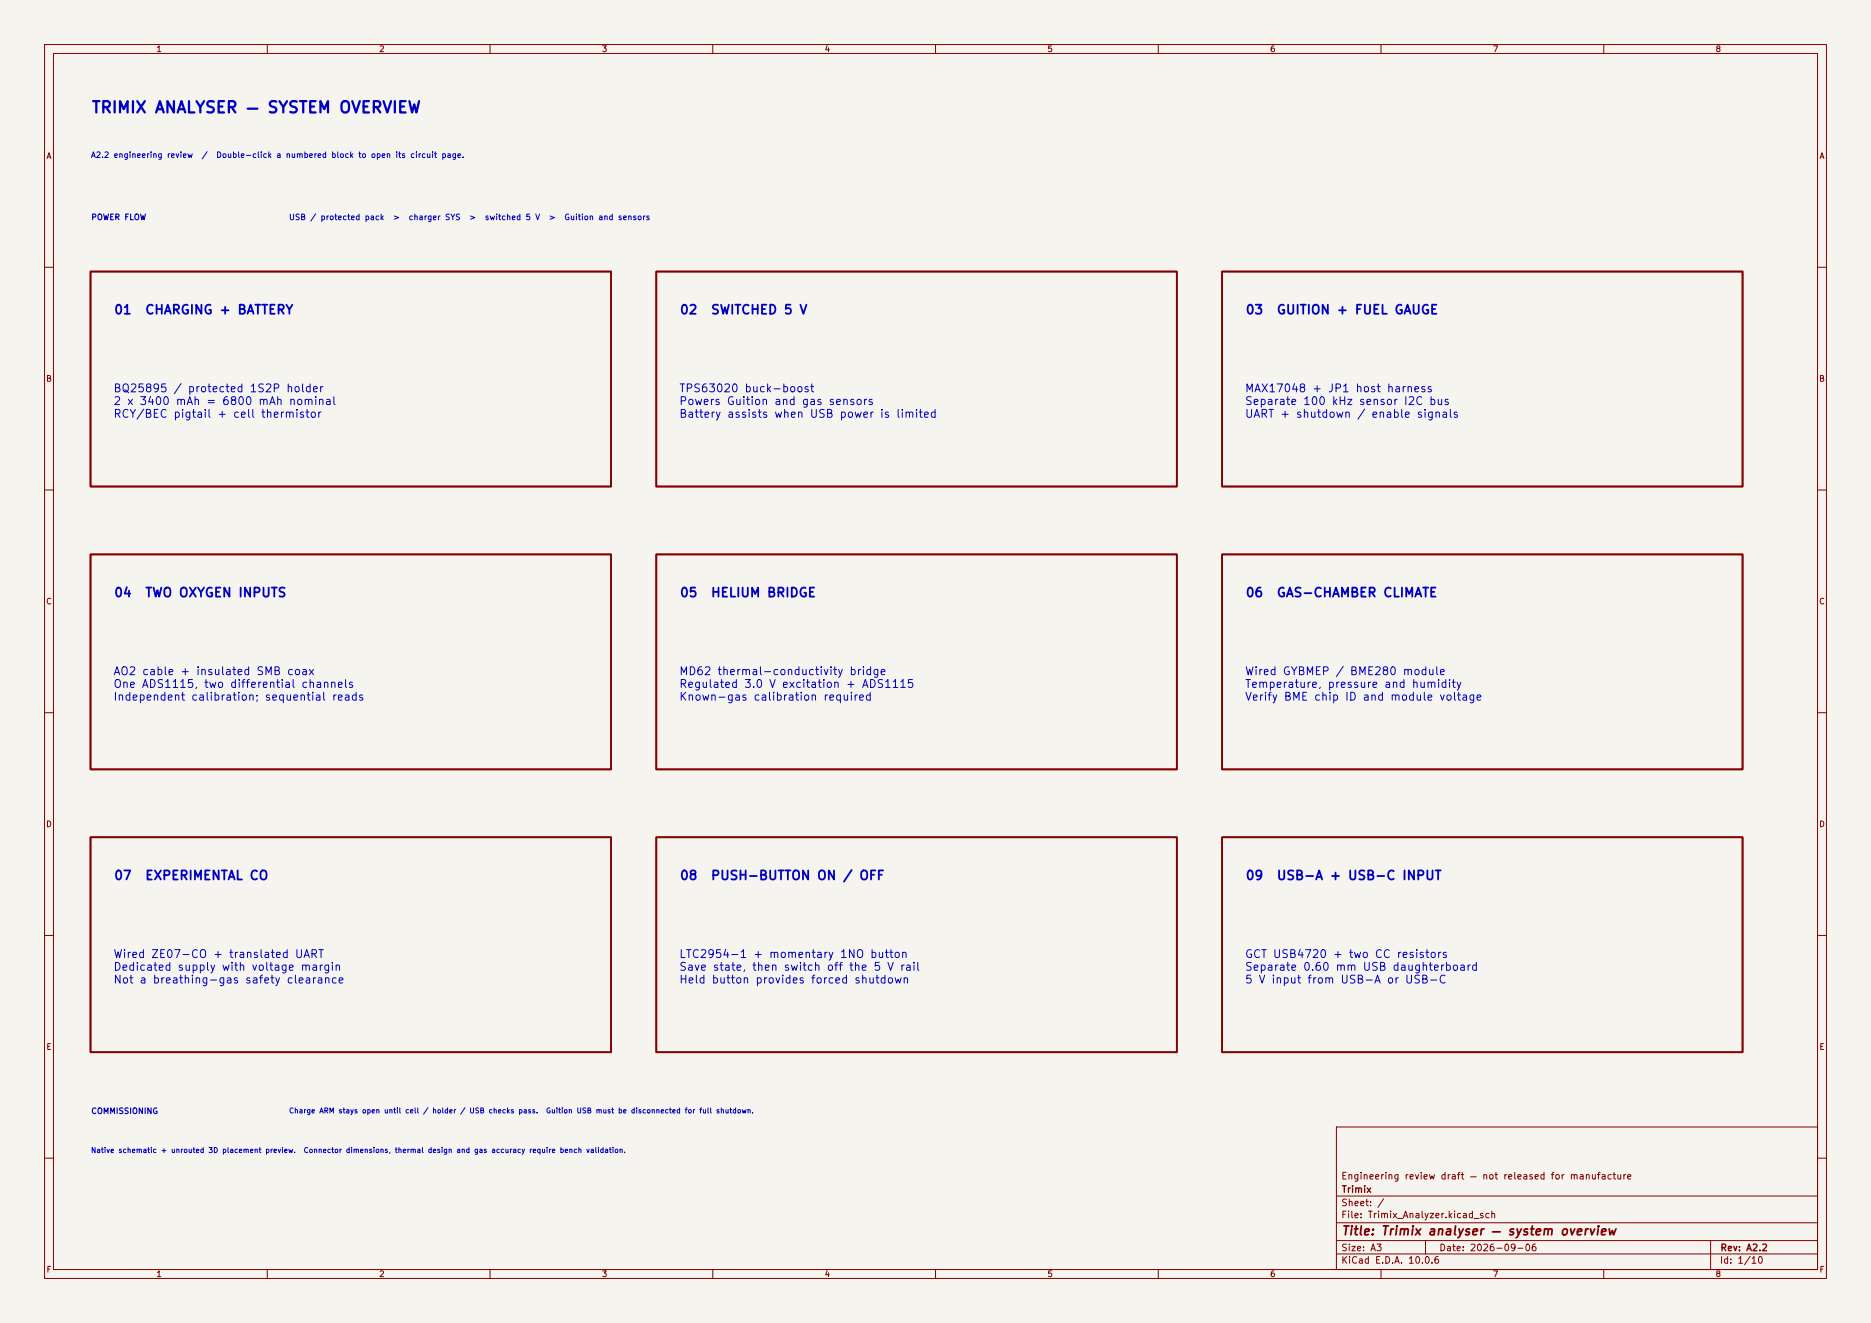
[picture p209: page 1]

POWER FLOW TRIMIX ANALYSER — SYSTEM OVERVIEW

A2.2 engineering review / Double-click a numbered block to open its circuit page. USB / protected pack > charger SYS > switched 5 V > Guition and sensors

BQ25895 / protected 1S2P holder
2 x 3400 mAh = 6800 mAh nominal
RCY/BEC pigtail + cell thermistor

MAX17048 + JP1 host harness
Separate 100 kHz sensor I2C bus
UART + shutdown / enable signals

TPS63020 buck-boost
Powers Guition and gas sensors Battery assists when USB power is limited

AO2 cable + insulated SMB coax One ADS1115, two differential channels

MD62 thermal-conductivity bridge
Regulated 3.0 V excitation + ADS1115
Known-gas calibration required

Wired GYBMEP / BME280 module
Temperature, pressure and humidity
Verify BME chip ID and module voltage

Independent calibration; sequential reads

08 PUSH-BUTTON ON / OFF

LTC2954-1 + momentary 1NO button
Save state, then switch off the 5 V rail
Held button provides forced shutdown

GCT USB4720 + two CC resistors
Separate 0.60 mm USB daughterboard
5 V input from USB-A or USB-C

Wired ZE07-CO + translated UART
Dedicated supply with voltage margin
Not a breathing-gas safety clearance

Native schematic + unrouted 3D placement preview. Connector dimensions, thermal design and gas accuracy require bench validation.

Engineering review draft — not released for manufacture
Trimix
Sheet: /
File: Trimix_Analyzer.kicad_sch
Title: Trimix analyser — system overview

Size: A3 | Rev: A2.2 | F Date: 2026-09-06
KiCad E.D.A. 10.0.6 | Id: 1/10

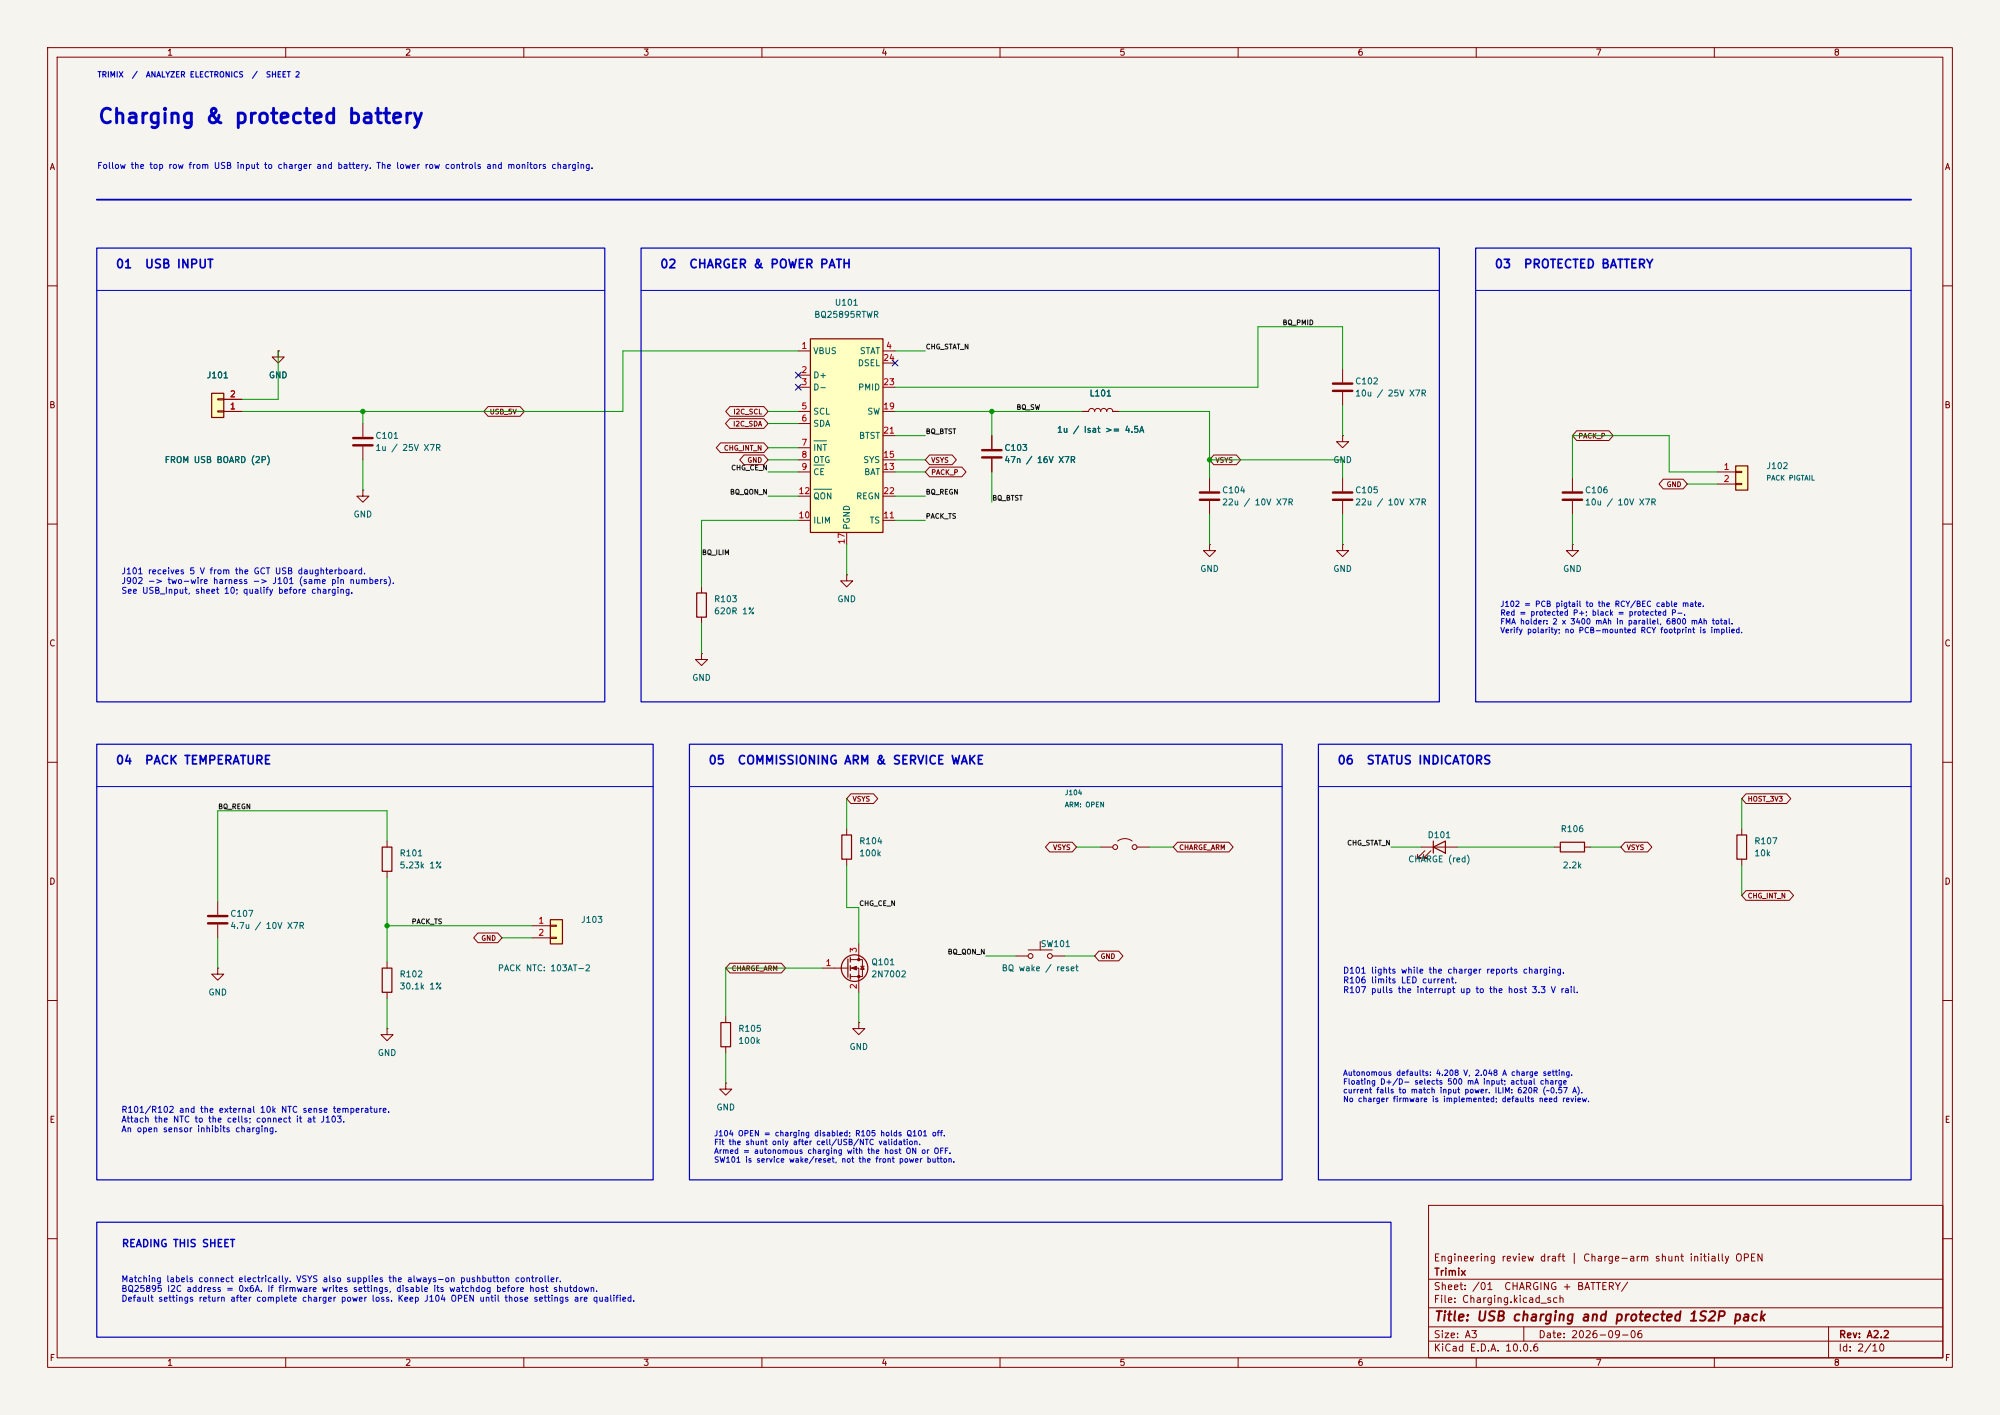
[picture p210: page 2]

TRIMIX / ANALYZER ELECTRONICS / SHEET 2
PACK_TS Charging & protected battery

Follow the top row from USB input to charger and battery. The lower row controls and monitors charging.

02 CHARGER & POWER PATH
SW 19 BTST 21 REGN 22 PMID 23 DSEL 24 U101 BQ25895RTWR

J101 receives 5 V from the GCT USB daughterboard. J902 -> two-wire harness -> J101 (same pin numbers). See USB_Input, sheet 10; qualify before charging.

J102 = PCB pigtail to the RCY/BEC cable mate. Red = protected P+; black = protected P-. FMA holder: 2 x 3400 mAh in parallel, 6800 mAh total. Verify polarity; no PCB-mounted RCY footprint is implied. D101 lights while the charger reports charging. R106 limits LED current. R107 pulls the interrupt up to the host 3.3 V rail. Matching labels connect electrically. VSYS also supplies the always-on pushbutton controller. BQ25895 I2C address = 0x6A. If firmware writes settings, disable its watchdog before host shutdown. Default settings return after complete charger power loss. Keep J104 OPEN until those settings are qualified.

Autonomous defaults: 4.208 V, 2.048 A charge setting.
Floating D+/D- selects 500 mA input; actual charge
current falls to match input power. ILIM: 620R (~0.57 A). No charger firmware is implemented; defaults need review.

R101/R102 and the external 10k NTC sense temperature. Attach the NTC to the cells; connect it at J103. An open sensor inhibits charging.

Engineering review draft | Charge-arm shunt initially OPEN
Trimix
Sheet: /01 CHARGING + BATTERY/
File: Charging.kicad_sch
Title: USB charging and protected 1S2P pack

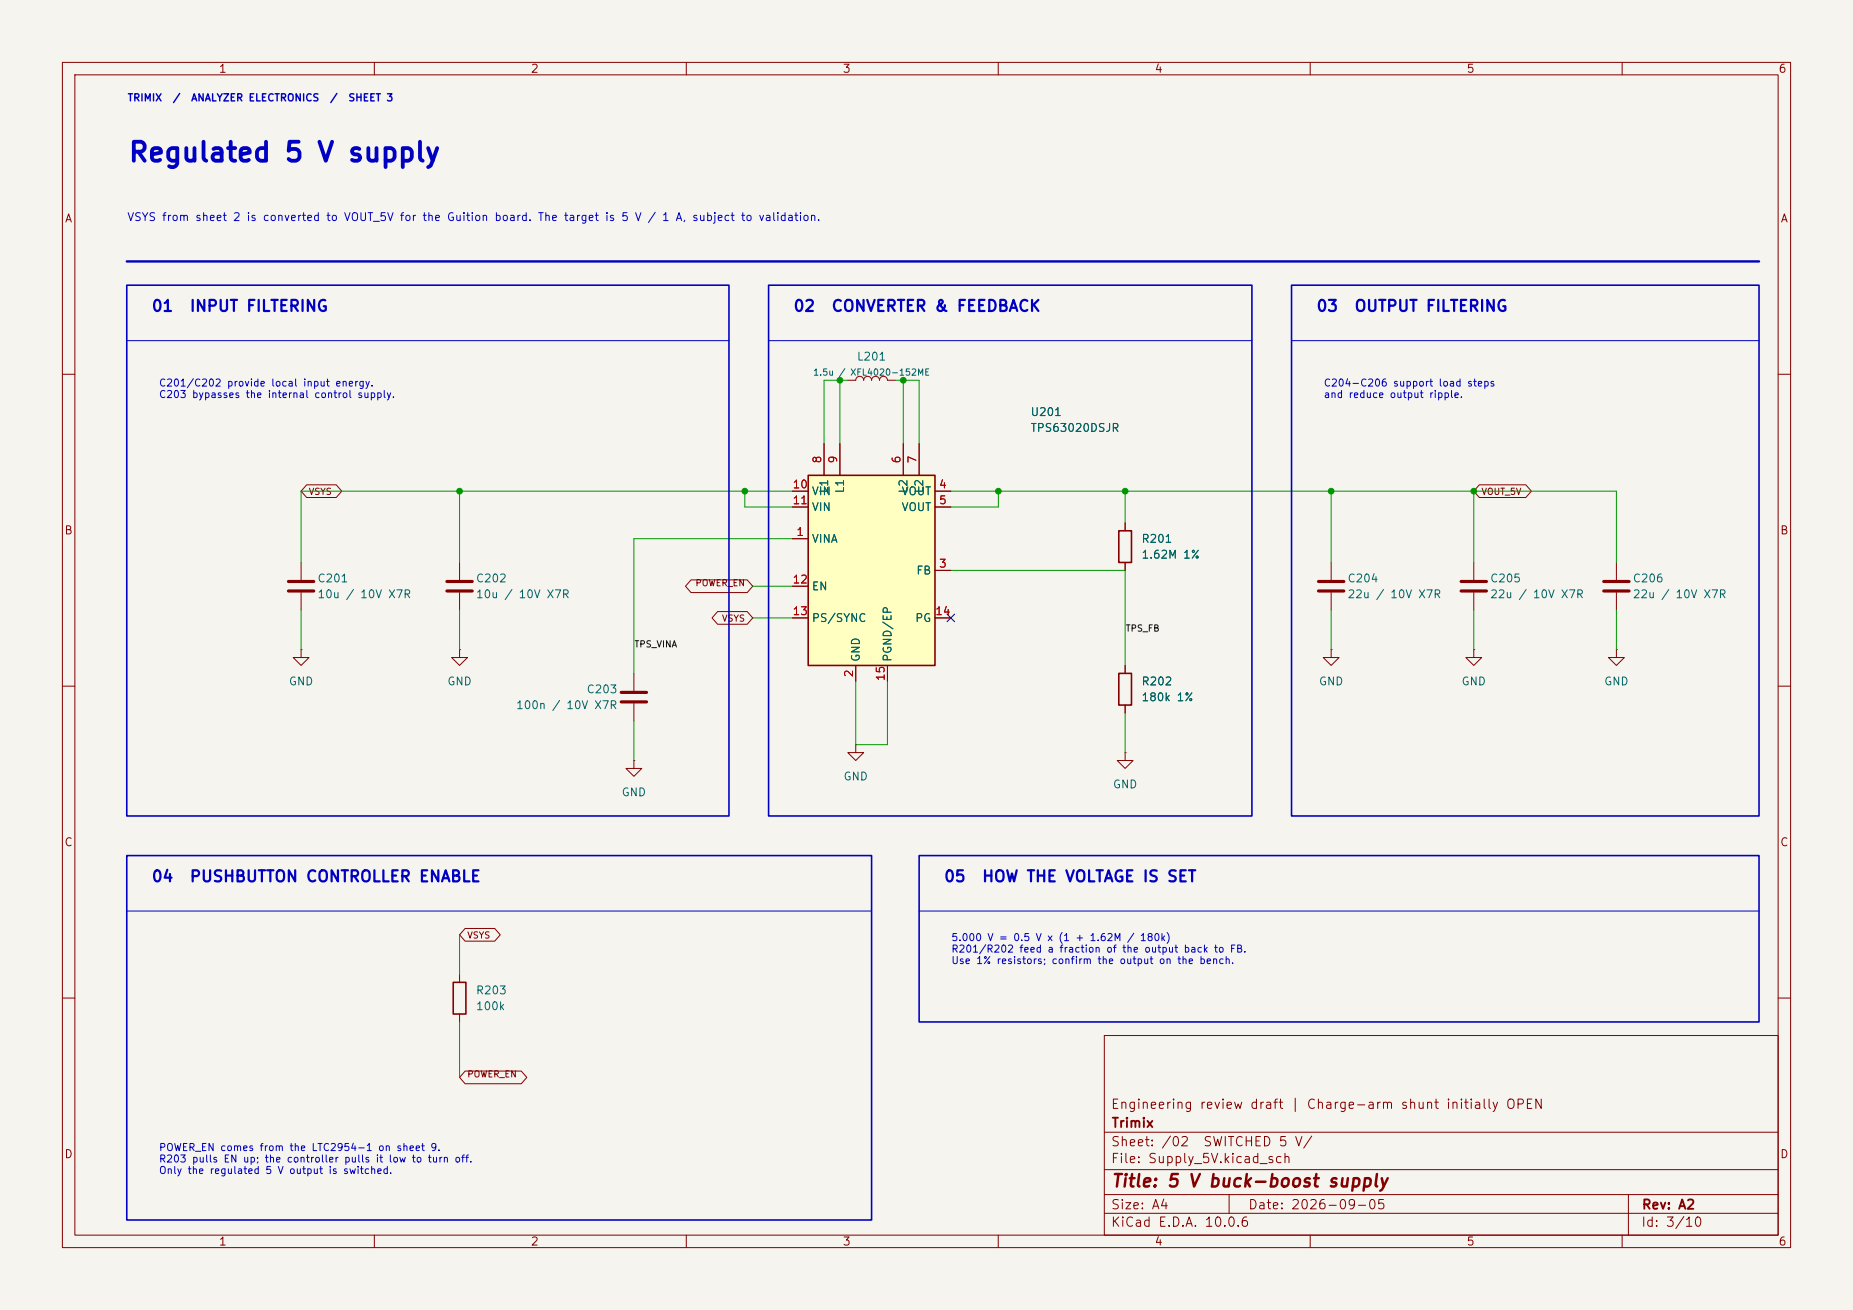
[picture p211: page 3]

TRIMIX / ANALYZER ELECTRONICS / SHEET 3 04 PUSHBUTTON CONTROLLER ENABLE
Regulated 5 V supply

R201/R202 feed a fraction of the output back to FB. Use 1% resistors; confirm the output on the bench. 01 INPUT FILTERING

C204-C206 support load steps and reduce output ripple.

05 HOW THE VOLTAGE IS SET

Engineering review draft | Charge-arm shunt initially OPEN
Trimix
Sheet: /02 SWITCHED 5 V/
File: Supply_5V.kicad_sch
Title: 5 V buck-boost supply

POWER_EN comes from the LTC2954-1 on sheet 9. R203 pulls EN up; the controller pulls it low to turn off. Only the regulated 5 V output is switched.

Size: A4 | Rev: A2

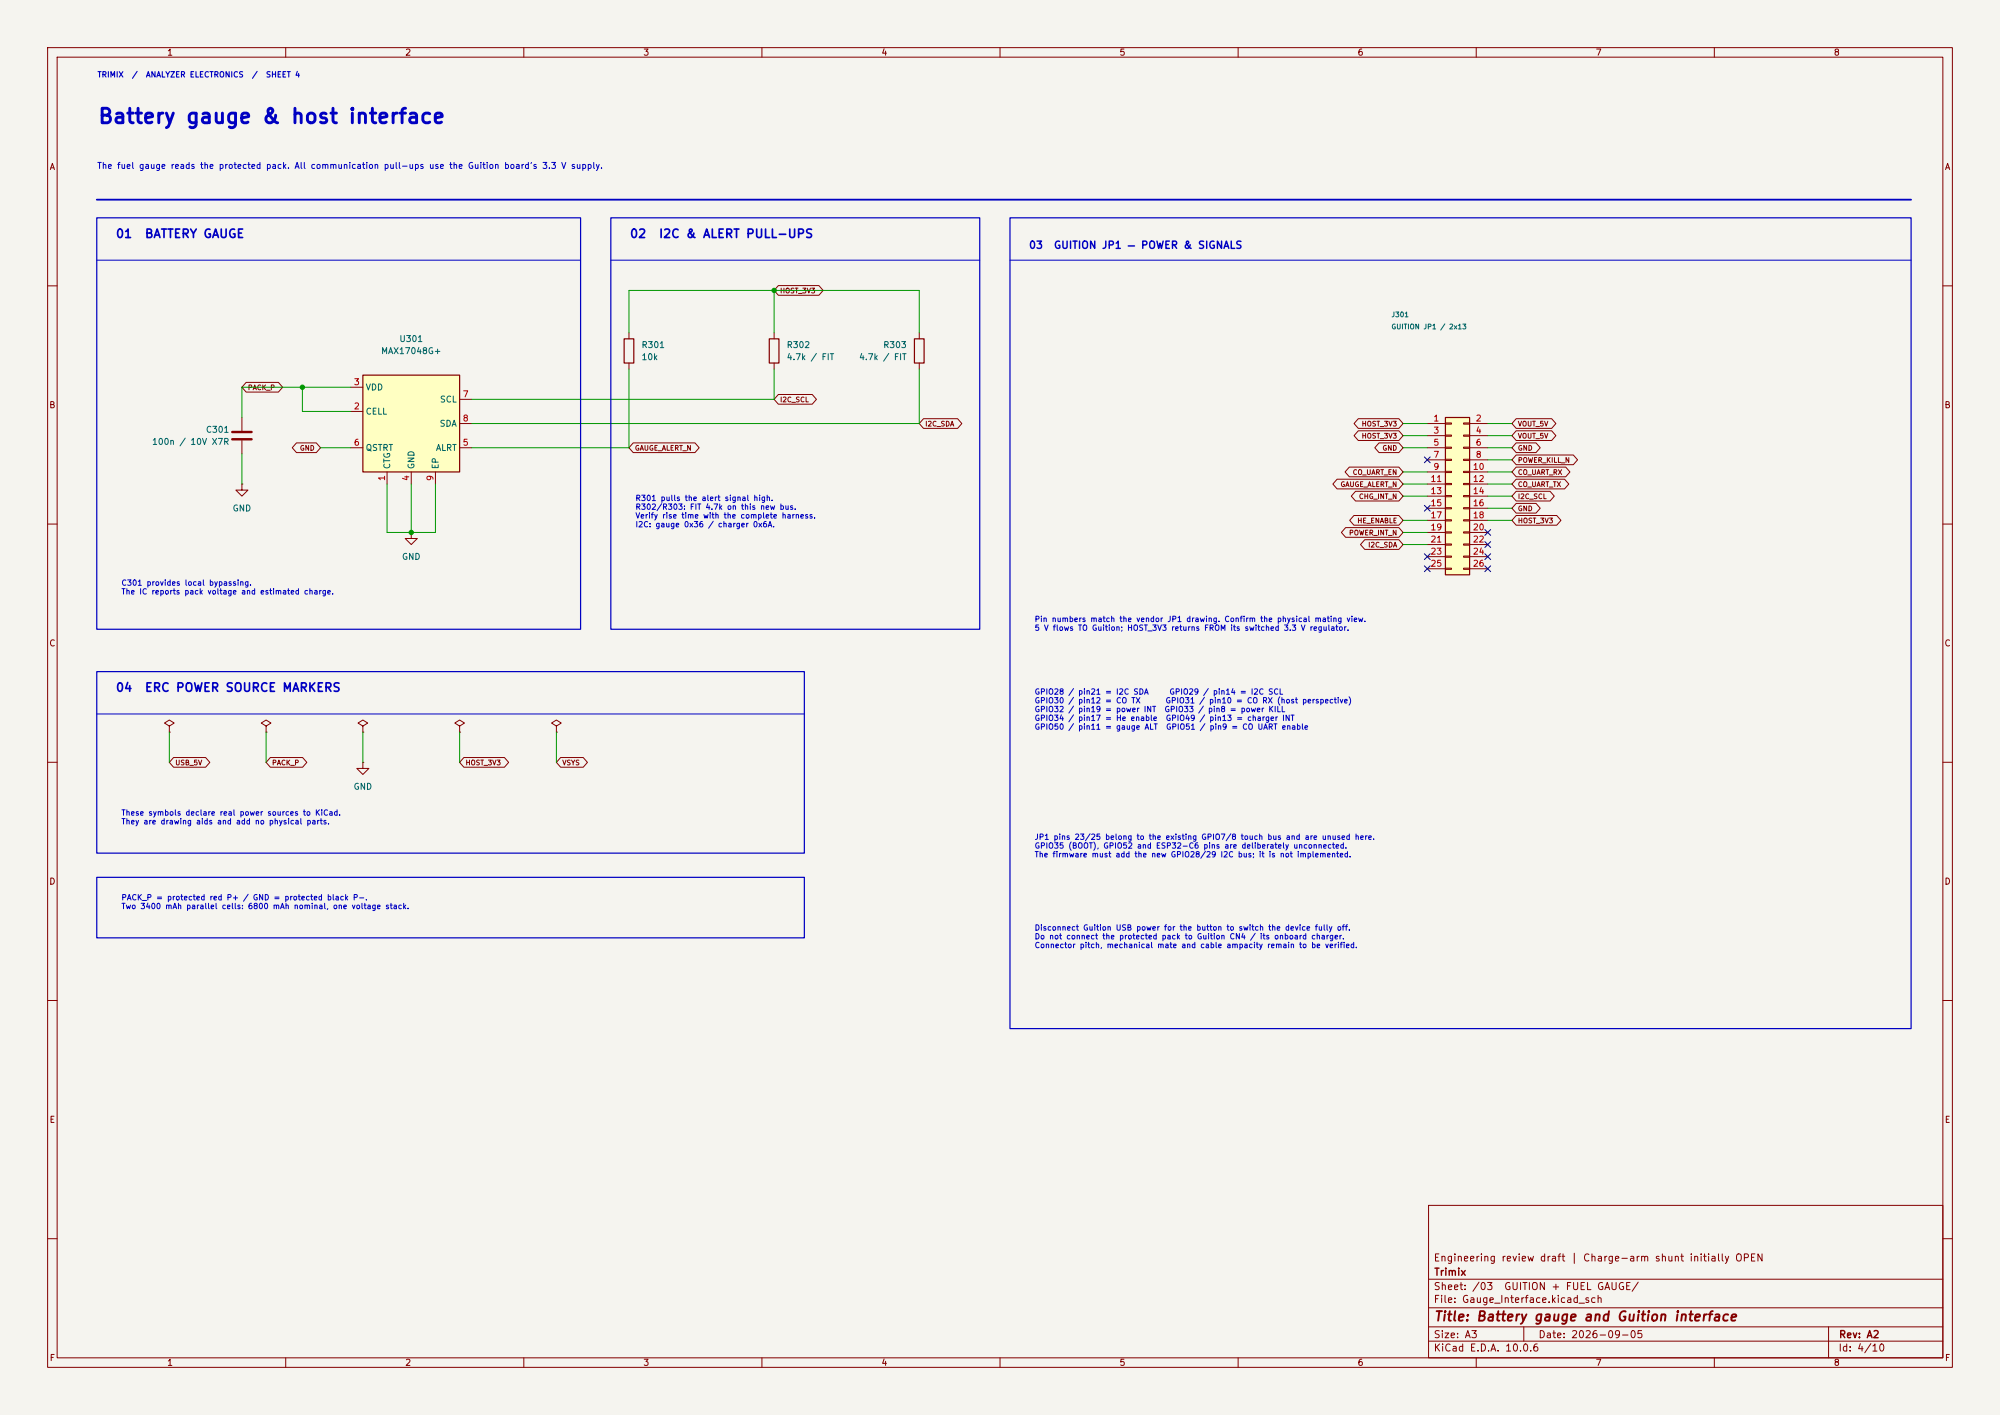
[picture p212: page 4]

The fuel gauge reads the protected pack. All communication pull-ups use the Guition board's 3.3 V supply. TRIMIX / ANALYZER ELECTRONICS / SHEET 4 01 BATTERY GAUGE

VSYS PACK_P = protected red P+ / GND = protected black P-. Two 3400 mAh parallel cells: 6800 mAh nominal, one voltage stack. Battery gauge & host interface

R301 pulls the alert signal high.
R302/R303: FIT 4.7k on this new bus. Verify rise time with the complete harness.

C301 provides local bypassing. The IC reports pack voltage and estimated charge.

04 ERC POWER SOURCE MARKERS

Engineering review draft | Charge-arm shunt initially OPEN
Trimix
Sheet: /03 GUITION + FUEL GAUGE/
File: Gauge_Interface.kicad_sch
Title: Battery gauge and Guition interface

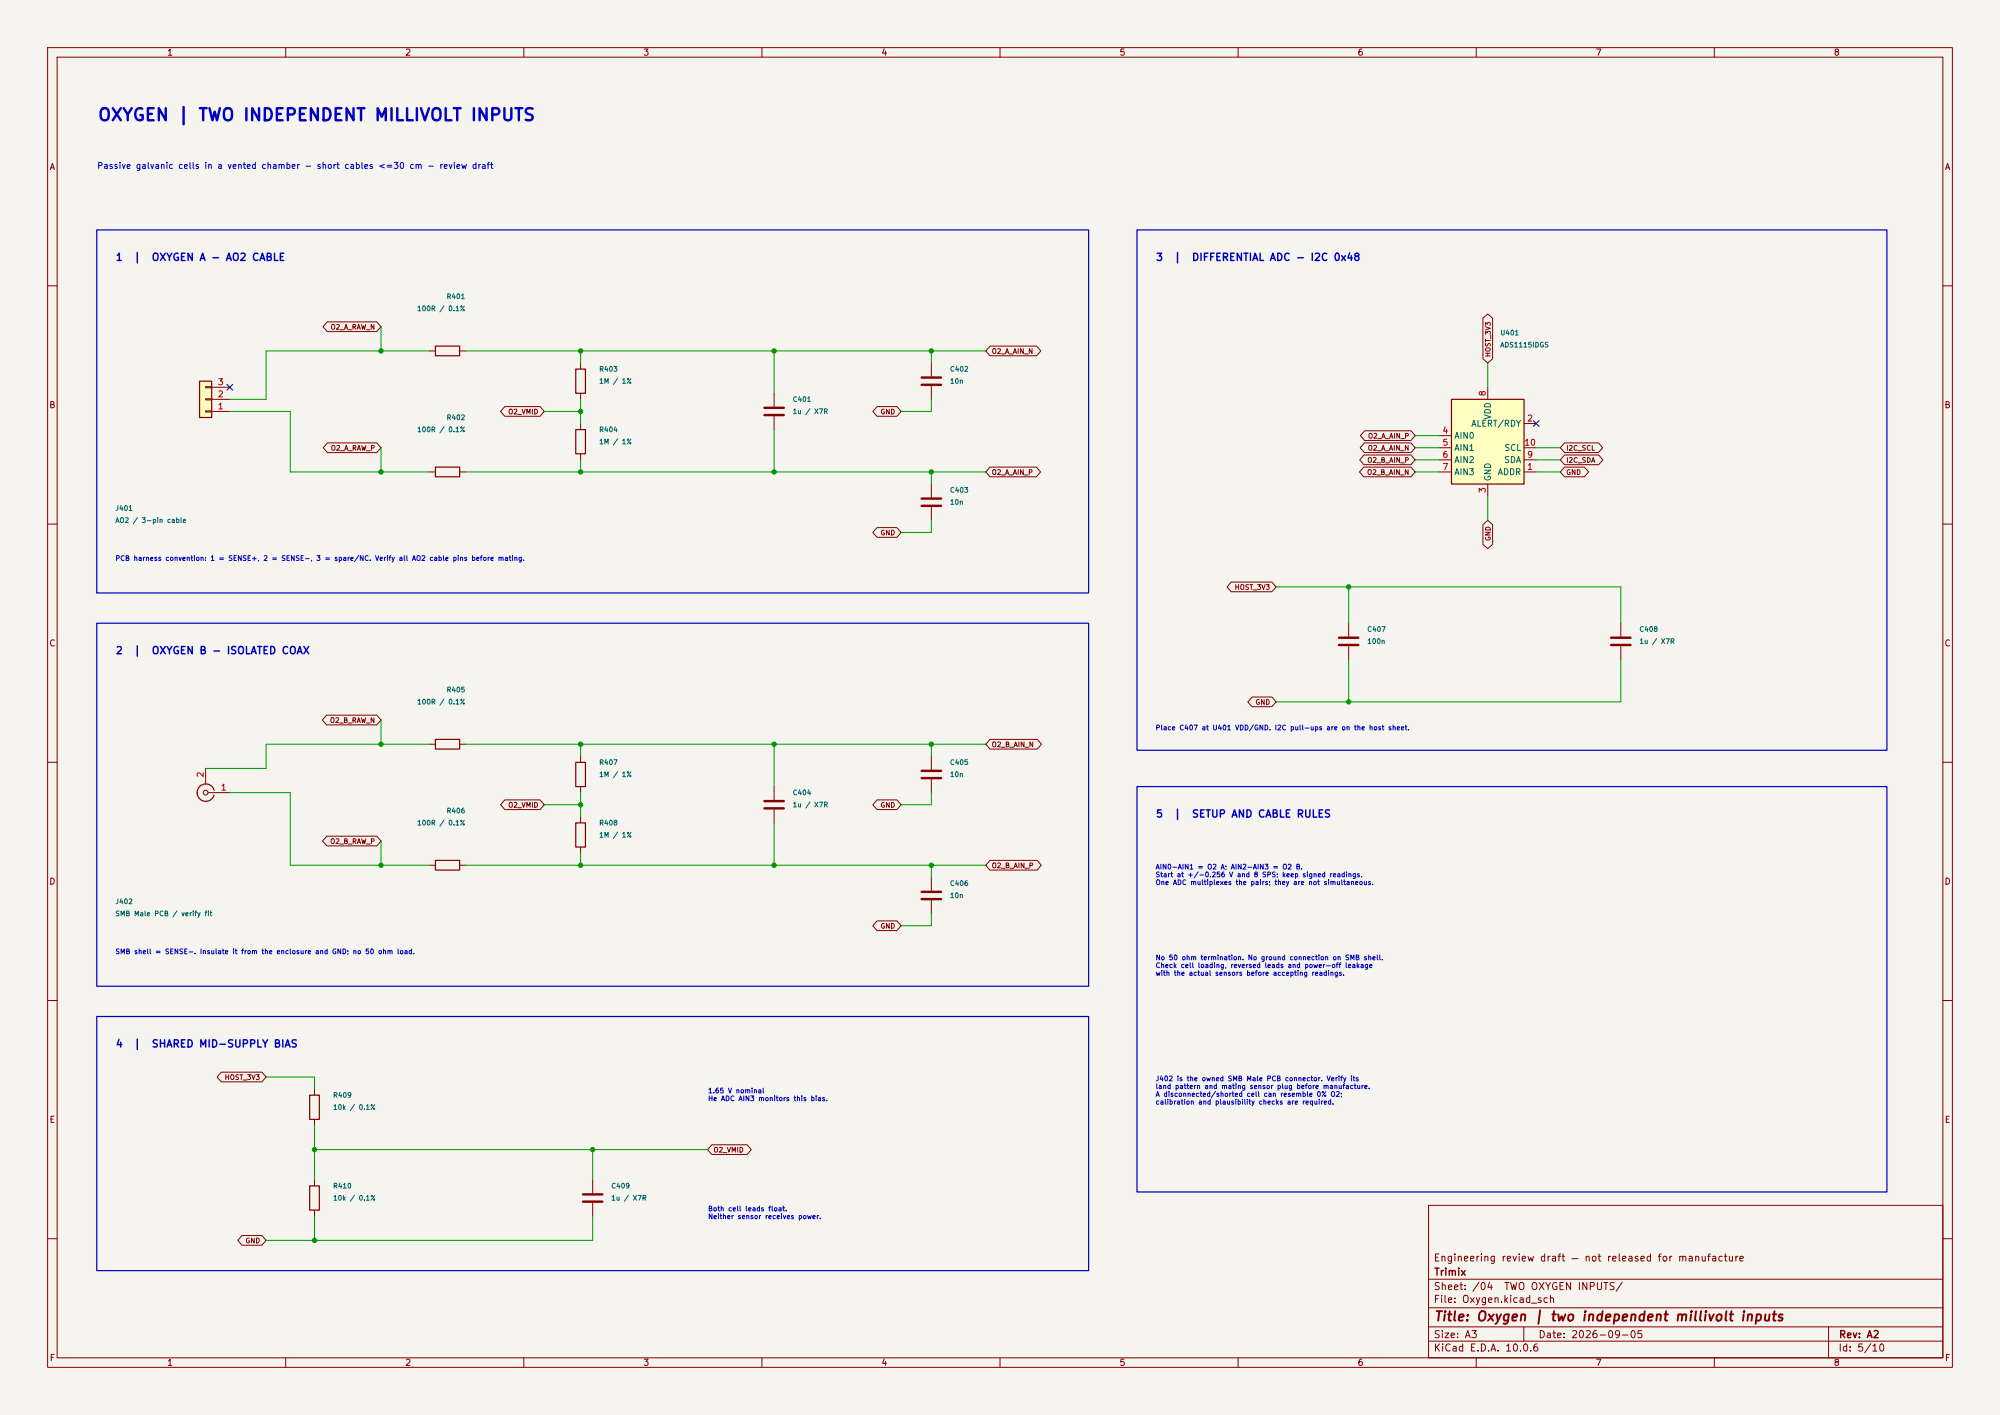
[picture p213: page 5]

Place C407 at U401 VDD/GND. I2C pull-ups are on the host sheet. OXYGEN | TWO INDEPENDENT MILLIVOLT INPUTS

O2_A_AIN_P Passive galvanic cells in a vented chamber - short cables <=30 cm - review draft

land pattern and mating sensor plug before manufacture. A disconnected/shorted cell can resemble 0% O2; calibration and plausibility checks are required. 5 | SETUP AND CABLE RULES

AIN0-AIN1 = O2 A; AIN2-AIN3 = O2 B. Start at +/-0.256 V and 8 SPS; keep signed readings. One ADC multiplexes the pairs; they are not simultaneous. No 50 ohm termination. No ground connection on SMB shell. Check cell loading, reversed leads and power-off leakage with the actual sensors before accepting readings.

SMB shell = SENSE-. Insulate it from the enclosure and GND; no 50 ohm load.

4 | SHARED MID-SUPPLY BIAS

J402 is the owned SMB Male PCB connector. Verify its

Both cell leads float. Neither sensor receives power. 1.65 V nominal He ADC AIN3 monitors this bias.

Engineering review draft — not released for manufacture
Trimix
Sheet: /04 TWO OXYGEN INPUTS/
File: Oxygen.kicad_sch
Title: Oxygen | two independent millivolt inputs

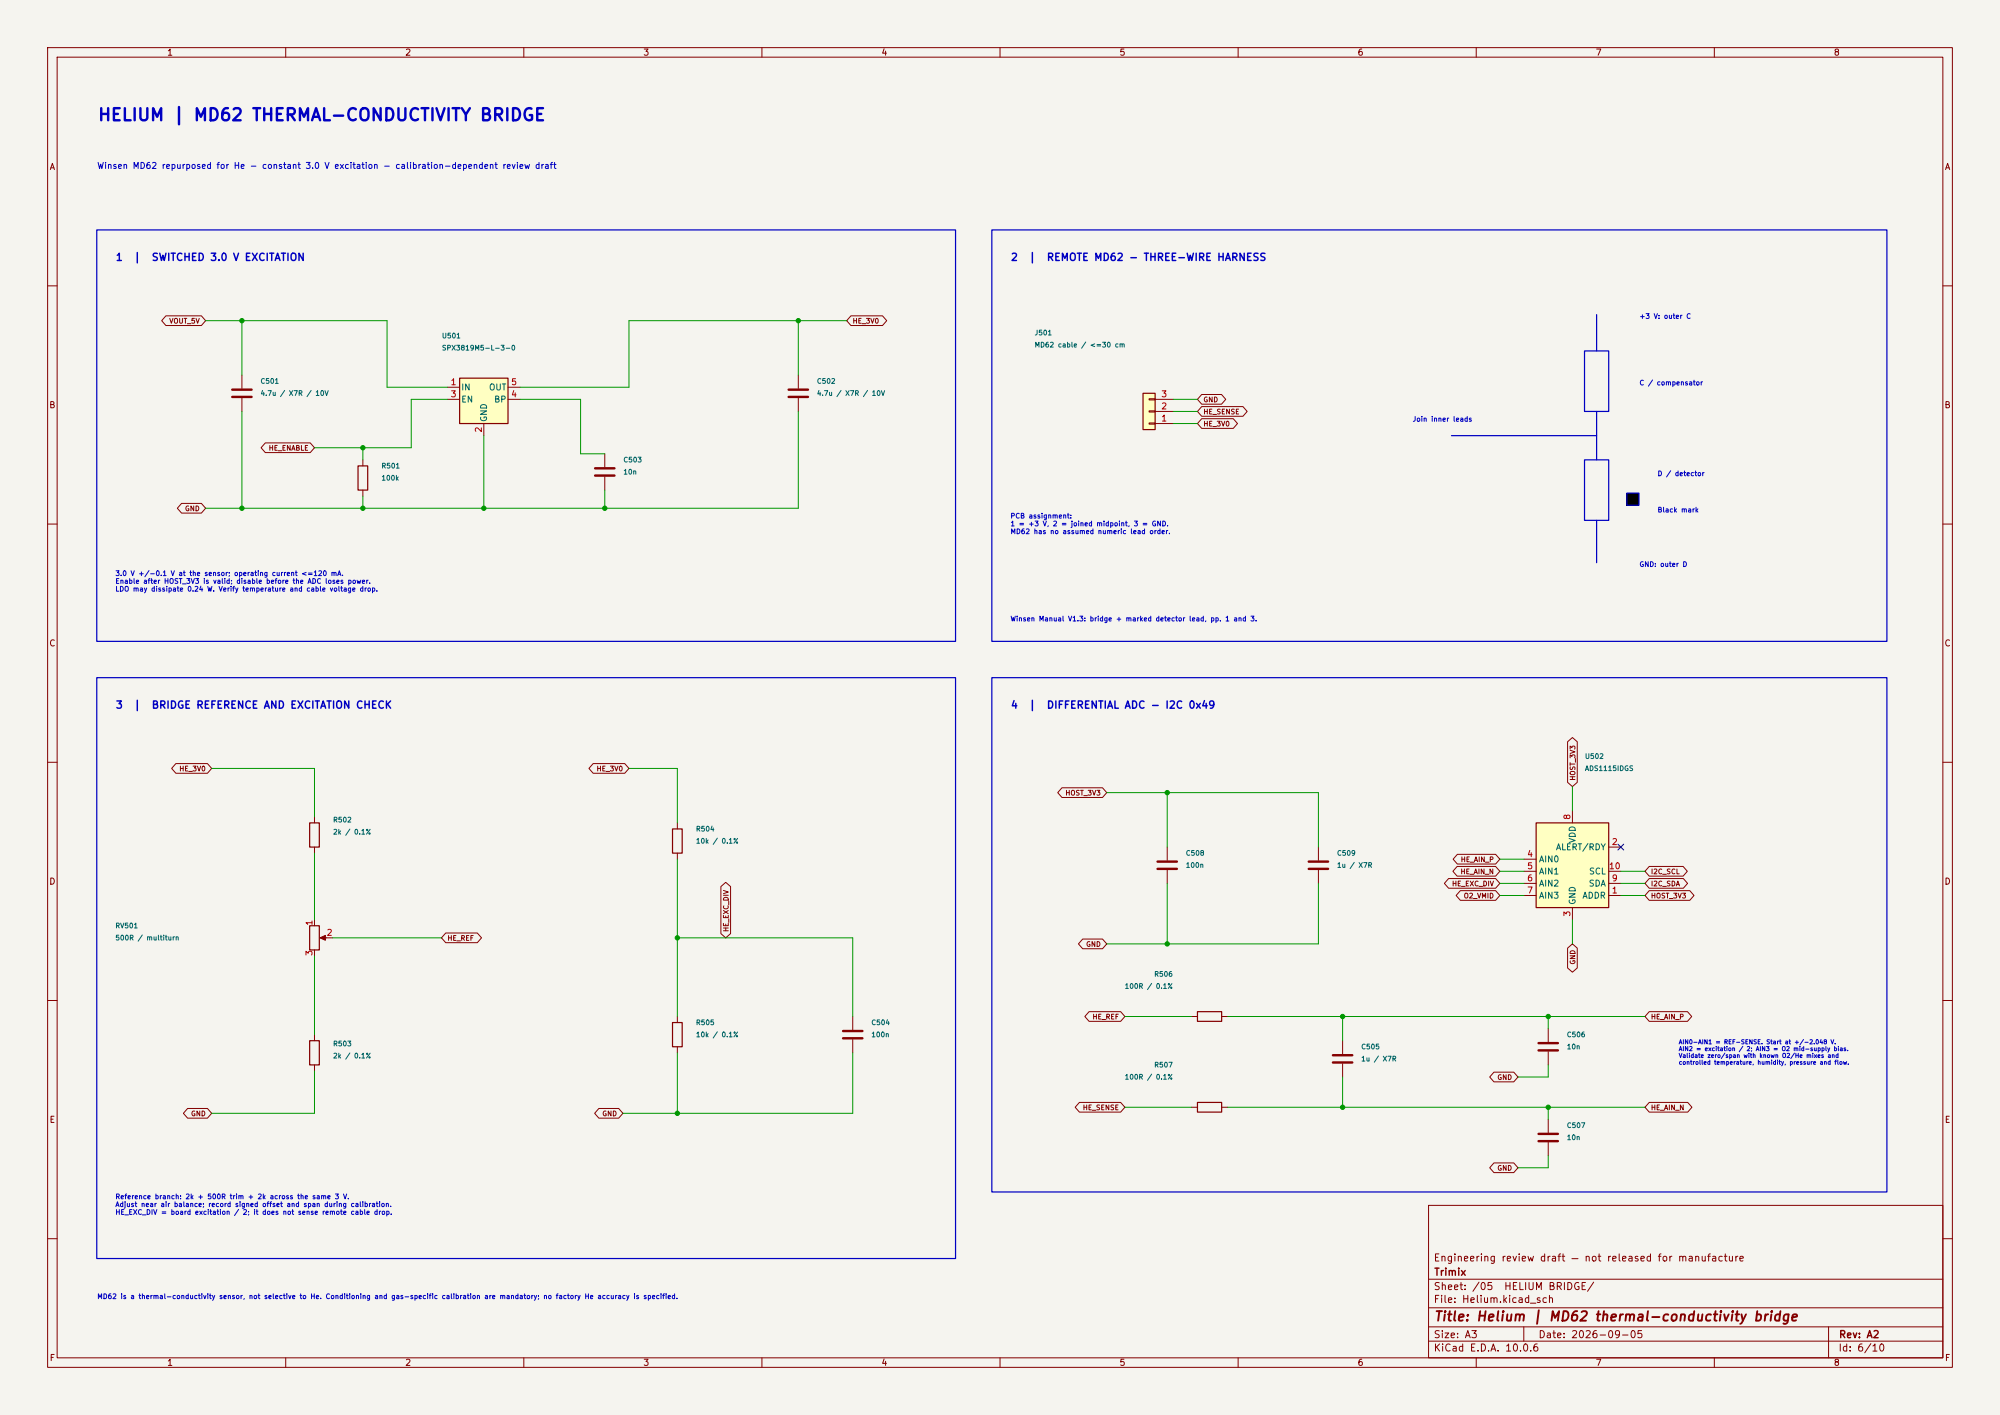
[picture p214: page 6]

Winsen MD62 repurposed for He - constant 3.0 V excitation - calibration-dependent review draft HELIUM | MD62 THERMAL-CONDUCTIVITY BRIDGE

controlled temperature, humidity, pressure and flow. 3 | BRIDGE REFERENCE AND EXCITATION CHECK

AIN0-AIN1 = REF-SENSE. Start at +/-2.048 V. AIN2 = excitation / 2; AIN3 = O2 mid-supply bias. Validate zero/span with known O2/He mixes and

Reference branch: 2k + 500R trim + 2k across the same 3 V. Adjust near air balance; record signed offset and span during calibration. HE_EXC_DIV = board excitation / 2; it does not sense remote cable drop. MD62 is a thermal-conductivity sensor, not selective to He. Conditioning and gas-specific calibration are mandatory; no factory He accuracy is specified.

Engineering review draft — not released for manufacture
Trimix
Sheet: /05 HELIUM BRIDGE/
File: Helium.kicad_sch
Title: Helium | MD62 thermal-conductivity bridge

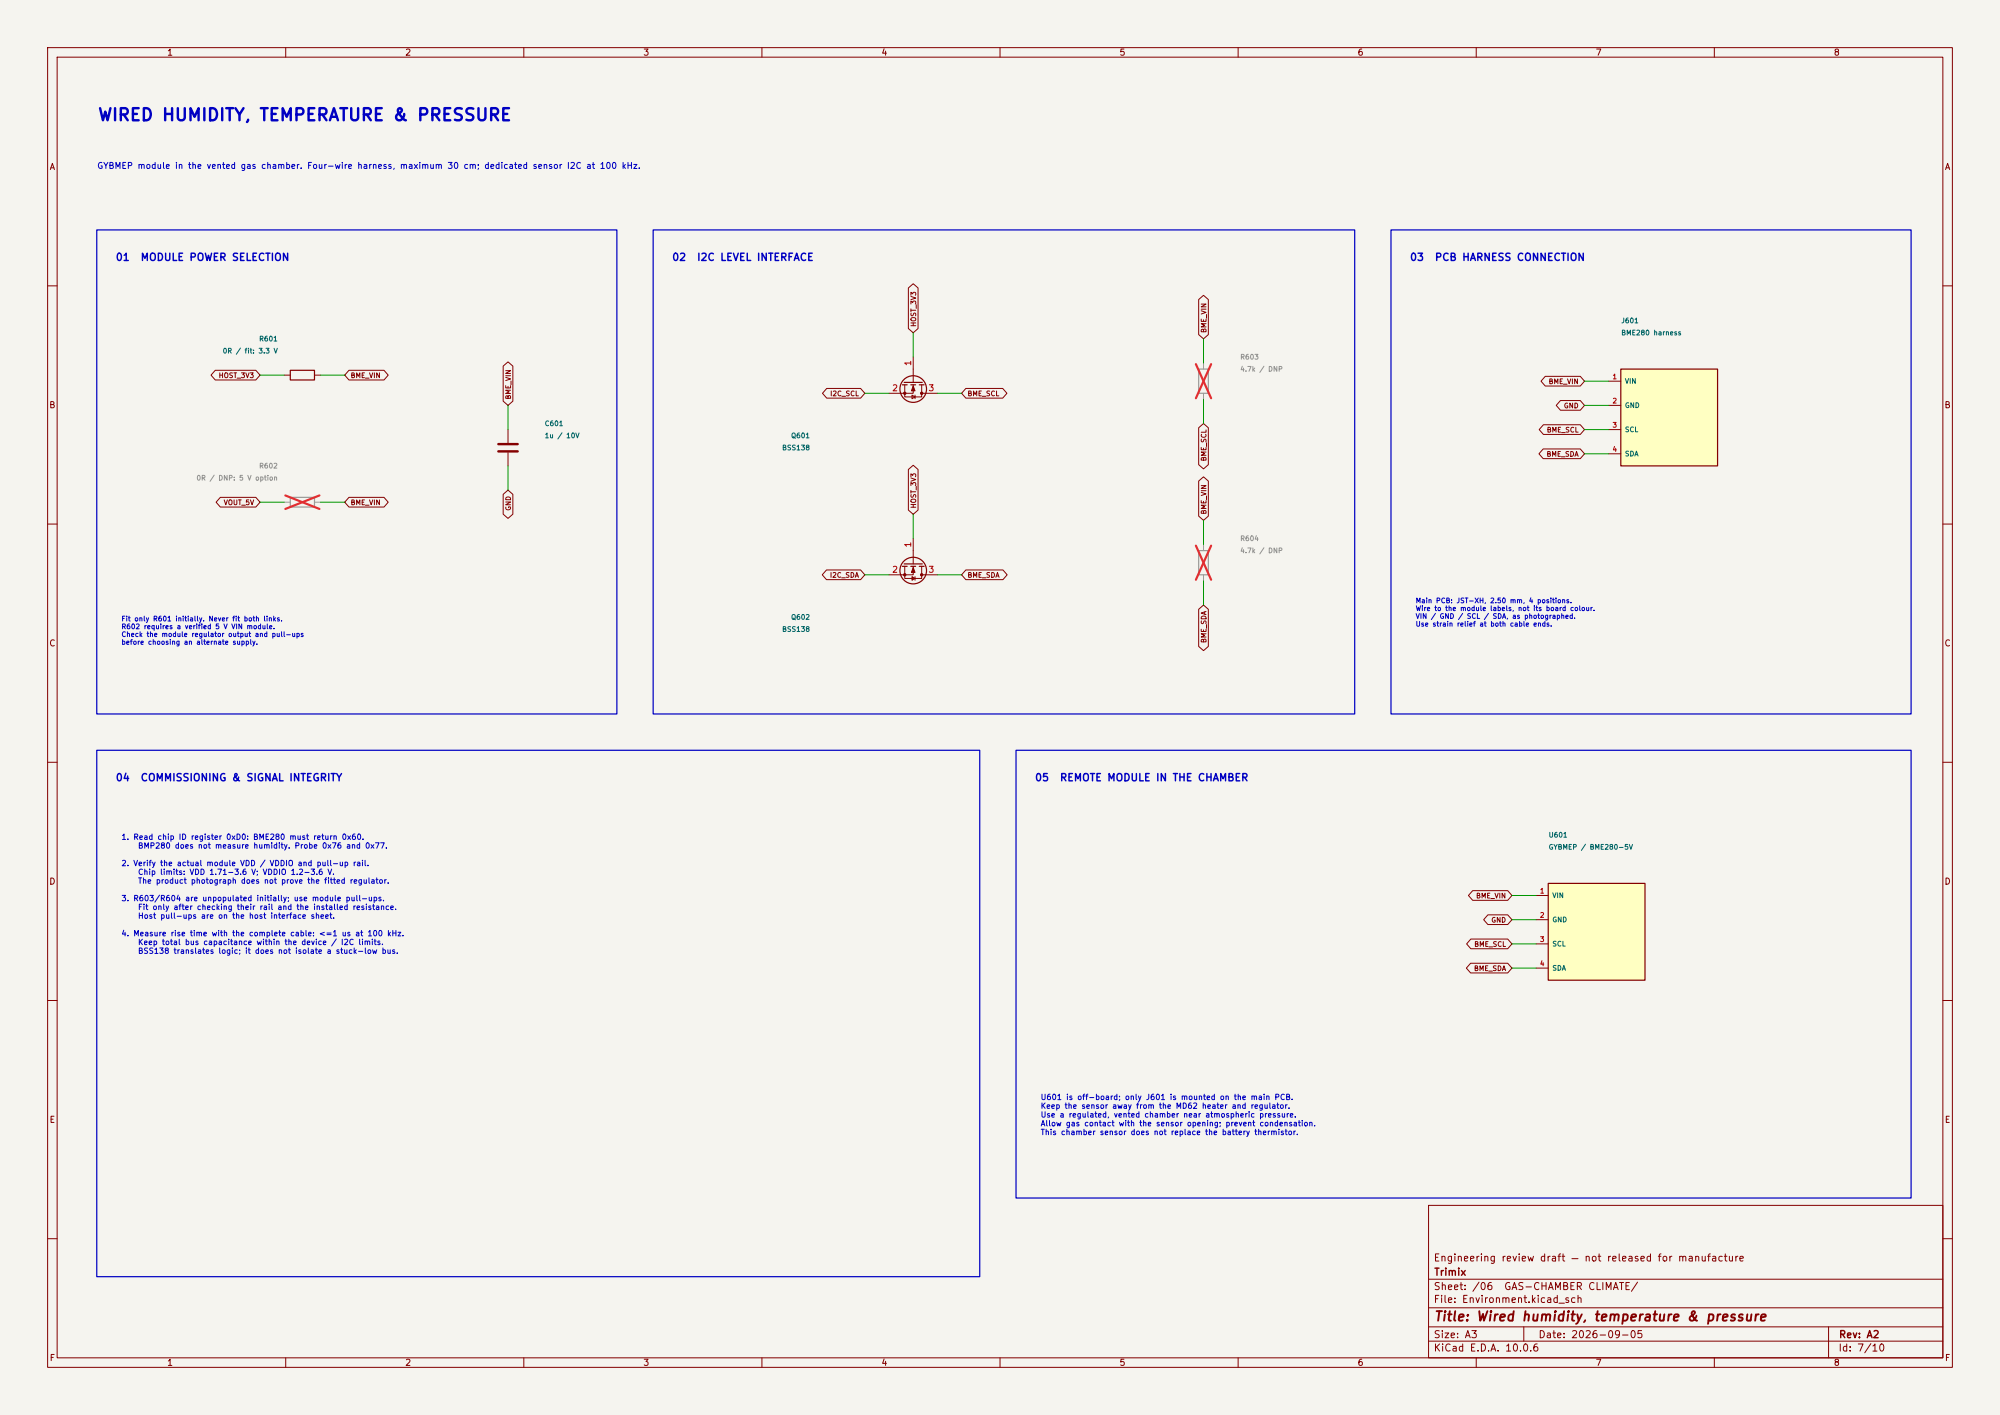
[picture p215: page 7]

WIRED HUMIDITY, TEMPERATURE & PRESSURE

Fit only R601 initially. Never fit both links. R602 requires a verified 5 V VIN module. Check the module regulator output and pull-ups before choosing an alternate supply.

Engineering review draft — not released for manufacture
Trimix
Sheet: /06 GAS-CHAMBER CLIMATE/
File: Environment.kicad_sch
Title: Wired humidity, temperature & pressure

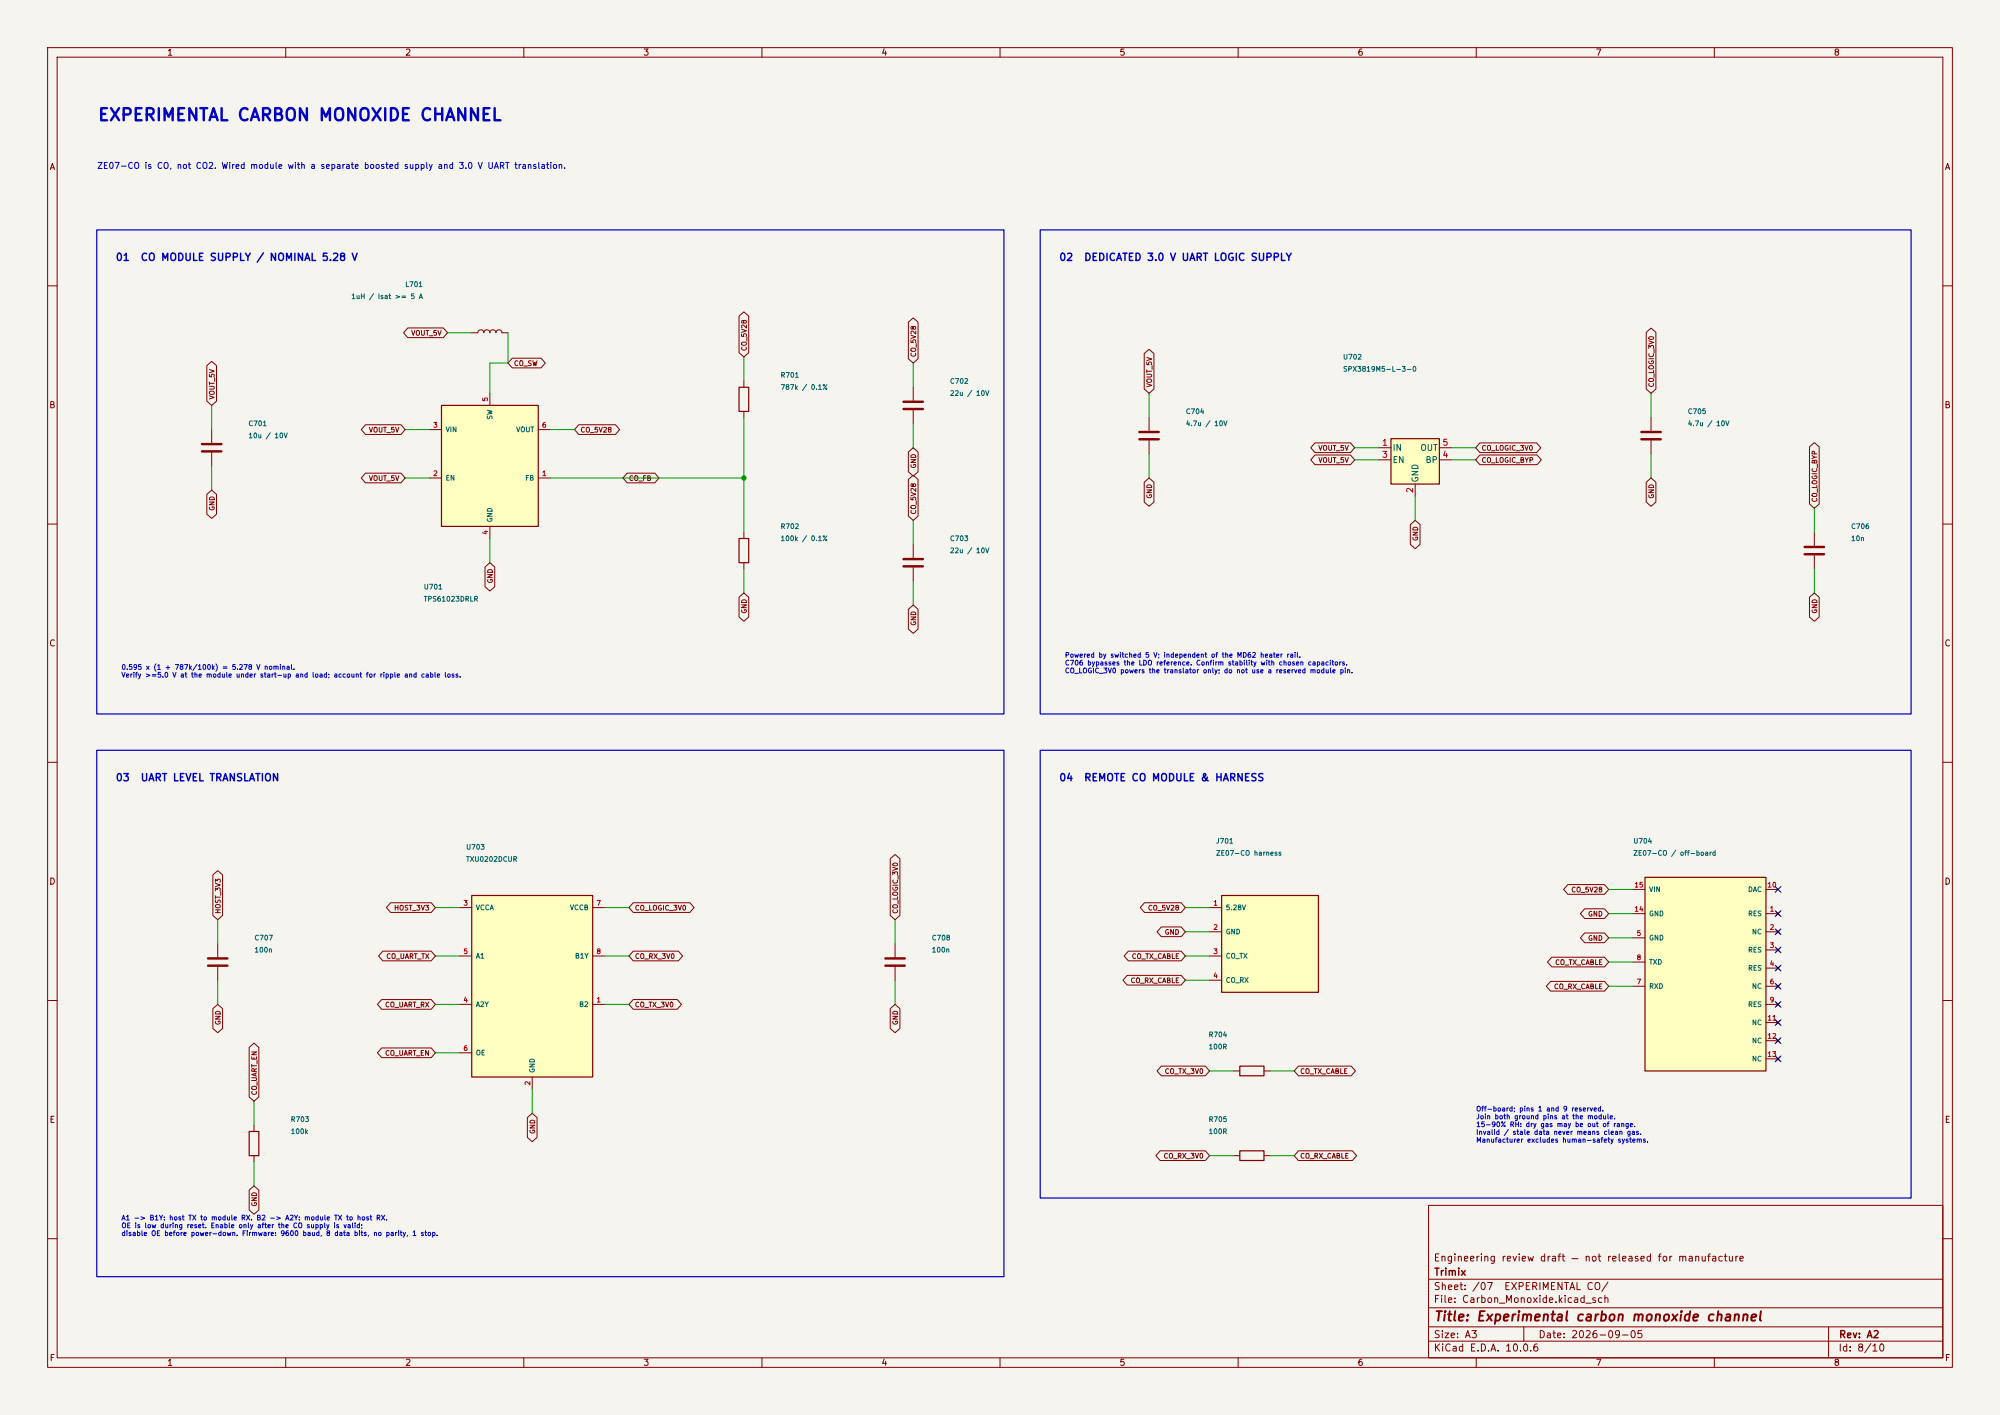
[picture p216: page 8]

ZE07-CO is CO, not CO2. Wired module with a separate boosted supply and 3.0 V UART translation. EXPERIMENTAL CARBON MONOXIDE CHANNEL

01 CO MODULE SUPPLY / NOMINAL 5.28 V

02 DEDICATED 3.0 V UART LOGIC SUPPLY
VOUT_5V VOUT_5V CO_5V28 CO_RX_3V0 GND

Powered by switched 5 V; independent of the MD62 heater rail. C706 bypasses the LDO reference. Confirm stability with chosen capacitors. CO_LOGIC_3V0 powers the translator only; do not use a reserved module pin. 04 REMOTE CO MODULE & HARNESS

0.595 x (1 + 787k/100k) = 5.278 V nominal. Verify >=5.0 V at the module under start-up and load; account for ripple and cable loss.

Invalid / stale data never means clean gas. Manufacturer excludes human-safety systems. A1 -> B1Y: host TX to module RX. B2 -> A2Y: module TX to host RX. OE is low during reset. Enable only after the CO supply is valid; disable OE before power-down. Firmware: 9600 baud, 8 data bits, no parity, 1 stop. 03 UART LEVEL TRANSLATION

Off-board; pins 1 and 9 reserved. Join both ground pins at the module. 15-90% RH: dry gas may be out of range.

Engineering review draft — not released for manufacture
Trimix
Sheet: /07 EXPERIMENTAL CO/
File: Carbon_Monoxide.kicad_sch
Title: Experimental carbon monoxide channel

AB

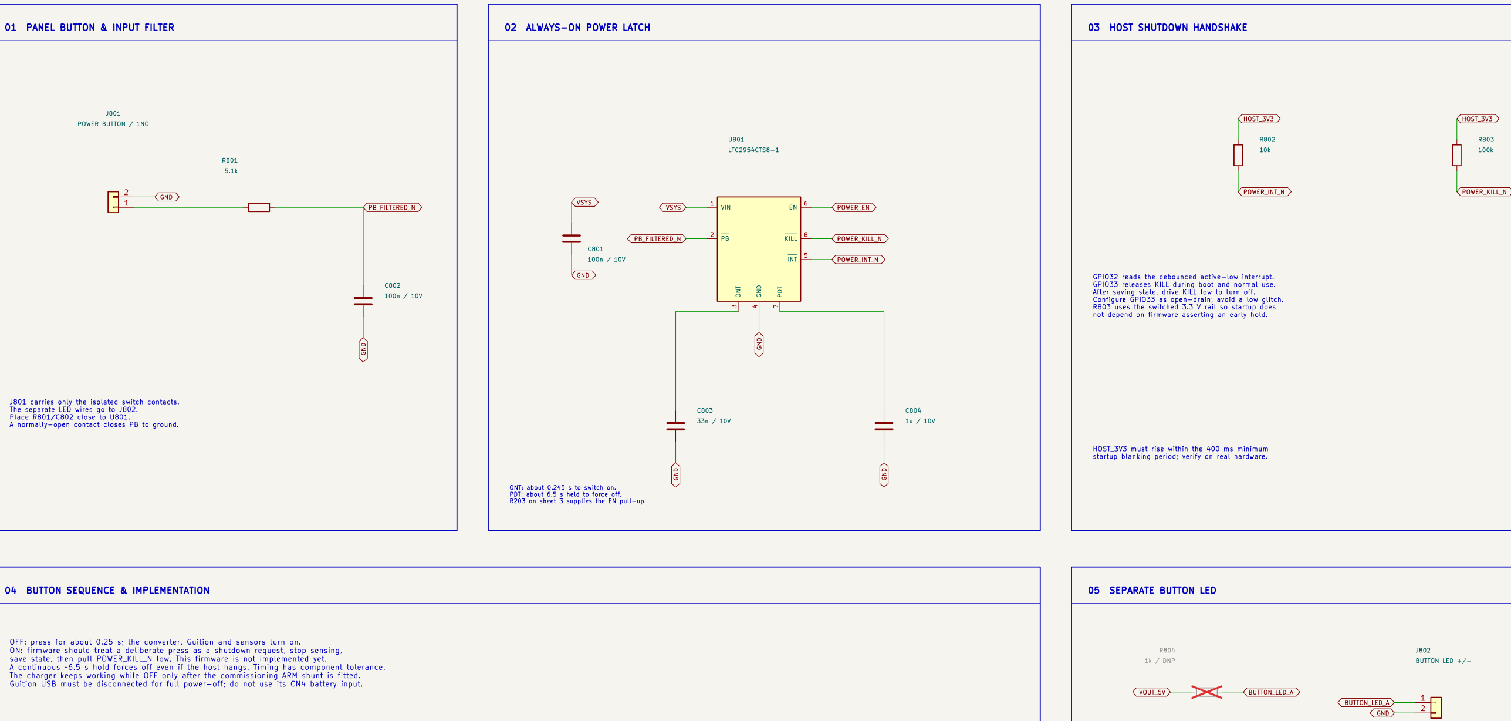
[picture p217: figure]
J801 POWER BUTTON / 1NO; J802 BUTTON LED +/-; 1k / DNP; VIN 1; ONT 3; GND; INT; 6 PDT 7 KILL; LTC2954CTS8-1 C803; 100k GND; VOUT_5V GND; VSYS VSYS; HOST_3V3 GND; POWER_KILL_N; HOST_3V3 POWER_INT_N; POWER_EN; PB_FILTERED_N; BUTTON_LED_A GND; BUTTON_LED_A; 02 ALWAYS-ON POWER LATCH; 03 HOST SHUTDOWN HANDSHAKE; 04 BUTTON SEQUENCE & IMPLEMENTATION; 05 SEPARATE BUTTON LED

C

D

E

AB

C

D

E

## Title: Momentary power button & safe shutdown

File: Power_Control.kicad_sch

Sheet: /08 PUSH-BUTTON ON / OFF/

Trimix

Engineering review draft — not released for manufacture

POWER_INT_N GPIO32 reads the debounced active-low interrupt. GPIO33 releases KILL during boot and normal use. After saving state, drive KILL low to turn off. Configure GPIO33 as open-drain; avoid a low glitch. R803 uses the switched 3.3 V rail so startup does not depend on firmware asserting an early hold. HOST_3V3 must rise within the 400 ms minimum

startup blanking period; verify on real hardware.

R804 initially DNP. Verify the ordered LED voltage, built-in resistor and polarity before fitting a value.

# MOMENTARY POWER BUTTON & SAFE SHUTDOWN

The button switches the 5 V load. The armed charger remains available with the screen and sensors off. 01 PANEL BUTTON & INPUT FILTER

ONT: about 0.245 s to switch on. PDT: about 6.5 s held to force off. R203 on sheet 3 supplies the EN pull-up. J801 carries only the isolated switch contacts. The separate LED wires go to J802. Place R801/C802 close to U801. A normally-open contact closes PB to ground.

OFF: press for about 0.25 s; the converter, Guition and sensors turn on. ON: firmware should treat a deliberate press as a shutdown request, stop sensing, save state, then pull POWER_KILL_N low. This firmware is not implemented yet. A continuous ~6.5 s hold forces off even if the host hangs. Timing has component tolerance. The charger keeps working while OFF only after the commissioning ARM shunt is fitted. Guition USB must be disconnected for full power-off; do not use its CN4 battery input.

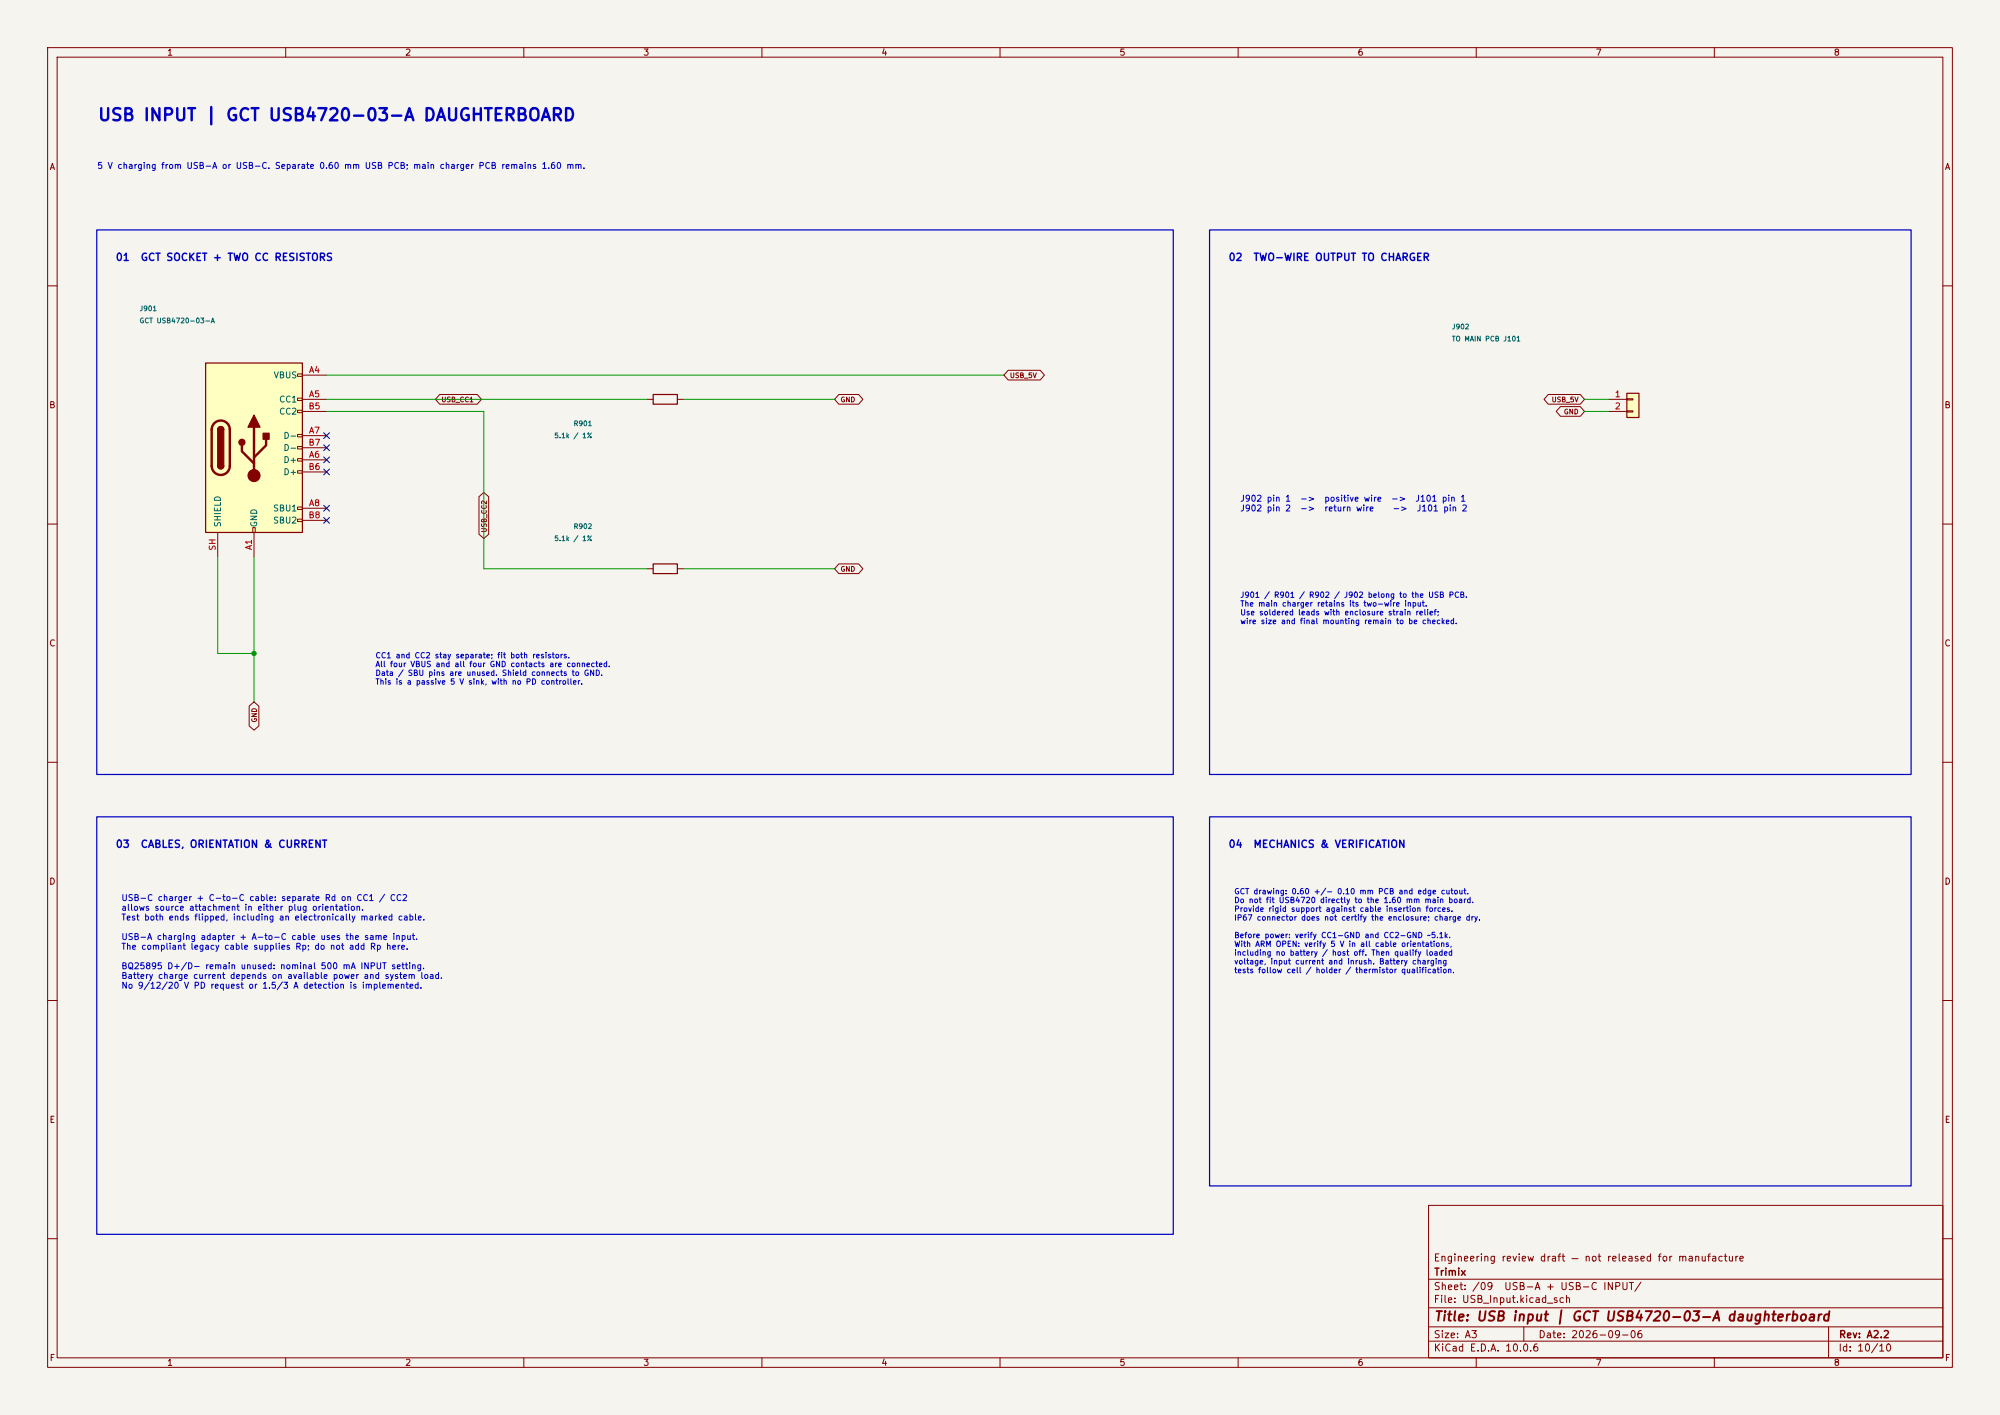
[picture p218: page 10]

USB INPUT | GCT USB4720-03-A DAUGHTERBOARD

5 V charging from USB-A or USB-C. Separate 0.60 mm USB PCB; main charger PCB remains 1.60 mm. 01 GCT SOCKET + TWO CC RESISTORS

02 TWO-WIRE OUTPUT TO CHARGER

J902 pin 1 -> positive wire -> J101 pin 1

J901 / R901 / R902 / J902 belong to the USB PCB. The main charger retains its two-wire input. Use soldered leads with enclosure strain relief; wire size and final mounting remain to be checked. GCT drawing: 0.60 +/- 0.10 mm PCB and edge cutout. Do not fit USB4720 directly to the 1.60 mm main board. Provide rigid support against cable insertion forces.

CC1 and CC2 stay separate; fit both resistors. All four VBUS and all four GND contacts are connected. Data / SBU pins are unused. Shield connects to GND. This is a passive 5 V sink, with no PD controller. USB-C charger + C-to-C cable: separate Rd on CC1 / CC2

allows source attachment in either plug orientation. Test both ends flipped, including an electronically marked cable. USB-A charging adapter + A-to-C cable uses the same input. The compliant legacy cable supplies Rp; do not add Rp here. BQ25895 D+/D- remain unused: nominal 500 mA INPUT setting.

IP67 connector does not certify the enclosure; charge dry. Before power: verify CC1-GND and CC2-GND ~5.1k. With ARM OPEN: verify 5 V in all cable orientations,

including no battery / host off. Then qualify loaded
voltage, input current and inrush. Battery charging
tests follow cell / holder / thermistor qualification.

Battery charge current depends on available power and system load. No 9/12/20 V PD request or 1.5/3 A detection is implemented.

Engineering review draft — not released for manufacture
Trimix
Sheet: /09 USB-A + USB-C INPUT/
File: USB_Input.kicad_sch
Title: USB input | GCT USB4720-03-A daughterboard
