magnus188/trimix-analysator/hardware/pcb/verification/power/Trimix_Power.pdf

1 | 2 | 3 | 4 | 5 | 6 | 7 | 8

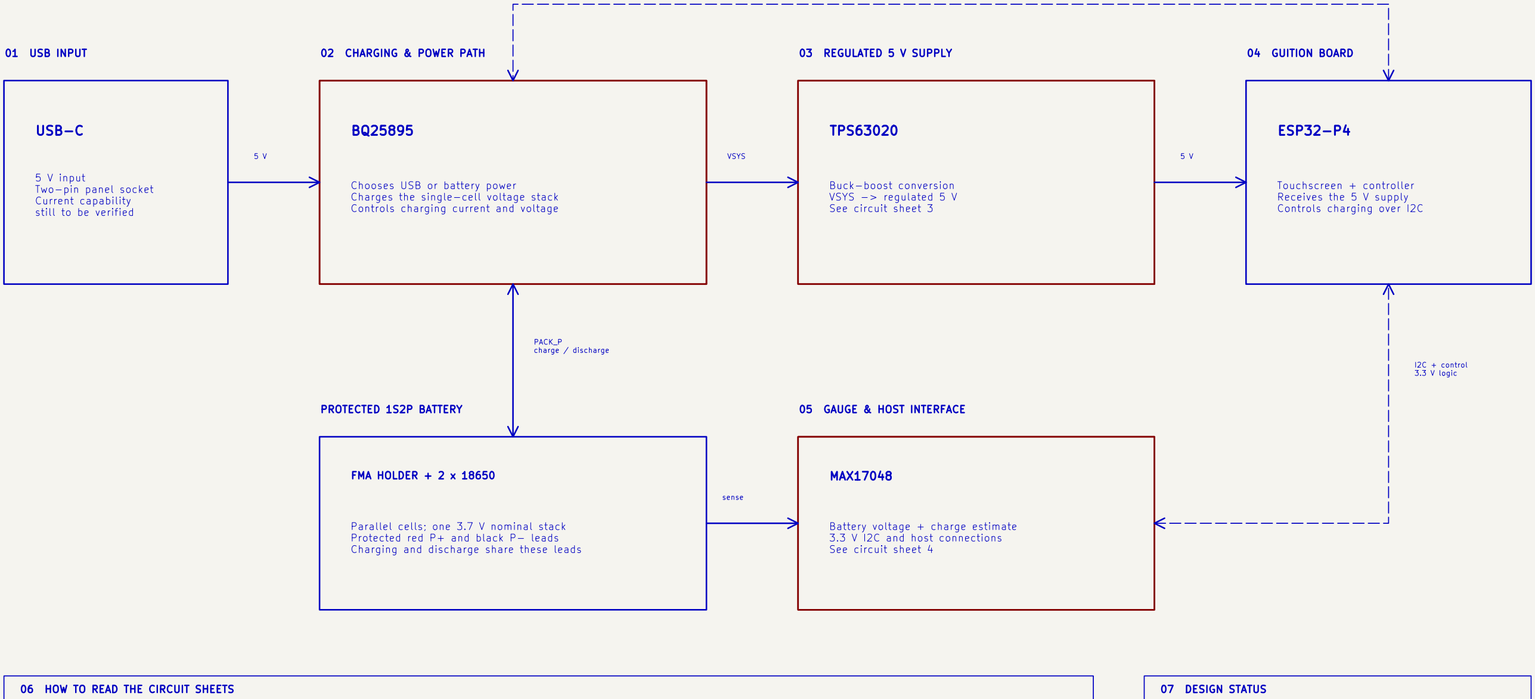
[picture p219: figure]
Receives the 5 V supply Controls charging over I2C; 07 DESIGN STATUS; PROTECTED 1S2P BATTERY; FMA HOLDER + 2 x 18650; Parallel cells; one 3.7 V nominal stack Protected red P+ and black P- leads; USB-C; 03 REGULATED 5 V SUPPLY; TPS63020; Buck-boost conversion VSYS -> regulated 5 V See circuit sheet 3; 06 HOW TO READ THE CIRCUIT SHEETS; PACK_P charge / discharge; I2C + control 3.3 V logic; 05 GAUGE & HOST INTERFACE; MAX17048; Battery voltage + charge estimate 3.3 V I2C and host connections See circuit sheet 4; VSYS Chooses USB or battery power; Charges the single-cell voltage stack Controls charging current and voltage; ESP32-P4; 5 V input Two-pin panel socket Current capability still to be verified

1 | 2 | 3 | 4 | 5 | 6 | 7 | 8

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
Size: A3 | Rev: P1.1 | F Date: 2026-09-05
KiCad E.D.A. 10.0.6 | Id: 1/4

## Title: Trimix power system - replacement schematic

### File: Trimix_Power.kicad_sch

### Sheet: /

Trimix

TRIMIX / POWER ELECTRONICS / SHEET 1 OF 4 | Touchscreen + controller

Review draft; not released for fabrication.
USB input, cells and final parts need verification. Charging currently requires an active host.

## Charging and discharge share these leads

# Power system overview

1. Each outlined section performs one job. Read its title before tracing individual wires.
2. Matching net labels are connected electrically, including across different sheets.
3. Component prefixes: U = IC, R = resistor, C = capacitor, L = inductor, J = connector.
4. A dot joins crossing wires. A cross on a pin means deliberately unconnected.
5. DNP means the component is drawn but not fitted in the initial assembly.
Overview: solid arrows show power/sensing; dashed arrows show host communication. These arrows show function; the detailed sheets contain the actual wiring.
Read from left to right. Double-click a numbered circuit sheet, or select it in the Hierarchy Navigator and press Enter. 01 USB INPUT | Host control: I2C + ALLOW_CHG
sense 02 CHARGING & POWER PATH | 04 GUITION BOARD

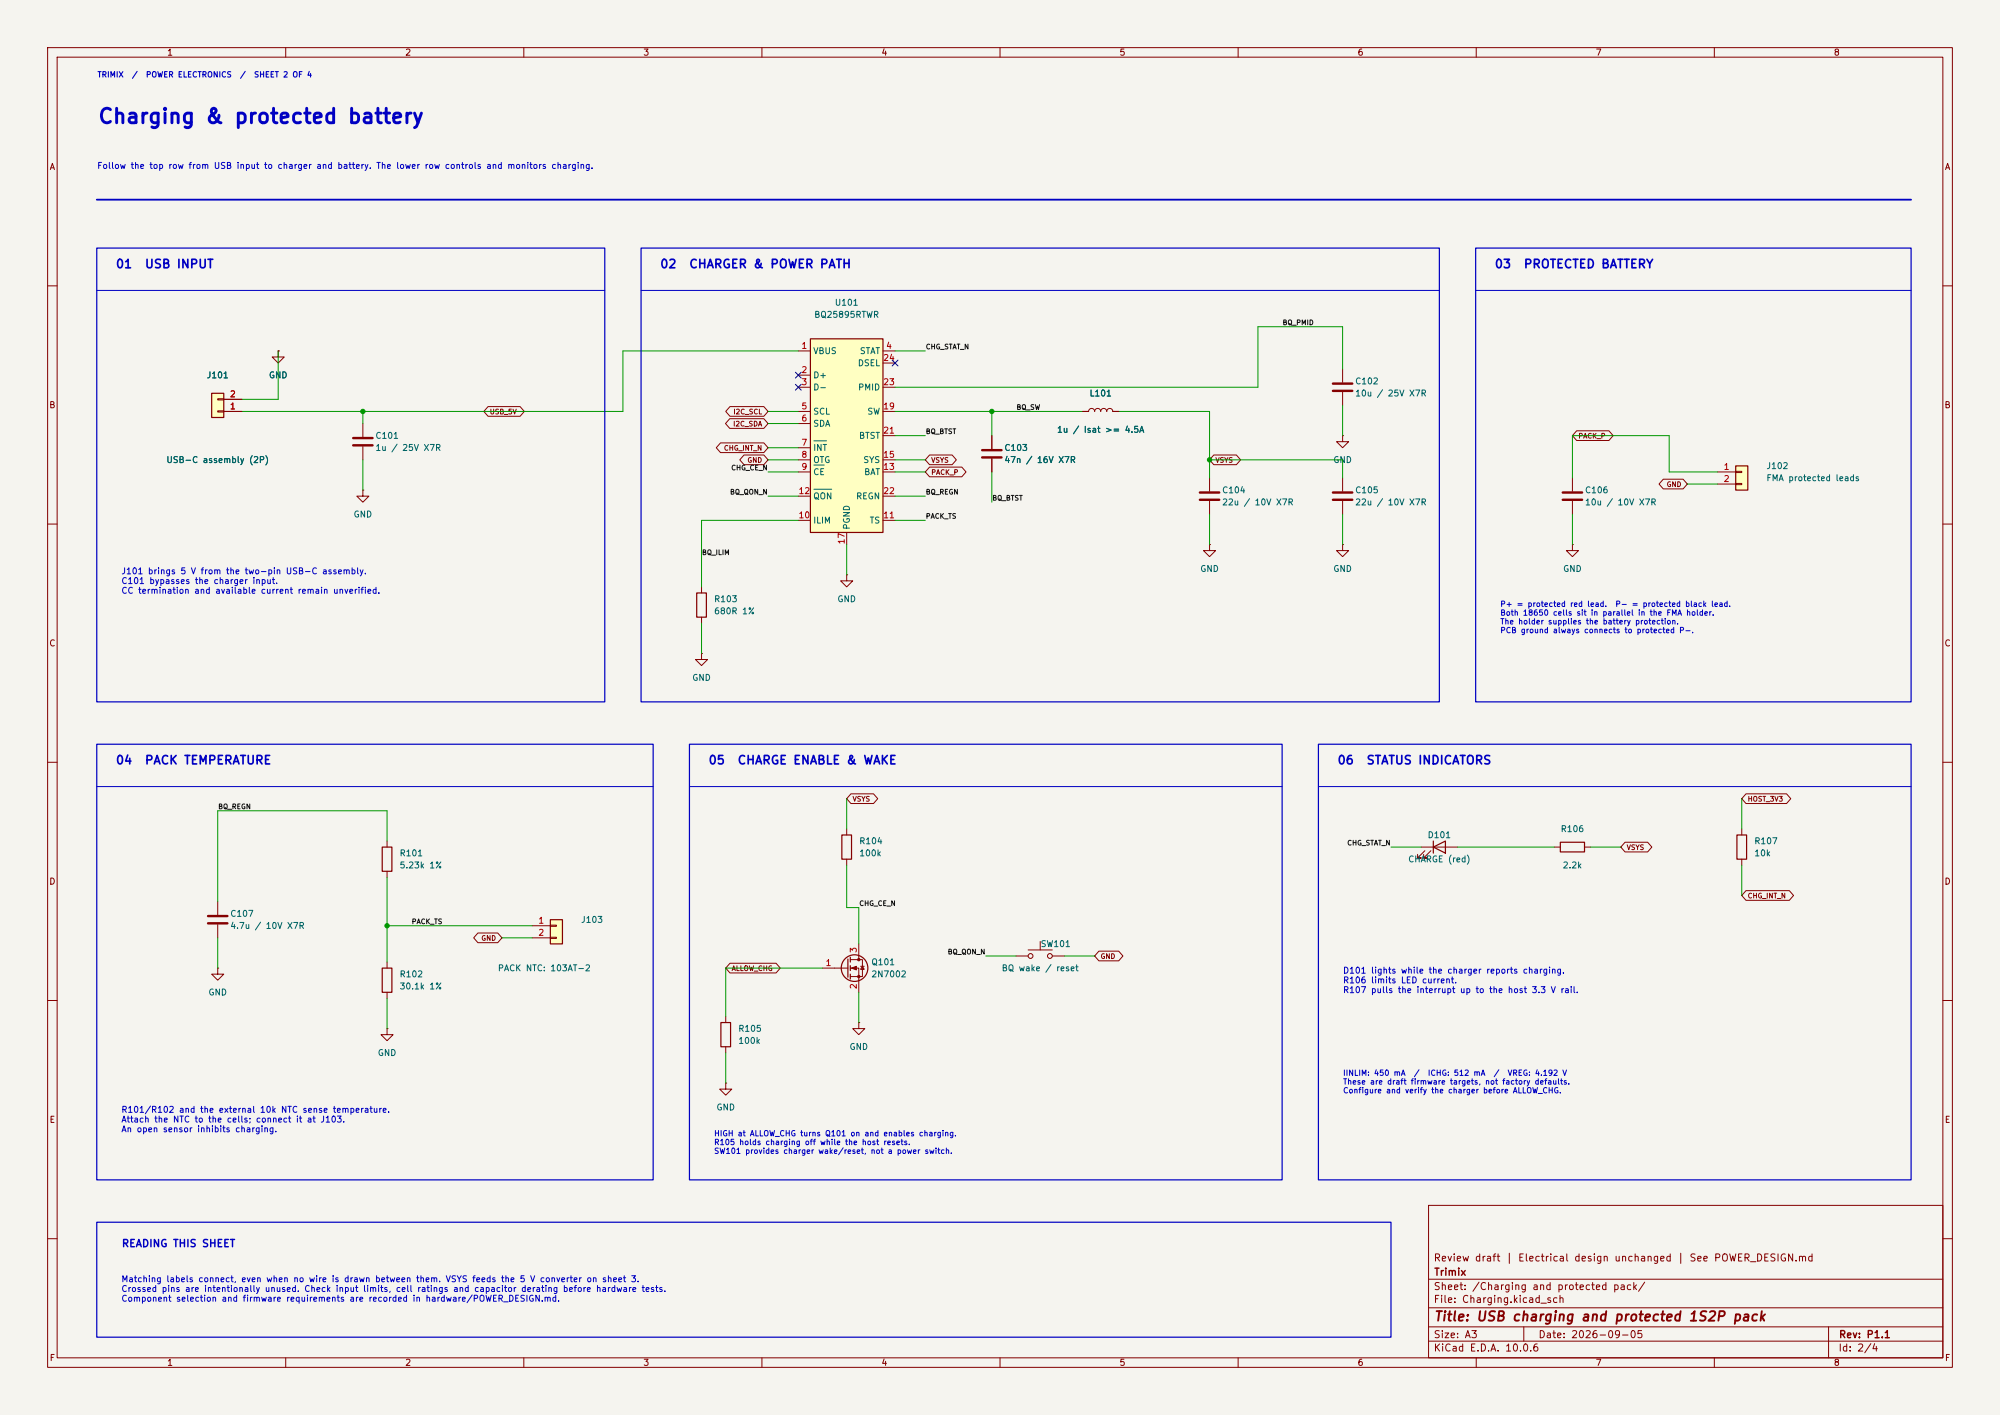
[picture p220: page 2]

TRIMIX / POWER ELECTRONICS / SHEET 2 OF 4 01 USB INPUT

J101 brings 5 V from the two-pin USB-C assembly. C101 bypasses the charger input. CC termination and available current remain unverified. Charging & protected battery

02 CHARGER & POWER PATH
SW 19 BTST 21 REGN 22 PMID 23 DSEL 24 U101 BQ25895RTWR

D101 lights while the charger reports charging. R106 limits LED current. R107 pulls the interrupt up to the host 3.3 V rail.

IINLIM: 450 mA / ICHG: 512 mA / VREG: 4.192 V
These are draft firmware targets, not factory defaults. Configure and verify the charger before ALLOW_CHG.

Review draft | Electrical design unchanged | See POWER_DESIGN.md
Trimix
Sheet: /Charging and protected pack/
File: Charging.kicad_sch
Title: USB charging and protected 1S2P pack

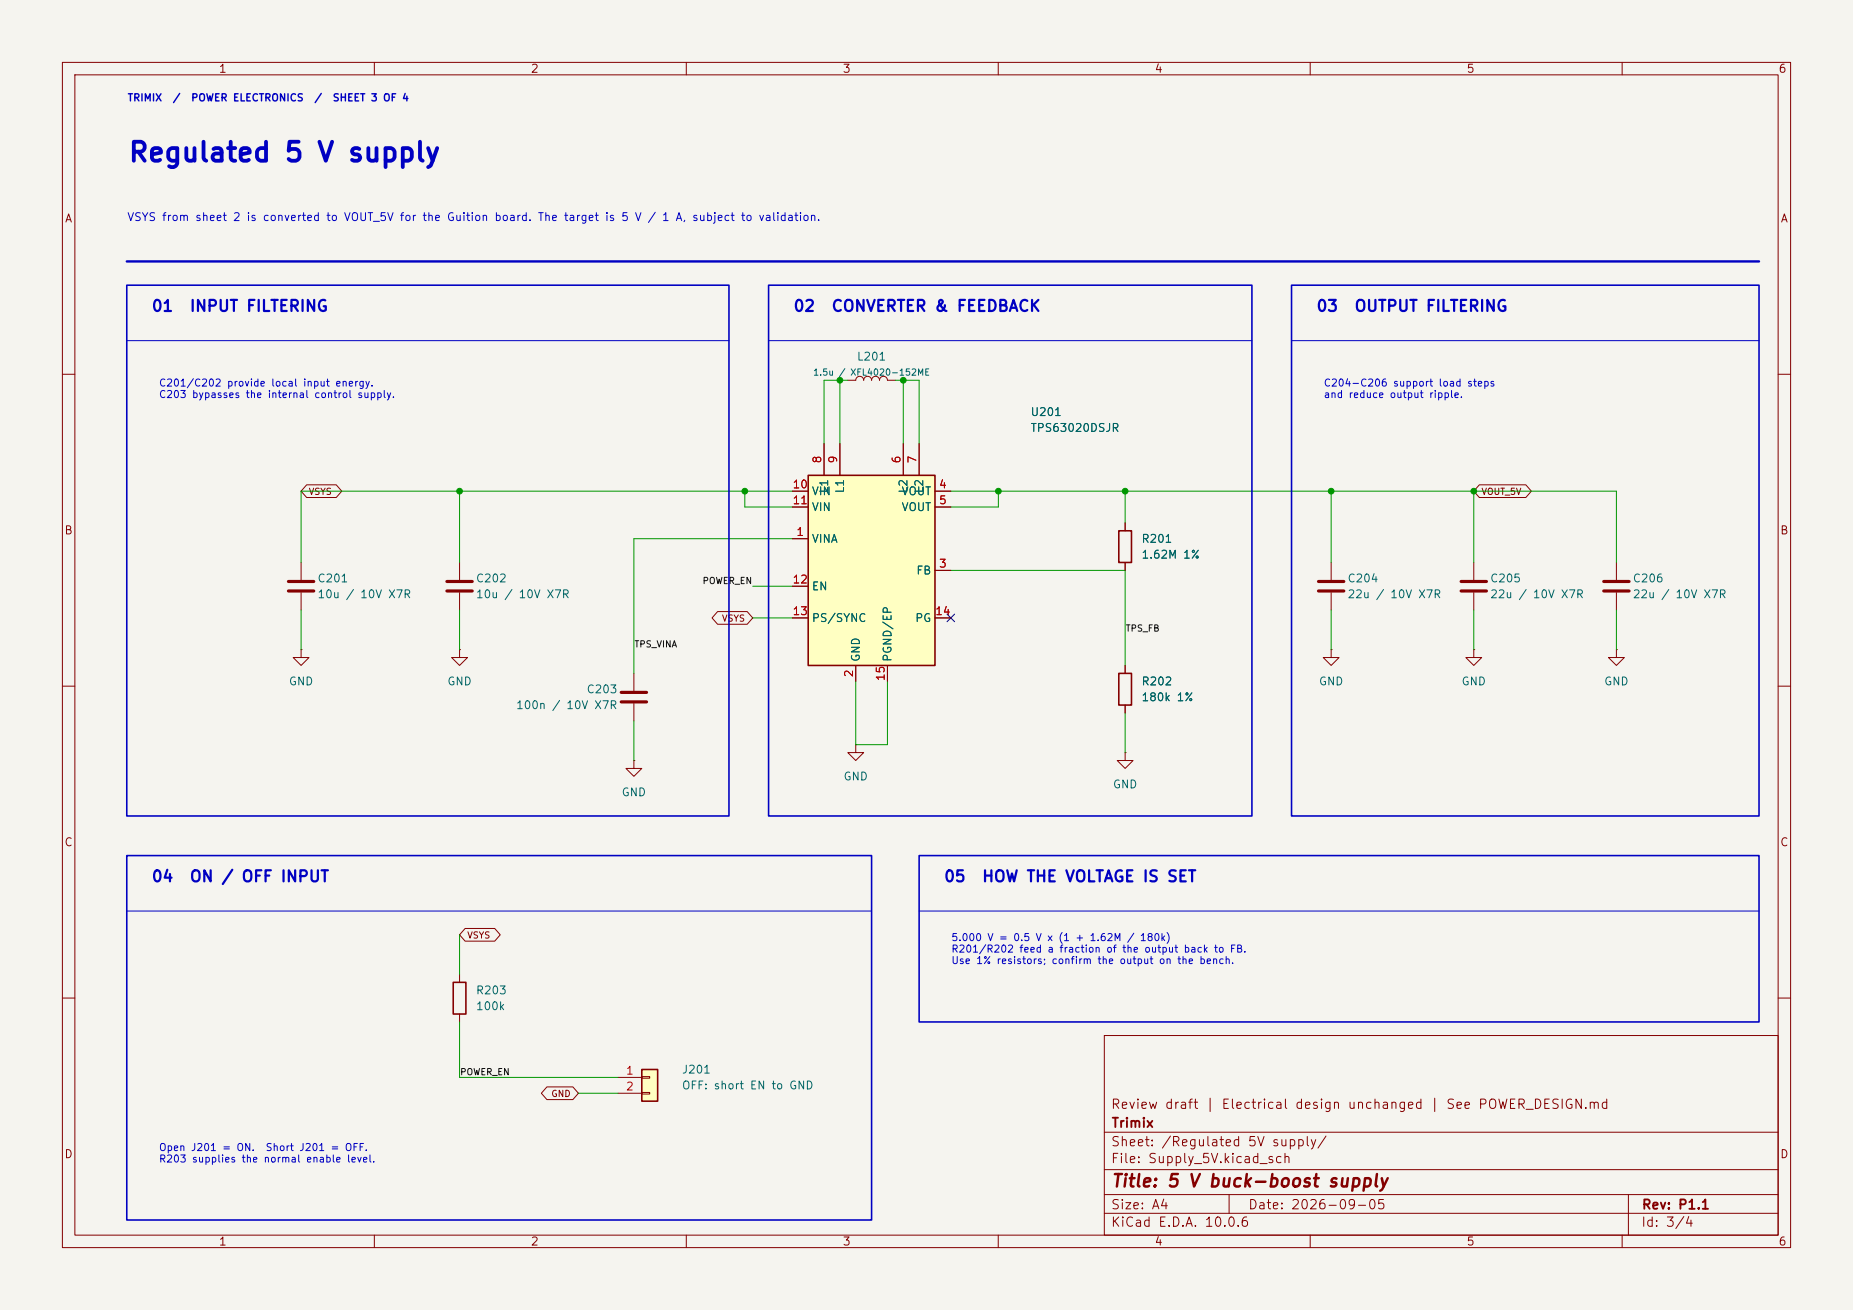
[picture p221: page 3]

POWER_EN VSYS from sheet 2 is converted to VOUT_5V for the Guition board. The target is 5 V / 1 A, subject to validation.

C201/C202 provide local input energy. C203 bypasses the internal control supply.

C204-C206 support load steps and reduce output ripple.

Open J201 = ON. Short J201 = OFF. R203 supplies the normal enable level. 04 ON / OFF INPUT

R201/R202 feed a fraction of the output back to FB. Use 1% resistors; confirm the output on the bench. 05 HOW THE VOLTAGE IS SET

J201 OFF: short EN to GND

Review draft | Electrical design unchanged | See POWER_DESIGN.md
Trimix
Sheet: /Regulated 5V supply/
File: Supply_5V.kicad_sch
Title: 5 V buck-boost supply

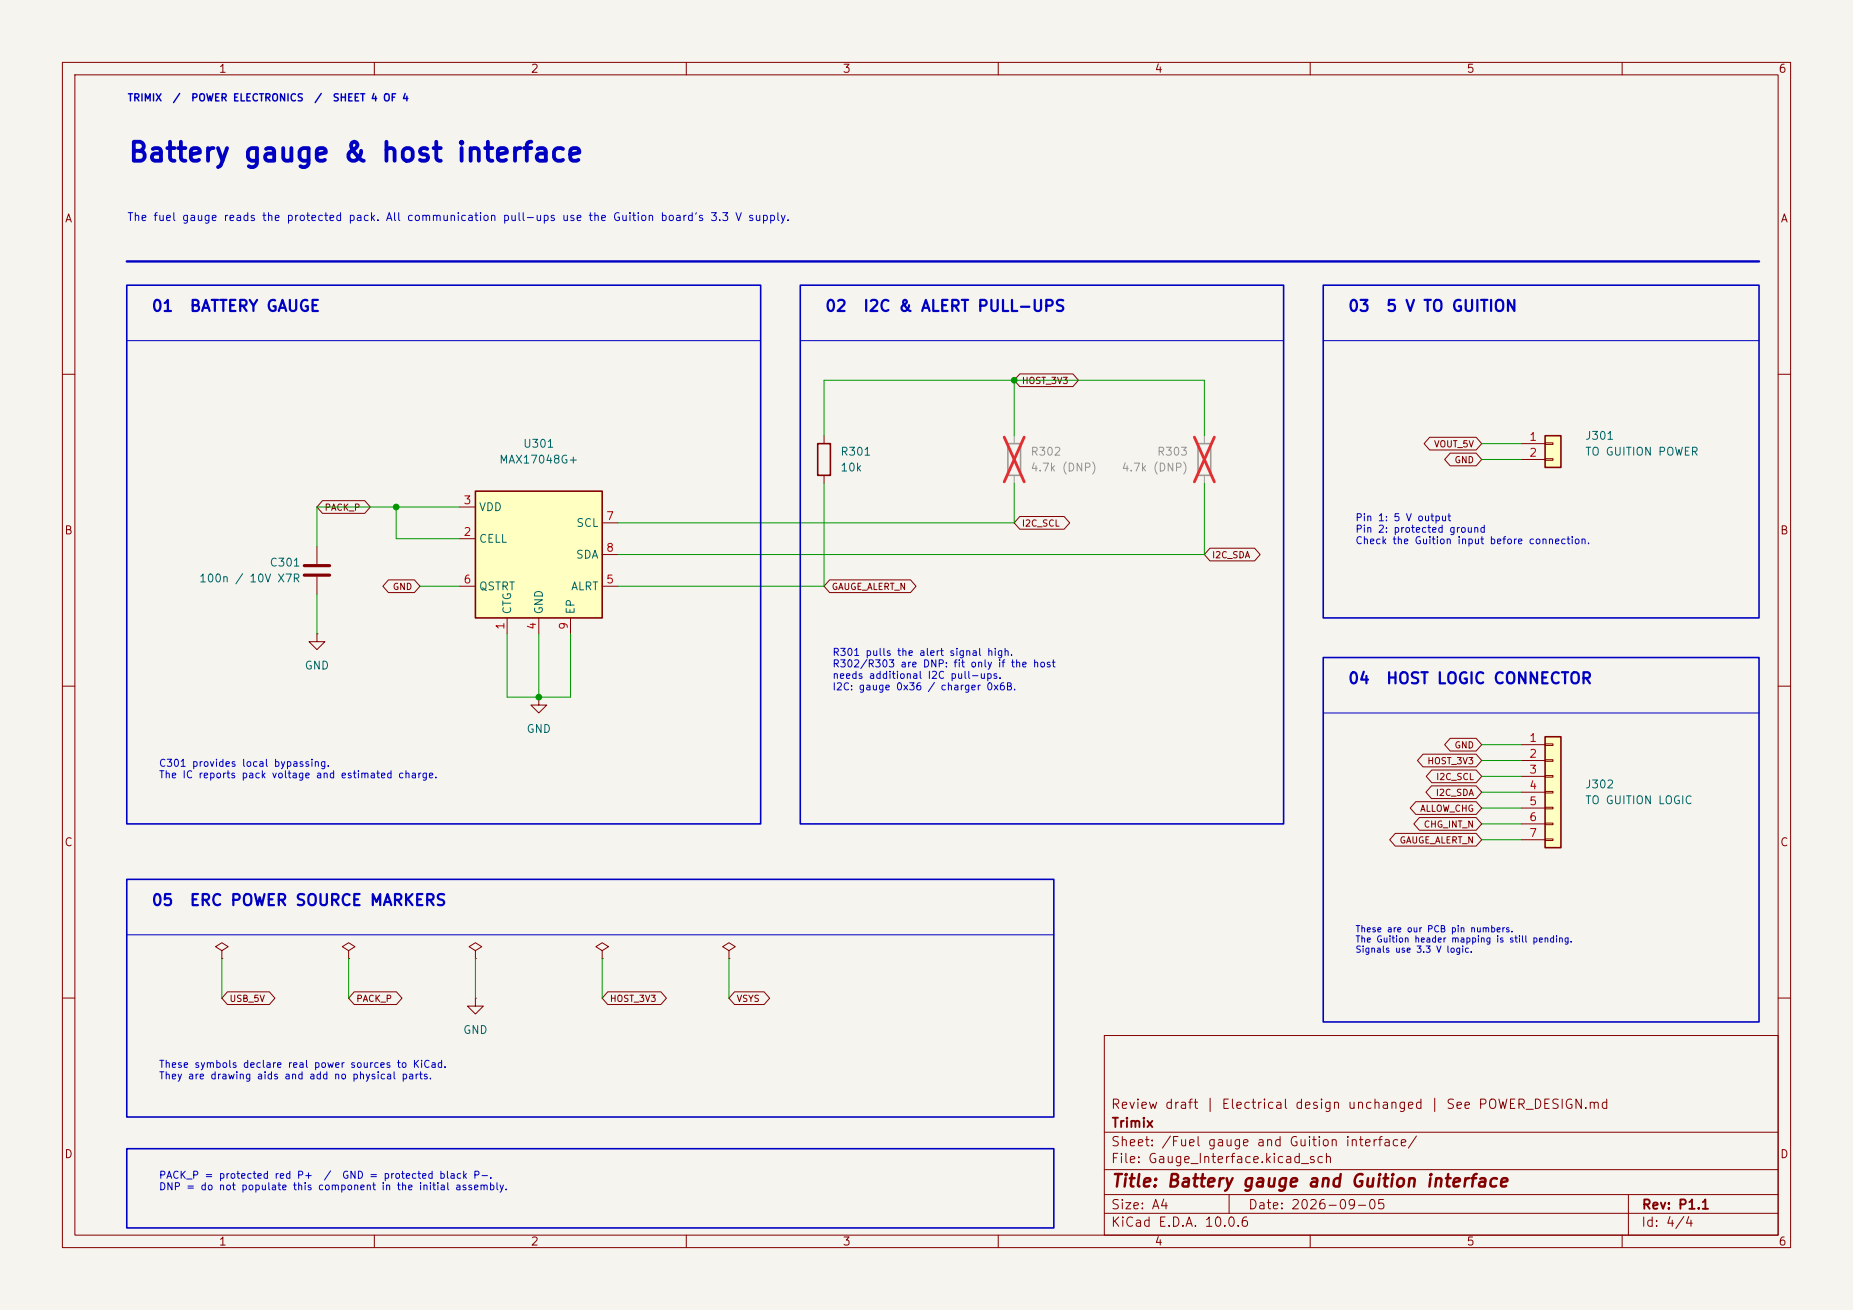
[picture p222: page 4]

TRIMIX / POWER ELECTRONICS / SHEET 4 OF 4
Battery gauge & host interface

The fuel gauge reads the protected pack. All communication pull-ups use the Guition board's 3.3 V supply.

Review draft | Electrical design unchanged | See POWER_DESIGN.md CTG

R301 pulls the alert signal high.
R302/R303 are DNP: fit only if the host needs additional I2C pull-ups.

05 ERC POWER SOURCE MARKERS

These symbols declare real power sources to KiCad. They are drawing aids and add no physical parts.

Trimix
Sheet: /Fuel gauge and Guition interface/
File: Gauge_Interface.kicad_sch
Title: Battery gauge and Guition interface
