magnus188/trimix-analysator/hardware/cad/rev04/verification/pdf-render/page-2.png

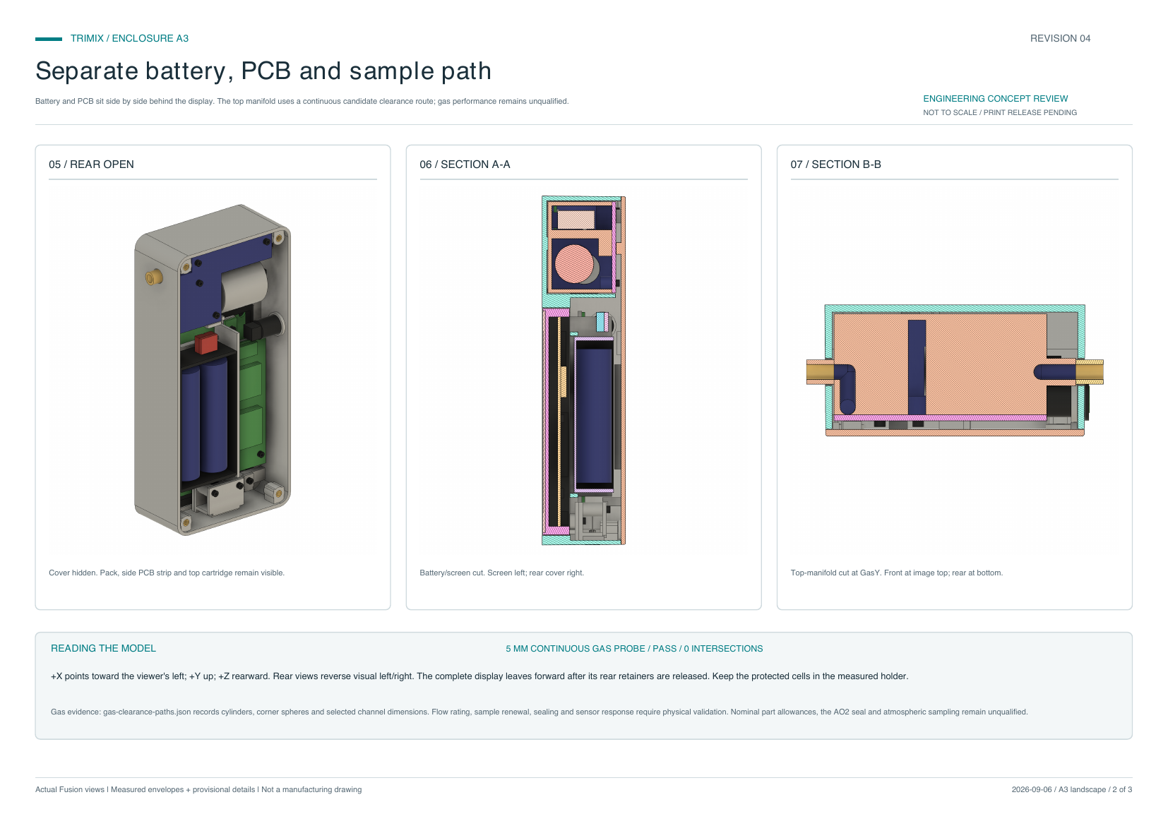
hardware/cad/rev04/verification/pdf-render/page-2.png
