magnus188/trimix-analysator/hardware/pcb/integration/verification/source-review/bq-62.png

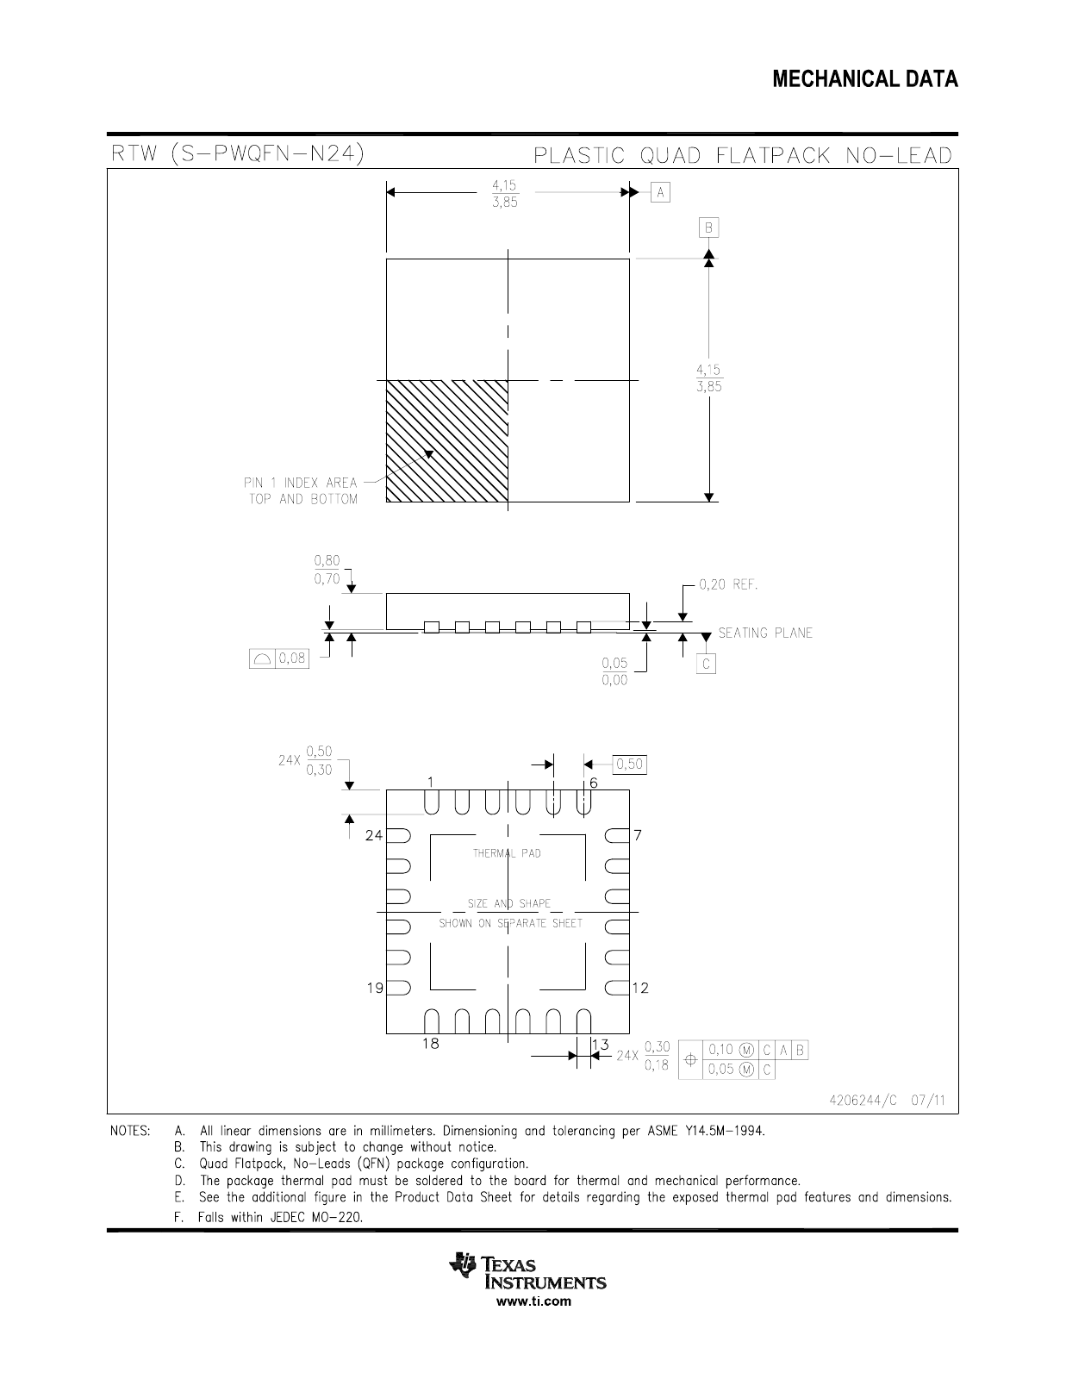
hardware/pcb/integration/verification/source-review/bq-62.png
