magnus188/trimix-analysator/hardware/pcb/integration/verification/source-review/bq-64.png

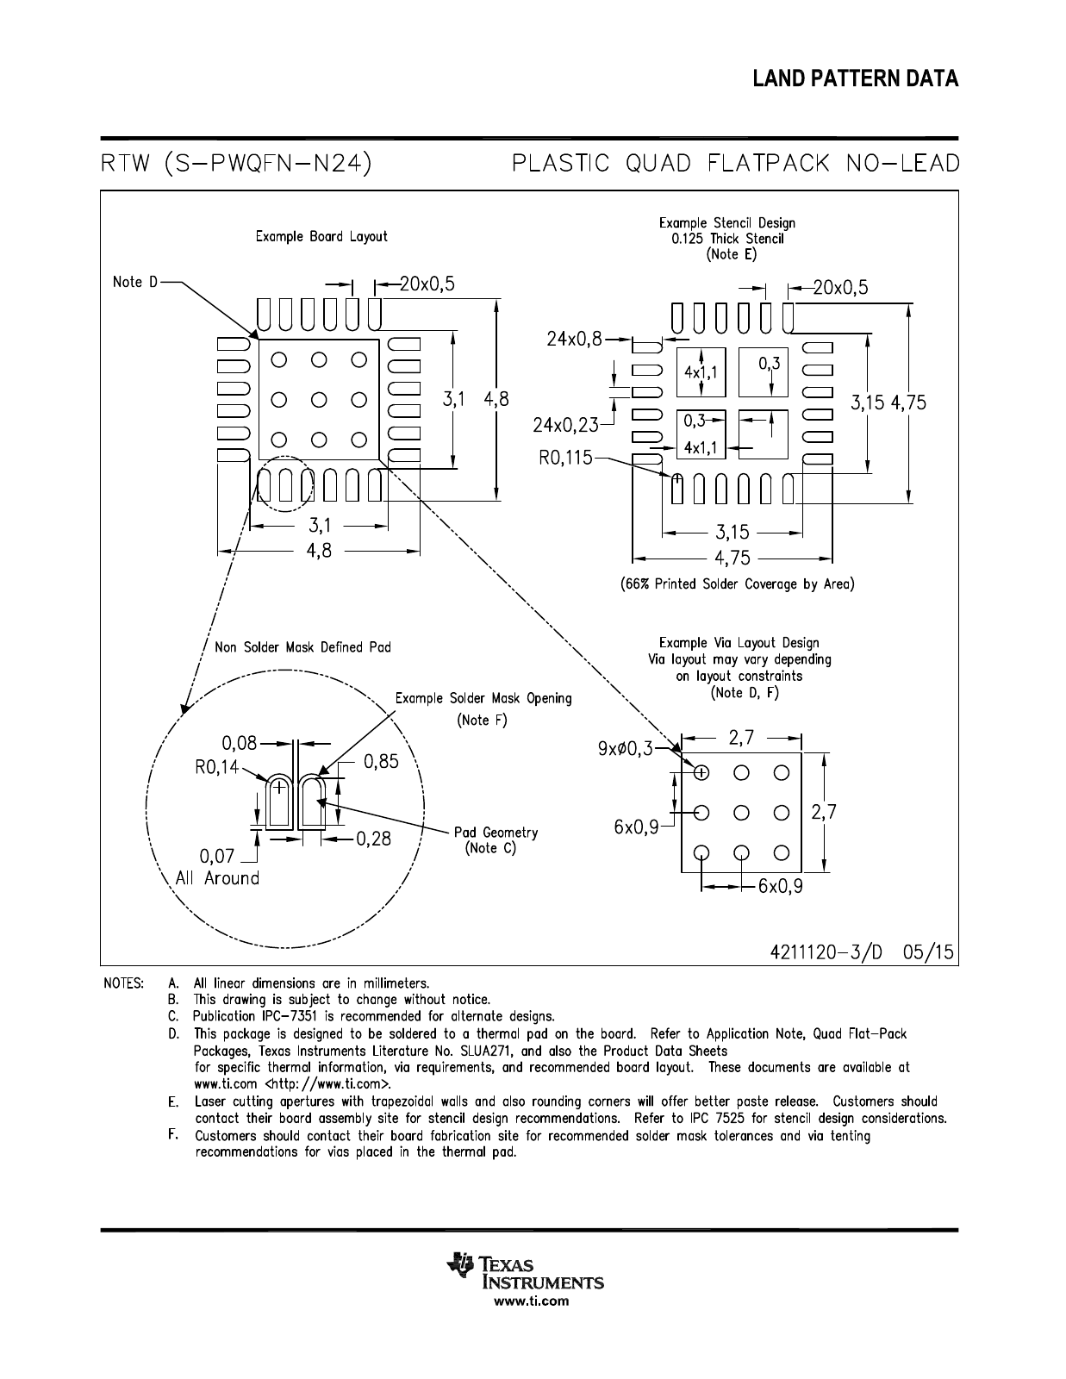
hardware/pcb/integration/verification/source-review/bq-64.png
