magnus188/trimix-analysator/hardware/pcb/integration/verification/source-review/tps-31.png

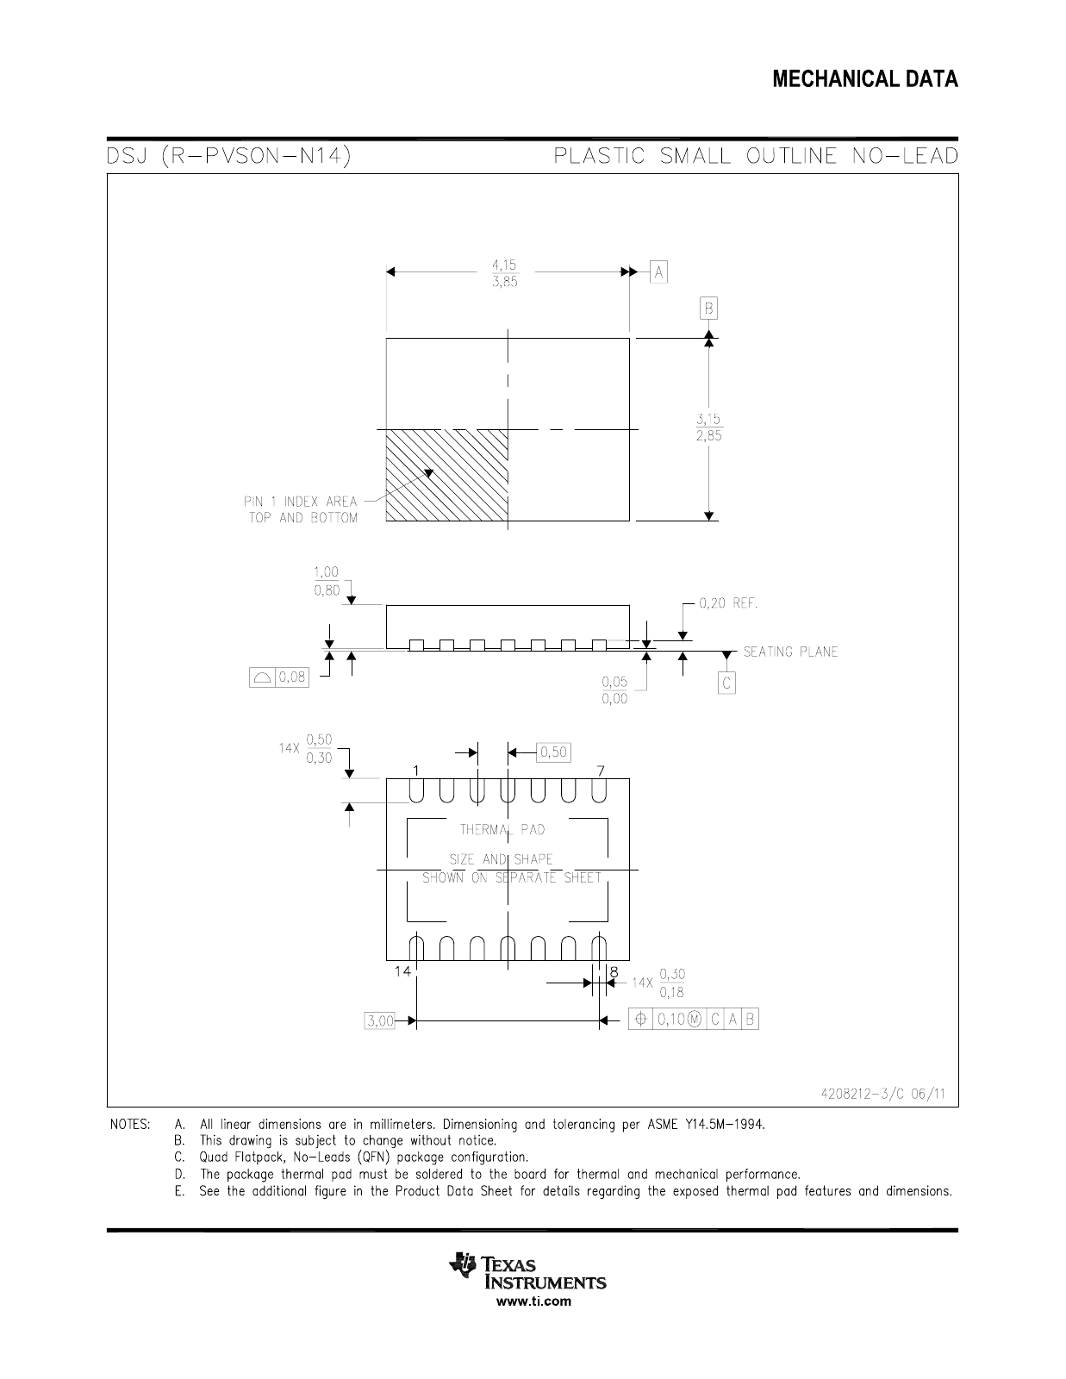
hardware/pcb/integration/verification/source-review/tps-31.png
