magnus188/trimix-analysator/hardware/pcb/integration/verification/source-review/tps-33.png

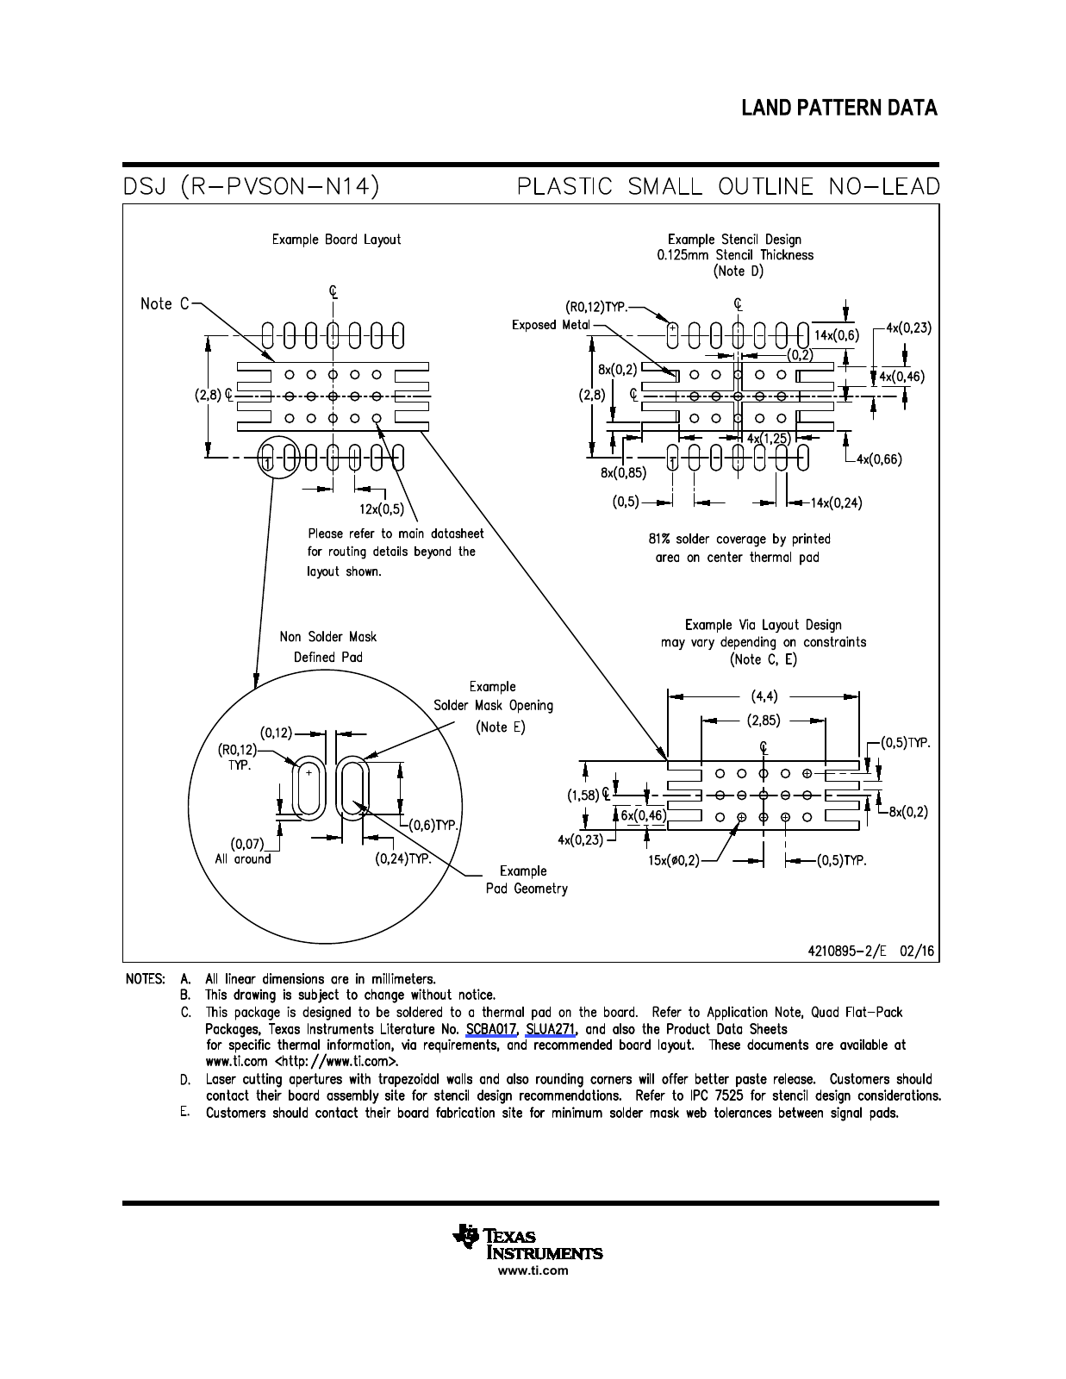
hardware/pcb/integration/verification/source-review/tps-33.png
