magnus188/trimix-analysator/hardware/pcb/integration/verification/u201-views/copper.png

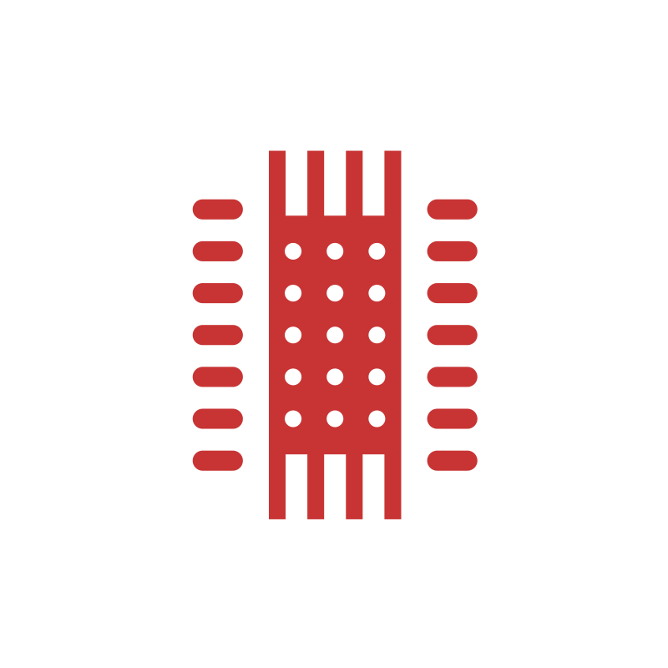
hardware/pcb/integration/verification/u201-views/copper.png
