magnus188/trimix-analysator/hardware/pcb/integration/verification/u201-views/pins.png

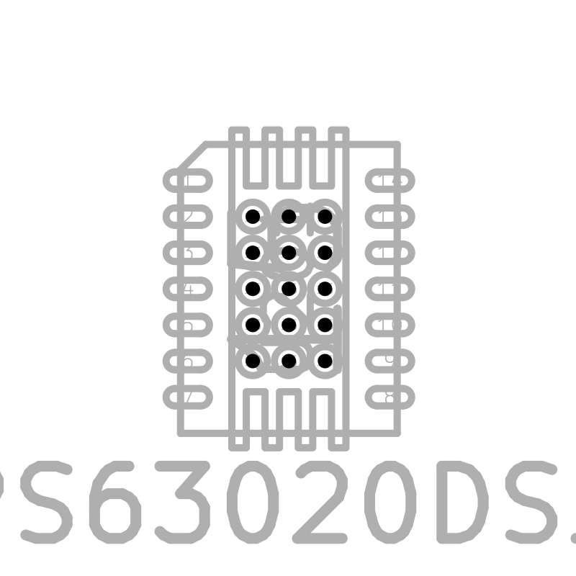
hardware/pcb/integration/verification/u201-views/pins.png
