magnus188/trimix-analysator/hardware/pcb/verification/analyzer/usb-input.png

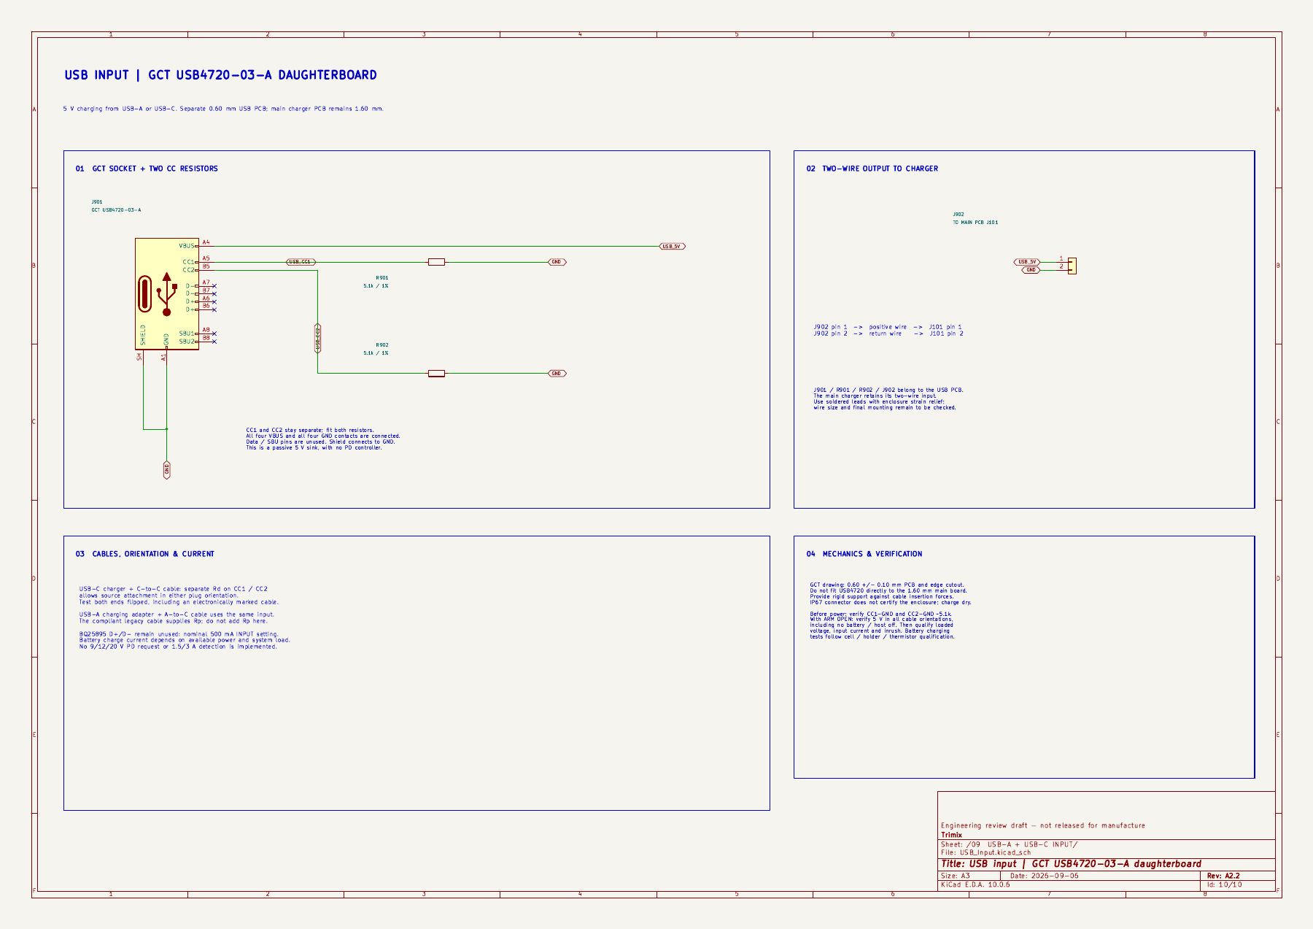
hardware/pcb/verification/analyzer/usb-input.png
