magnus188/trimix-analysator/hardware/pcb/verification/power/charging.png

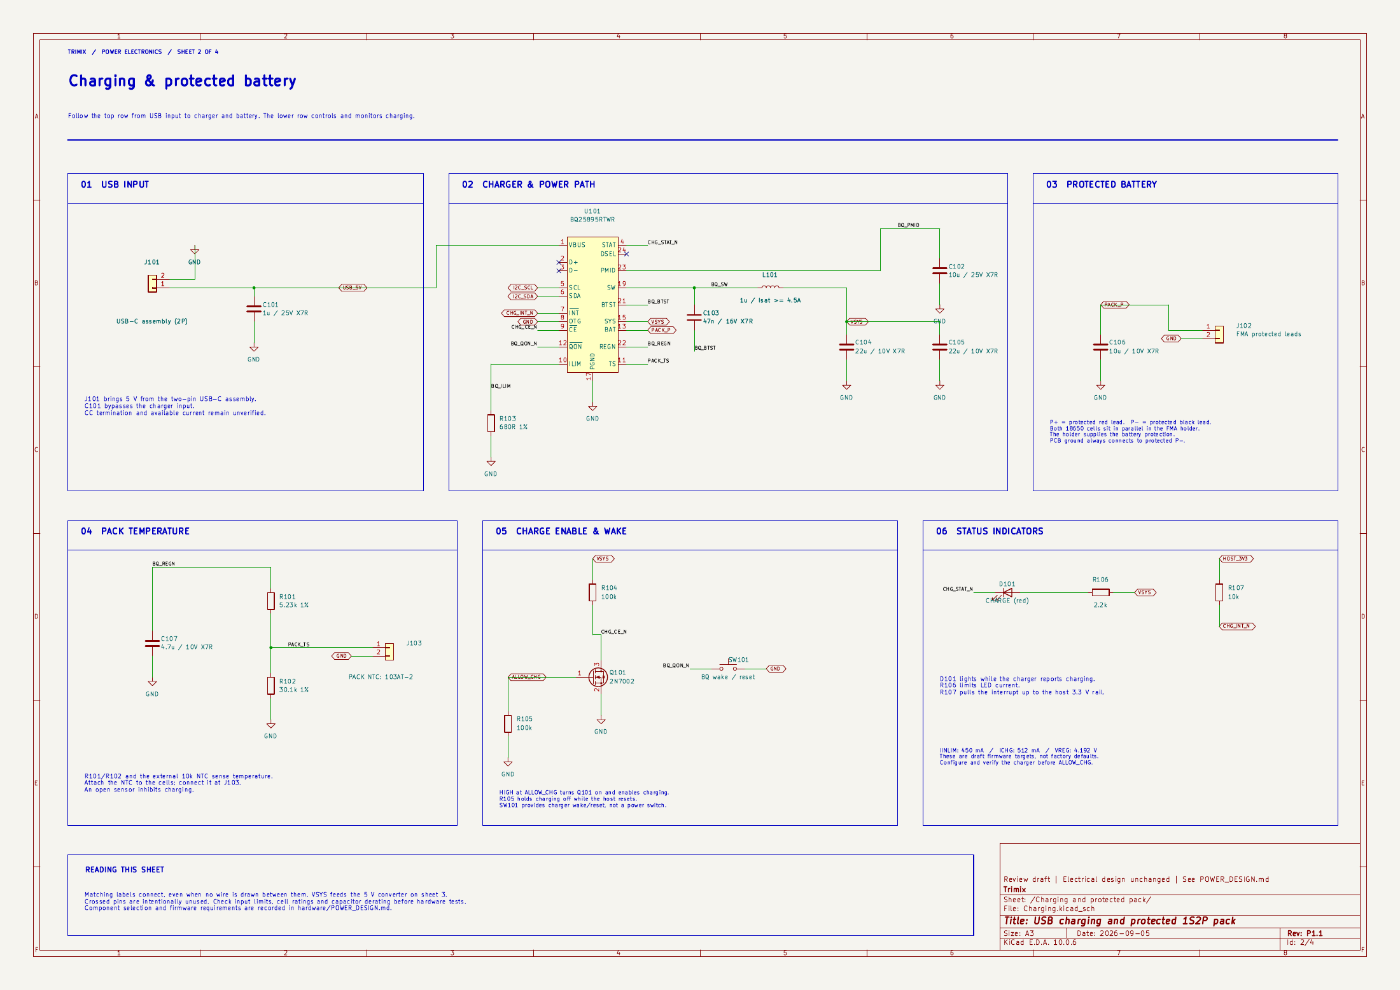
hardware/pcb/verification/power/charging.png
