magnus188/trimix-analysator/hardware/system-review/mechanical/final-local-checkpoint/bound-inputs/hardware/system-review/mechanical/verification/final-local-checks/views/rear-access.png

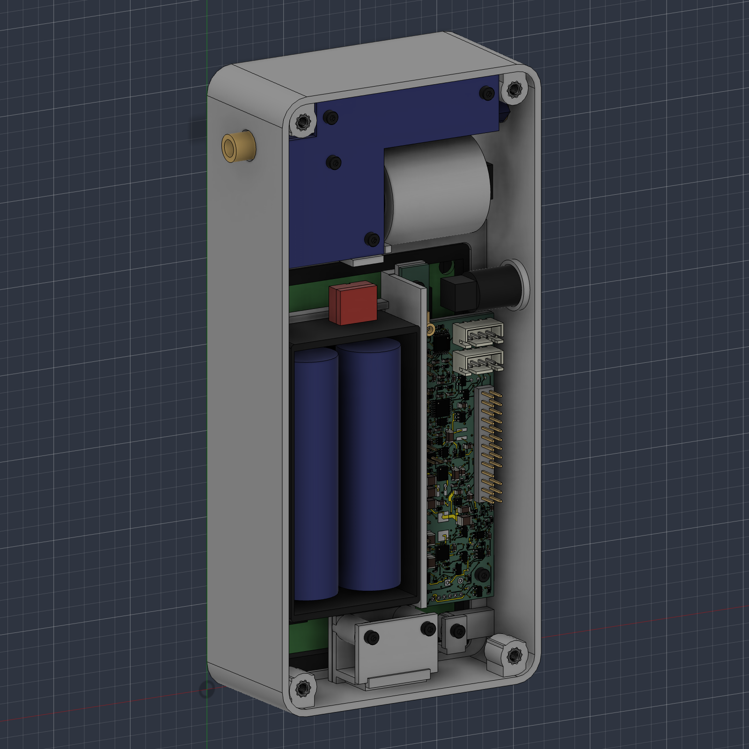
hardware/system-review/mechanical/final-local-checkpoint/bound-inputs/hardware/system-review/mechanical/verification/final-local-checks/views/rear-access.png
