magnus188/trimix-analysator/hardware/system-review/mechanical/verification/final-local-checks/views/carrier-apertures.png

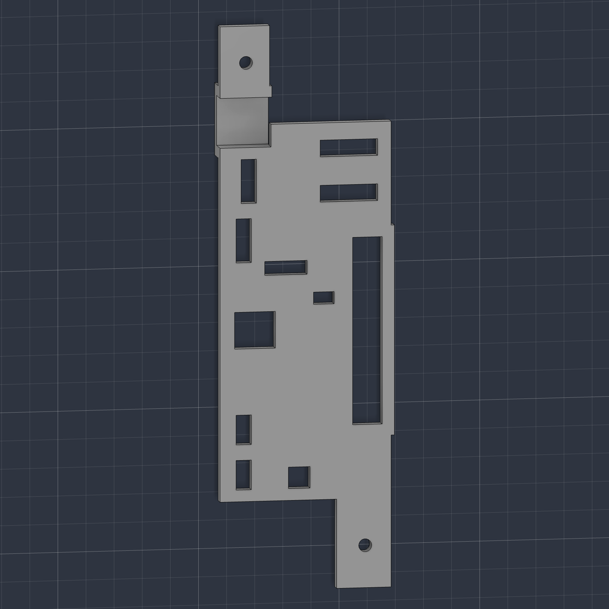
hardware/system-review/mechanical/verification/final-local-checks/views/carrier-apertures.png
