magnus188/trimix-analysator/hardware/system-review/mechanical/verification/final-local-slices/projects/pla/TMX-A3-P01_final_local_diagnostic/inspection/plate_1.png

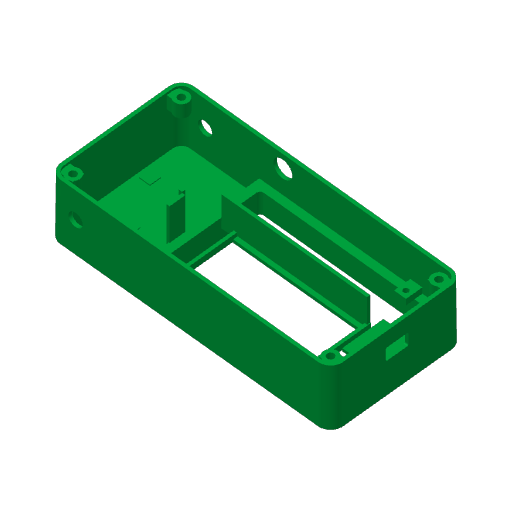
hardware/system-review/mechanical/verification/final-local-slices/projects/pla/TMX-A3-P01_final_local_diagnostic/inspection/plate_1.png
