magnus188/trimix-analysator/hardware/system-review/software/oxygen/views/calibration-overview.png

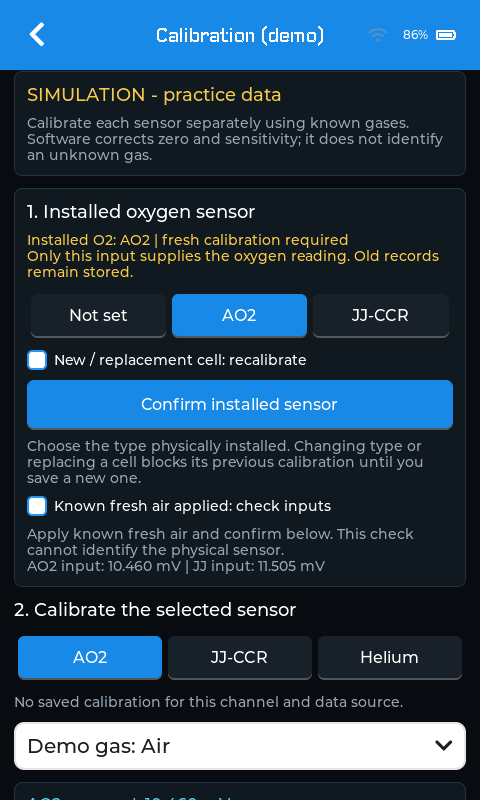
hardware/system-review/software/oxygen/views/calibration-overview.png
