magnus188/trimix-analysator/hardware/system-review/verification/before-co-environment/hardware/system-review/verification/interface-review-page-4.png

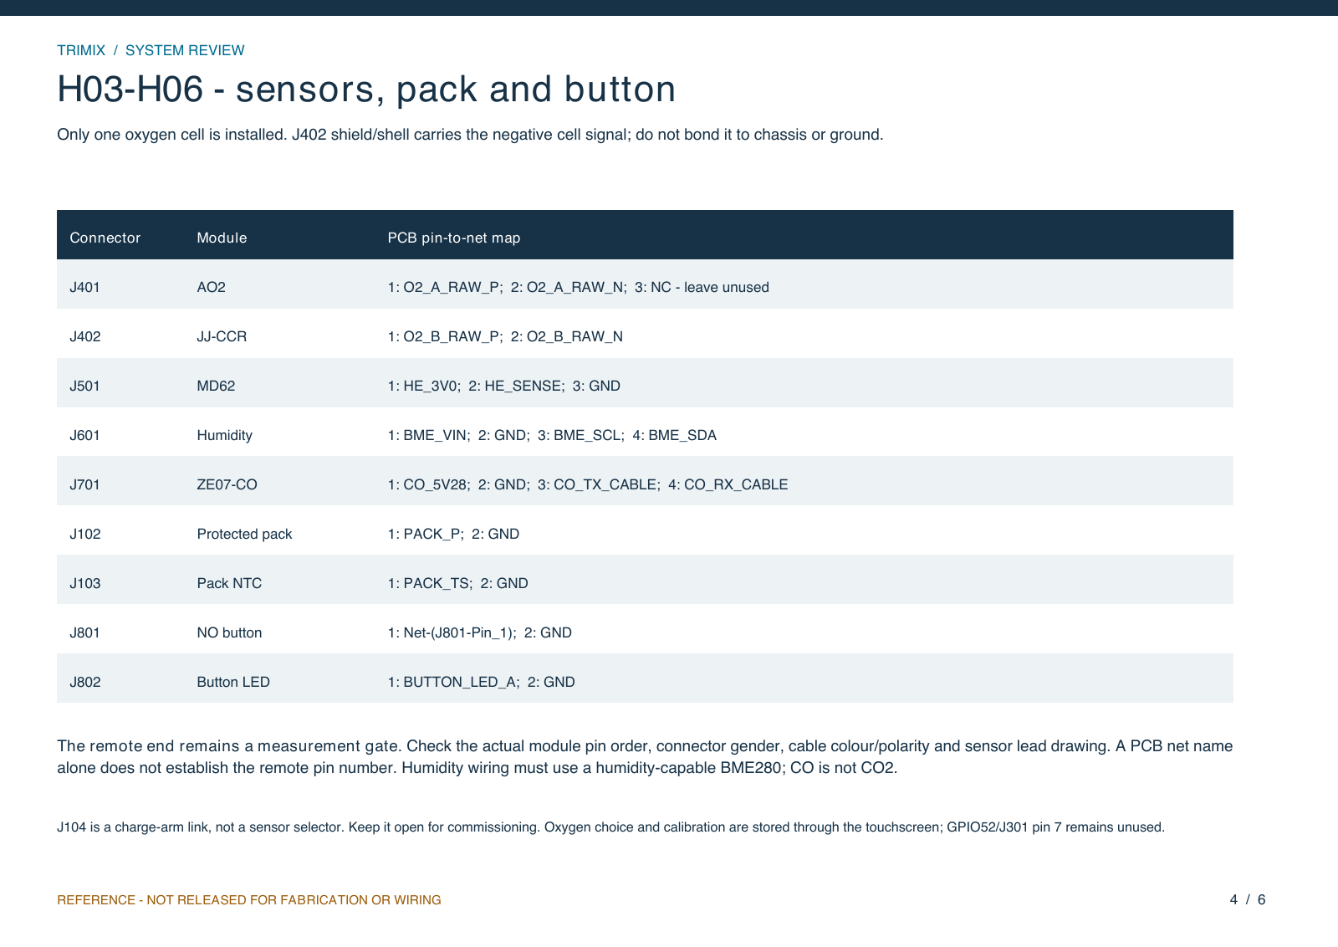
hardware/system-review/verification/before-co-environment/hardware/system-review/verification/interface-review-page-4.png
