magnus188/trimix-analysator/hardware/system-review/verification/before-routed-integration-interface/interface-review-page-6.png

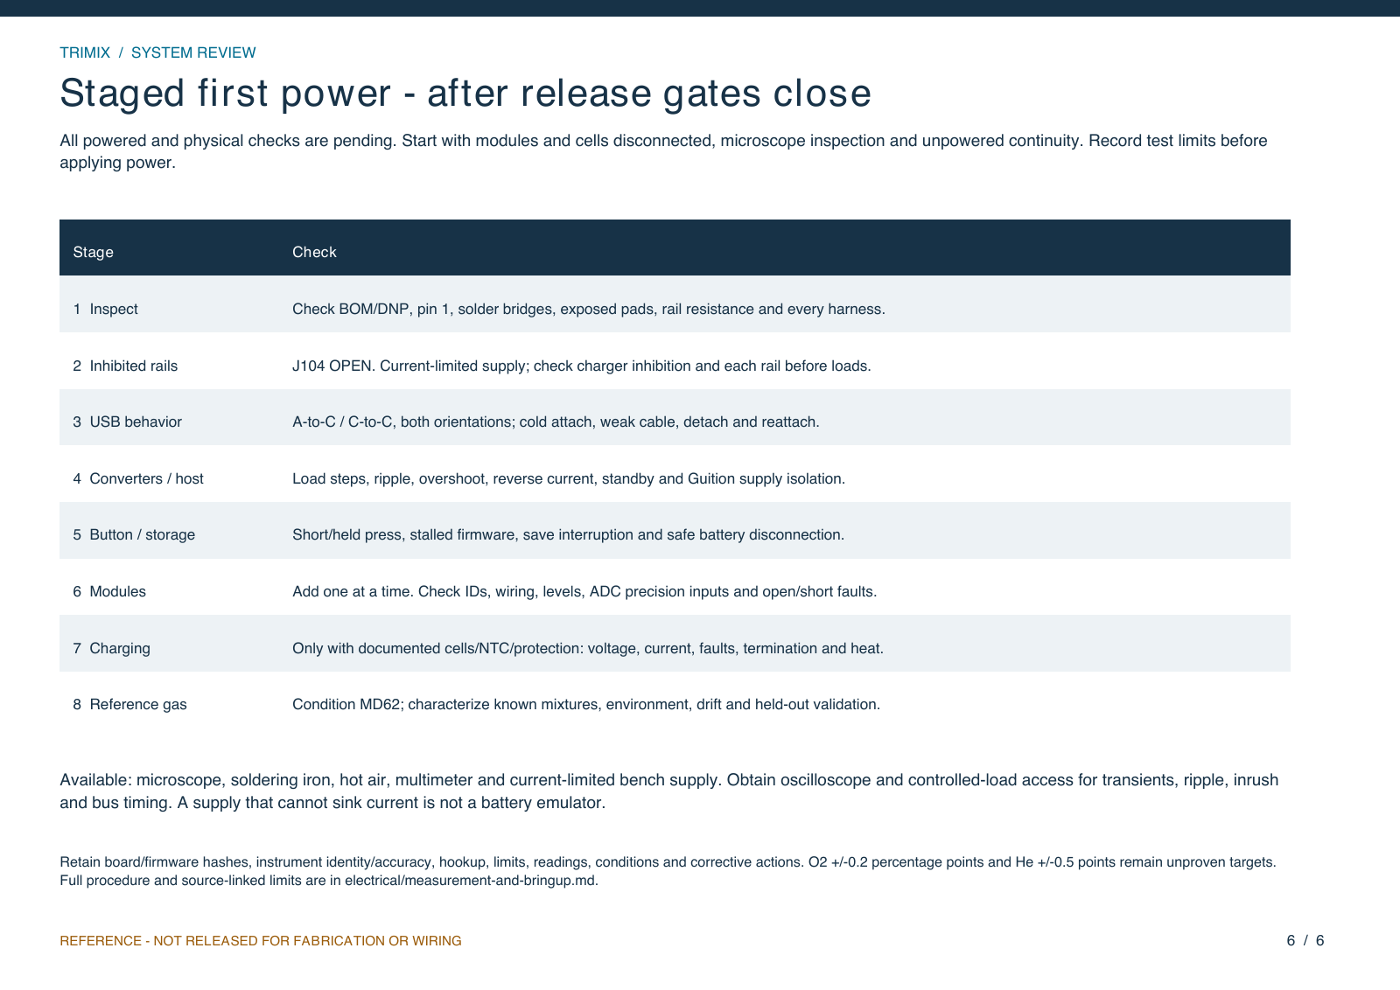
hardware/system-review/verification/before-routed-integration-interface/interface-review-page-6.png
