magnus188/trimix-analysator/hardware/system-review/verification/ui-current/calibration-fault.png

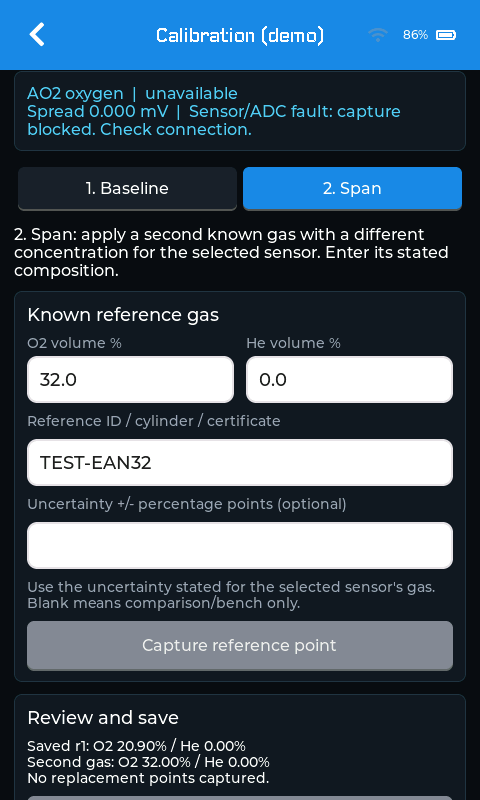
hardware/system-review/verification/ui-current/calibration-fault.png
