magnus188/trimix-analysator/hardware/system-review/verification/ui-current/device-status.png

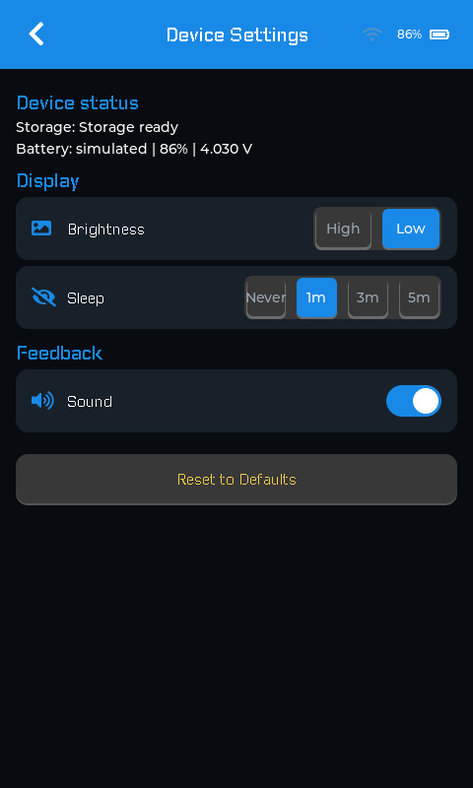
hardware/system-review/verification/ui-current/device-status.png
