magnus188/trimix-analysator/hardware/system-review/verification/ui-current/device-unavailable.png

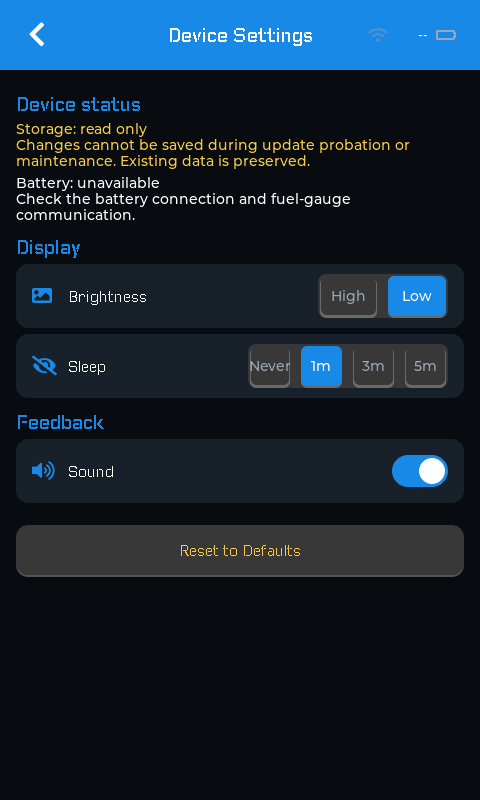
hardware/system-review/verification/ui-current/device-unavailable.png
