magnus188/trimix-analysator/hardware/system-review/software/oxygen/views/history-gas-provenance.png

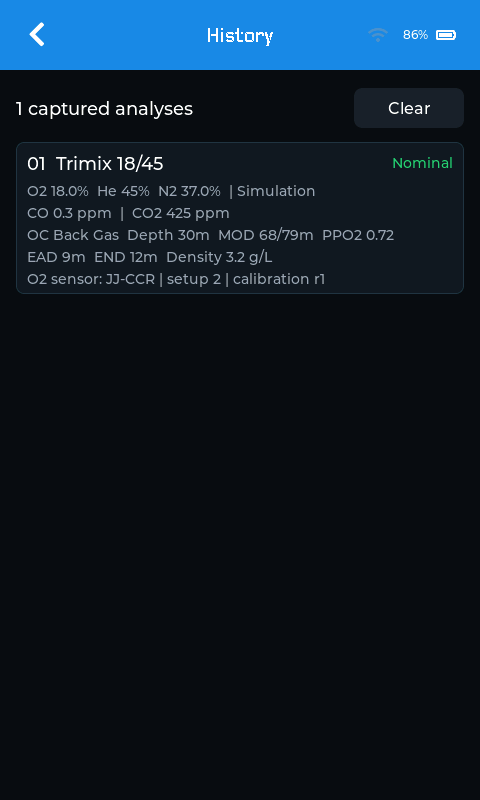
hardware/system-review/software/oxygen/views/history-gas-provenance.png
