magnus188/trimix-analysator/hardware/system-review/electrical/usb-final/usb-schematic.pdf

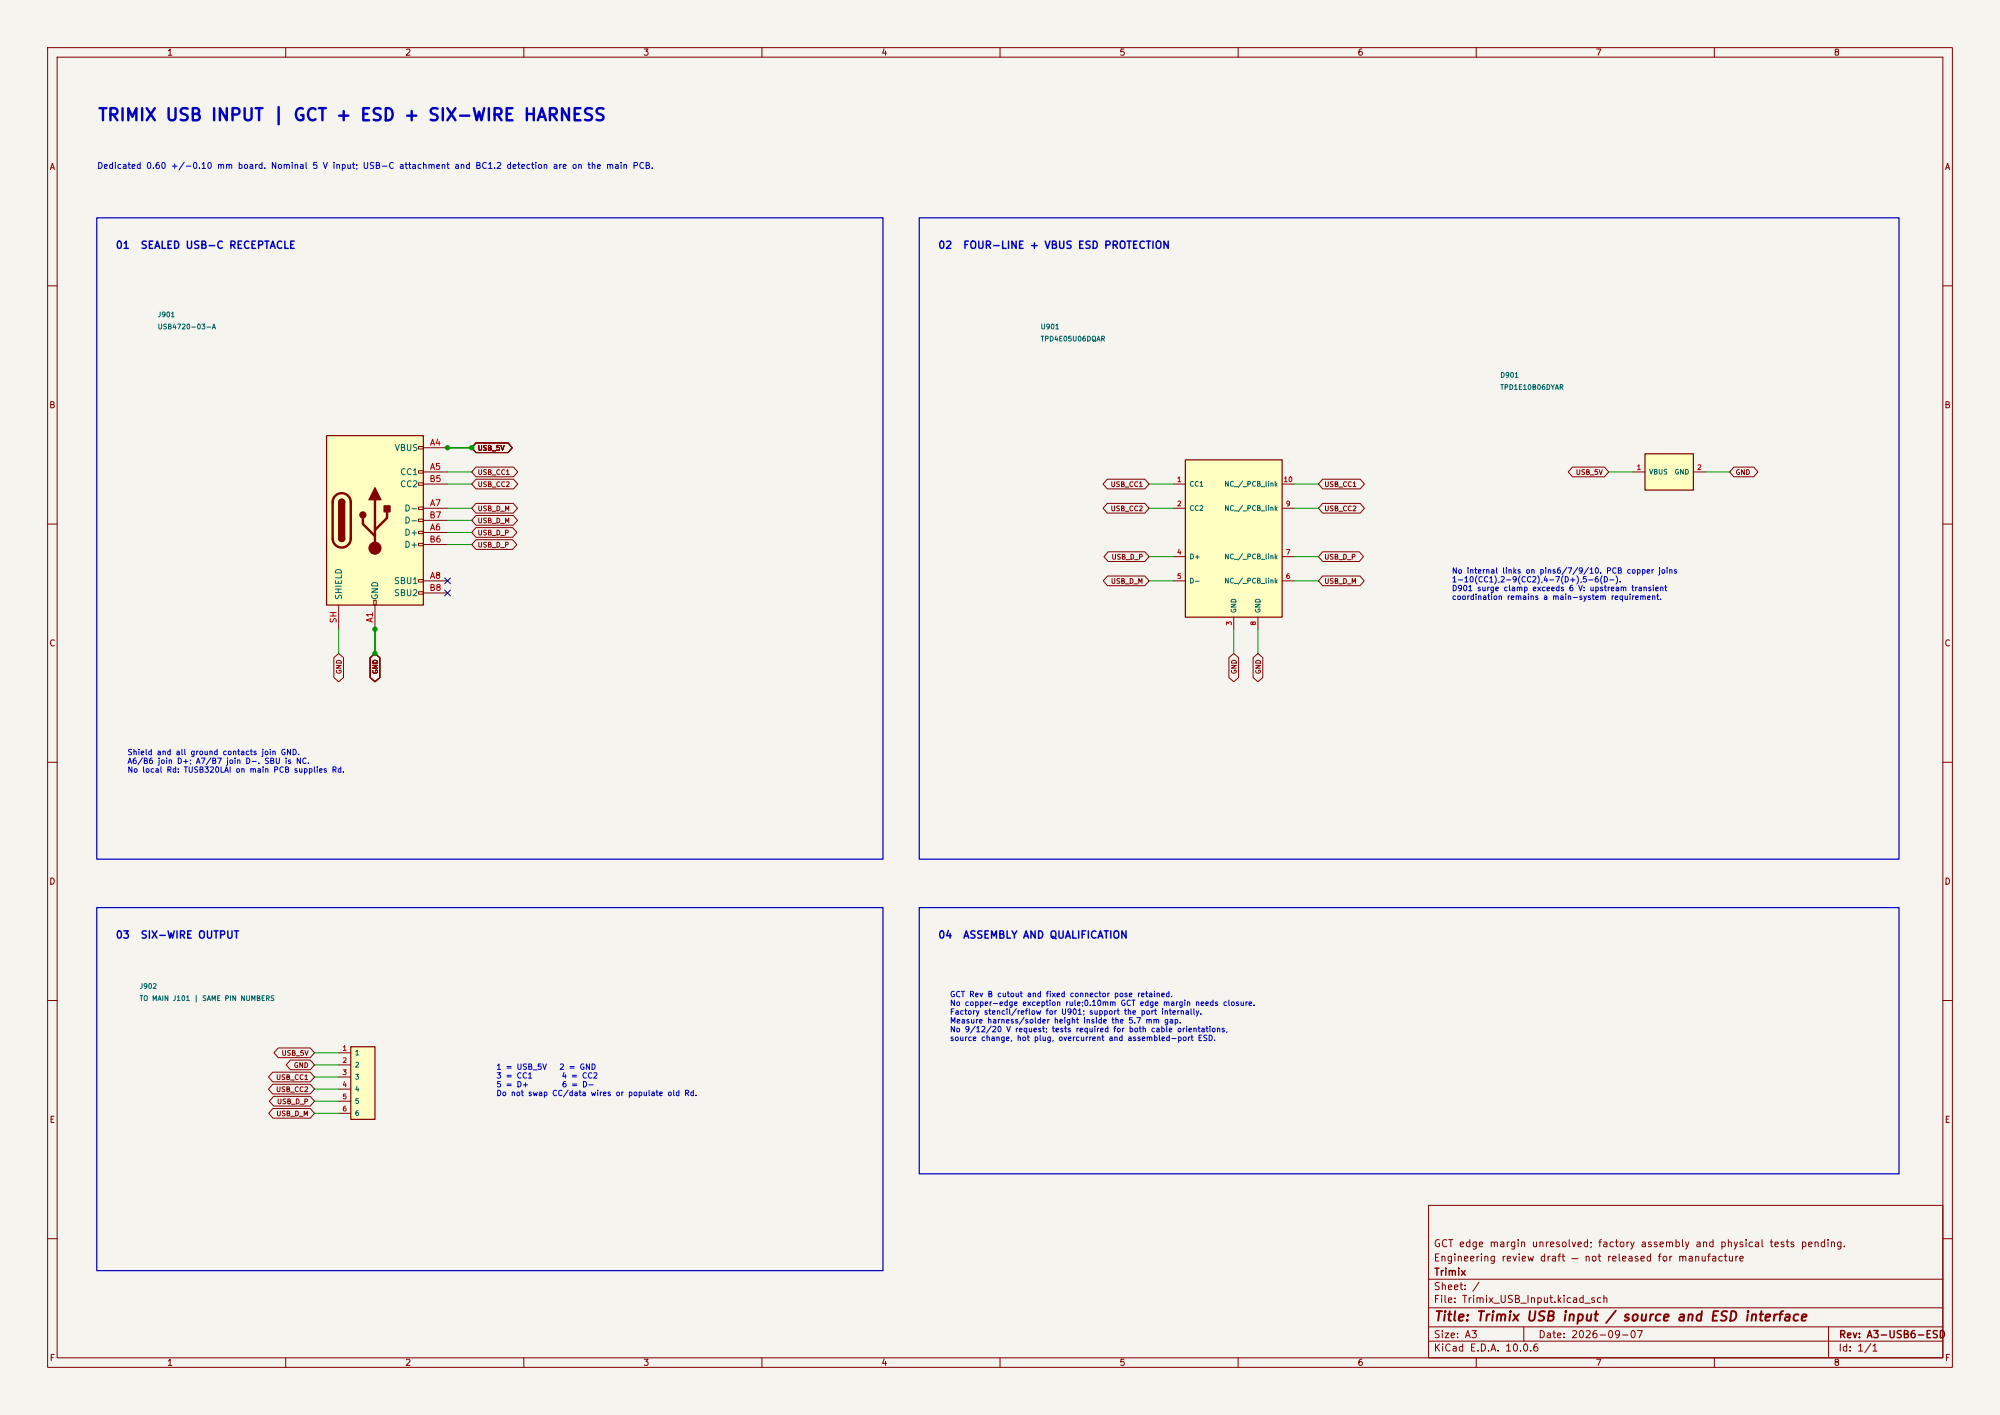
[picture p245: page 1]

Dedicated 0.60 +/-0.10 mm board. Nominal 5 V input; USB-C attachment and BC1.2 detection are on the main PCB.

GCT edge margin unresolved; factory assembly and physical tests pending. GND A1

Shield and all ground contacts join GND. A6/B6 join D+; A7/B7 join D-. SBU is NC. No local Rd: TUSB320LAI on main PCB supplies Rd. 03 SIX-WIRE OUTPUT

TO MAIN J101 | SAME PIN NUMBERS

GCT Rev B cutout and fixed connector pose retained. No copper-edge exception rule;0.10mm GCT edge margin needs closure. Factory stencil/reflow for U901; support the port internally. Measure harness/solder height inside the 5.7 mm gap. No 9/12/20 V request; tests required for both cable orientations, source change, hot plug, overcurrent and assembled-port ESD.

Engineering review draft — not released for manufacture
Trimix
Sheet: /
File: Trimix_USB_Input.kicad_sch
Title: Trimix USB input / source and ESD interface

Size: A3 | Rev: A3-USB6-ESD | F Date: 2026-09-07
KiCad E.D.A. 10.0.6 | Id: 1/1
