magnus188/trimix-analysator/hardware/system-review/integration-photo/guition-manufacturer/JC4880P443C_I_W_Y.pdf

117,01

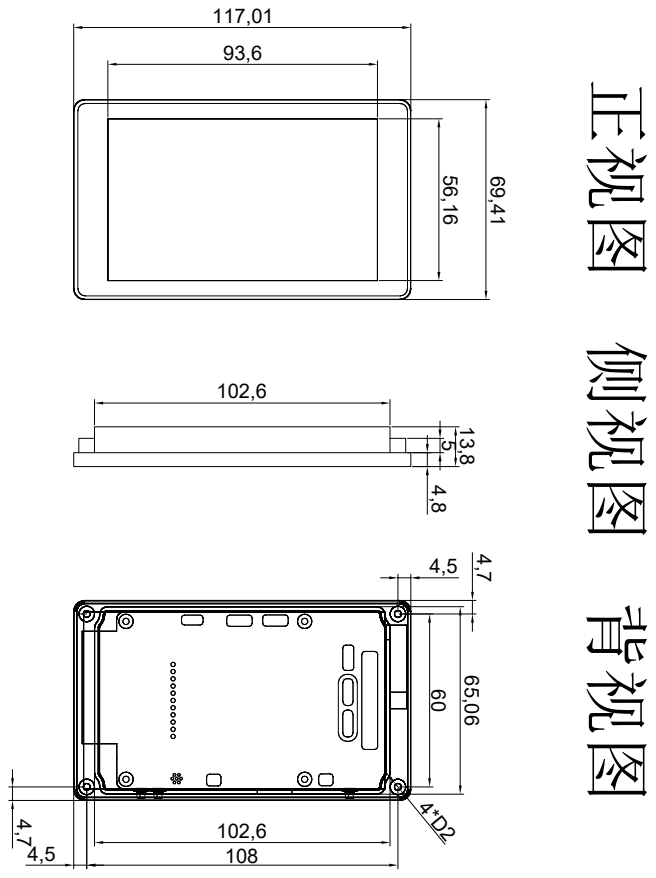
[picture p246: page 1]
正视图 侧视图 背视图⁶⁵,06
