magnus188/trimix-analysator/hardware/kicad/Trimix.kicad_sch

## KiCad design hardware/kicad/Trimix.kicad_sch (2026-09-07)

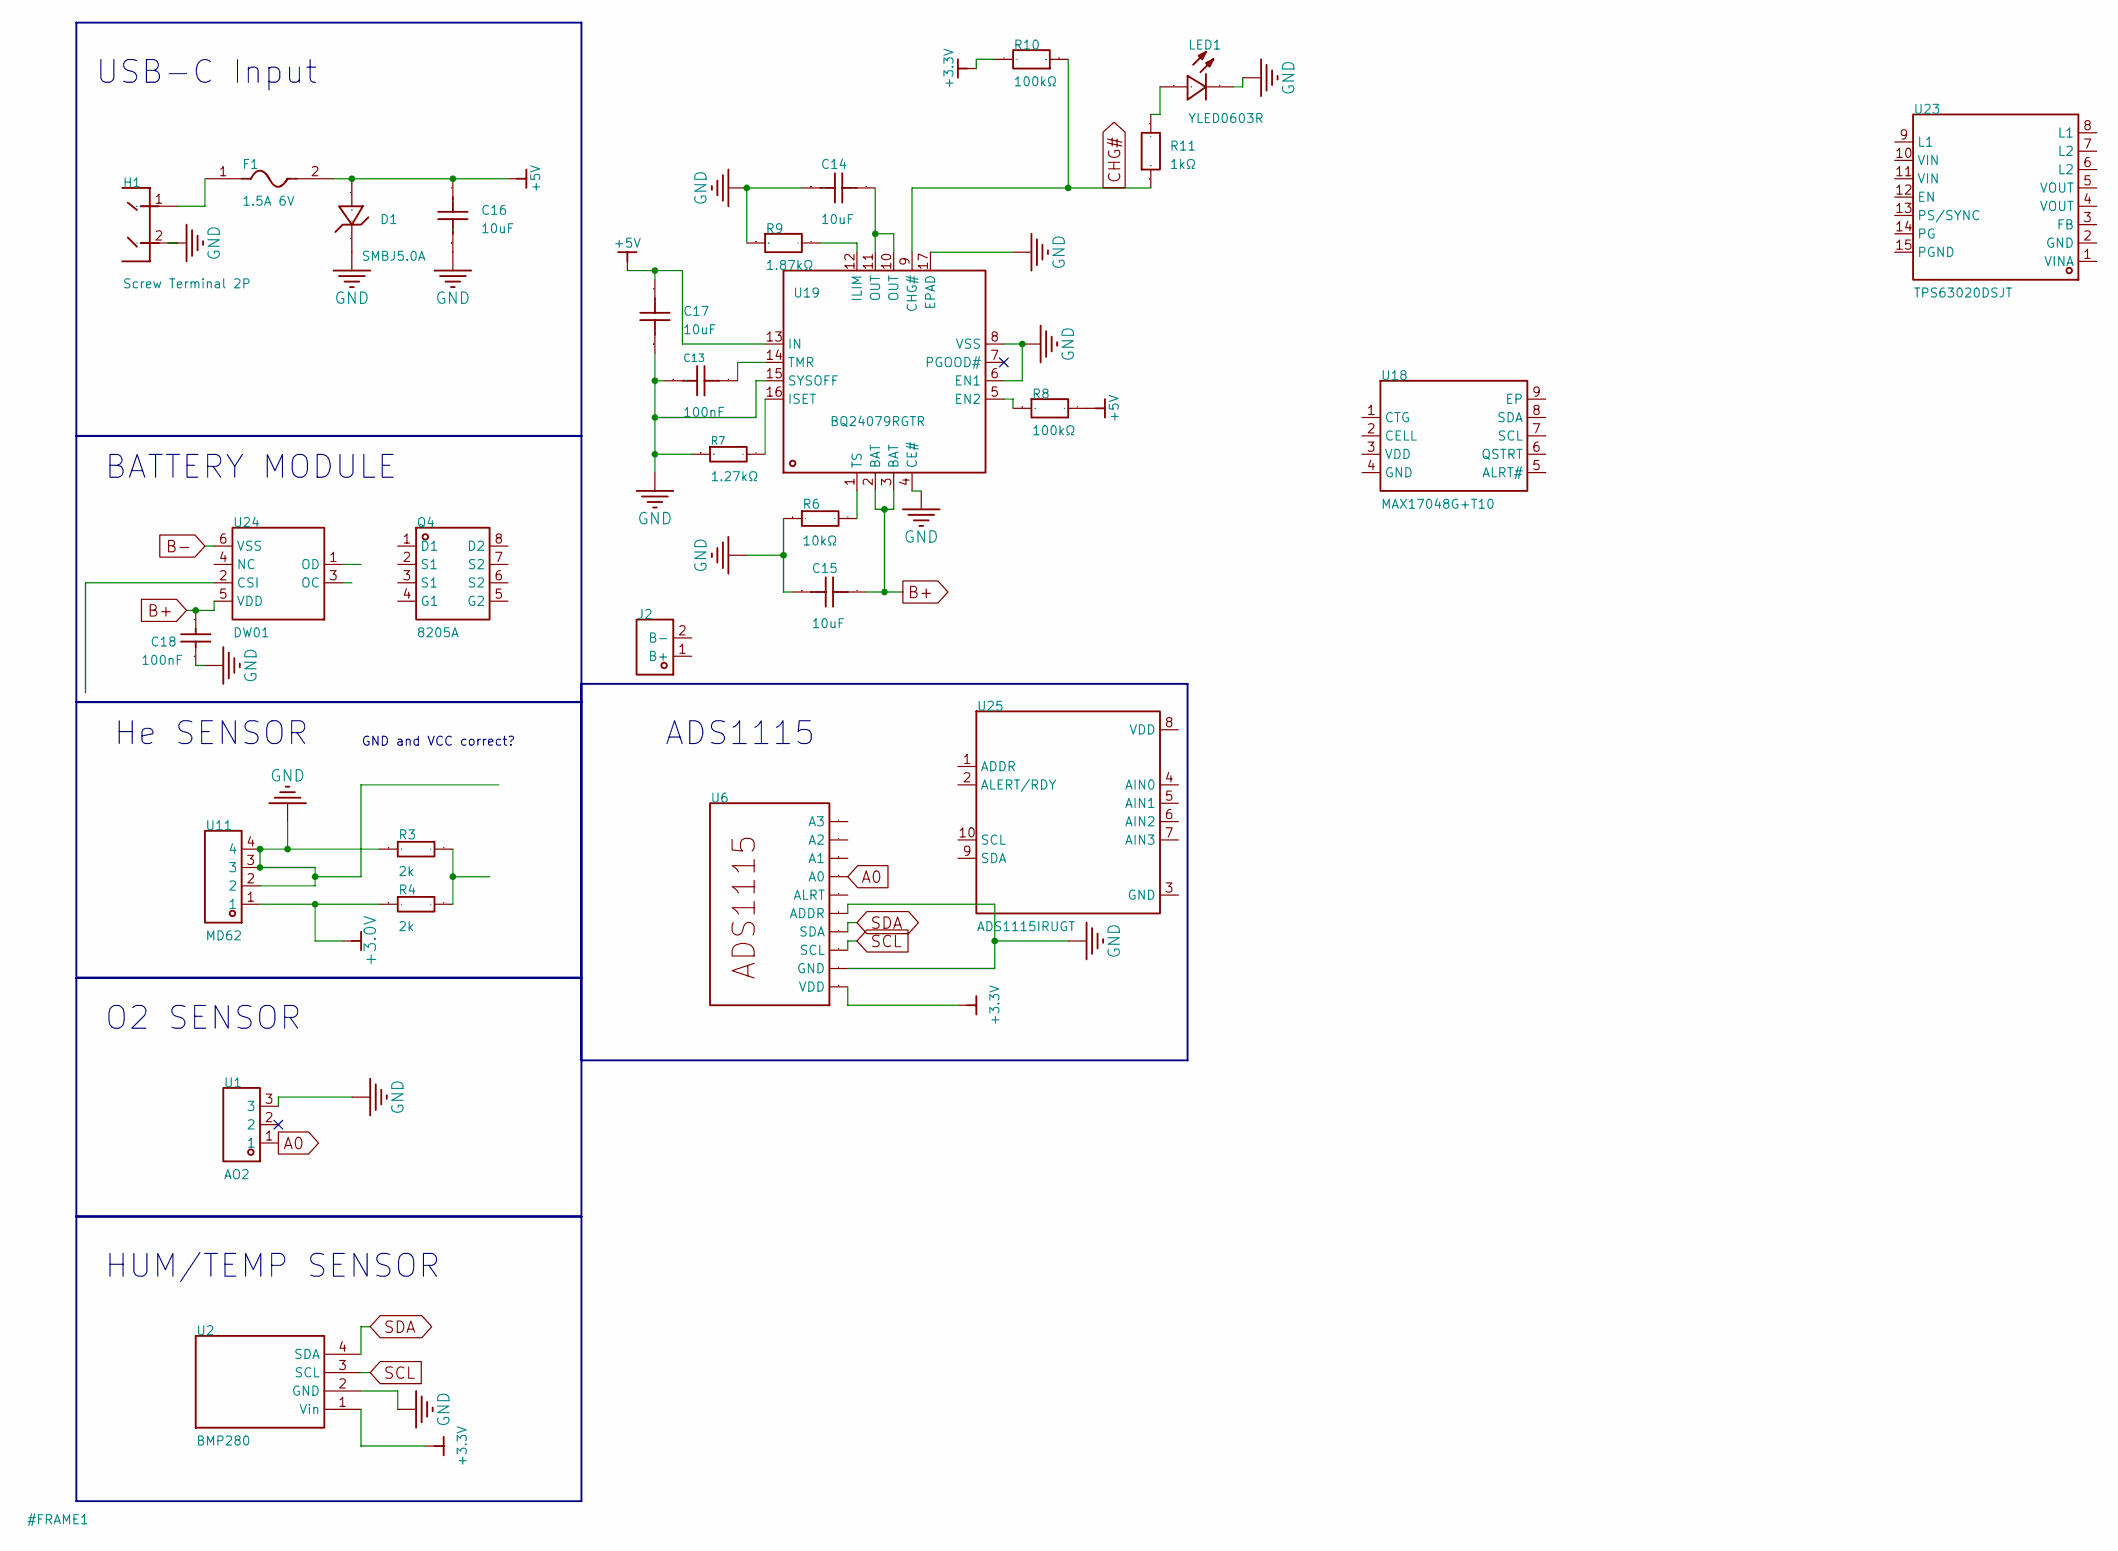
[picture p277: schematic Trimix.kicad_sch]

Parts:
C13: 100nF; C0402; Manufacturer Part CC0402KRX7R7BB104; LCSC Part Name 100nF ±10% 16V
C14, C15, C16, C17: 10uF; C0603; Manufacturer Part CL10A106MQ8NNNC; LCSC Part Name 10uF ±20% 6.3V
C18: 100nF; C0603; Manufacturer Part 0603B104K500NT; LCSC Part Name 100nF ±10% 50V
D1: SMBJ5.0A; SMB_L4.6-W3.6-LS5.3-RD; Manufacturer Part SMBJ5.0A; LCSC Part Name SMBJ5.0A
F1: 1.5A 6V; F1206; Manufacturer Part 1.5A 6V; LCSC Part Name ASMD1206-020
H1: Screw Terminal 2P; 2 PIN 2.54MM PITCH CONNECTOR2; Manufacturer Part KF128-2.54-2P
J2: CONN-TH_P3.50_KF128L-3.5-2P; Manufacturer Part KF128L-3.5-2P; LCSC Part Name 3.5mm 排数:1 每排P数:2 直针 可拼接 铜 环保
LED1: YLED0603R; LED0603-FD; Manufacturer Part YLED0603R; LCSC Part Name 红色 独立二极管
Q4: 8205A; TSSOP-8_L4.4-W3.0-P0.65-LS6.4-BL; Manufacturer Part 8205A; LCSC Part Name 2个N沟道 耐压:19.5V 电流:4.5A
R3, R4: 2k; Resistor 1_8w 7mm metal film; Manufacturer Part 1206W4F1002T5E
R6: 10kΩ; R0603; Manufacturer Part 0603WAF6201T5E; LCSC Part Name 6.2kΩ ±1% 100mW 厚膜电阻
R7: 1.27kΩ; R0603; Manufacturer Part 0603WAF1271T5E; LCSC Part Name 1.27kΩ ±1% 100mW 厚膜电阻
R8, R10: 100kΩ; R0603; Manufacturer Part FRC0603J104 TS; LCSC Part Name 100kΩ ±5% 100mW 厚膜电阻
R9: 1.87kΩ; R0603; Manufacturer Part FRC0603F1871TS; LCSC Part Name 1.87kΩ ±1% 100mW 厚膜电阻
R11: 1kΩ; R0603; Manufacturer Part FRC0603J104 TS; LCSC Part Name 100kΩ ±5% 100mW 厚膜电阻
U1: AO2; HDR-TH_3P-P2.54-V-M-1; Manufacturer Part AO2; LCSC Part Name 2.54mm-1*3P 直针
U2: BMP280; BME_BMP280
U6: ADAFRUIT ADS1115; Manufacturer Part 1085
U11: MD62; SENSORS-TH_MD62; Manufacturer Part MD62; LCSC Part Name MD62
U18: MAX17048G+T10; TDFN-8_L2.0-W2.0-P0.50-BL-EP1.2; Manufacturer Part MAX17048G+T10; LCSC Part Name 单节/双节电池电量计使用ModelGauge技术
U19: BQ24079RGTR; QFN-16_L3.0-W3.0-P0.50-TL-EP; Manufacturer Part BQ24079RGTR; LCSC Part Name bq2407x 1.5-A USB友好型锂离子电池充电器和电源路径管理IC
U23: TPS63020DSJT; VSON-14_L4.0-W3.0-P0.50-BL-EP_TI_DSJ; Manufacturer Part TPS63020DSJT; LCSC Part Name 具有4A开关的高效率单电感器降压/升压转换器
U24: DW01; TSOT-23-6_L2.9-W1.6-P0.95-LS2.8-BL; Manufacturer Part DW01; LCSC Part Name 锂电池保护IC
U25: ADS1115IRUGT; X2QFN-10_L2.0-W1.5-P0.50-TL_RUG0010B; Manufacturer Part ADS1115IRUGT; LCSC Part Name 具有内部基准、振荡器和可编程比较器且兼容 I2C 的ADS111x、超小型、低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

Connections:
+3.0V: R4.1, U11.1
+3.3V: R10.2, U2.1 (Vin), U6.10 (VDD)
+5V: C16.2, C17.2, D1.2 (A), F1.2, R8.2, U19.13 (IN)
A0: U1.1, U6.3 (A0)
B+: C15.2, C18.2, U19.2 (BAT), U19.3 (BAT), U24.5 (VDD)
B-: U24.6 (VSS)
CHG#: R10.1, R11.1, U19.9 (CHG#)
GND: C13.1, C14.1, C15.1, C16.1, C17.1, C18.1, D1.1 (C), H1.2, LED1.2 (-), R3.1, R6.1, R7.1, R9.1, U1.3, U2.2 (GND), U6.1 (ADDR), U6.9 (GND), U11.2, U11.3, U11.4, U19.4 (CE#), U19.6 (EN1), U19.8 (VSS), U19.15 (SYSOFF), U19.17 (EPAD)
unnamed: C13.2, U19.14 (TMR)
unnamed: C14.2, U19.10 (OUT), U19.11 (OUT)
unnamed: F1.1, H1.1
unnamed: LED1.1 (+), R11.2
unnamed: R3.2, R4.2
unnamed: R6.2, U19.1 (TS)
unnamed: R7.2, U19.16 (ISET)
unnamed: R8.1, U19.5 (EN2)
unnamed: R9.2, U19.12 (ILIM)
SCL: U2.3 (SCL), U6.8 (SCL)
SDA: U2.4 (SDA), U6.7 (SDA)

Notes on the sheet:
O2 SENSOR
He SENSOR
GND and VCC correct?
BATTERY MODULE
ADS1115
HUM/TEMP SENSOR
USB-C Input
