magnus188/trimix-analysator/hardware/pcb/power/Charging.kicad_sch

## KiCad design hardware/pcb/power/Charging.kicad_sch (2026-09-07)

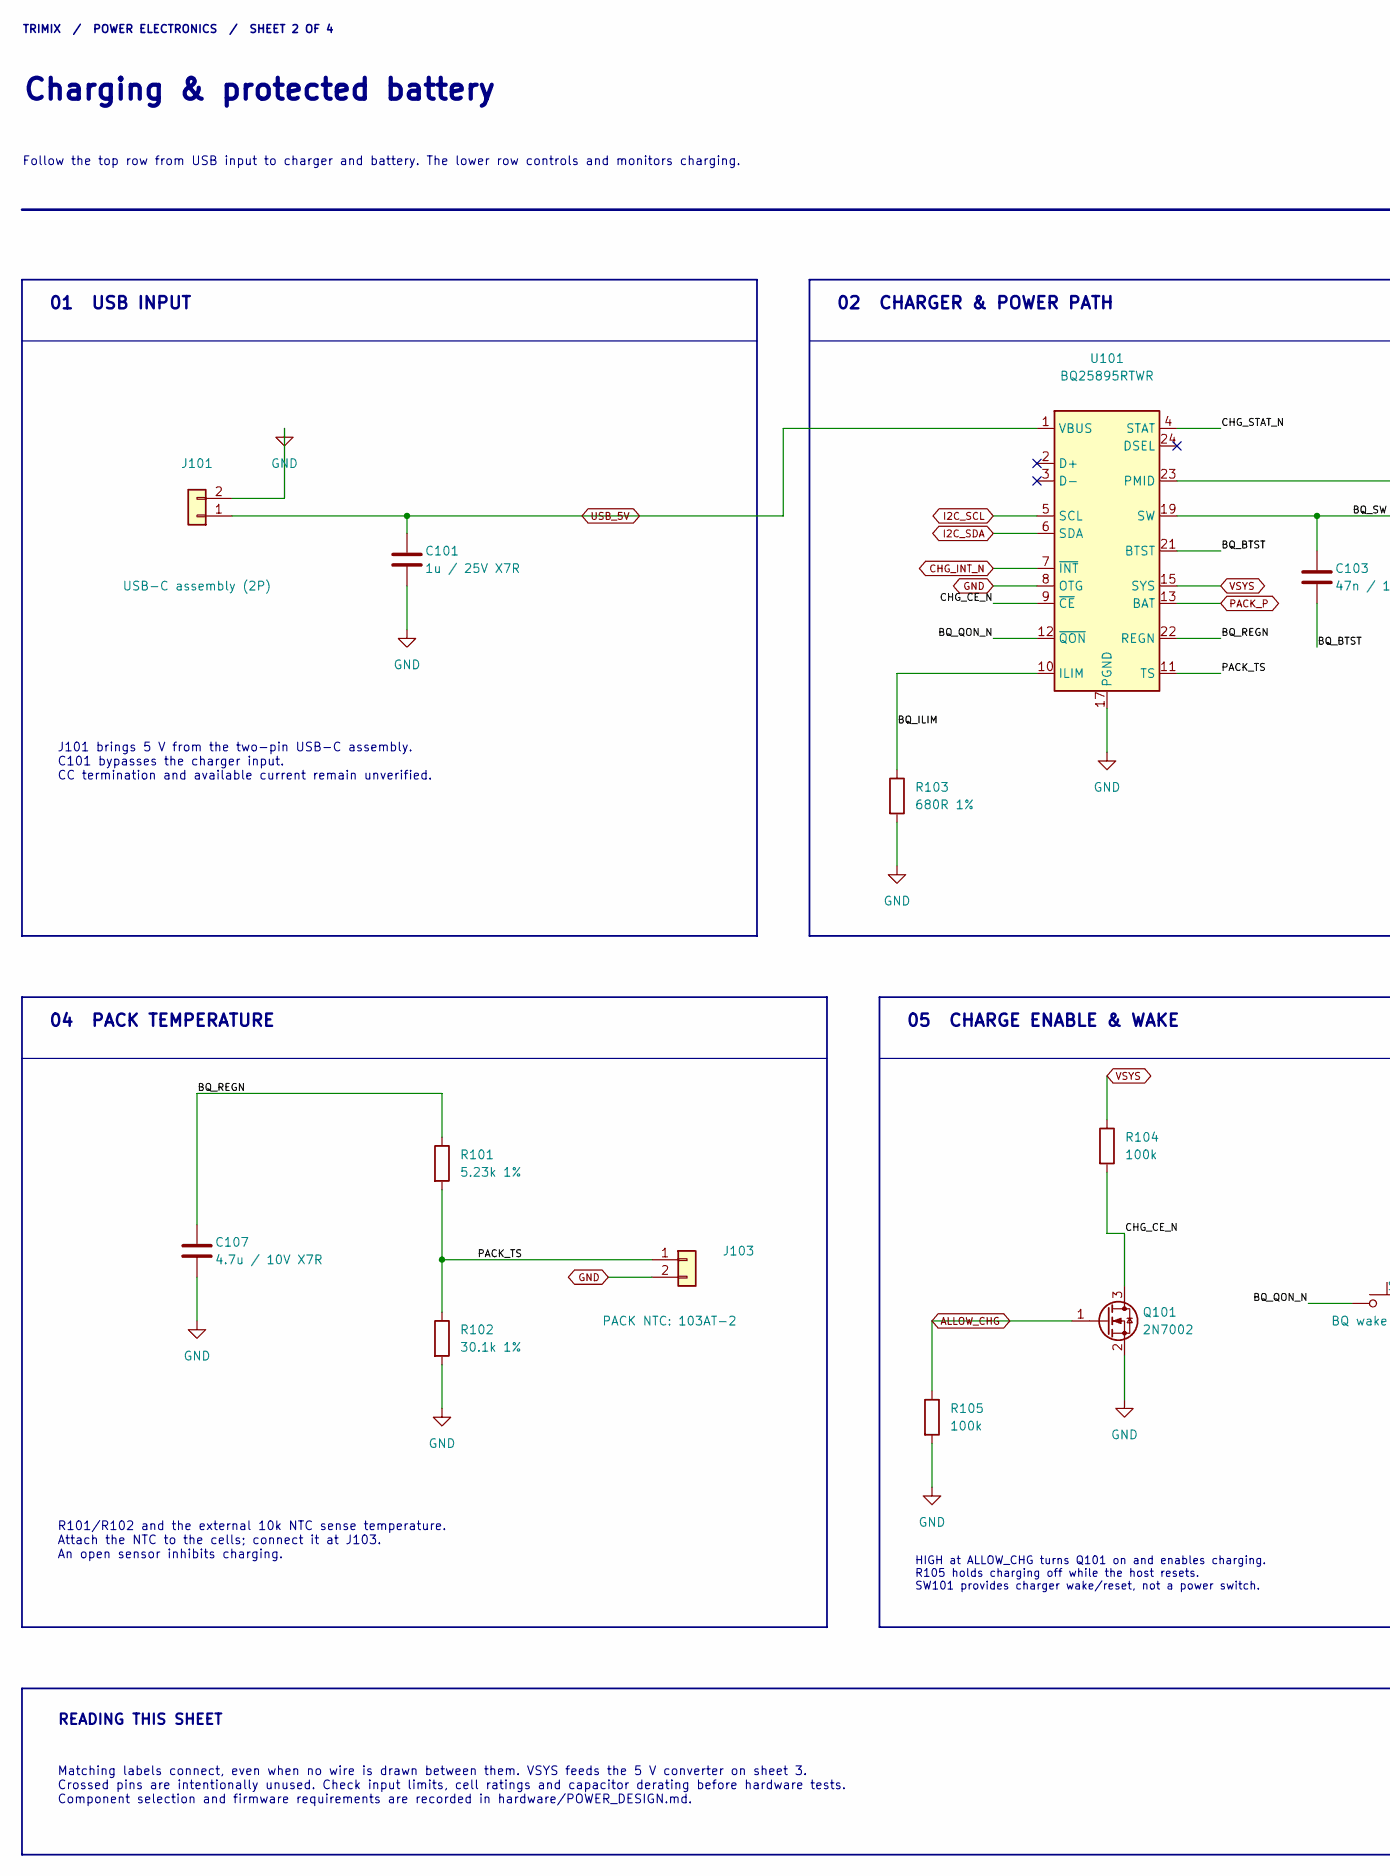
[picture p278: schematic Charging.kicad_sch, part in row 1, column 1]

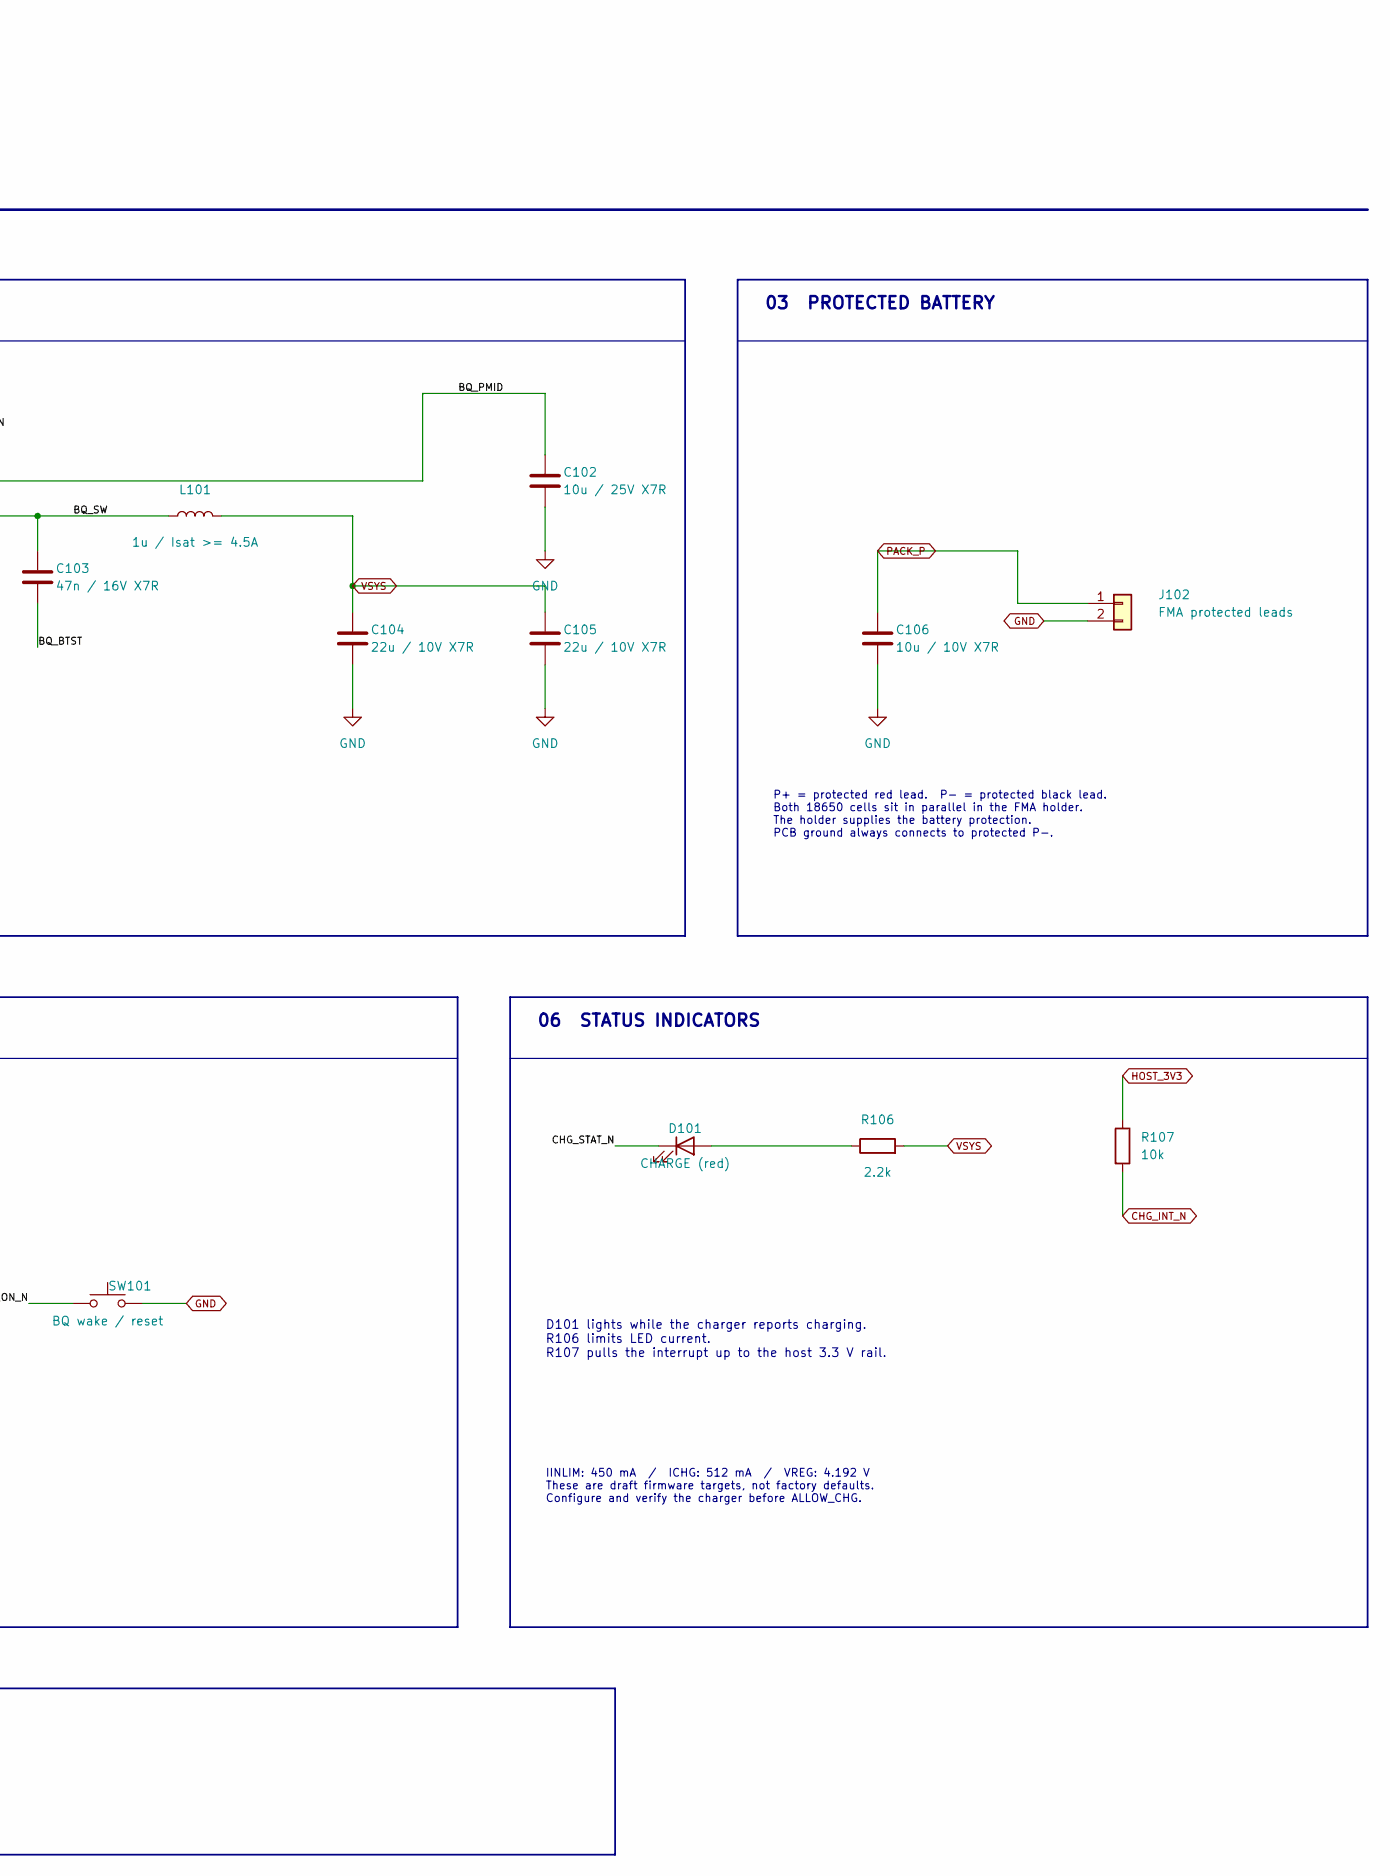
[picture p279: schematic Charging.kicad_sch, part in row 1, column 2]

Parts:
C101: 1u / 25V X7R; C_0805_2012Metric
C102: 10u / 25V X7R; C_1206_3216Metric
C103: 47n / 16V X7R; C_0805_2012Metric
C104, C105: 22u / 10V X7R; C_0805_2012Metric
C106: 10u / 10V X7R; C_0805_2012Metric
C107: 4.7u / 10V X7R; C_0805_2012Metric
D101: CHARGE (red)
J101: USB-C assembly (2P)
J102: FMA protected leads
J103: PACK NTC: 103AT-2
L101: 1u / Isat >= 4.5A
Q101: 2N7002; SOT-23
R101: 5.23k 1%; R_0603_1608Metric
R102: 30.1k 1%; R_0603_1608Metric
R103: 680R 1%; R_0603_1608Metric
R104, R105: 100k; R_0603_1608Metric
R106: 2.2k; R_0603_1608Metric
R107: 10k; R_0603_1608Metric
SW101: BQ wake / reset
U101: BQ25895RTWR; Texas_RTW_WQFN-24-1EP_4x4mm_P0.5mm_EP2.7x2.7mm_ThermalVias

Connections:
ALLOW_CHG: Q101.1 (G), R105.1
BQ_BTST: C103.2, U101.21 (BTST)
BQ_ILIM: R103.1, U101.10 (ILIM)
BQ_PMID: C102.1, U101.23 (PMID)
BQ_QON_N: SW101.1, U101.12 (~QON)
BQ_REGN: C107.1, R101.1, U101.22 (REGN)
BQ_SW: C103.1, L101.1, U101.19 (SW), U101.20 (SW)
CHG_CE_N: Q101.3 (D), R104.2, U101.9 (~CE)
CHG_INT_N: R107.2, U101.7 (~INT)
CHG_STAT_N: D101.1 (K), U101.4 (STAT)
GND: C101.2, C102.2, C104.2, C105.2, C106.2, C107.2, J101.2, J102.2, J103.2, Q101.2 (S), R102.2, R103.2, R105.2, SW101.2, U101.8 (OTG), U101.17 (PGND), U101.18 (PGND), U101.25 (PGND)
HOST_3V3: R107.1
I2C_SCL: U101.5 (SCL)
I2C_SDA: U101.6 (SDA)
unnamed: D101.2 (A), R106.1
PACK_P: C106.1, J102.1, U101.13 (BAT), U101.14 (BAT)
PACK_TS: J103.1, R101.2, R102.1, U101.11 (TS)
USB_5V: C101.1, J101.1, U101.1 (VBUS)
VSYS: C104.1, C105.1, L101.2, R104.1, R106.2, U101.15 (SYS), U101.16 (SYS)

Notes on the sheet:
05 CHARGE ENABLE & WAKE
D101 lights while the charger reports charging. R106 limits LED current. R107 pulls the interrupt up to the host 3.3 V rail.
Follow the top row from USB input to charger and battery. The lower row controls and monitors charging.
02 CHARGER & POWER PATH
Charging & protected battery
01 USB INPUT
03 PROTECTED BATTERY
TRIMIX / POWER ELECTRONICS / SHEET 2 OF 4
Matching labels connect, even when no wire is drawn between them. VSYS feeds the 5 V converter on sheet 3. Crossed pins are intentionally unused. Check input limits, cell ratings and capacitor derating before hardware tests. Component selection and firmware requirements are recorded in hardware/POW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
R101/R102 and the external 10k NTC sense temperature. Attach the NTC to the cells; connect it at J103. An open sensor inhibits charging.
HIGH at ALLOW_CHG turns Q101 on and enables charging. R105 holds charging off while the host resets. SW101 provides charger wake/reset, not a power switch.
04 PACK TEMPERATURE
J101 brings 5 V from the two-pin USB-C assembly. C101 bypasses the charger input. CC termination and available current remain unverified.
IINLIM: 450 mA / ICHG: 512 mA / VREG: 4.192 V These are draft firmware targets, not factory defaults. Configure and verify the charger before ALLOW_CHG.
06 STATUS INDICATORS
P+ = protected red lead. P- = protected black lead. Both 18650 cells sit in parallel in the FMA holder. The holder supplies the battery protection. PCB ground always connects to protected P-.
READING THIS SHEET
