magnus188/trimix-analysator/hardware/pcb/power/Gauge_Interface.kicad_sch

## KiCad design hardware/pcb/power/Gauge_Interface.kicad_sch (2026-09-07)

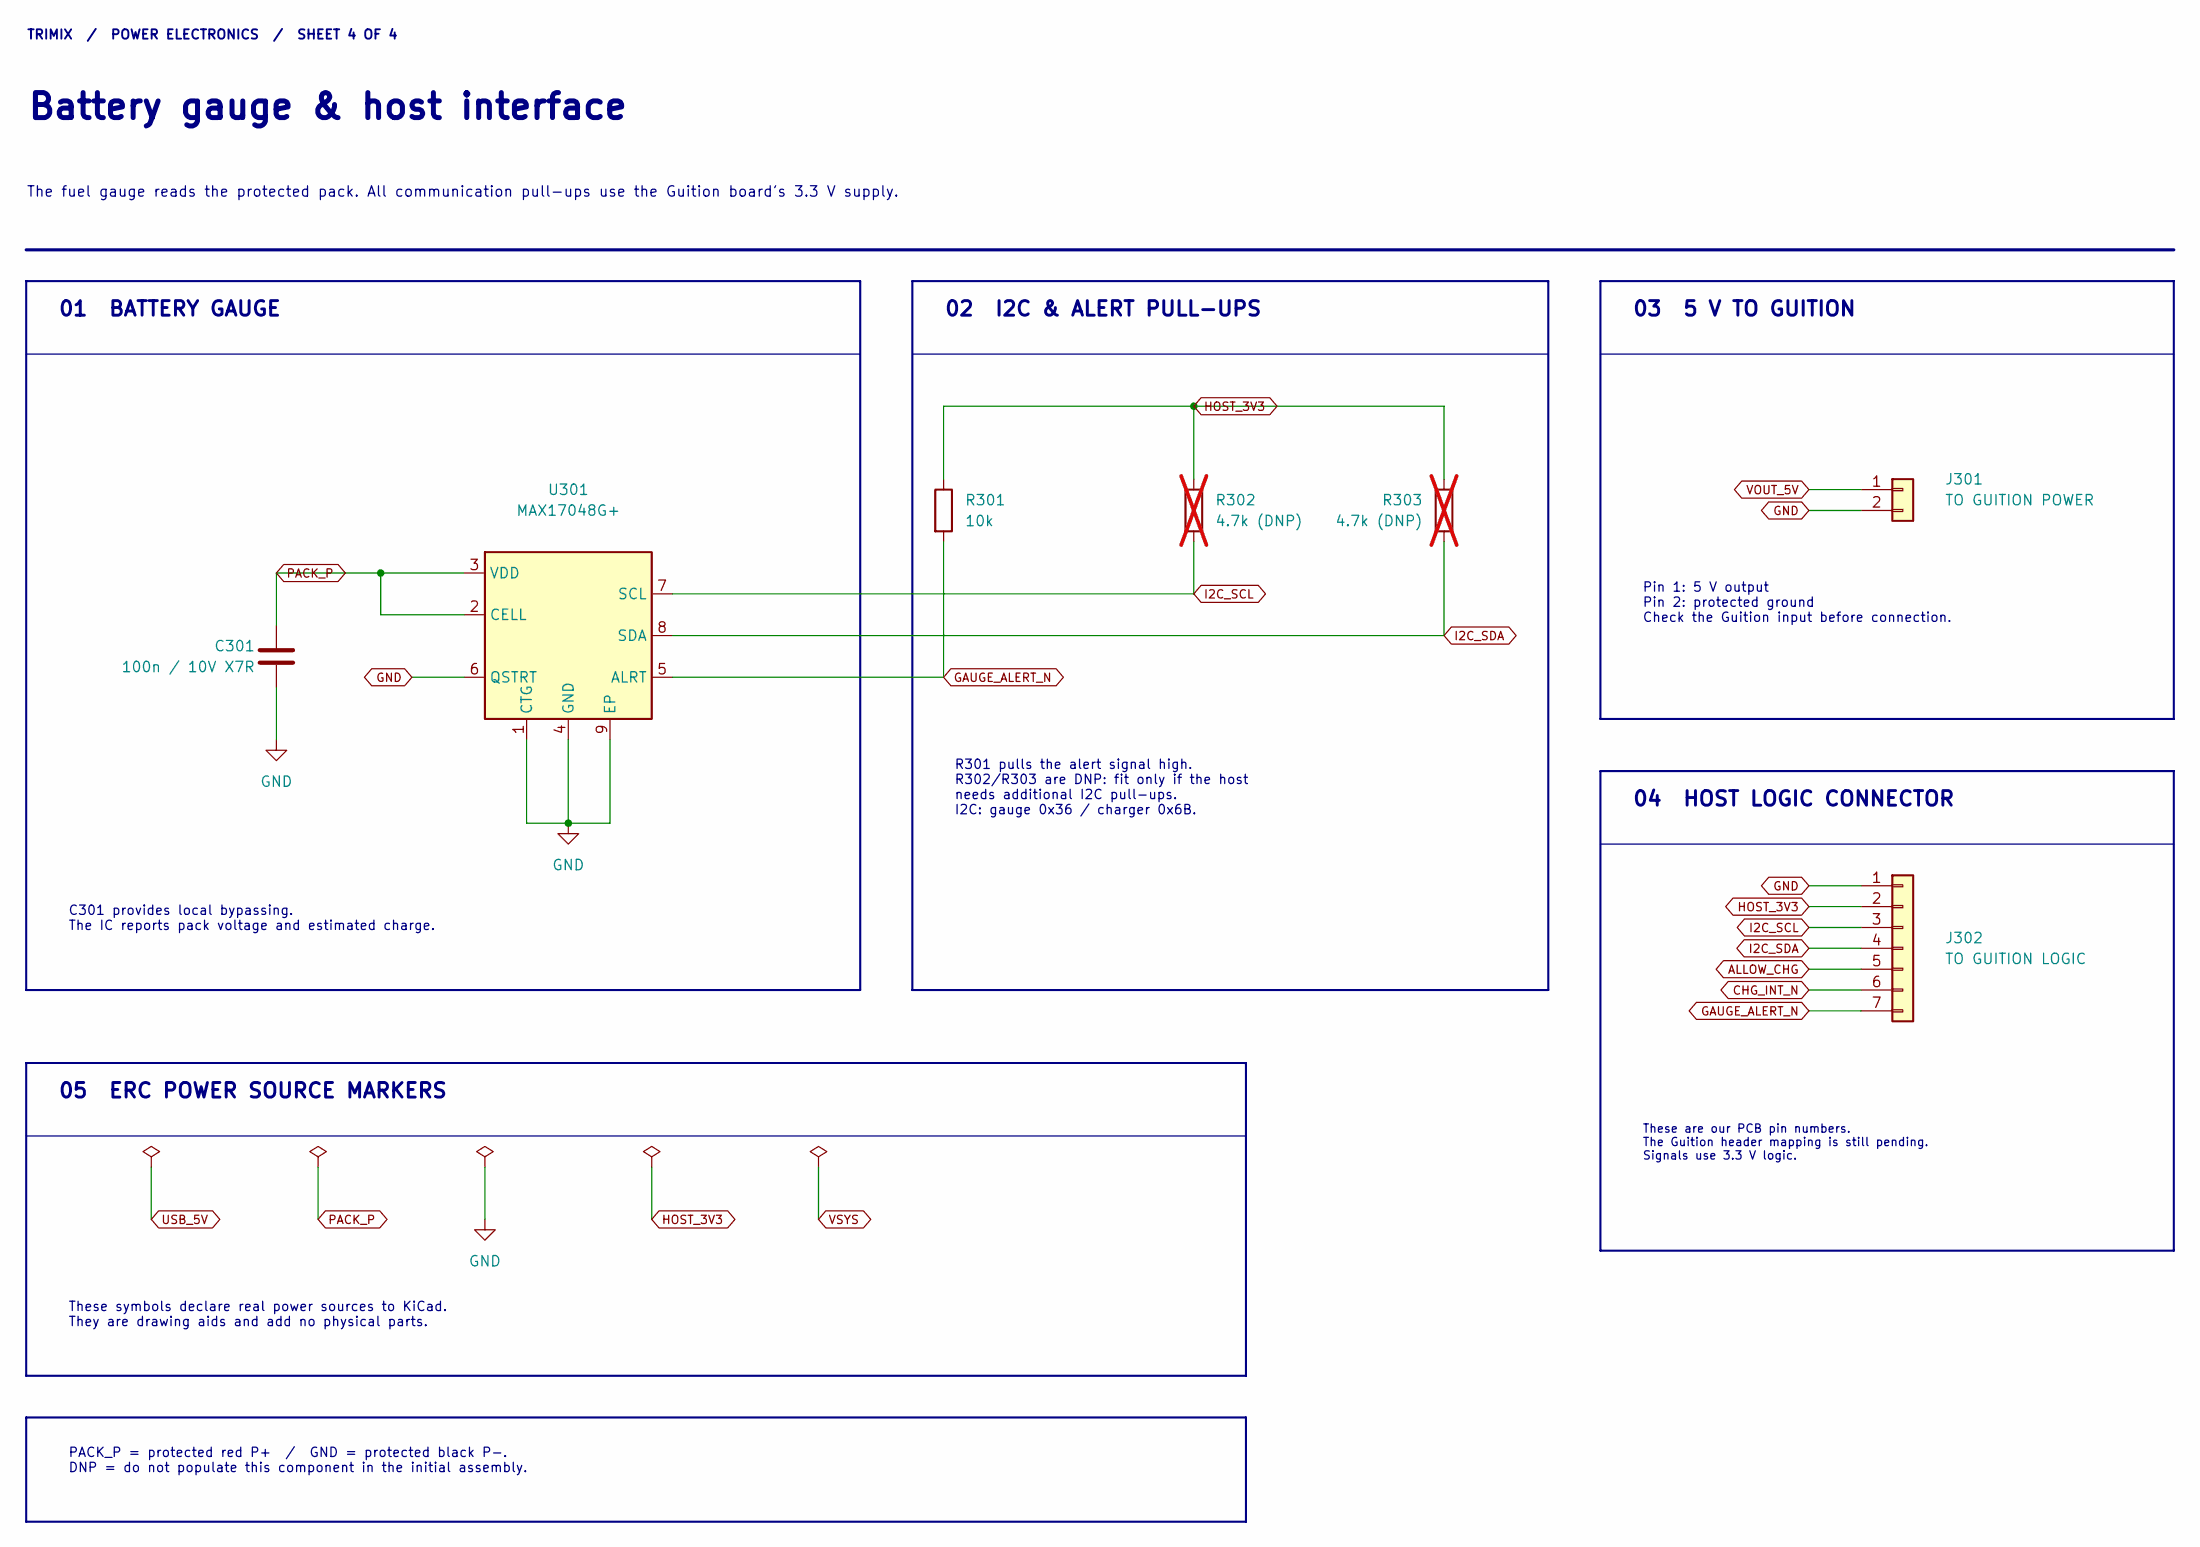
[picture p280: schematic Gauge_Interface.kicad_sch]

Parts:
C301: 100n / 10V X7R; C_0805_2012Metric
J301: TO GUITION POWER
J302: TO GUITION LOGIC
R301: 10k; R_0603_1608Metric
R302, R303: 4.7k (DNP); R_0603_1608Metric; not fitted
U301: MAX17048G+; TDFN-8-1EP_2x2mm_P0.5mm_EP0.8x1.2mm

Connections:
ALLOW_CHG: J302.5
CHG_INT_N: J302.6
GAUGE_ALERT_N: J302.7, R301.2, U301.5 (ALRT)
GND: C301.2, J301.2, J302.1, U301.1 (CTG), U301.4 (GND), U301.6 (QSTRT), U301.9 (EP)
HOST_3V3: J302.2, R301.1, R302.1, R303.1
I2C_SCL: J302.3, R302.2, U301.7 (SCL)
I2C_SDA: J302.4, R303.2, U301.8 (SDA)
PACK_P: C301.1, U301.2 (CELL), U301.3 (VDD)
VOUT_5V: J301.1

Notes on the sheet:
C301 provides local bypassing. The IC reports pack voltage and estimated charge.
TRIMIX / POWER ELECTRONICS / SHEET 4 OF 4
The fuel gauge reads the protected pack. All communication pull-ups use the Guition board's 3.3 V supply.
05 ERC POWER SOURCE MARKERS
03 5 V TO GUITION
Battery gauge & host interface
These symbols declare real power sources to KiCad. They are drawing aids and add no physical parts.
Pin 1: 5 V output Pin 2: protected ground Check the Guition input before connection.
These are our PCB pin numbers. The Guition header mapping is still pending. Signals use 3.3 V logic.
01 BATTERY GAUGE
R301 pulls the alert signal high. R302/R303 are DNP: fit only if the host needs additional I2C pull-ups. I2C: gauge 0x36 / charger 0x6B.
04 HOST LOGIC CONNECTOR
02 I2C & ALERT PULL-UPS
PACK_P = protected red P+ / GND = protected black P-. DNP = do not populate this component in the initial assembly.
