magnus188/trimix-analysator/hardware/pcb/power/Supply_5V.kicad_sch

## KiCad design hardware/pcb/power/Supply_5V.kicad_sch (2026-09-07)

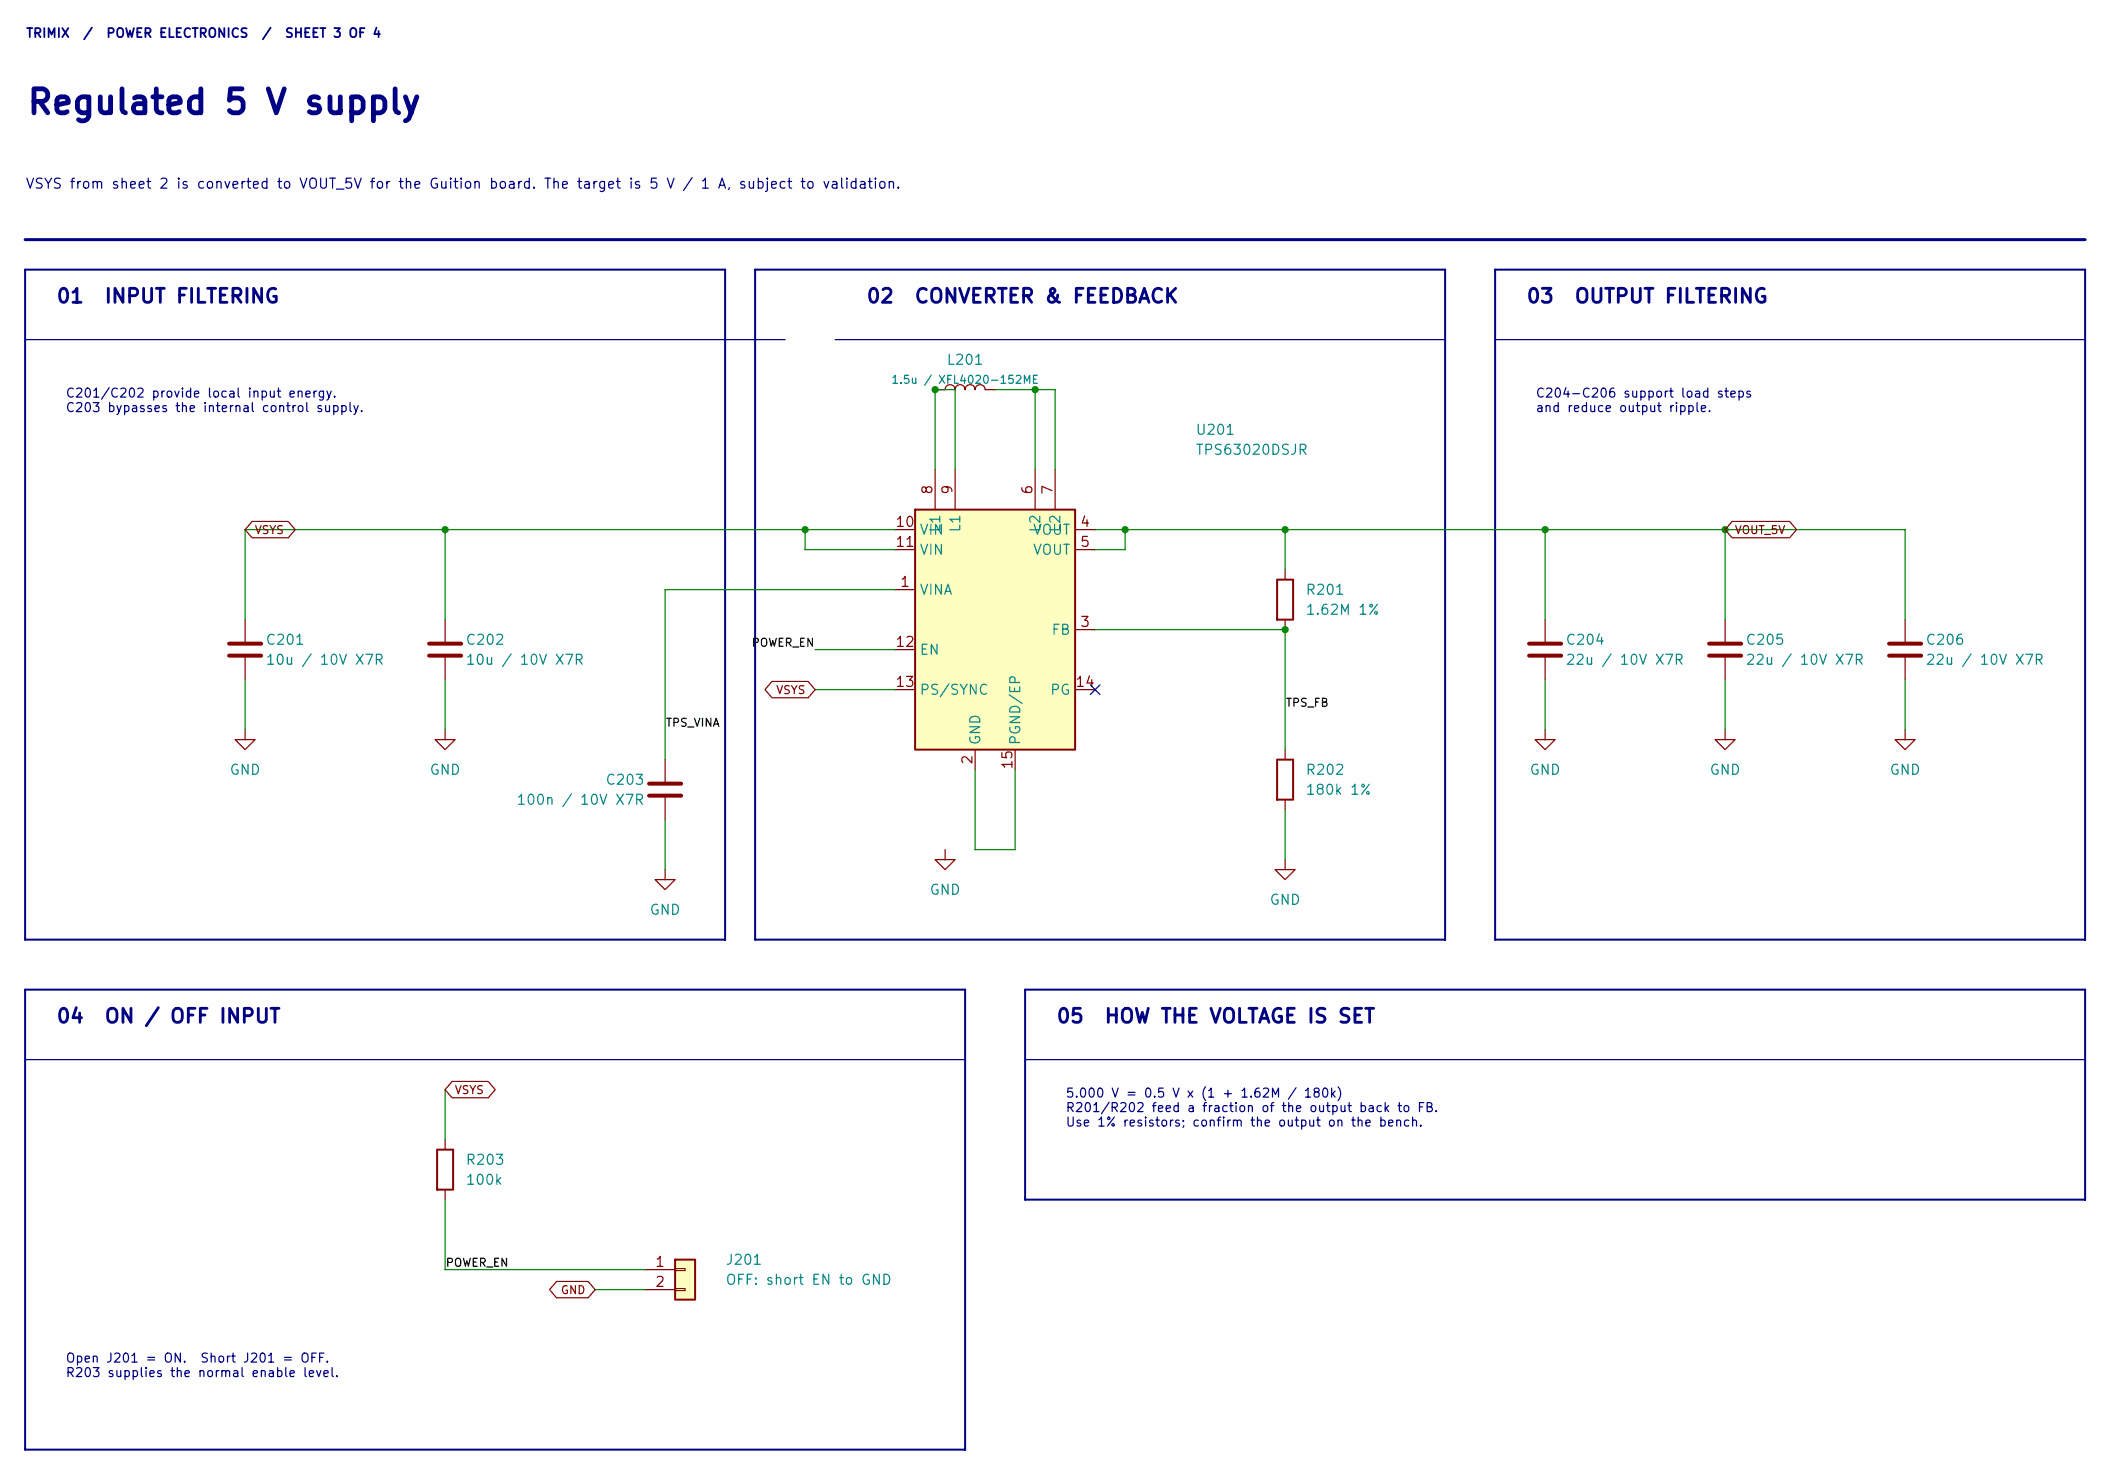
[picture p281: schematic Supply_5V.kicad_sch]

Parts:
C201, C202: 10u / 10V X7R; C_0805_2012Metric
C203: 100n / 10V X7R; C_0805_2012Metric
C204, C205, C206: 22u / 10V X7R; C_0805_2012Metric
J201: OFF: short EN to GND
L201: 1.5u / XFL4020-152ME; L_Coilcraft_XxL4020
R201: 1.62M 1%; R_0603_1608Metric
R202: 180k 1%; R_0603_1608Metric
R203: 100k; R_0603_1608Metric
U201: TPS63020DSJR; DFN-14-1EP_3x4mm_P0.5mm_EP1.7x3.3mm

Connections:
GND: C201.2, C202.2, C203.2, C204.2, C205.2, C206.2, J201.2, R202.2
unnamed: L201.1, U201.8 (L1), U201.9 (L1)
unnamed: L201.2, U201.6 (L2), U201.7 (L2)
unnamed: U201.2 (GND), U201.15 (PGND/EP)
POWER_EN: J201.1, R203.2, U201.12 (EN)
TPS_FB: R201.2, R202.1, U201.3 (FB)
TPS_VINA: C203.1, U201.1 (VINA)
VOUT_5V: C204.1, C205.1, C206.1, R201.1, U201.4 (VOUT), U201.5 (VOUT)
VSYS: C201.1, C202.1, R203.1, U201.10 (VIN), U201.11 (VIN), U201.13 (PS/SYNC)

Notes on the sheet:
02 CONVERTER & FEEDBACK
C204-C206 support load steps and reduce output ripple.
5.000 V = 0.5 V x (1 + 1.62M / 180k) R201/R202 feed a fraction of the output back to FB. Use 1% resistors; confirm the output on the bench.
VSYS from sheet 2 is converted to VOUT_5V for the Guition board. The target is 5 V / 1 A, subject to validation.
TRIMIX / POWER ELECTRONICS / SHEET 3 OF 4
05 HOW THE VOLTAGE IS SET
01 INPUT FILTERING
04 ON / OFF INPUT
Regulated 5 V supply
C201/C202 provide local input energy. C203 bypasses the internal control supply.
03 OUTPUT FILTERING
Open J201 = ON. Short J201 = OFF. R203 supplies the normal enable level.
