magnus188/trimix-analysator/hardware/pcb/usb-input/Trimix_USB_Input.kicad_sch

## KiCad design hardware/pcb/usb-input/Trimix_USB_Input.kicad_sch (2026-09-09)



Parts:
D901: TPD1E10B06DYAR; TI_DYA0002A; MPN TPD1E10B06DYAR
J901: USB4720-03-A; USB4720_RevB; MPN USB4720-03-A
J902: TO MAIN J101 | SAME PIN NUMBERS; USB_Harness_6P_P1.8mm
U901: TPD4E05U06DQAR; TI_DQA0010B; MPN TPD4E05U06DQAR

Connections:
GND: D901.2 (GND), J901.A1 (GND), J901.A12 (GND), J901.B1 (GND), J901.B12 (GND), J901.SH (SHIELD), J902.2, U901.3 (GND), U901.8 (GND)
USB_5V: D901.1 (VBUS), J901.A4 (VBUS), J901.A9 (VBUS), J901.B4 (VBUS), J901.B9 (VBUS), J902.1
USB_CC1: J901.A5 (CC1), J902.3, U901.1 (CC1), U901.10 (NC / PCB link)
USB_CC2: J901.B5 (CC2), J902.4, U901.2 (CC2), U901.9 (NC / PCB link)
USB_D_M: J901.A7 (D-), J901.B7 (D-), J902.6, U901.5 (D-), U901.6 (NC / PCB link)
USB_D_P: J901.A6 (D+), J901.B6 (D+), J902.5, U901.4 (D+), U901.7 (NC / PCB link)

Notes on the sheet:
TRIMIX USB INPUT | GCT + ESD + SIX-WIRE HARNESS
Dedicated 0.60 +/-0.10 mm board. Nominal 5 V input; USB-C attachment and BC1.2 detection are on the main PCB.
01 SEALED USB-C RECEPTACLE
02 FOUR-LINE + VBUS ESD PROTECTION
03 SIX-WIRE OUTPUT
04 ASSEMBLY AND QUALIFICATION
Shield and all ground contacts join GND. A6/B6 join D+; A7/B7 join D-. SBU is NC. No local Rd: TUSB320LAI on main PCB supplies Rd.
No internal links on pins6/7/9/10. PCB copper joins 1-10(CC1),2-9(CC2),4-7(D+),5-6(D-). D901 surge clamp exceeds 6 V: upstream transient coordination remains a main-system requirement.
1 = USB_5V 2 = GND 3 = CC1 4 = CC2 5 = D+ 6 = D- Do not swap CC/data wires or populate old Rd.
GCT Rev B cutout and fixed connector pose retained. No copper-edge exception rule;0.10mm GCT edge margin needs closure. Factory stencil/reflow for U901; support the port internally. Measure harness/solder height inside the 5.7 mm gap. No 9/12/20 V request; tests required for both cable orientations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
