magnus188/trimix-analysator/hardware/system-review/electrical/before-local-input-cap.kicad_sch

## KiCad design hardware/system-review/electrical/before-local-input-cap.kicad_sch (2026-09-09)

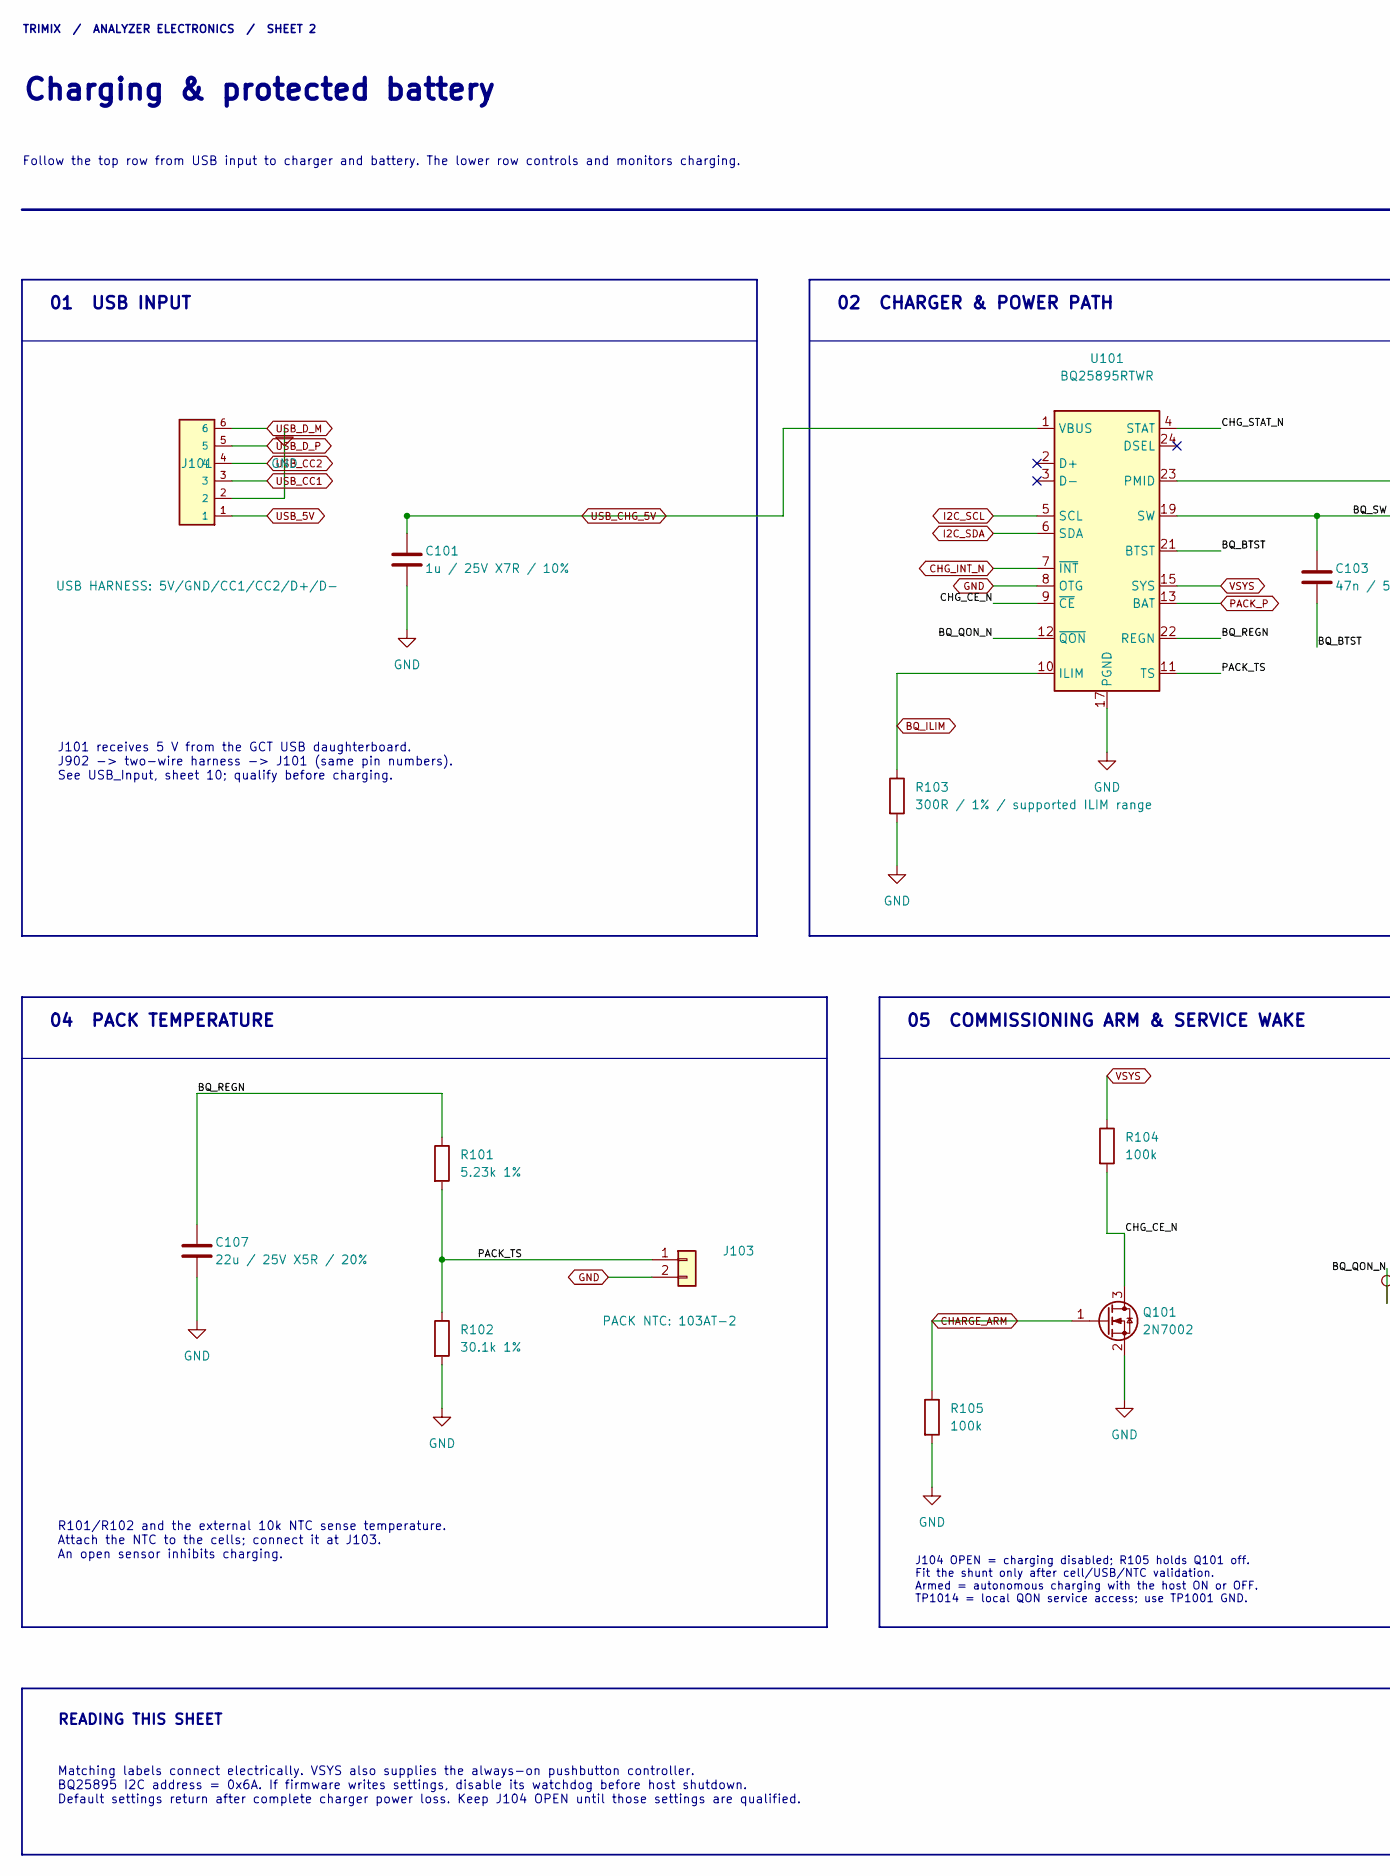
[picture p282: schematic before-local-input-cap.kicad_sch, part in row 1, column 1]


Parts:
C101: 1u / 25V X7R / 10%; C_0805_2012Metric; MPN C2012X7R1E105K125AB
C102, C104, C105: 22u / 16V X7R / 20%; C_1210_3225Metric; MPN C3225X7R1C226M250AC
C103: 47n / 50V X7R / 10%; C_0805_2012Metric; MPN C0805C473K5RACTU
C106, C107: 22u / 25V X5R / 20%; C_1206_3216Metric; MPN C3216X5R1E226M160AB
C108: 4.7u / 16V X5R / 10%; C_0603_1608Metric; MPN C1608X5R1C475K080AC
J101: USB HARNESS: 5V/GND/CC1/CC2/D+/D-; USB_Harness_6P_P1.8mm
J102: PACK PIGTAIL; Battery_Pigtail_2x22AWG_P4.2_D1.00_Pad1.85
J103: PACK NTC: 103AT-2; PinHeader_1x02_P2.54mm_Vertical; MPN M20-9990246
J104: ARM: OPEN; PinHeader_1x02_P2.54mm_Vertical; MPN M20-9990246
L101: 1u / 74437349010; L_Wurth_74437349010_7050; MPN 74437349010
Q101: 2N7002; SOT-23; MPN 2N7002-7-F
R101: 5.23k 1%; R_0603_1608Metric; MPN RC0603FR-075K23L
R102: 30.1k 1%; R_0603_1608Metric; MPN RC0603FR-0730K1L
R103: 300R / 1% / supported ILIM range; R_0603_1608Metric; MPN RC0603FR-07300RL
R104, R105: 100k; R_0603_1608Metric; MPN RC0603FR-07100KL
R107: 10k; R_0603_1608Metric; MPN RC0603FR-0710KL
TP1013: CHG_STAT_N; TestPoint_Pad_D0.8mm
TP1014: QON SERVICE; TestPoint_Pad_D0.8mm
U101: BQ25895RTWR; TI_RTW24_4x4_ThermalVias_ServicePad; MPN BQ25895RTWR

Connections:
BQ_BTST: C103.2, U101.21 (BTST)
BQ_ILIM: R103.1, U101.10 (ILIM)
BQ_PMID: C102.1, U101.23 (PMID)
BQ_QON_N: TP1014.1, U101.12 (~QON)
BQ_REGN: C107.1, R101.1, U101.22 (REGN)
BQ_SW: C103.1, L101.1, U101.19 (SW), U101.20 (SW)
CHARGE_ARM: J104.2 (B), Q101.1 (G), R105.1
CHG_CE_N: Q101.3 (D), R104.2, U101.9 (~CE)
CHG_INT_N: R107.2, U101.7 (~INT)
CHG_STAT_N: TP1013.1, U101.4 (STAT)
GND: C101.2, C102.2, C104.2, C105.2, C106.2, C107.2, C108.2, J101.2, J102.2, J103.2, Q101.2 (S), R102.2, R103.2, R105.2, U101.8 (OTG), U101.17 (PGND), U101.18 (PGND), U101.25 (PGND)
HOST_3V3: R107.1
I2C_SCL: U101.5 (SCL)
I2C_SDA: U101.6 (SDA)
PACK_P: C106.1, J102.1, U101.13 (BAT), U101.14 (BAT)
PACK_TS: J103.1, R101.2, R102.1, U101.11 (TS)
USB_5V: J101.1
USB_CC1: J101.3
USB_CC2: J101.4
USB_CHG_5V: C101.1, U101.1 (VBUS)
USB_D_M: J101.6
USB_D_P: J101.5
VSYS: C104.1, C105.1, C108.1, J104.1 (A), L101.2, R104.1, U101.15 (SYS), U101.16 (SYS)

Notes on the sheet:
05 COMMISSIONING ARM & SERVICE WAKE
C108 supplements the retained C104/C105 SYS bulk. TP1013 exposes charger STAT on the board rear. R107 pulls charger/permission feedback up to 3.3 V.
Follow the top row from USB input to charger and battery. The lower row controls and monitors charging.
02 CHARGER & POWER PATH
Charging & protected battery
01 USB INPUT
03 PROTECTED BATTERY
TRIMIX / ANALYZER ELECTRONICS / SHEET 2
Matching labels connect electrically. VSYS also supplies the always-on pushbutton controller. BQ25895 I2C address = 0x6A. If firmware writes settings, disable its watchdog before host shutdown. Default settings return after complete charger power loss. Keep J104 OPEN until those settings are qualif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
R101/R102 and the external 10k NTC sense temperature. Attach the NTC to the cells; connect it at J103. An open sensor inhibits charging.
J104 OPEN = charging disabled; R105 holds Q101 off. Fit the shunt only after cell/USB/NTC validation. Armed = autonomous charging with the host ON or OFF. TP1014 = local QON service access; use TP1001 GND.
04 PACK TEMPERATURE
J101 receives 5 V from the GCT USB daughterboard. J902 -> two-wire harness -> J101 (same pin numbers). See USB_Input, sheet 10; qualify before charging.
Autonomous defaults: 4.208 V, 2.048 A charge setting. Floating D+/D- selects 500 mA input; actual charge current falls to match input power. ILIM: 300R (~0.57 A). No charger firmware is implemented; defaults need review.
06 STATUS INDICATORS
J102 = PCB pigtail to the RCY/BEC cable mate. Red = protected P+; black = protected P-. FMA holder: 2 x 3400 mAh in parallel, 6800 mAh total. Verify polarity; no PCB-mounted RCY footprint is implied.
READING THIS SHEET
