magnus188/trimix-analysator/hardware/system-review/electrical/before-host-isolation/Gauge_Interface.kicad_sch

## KiCad design hardware/system-review/electrical/before-host-isolation/Gauge_Interface.kicad_sch (2026-09-07)

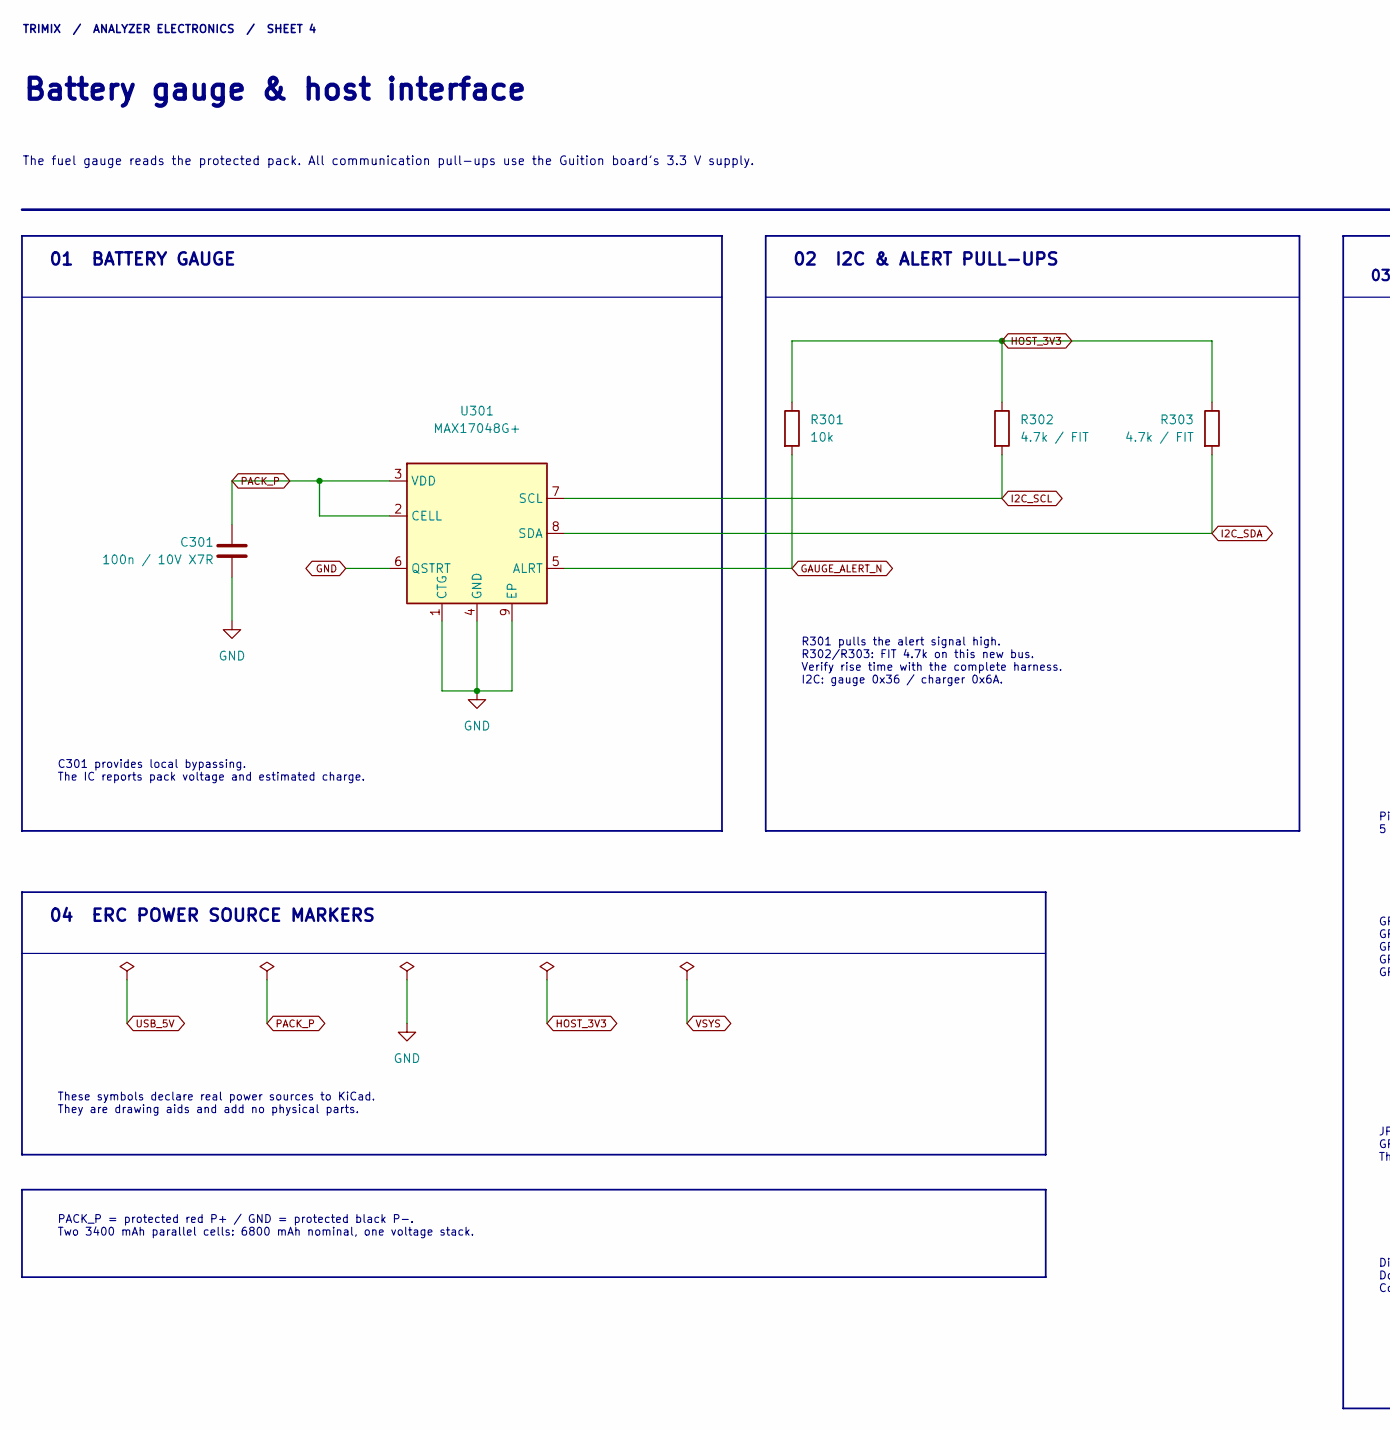
[picture p285: schematic Gauge_Interface.kicad_sch, part in row 1, column 1]

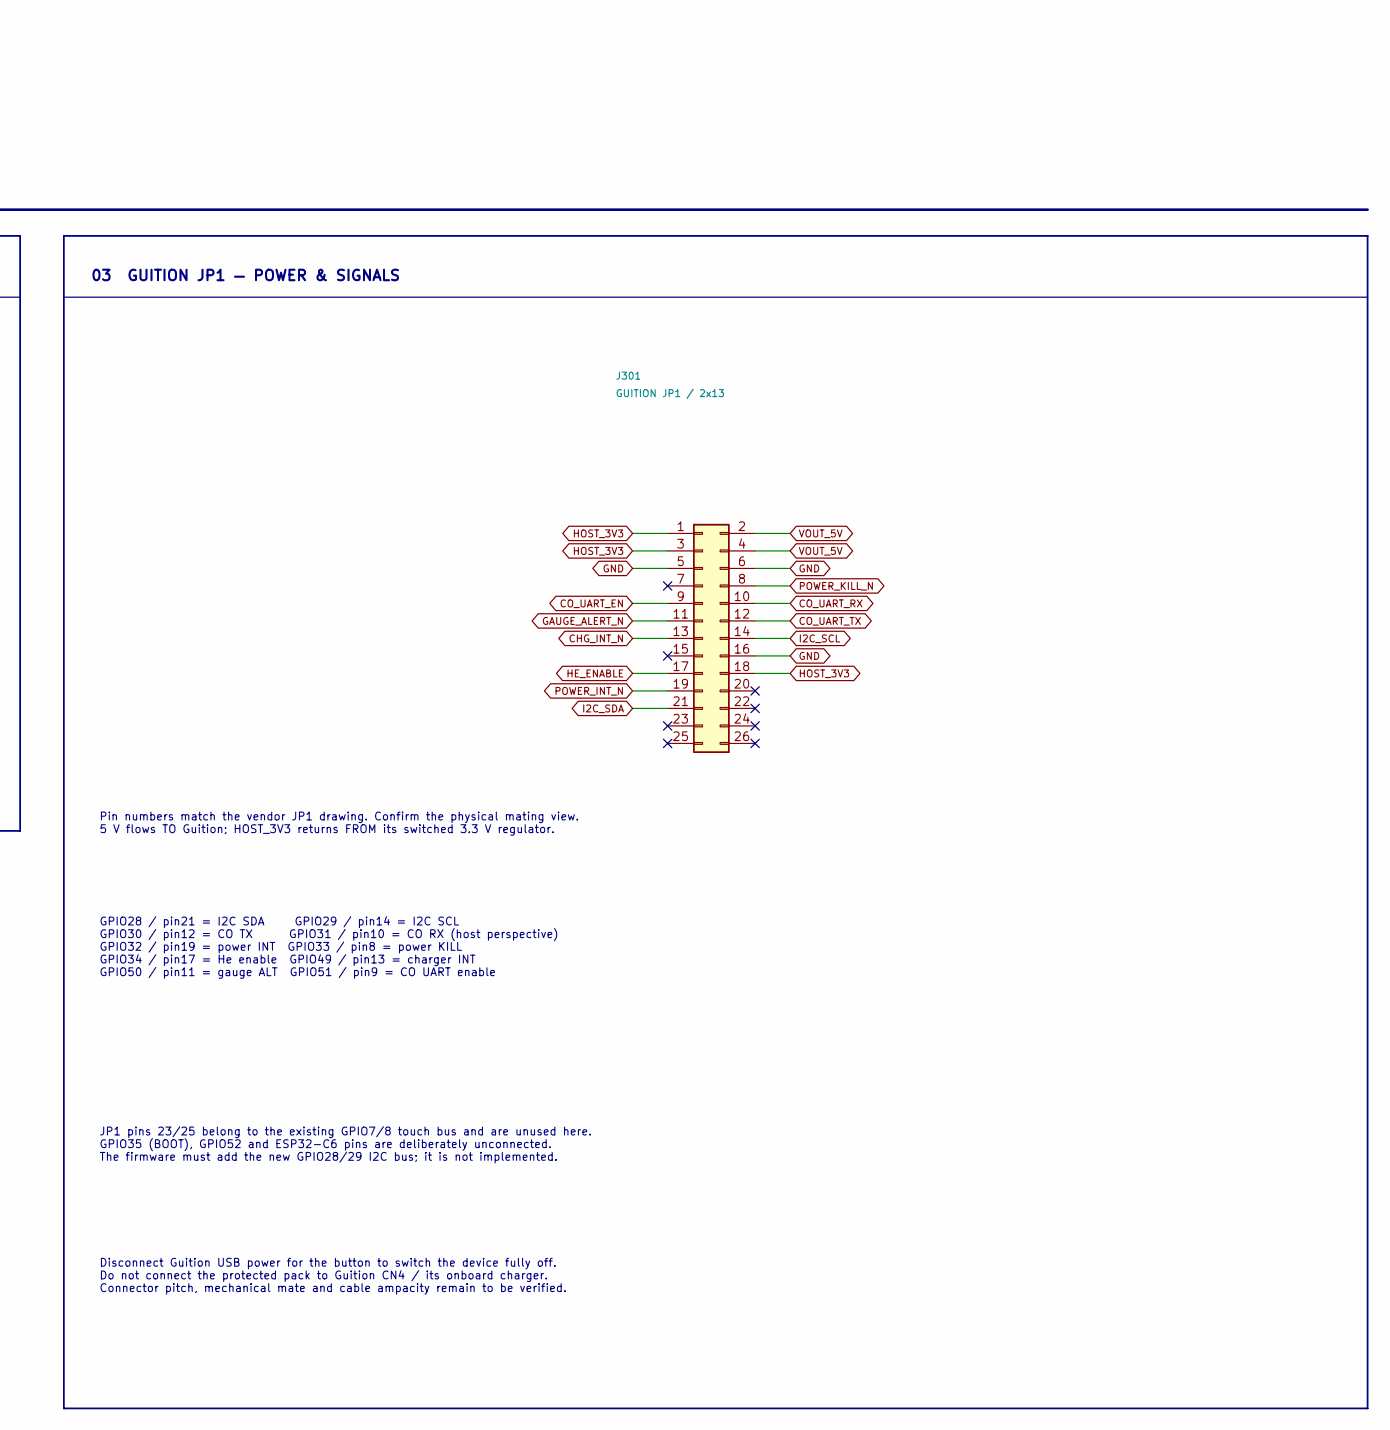
[picture p286: schematic Gauge_Interface.kicad_sch, part in row 1, column 2]

Parts:
C301: 100n / 10V X7R; C_0805_2012Metric
J301: GUITION JP1 / 2x13; PinHeader_2x13_P2.54mm_Vertical
R301: 10k; R_0603_1608Metric
R302, R303: 4.7k / FIT; R_0603_1608Metric
U301: MAX17048G+; TDFN-8-1EP_2x2mm_P0.5mm_EP0.8x1.2mm

Connections:
CHG_INT_N: J301.13
CO_UART_EN: J301.9
CO_UART_RX: J301.10
CO_UART_TX: J301.12
GAUGE_ALERT_N: J301.11, R301.2, U301.5 (ALRT)
GND: C301.2, J301.5, J301.6, J301.16, U301.1 (CTG), U301.4 (GND), U301.6 (QSTRT), U301.9 (EP)
HE_ENABLE: J301.17
HOST_3V3: J301.1, J301.3, J301.18, R301.1, R302.1, R303.1
I2C_SCL: J301.14, R302.2, U301.7 (SCL)
I2C_SDA: J301.21, R303.2, U301.8 (SDA)
PACK_P: C301.1, U301.2 (CELL), U301.3 (VDD)
POWER_INT_N: J301.19
POWER_KILL_N: J301.8
VOUT_5V: J301.2, J301.4

Notes on the sheet:
Pin numbers match the vendor JP1 drawing. Confirm the physical mating view. 5 V flows TO Guition; HOST_3V3 returns FROM its switched 3.3 V regulator.
C301 provides local bypassing. The IC reports pack voltage and estimated charge.
TRIMIX / ANALYZER ELECTRONICS / SHEET 4
The fuel gauge reads the protected pack. All communication pull-ups use the Guition board's 3.3 V supply.
04 ERC POWER SOURCE MARKERS
03 GUITION JP1 — POWER & SIGNALS
Battery gauge & host interface
These symbols declare real power sources to KiCad. They are drawing aids and add no physical parts.
GPIO28 / pin21 = I2C SDA GPIO29 / pin14 = I2C SCL GPIO30 / pin12 = CO TX GPIO31 / pin10 = CO RX (host perspective) GPIO32 / pin19 = power INT GPIO33 / pin8 = power KILL GPIO34 / pin17 = He enable GPIO49 / pin13 = charger INT GPIO50 / pin11 = gauge ALT GPIO51 / pin9 = CO UART enable
01 BATTERY GAUGE
R301 pulls the alert signal high. R302/R303: FIT 4.7k on this new bus. Verify rise time with the complete harness. I2C: gauge 0x36 / charger 0x6A.
02 I2C & ALERT PULL-UPS
JP1 pins 23/25 belong to the existing GPIO7/8 touch bus and are unused here. GPIO35 (BOOT), GPIO52 and ESP32-C6 pins are deliberately unconnected. The firmware must add the new GPIO28/29 I2C bus; it is not implemented.
PACK_P = protected red P+ / GND = protected black P-. Two 3400 mAh parallel cells: 6800 mAh nominal, one voltage stack.
Disconnect Guition USB power for the button to switch the device fully off. Do not connect the protected pack to Guition CN4 / its onboard charger. Connector pitch, mechanical mate and cable ampacity remain to be verified.
