magnus188/trimix-analysator/hardware/system-review/electrical/before-inductor-selection/Carbon_Monoxide.kicad_sch

## KiCad design hardware/system-review/electrical/before-inductor-selection/Carbon_Monoxide.kicad_sch (2026-09-09)

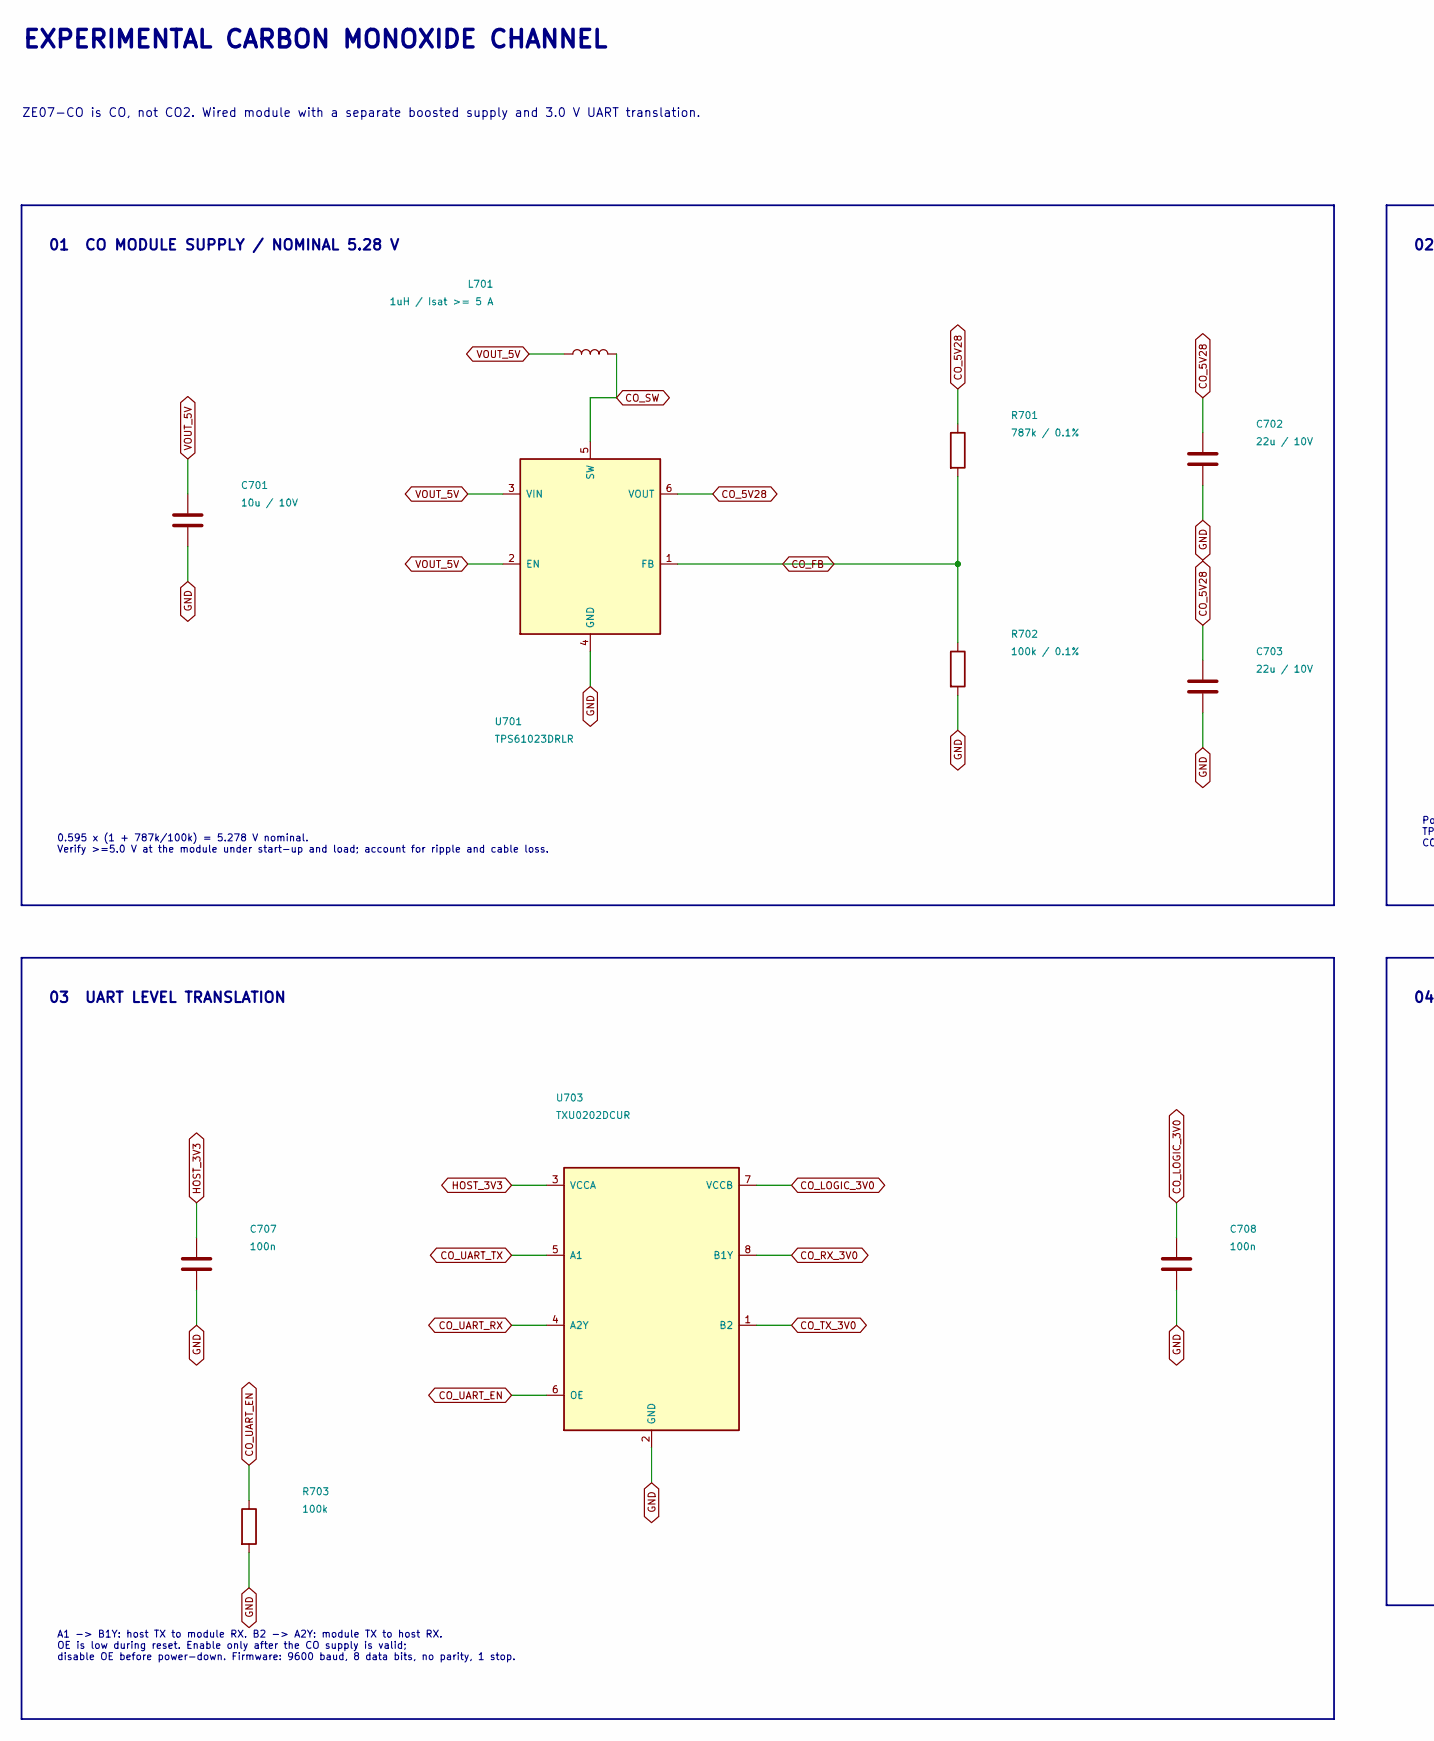
[picture p287: schematic Carbon_Monoxide.kicad_sch, part in row 1, column 1]

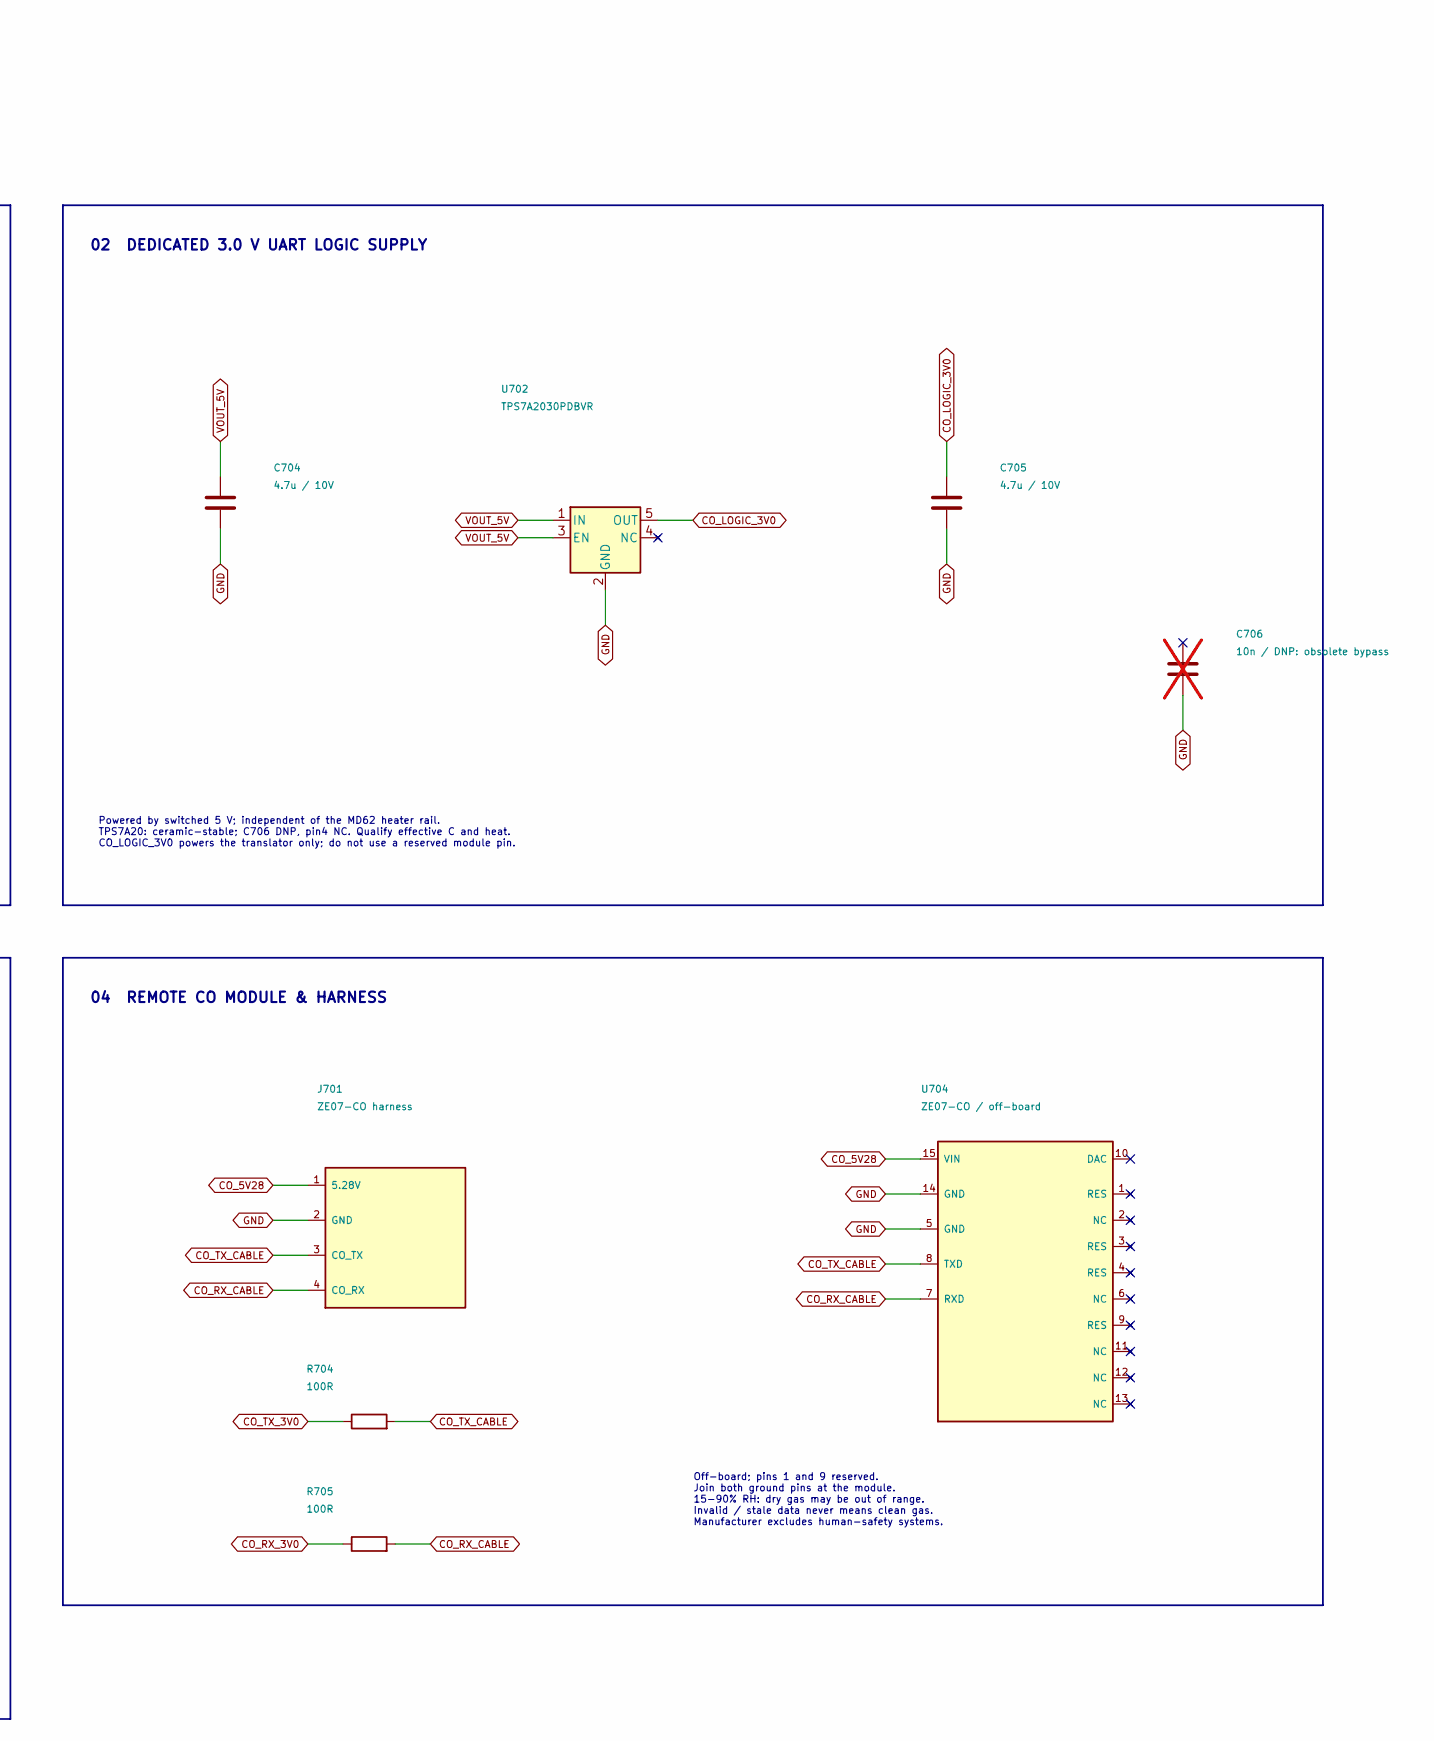
[picture p288: schematic Carbon_Monoxide.kicad_sch, part in row 1, column 2]

Parts:
C701: 10u / 10V; C_0805_2012Metric
C702, C703: 22u / 10V; C_0805_2012Metric
C704, C705: 4.7u / 10V; C_0805_2012Metric
C706: 10n / DNP: obsolete bypass; C_0805_2012Metric; not fitted
C707, C708: 100n; C_0805_2012Metric
J701: ZE07-CO harness; JST_XH_B4B-XH-A_1x04_P2.50mm_Vertical
L701: 1uH / Isat >= 5 A; L_Taiyo-Yuden_NR-40xx
R701: 787k / 0.1%; R_0603_1608Metric
R702: 100k / 0.1%; R_0603_1608Metric
R703: 100k; R_0603_1608Metric
R704, R705: 100R; R_0603_1608Metric
U701: TPS61023DRLR; SOT-563
U702: TPS7A2030PDBVR; SOT-23-5; MPN TPS7A2030PDBVR
U703: TXU0202DCUR; VSSOP-8_2.3x2mm_P0.5mm
U704: ZE07-CO / off-board

Connections:
CO_5V28: C702.1, C703.1, J701.1 (5.28V), R701.1, U701.6 (VOUT), U704.15 (VIN)
CO_FB: R701.2, R702.1, U701.1 (FB)
CO_LOGIC_3V0: C705.1, C708.1, U702.5 (OUT), U703.7 (VCCB)
CO_RX_3V0: R705.1, U703.8 (B1Y)
CO_RX_CABLE: J701.4 (CO_RX), R705.2, U704.7 (RXD)
CO_SW: L701.2, U701.5 (SW)
CO_TX_3V0: R704.1, U703.1 (B2)
CO_TX_CABLE: J701.3 (CO_TX), R704.2, U704.8 (TXD)
CO_UART_EN: R703.1, U703.6 (OE)
CO_UART_RX: U703.4 (A2Y)
CO_UART_TX: U703.5 (A1)
GND: C701.2, C702.2, C703.2, C704.2, C705.2, C706.2, C707.2, C708.2, J701.2 (GND), R702.2, R703.2, U701.4 (GND), U702.2 (GND), U703.2 (GND), U704.5 (GND), U704.14 (GND)
HOST_3V3: C707.1, U703.3 (VCCA)
VOUT_5V: C701.1, C704.1, L701.1, U701.2 (EN), U701.3 (VIN), U702.1 (IN), U702.3 (EN)

Notes on the sheet:
ZE07-CO is CO, not CO2. Wired module with a separate boosted supply and 3.0 V UART translation.
Powered by switched 5 V; independent of the MD62 heater rail. TPS7A20: ceramic-stable; C706 DNP, pin4 NC. Qualify effective C and heat. CO_LOGIC_3V0 powers the translator only; do not use a reserved module pin.
EXPERIMENTAL CARBON MONOXIDE CHANNEL
A1 -> B1Y: host TX to module RX. B2 -> A2Y: module TX to host RX. OE is low during reset. Enable only after the CO supply is valid; disable OE before power-down. Firmware: 9600 baud, 8 data bits, no parity, 1 stop.
0.595 x (1 + 787k/100k) = 5.278 V nominal. Verify >=5.0 V at the module under start-up and load; account for ripple and cable loss.
04 REMOTE CO MODULE & HARNESS
03 UART LEVEL TRANSLATION
Off-board; pins 1 and 9 reserved. Join both ground pins at the module. 15-90% RH: dry gas may be out of range. Invalid / stale data never means clean gas. Manufacturer excludes human-safety systems.
01 CO MODULE SUPPLY / NOMINAL 5.28 V
02 DEDICATED 3.0 V UART LOGIC SUPPLY
