magnus188/trimix-analysator/hardware/system-review/electrical/before-inductor-selection/Charging.kicad_sch

## KiCad design hardware/system-review/electrical/before-inductor-selection/Charging.kicad_sch (2026-09-07)

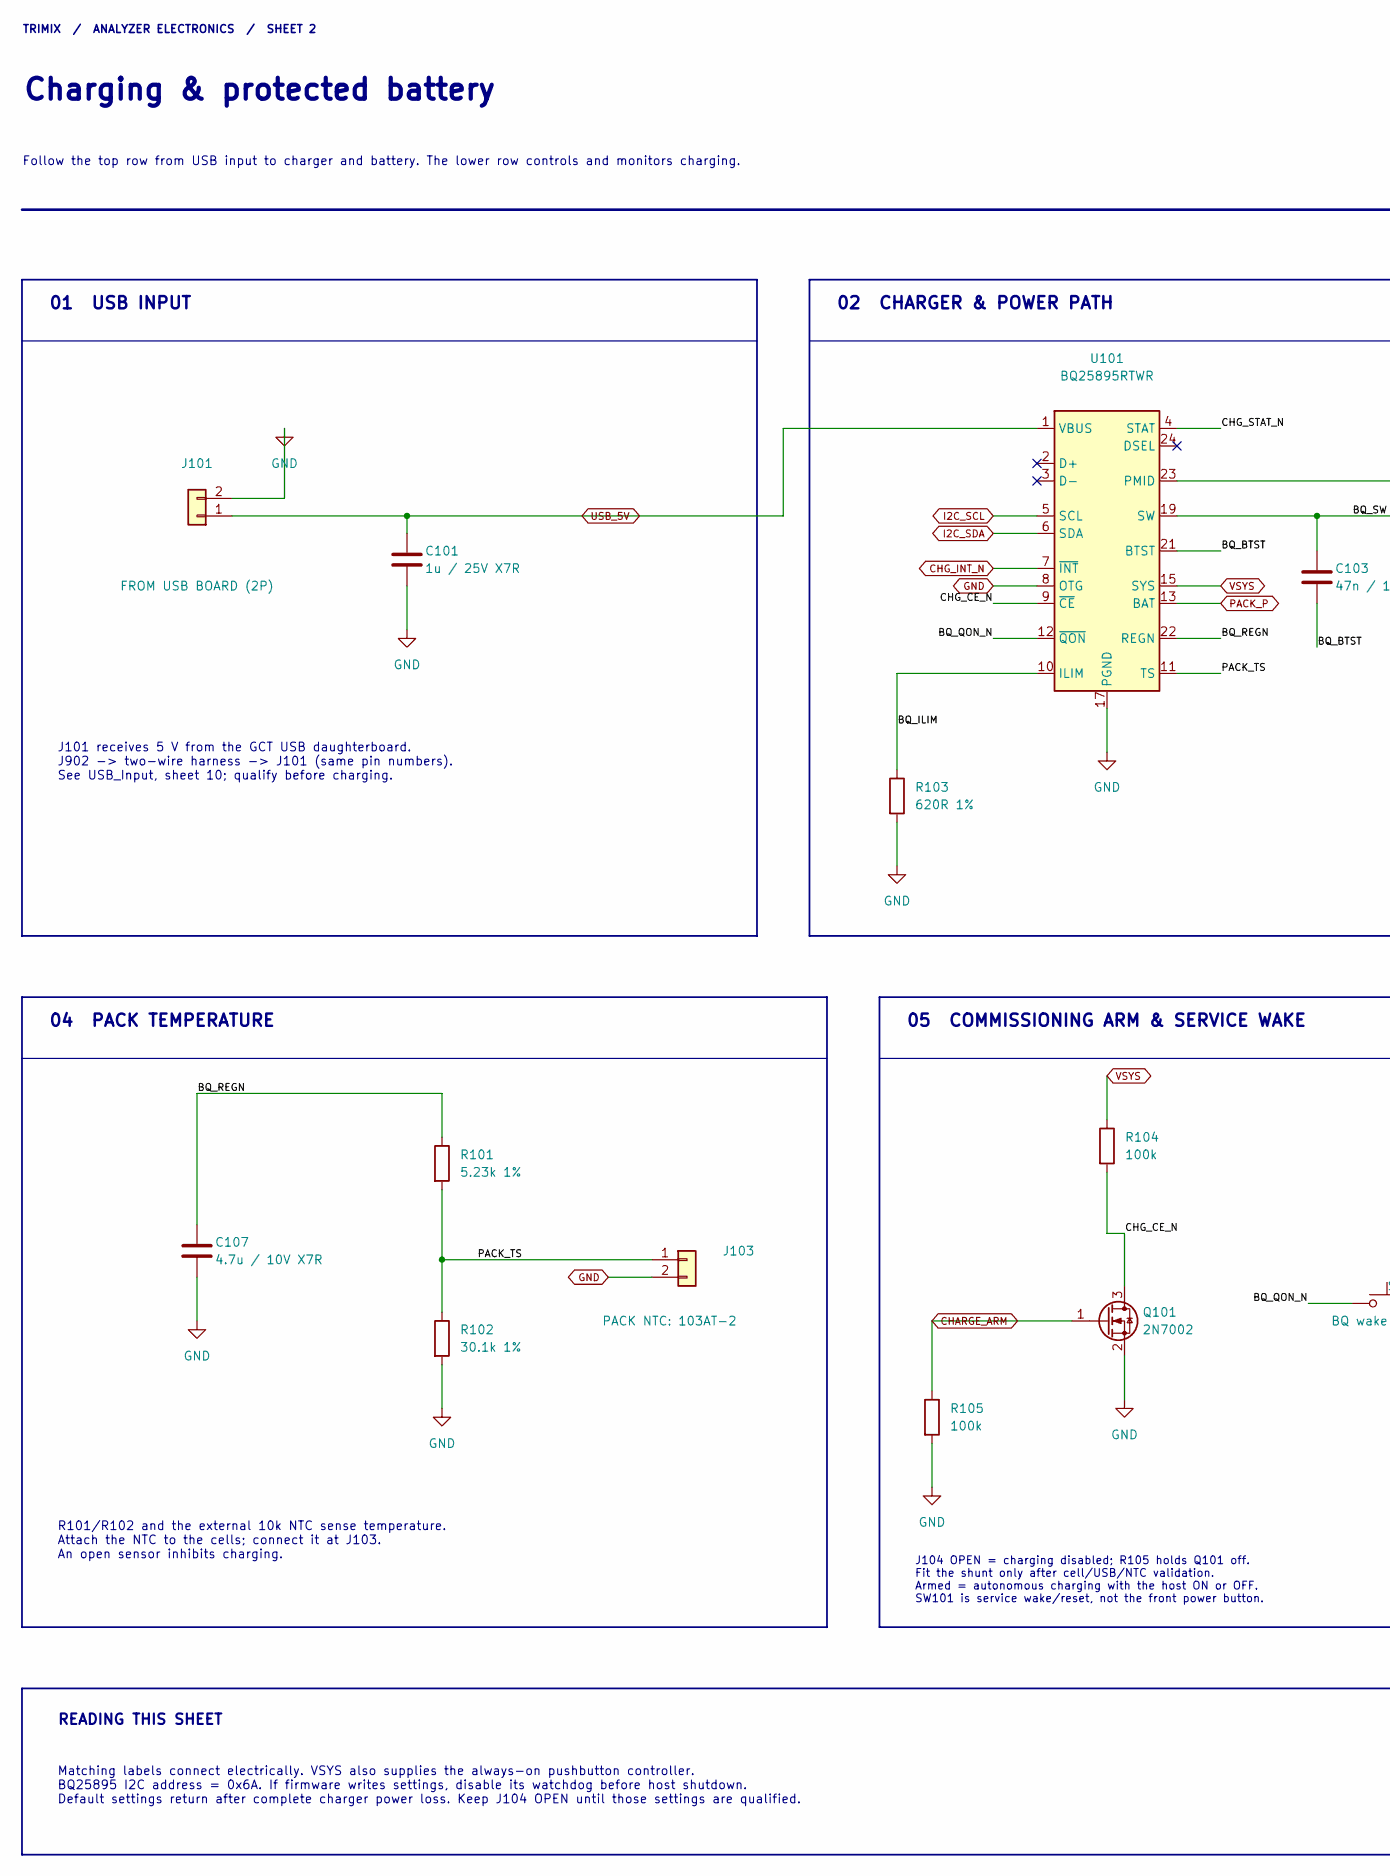
[picture p289: schematic Charging.kicad_sch, part in row 1, column 1]

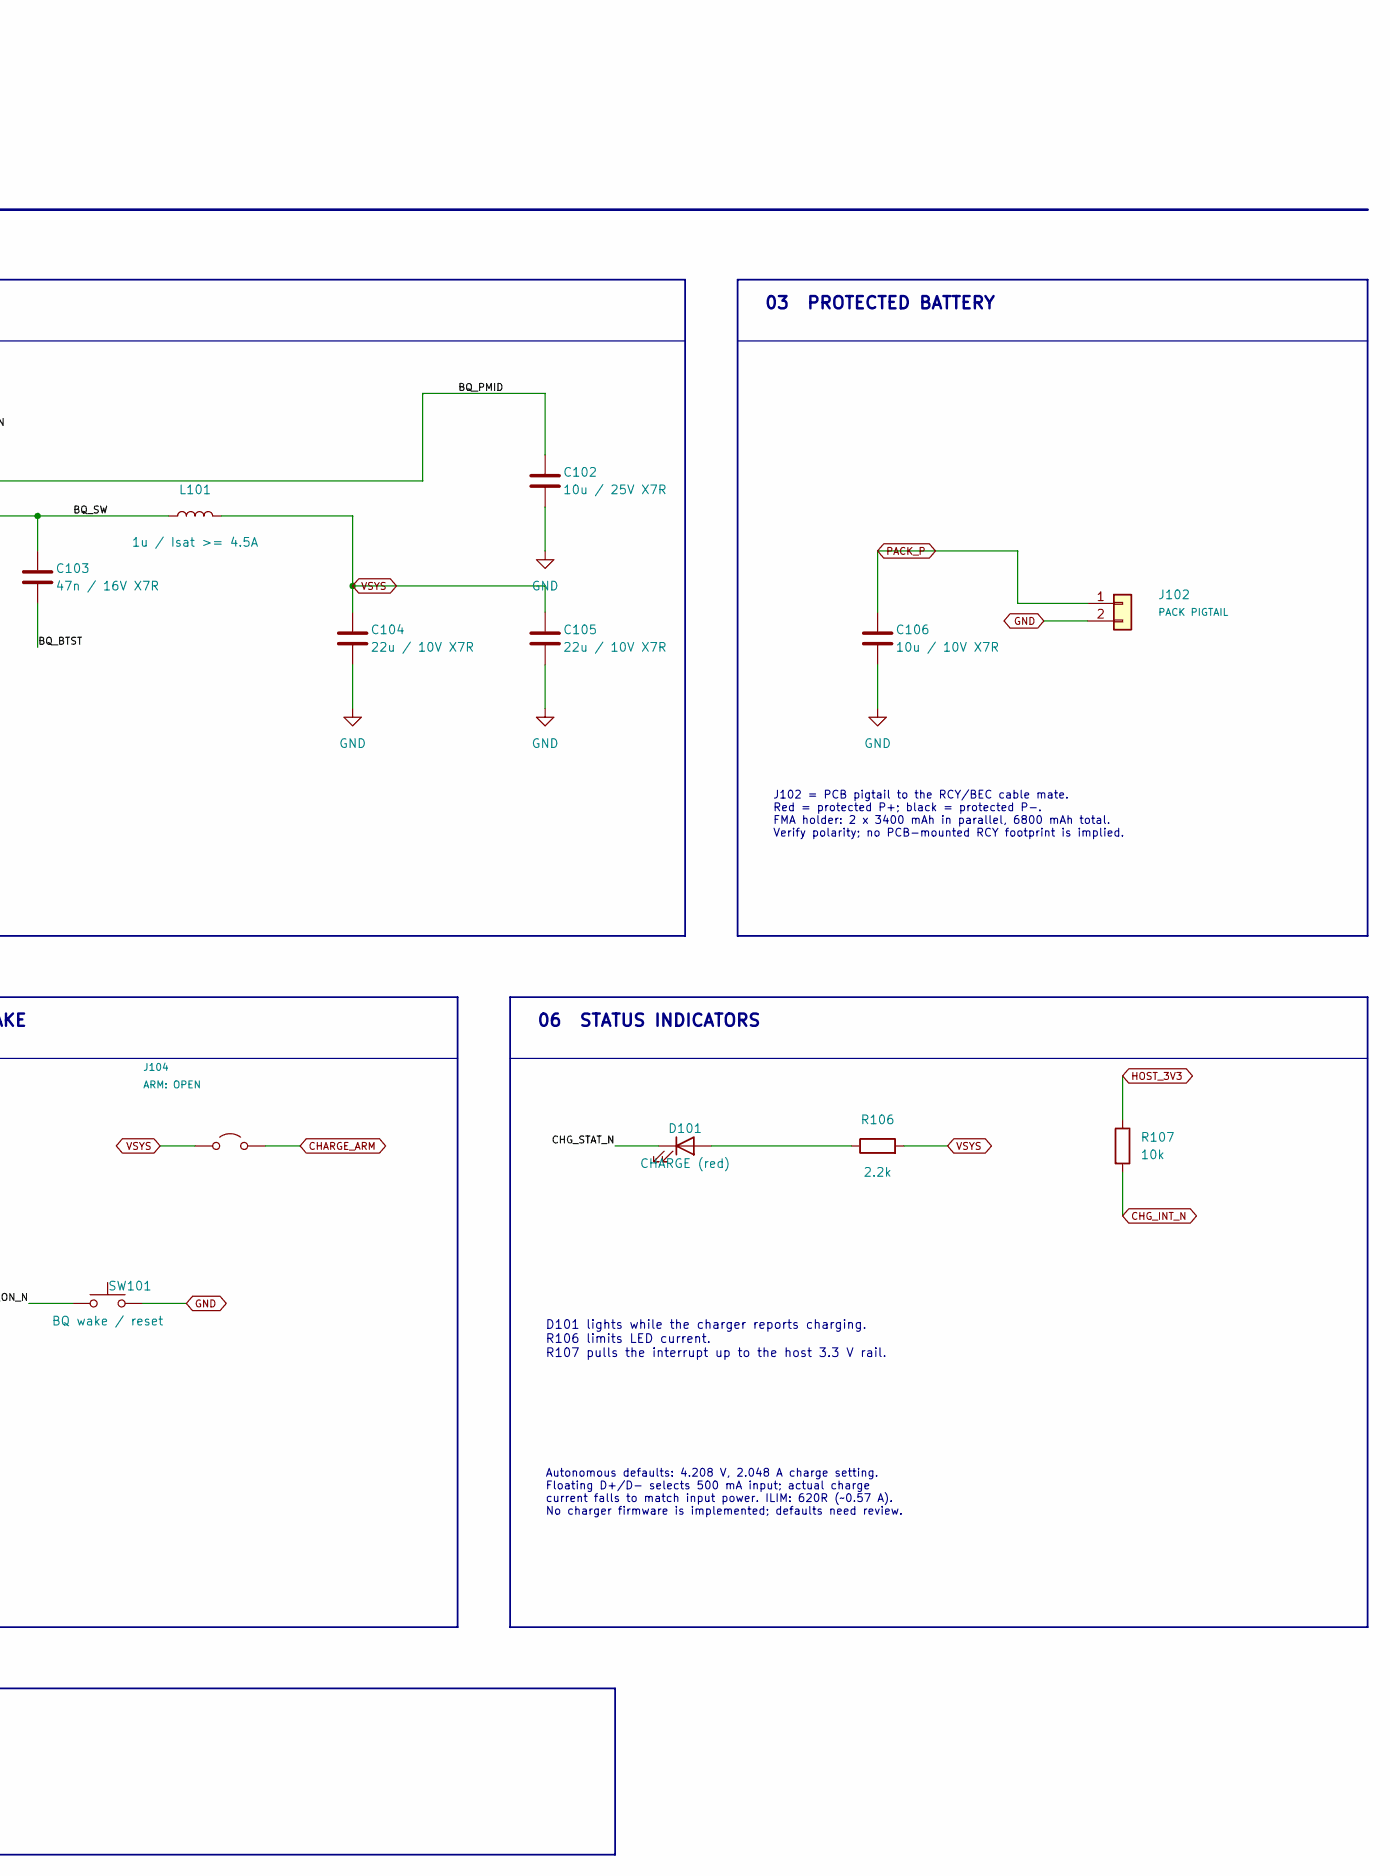
[picture p290: schematic Charging.kicad_sch, part in row 1, column 2]

Parts:
C101: 1u / 25V X7R; C_0805_2012Metric
C102: 10u / 25V X7R; C_1206_3216Metric
C103: 47n / 16V X7R; C_0805_2012Metric
C104, C105: 22u / 10V X7R; C_0805_2012Metric
C106: 10u / 10V X7R; C_0805_2012Metric
C107: 4.7u / 10V X7R; C_0805_2012Metric
D101: CHARGE (red); LED_0805_2012Metric
J101: FROM USB BOARD (2P); SolderWire-0.25sqmm_1x02_P4.2mm_D0.65mm_OD1.7mm
J102: PACK PIGTAIL; SolderWire-0.25sqmm_1x02_P4.2mm_D0.65mm_OD1.7mm
J103: PACK NTC: 103AT-2; PinHeader_1x02_P2.54mm_Vertical
J104: ARM: OPEN; PinHeader_1x02_P2.54mm_Vertical
L101: 1u / Isat >= 4.5A; L_Wuerth_HCM-7050
Q101: 2N7002; SOT-23
R101: 5.23k 1%; R_0603_1608Metric
R102: 30.1k 1%; R_0603_1608Metric
R103: 620R 1%; R_0603_1608Metric
R104, R105: 100k; R_0603_1608Metric
R106: 2.2k; R_0603_1608Metric
R107: 10k; R_0603_1608Metric
SW101: BQ wake / reset; SW_PUSH_6mm
U101: BQ25895RTWR; Texas_RTW_WQFN-24-1EP_4x4mm_P0.5mm_EP2.7x2.7mm_ThermalVias

Connections:
BQ_BTST: C103.2, U101.21 (BTST)
BQ_ILIM: R103.1, U101.10 (ILIM)
BQ_PMID: C102.1, U101.23 (PMID)
BQ_QON_N: SW101.1, U101.12 (~QON)
BQ_REGN: C107.1, R101.1, U101.22 (REGN)
BQ_SW: C103.1, L101.1, U101.19 (SW), U101.20 (SW)
CHARGE_ARM: J104.2 (B), Q101.1 (G), R105.1
CHG_CE_N: Q101.3 (D), R104.2, U101.9 (~CE)
CHG_INT_N: R107.2, U101.7 (~INT)
CHG_STAT_N: D101.1 (K), U101.4 (STAT)
GND: C101.2, C102.2, C104.2, C105.2, C106.2, C107.2, J101.2, J102.2, J103.2, Q101.2 (S), R102.2, R103.2, R105.2, SW101.2, U101.8 (OTG), U101.17 (PGND), U101.18 (PGND), U101.25 (PGND)
HOST_3V3: R107.1
I2C_SCL: U101.5 (SCL)
I2C_SDA: U101.6 (SDA)
unnamed: D101.2 (A), R106.1
PACK_P: C106.1, J102.1, U101.13 (BAT), U101.14 (BAT)
PACK_TS: J103.1, R101.2, R102.1, U101.11 (TS)
USB_5V: C101.1, J101.1, U101.1 (VBUS)
VSYS: C104.1, C105.1, J104.1 (A), L101.2, R104.1, R106.2, U101.15 (SYS), U101.16 (SYS)

Notes on the sheet:
05 COMMISSIONING ARM & SERVICE WAKE
D101 lights while the charger reports charging. R106 limits LED current. R107 pulls the interrupt up to the host 3.3 V rail.
Follow the top row from USB input to charger and battery. The lower row controls and monitors charging.
02 CHARGER & POWER PATH
Charging & protected battery
01 USB INPUT
03 PROTECTED BATTERY
TRIMIX / ANALYZER ELECTRONICS / SHEET 2
Matching labels connect electrically. VSYS also supplies the always-on pushbutton controller. BQ25895 I2C address = 0x6A. If firmware writes settings, disable its watchdog before host shutdown. Default settings return after complete charger power loss. Keep J104 OPEN until those settings are qualif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
R101/R102 and the external 10k NTC sense temperature. Attach the NTC to the cells; connect it at J103. An open sensor inhibits charging.
J104 OPEN = charging disabled; R105 holds Q101 off. Fit the shunt only after cell/USB/NTC validation. Armed = autonomous charging with the host ON or OFF. SW101 is service wake/reset, not the front power button.
04 PACK TEMPERATURE
J101 receives 5 V from the GCT USB daughterboard. J902 -> two-wire harness -> J101 (same pin numbers). See USB_Input, sheet 10; qualify before charging.
Autonomous defaults: 4.208 V, 2.048 A charge setting. Floating D+/D- selects 500 mA input; actual charge current falls to match input power. ILIM: 620R (~0.57 A). No charger firmware is implemented; defaults need review.
06 STATUS INDICATORS
J102 = PCB pigtail to the RCY/BEC cable mate. Red = protected P+; black = protected P-. FMA holder: 2 x 3400 mAh in parallel, 6800 mAh total. Verify polarity; no PCB-mounted RCY footprint is implied.
READING THIS SHEET
