magnus188/trimix-analysator/hardware/system-review/electrical/before-input-limiter/Charging.kicad_sch

## KiCad design hardware/system-review/electrical/before-input-limiter/Charging.kicad_sch (2026-09-09)

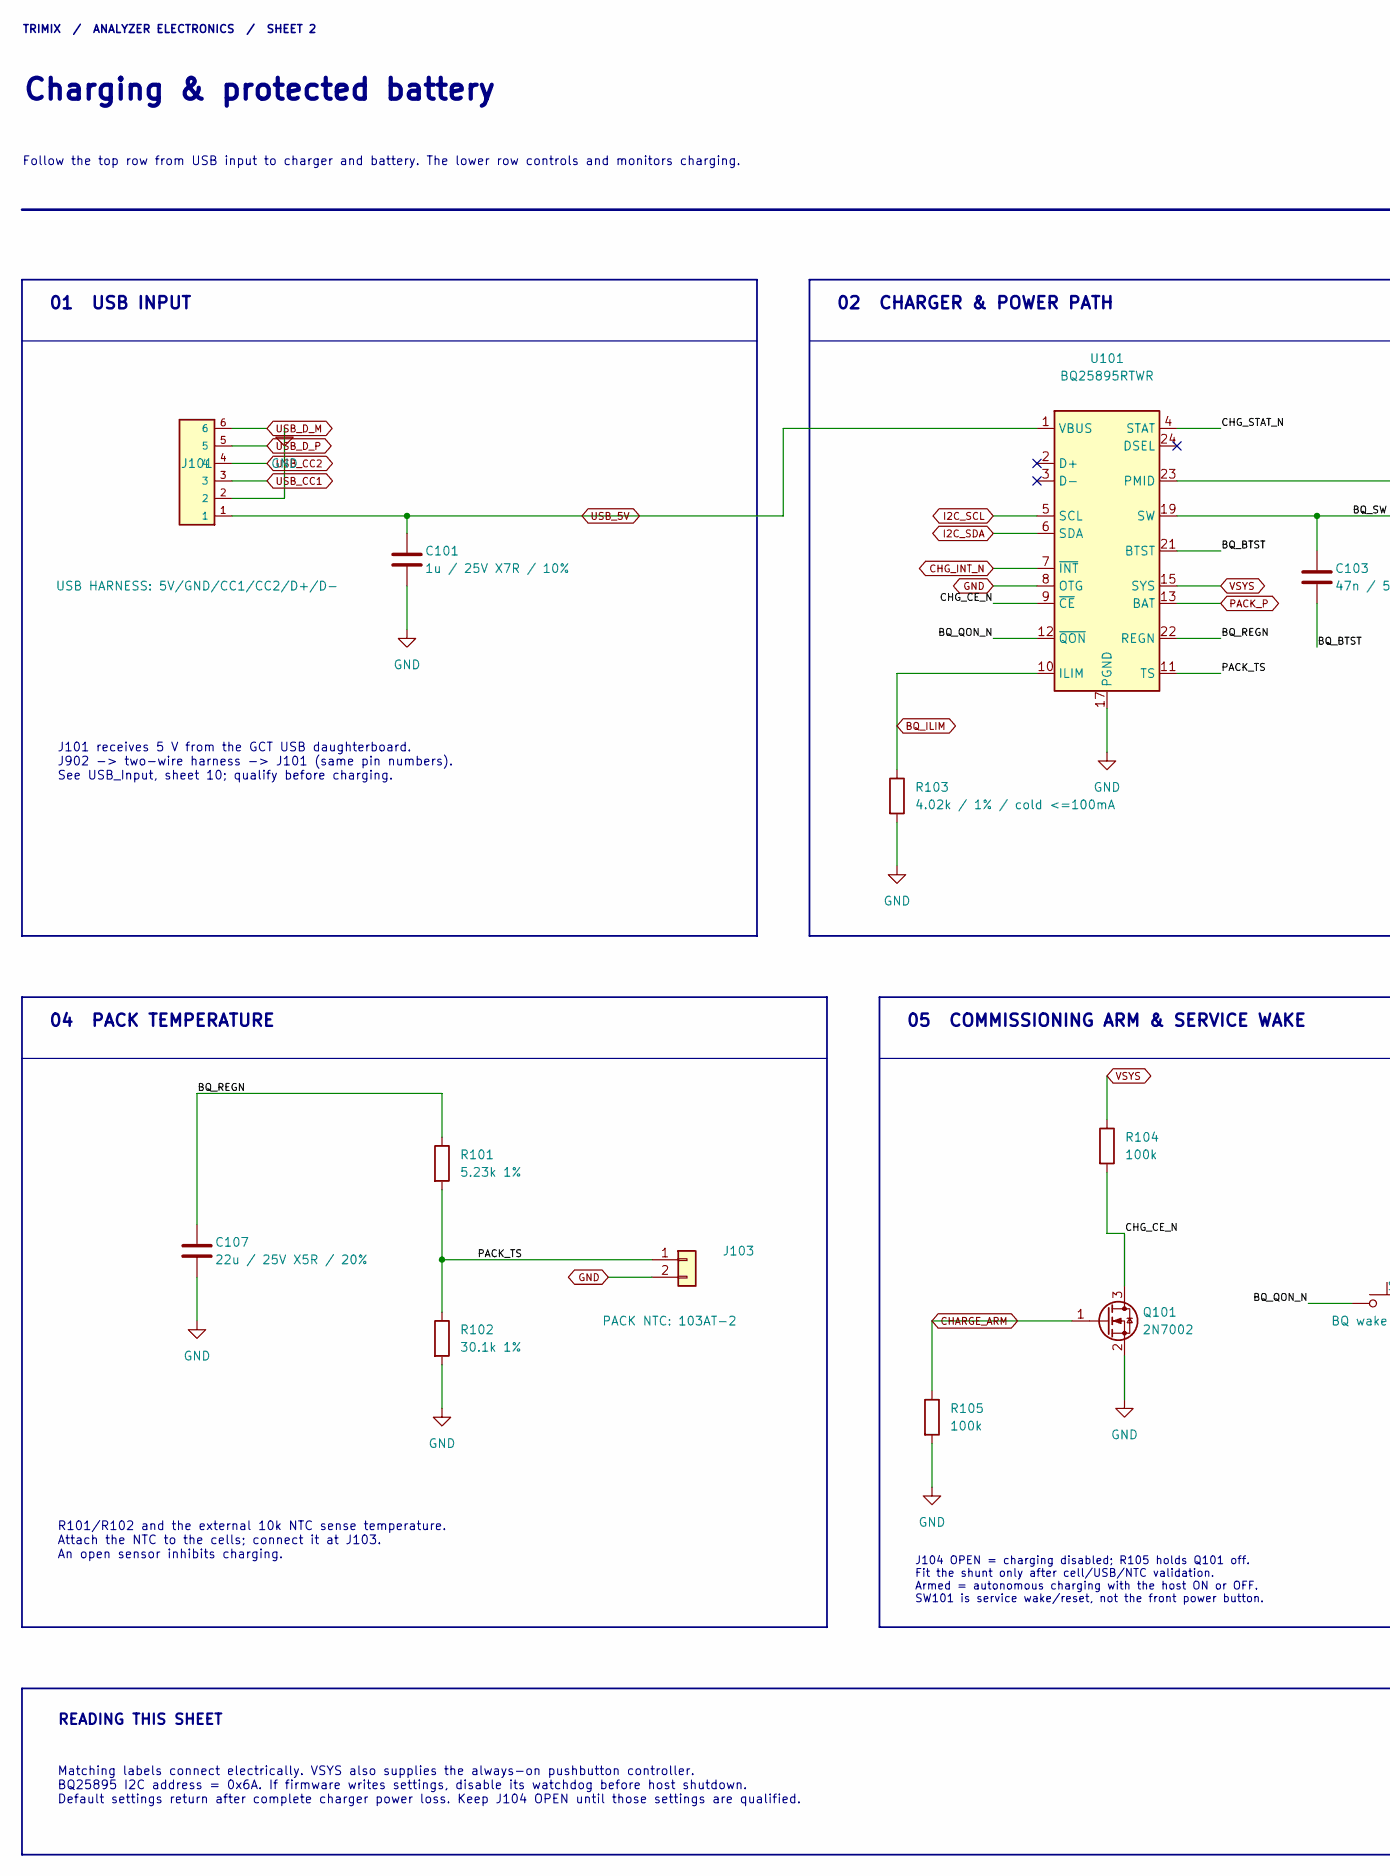
[picture p291: schematic Charging.kicad_sch, part in row 1, column 1]

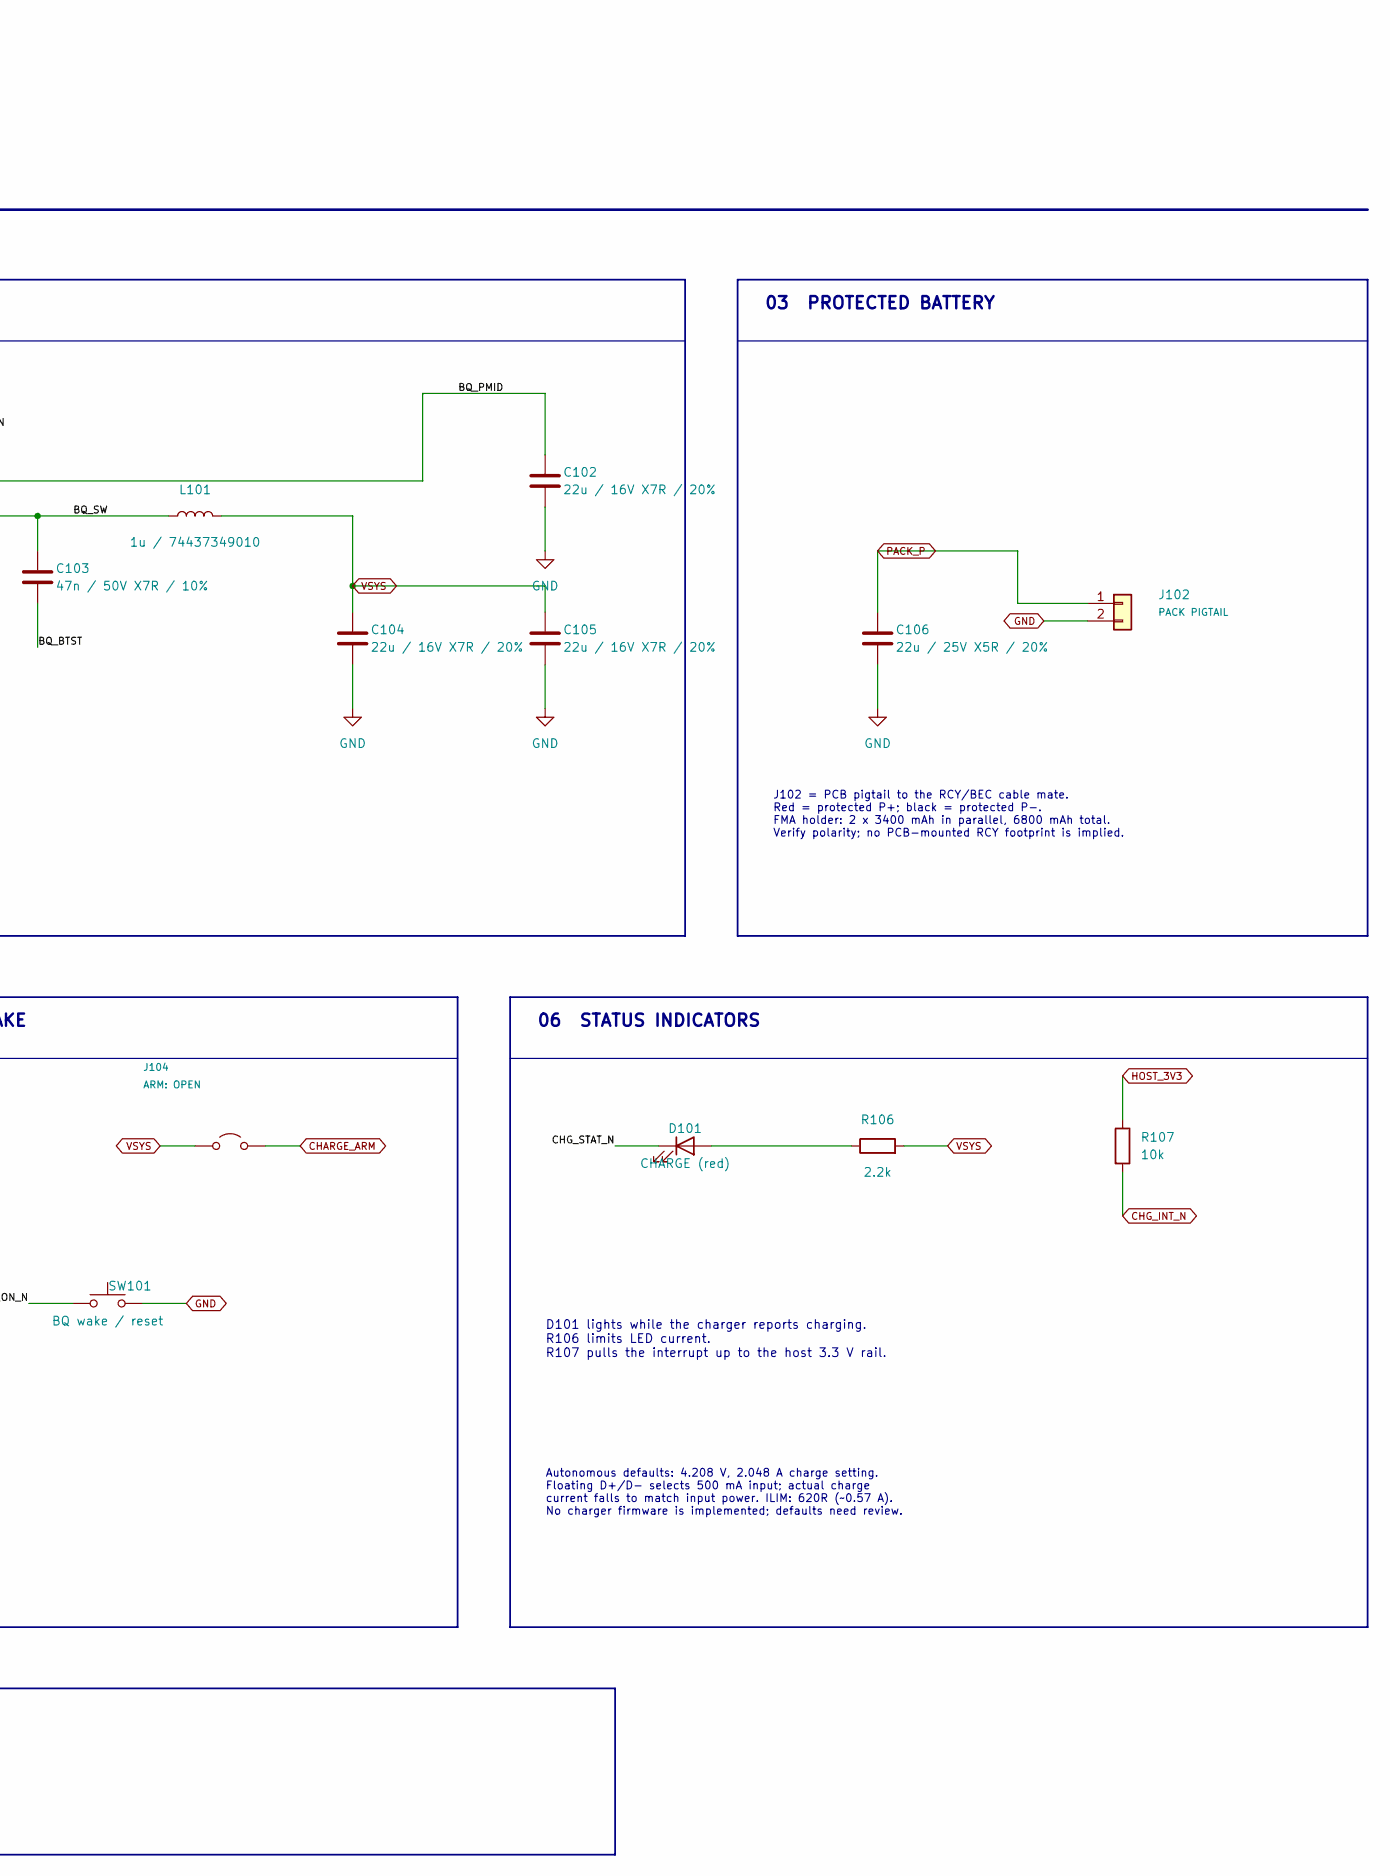
[picture p292: schematic Charging.kicad_sch, part in row 1, column 2]

Parts:
C101: 1u / 25V X7R / 10%; C_0805_2012Metric; MPN C2012X7R1E105K125AB
C102, C104, C105: 22u / 16V X7R / 20%; C_1210_3225Metric; MPN C3225X7R1C226M250AC
C103: 47n / 50V X7R / 10%; C_0805_2012Metric; MPN C0805C473K5RACTU
C106, C107: 22u / 25V X5R / 20%; C_1206_3216Metric; MPN C3216X5R1E226M160AB
D101: CHARGE (red); LED_0805_2012Metric; MPN APT2012EC
J101: USB HARNESS: 5V/GND/CC1/CC2/D+/D-; USB_Harness_6P_P1.8mm
J102: PACK PIGTAIL; SolderWire-0.25sqmm_1x02_P4.2mm_D0.65mm_OD1.7mm
J103: PACK NTC: 103AT-2; PinHeader_1x02_P2.54mm_Vertical; MPN M20-9990246
J104: ARM: OPEN; PinHeader_1x02_P2.54mm_Vertical; MPN M20-9990246
L101: 1u / 74437349010; L_Wurth_74437349010_7050; MPN 74437349010
Q101: 2N7002; SOT-23; MPN 2N7002-7-F
R101: 5.23k 1%; R_0603_1608Metric; MPN RC0603FR-075K23L
R102: 30.1k 1%; R_0603_1608Metric; MPN RC0603FR-0730K1L
R103: 4.02k / 1% / cold <=100mA; R_0603_1608Metric; MPN RC0603FR-074K02L
R104, R105: 100k; R_0603_1608Metric; MPN RC0603FR-07100KL
R106: 2.2k; R_0603_1608Metric; MPN RC0603FR-072K2L
R107: 10k; R_0603_1608Metric; MPN RC0603FR-0710KL
SW101: BQ wake / reset; SW_PUSH_6mm; MPN B3F-1000
U101: BQ25895RTWR; Texas_RTW_WQFN-24-1EP_4x4mm_P0.5mm_EP2.7x2.7mm_ThermalVias

Connections:
BQ_BTST: C103.2, U101.21 (BTST)
BQ_ILIM: R103.1, U101.10 (ILIM)
BQ_PMID: C102.1, U101.23 (PMID)
BQ_QON_N: SW101.1, U101.12 (~QON)
BQ_REGN: C107.1, R101.1, U101.22 (REGN)
BQ_SW: C103.1, L101.1, U101.19 (SW), U101.20 (SW)
CHARGE_ARM: J104.2 (B), Q101.1 (G), R105.1
CHG_CE_N: Q101.3 (D), R104.2, U101.9 (~CE)
CHG_INT_N: R107.2, U101.7 (~INT)
CHG_STAT_N: D101.1 (K), U101.4 (STAT)
GND: C101.2, C102.2, C104.2, C105.2, C106.2, C107.2, J101.2, J102.2, J103.2, Q101.2 (S), R102.2, R103.2, R105.2, SW101.2, U101.8 (OTG), U101.17 (PGND), U101.18 (PGND), U101.25 (PGND)
HOST_3V3: R107.1
I2C_SCL: U101.5 (SCL)
I2C_SDA: U101.6 (SDA)
unnamed: D101.2 (A), R106.1
PACK_P: C106.1, J102.1, U101.13 (BAT), U101.14 (BAT)
PACK_TS: J103.1, R101.2, R102.1, U101.11 (TS)
USB_5V: C101.1, J101.1, U101.1 (VBUS)
USB_CC1: J101.3
USB_CC2: J101.4
USB_D_M: J101.6
USB_D_P: J101.5
VSYS: C104.1, C105.1, J104.1 (A), L101.2, R104.1, R106.2, U101.15 (SYS), U101.16 (SYS)

Notes on the sheet:
05 COMMISSIONING ARM & SERVICE WAKE
D101 lights while the charger reports charging. R106 limits LED current. R107 pulls the interrupt up to the host 3.3 V rail.
Follow the top row from USB input to charger and battery. The lower row controls and monitors charging.
02 CHARGER & POWER PATH
Charging & protected battery
01 USB INPUT
03 PROTECTED BATTERY
TRIMIX / ANALYZER ELECTRONICS / SHEET 2
Matching labels connect electrically. VSYS also supplies the always-on pushbutton controller. BQ25895 I2C address = 0x6A. If firmware writes settings, disable its watchdog before host shutdown. Default settings return after complete charger power loss. Keep J104 OPEN until those settings are qualif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
R101/R102 and the external 10k NTC sense temperature. Attach the NTC to the cells; connect it at J103. An open sensor inhibits charging.
J104 OPEN = charging disabled; R105 holds Q101 off. Fit the shunt only after cell/USB/NTC validation. Armed = autonomous charging with the host ON or OFF. SW101 is service wake/reset, not the front power button.
04 PACK TEMPERATURE
J101 receives 5 V from the GCT USB daughterboard. J902 -> two-wire harness -> J101 (same pin numbers). See USB_Input, sheet 10; qualify before charging.
Autonomous defaults: 4.208 V, 2.048 A charge setting. Floating D+/D- selects 500 mA input; actual charge current falls to match input power. ILIM: 620R (~0.57 A). No charger firmware is implemented; defaults need review.
06 STATUS INDICATORS
J102 = PCB pigtail to the RCY/BEC cable mate. Red = protected P+; black = protected P-. FMA holder: 2 x 3400 mAh in parallel, 6800 mAh total. Verify polarity; no PCB-mounted RCY footprint is implied.
READING THIS SHEET
