magnus188/trimix-analysator/hardware/system-review/electrical/before-input-limiter/USB_Source_Control.kicad_sch

## KiCad design hardware/system-review/electrical/before-input-limiter/USB_Source_Control.kicad_sch (2026-09-09)

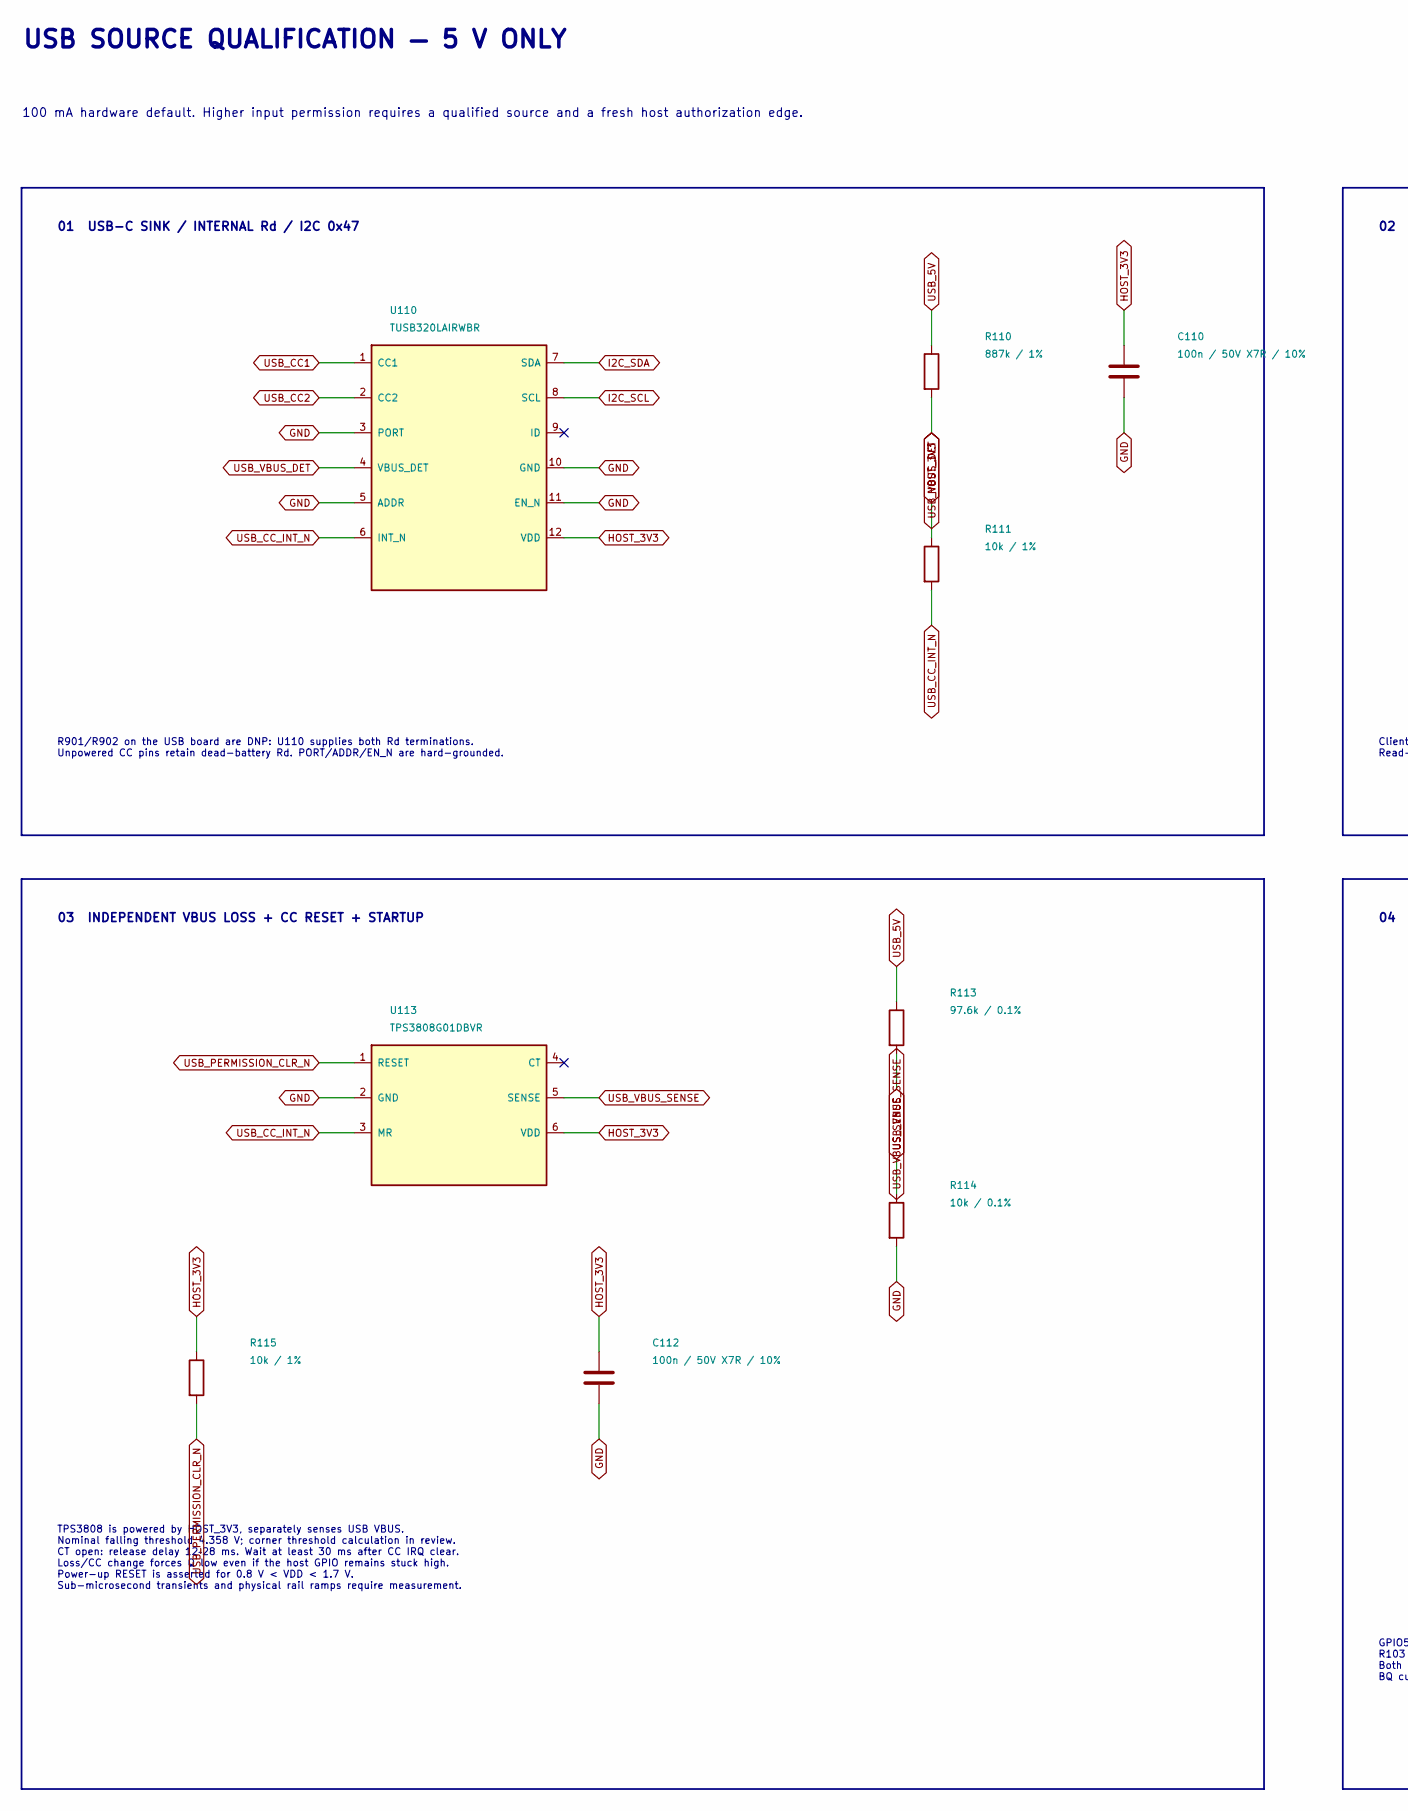
[picture p293: schematic USB_Source_Control.kicad_sch, part in row 1, column 1]

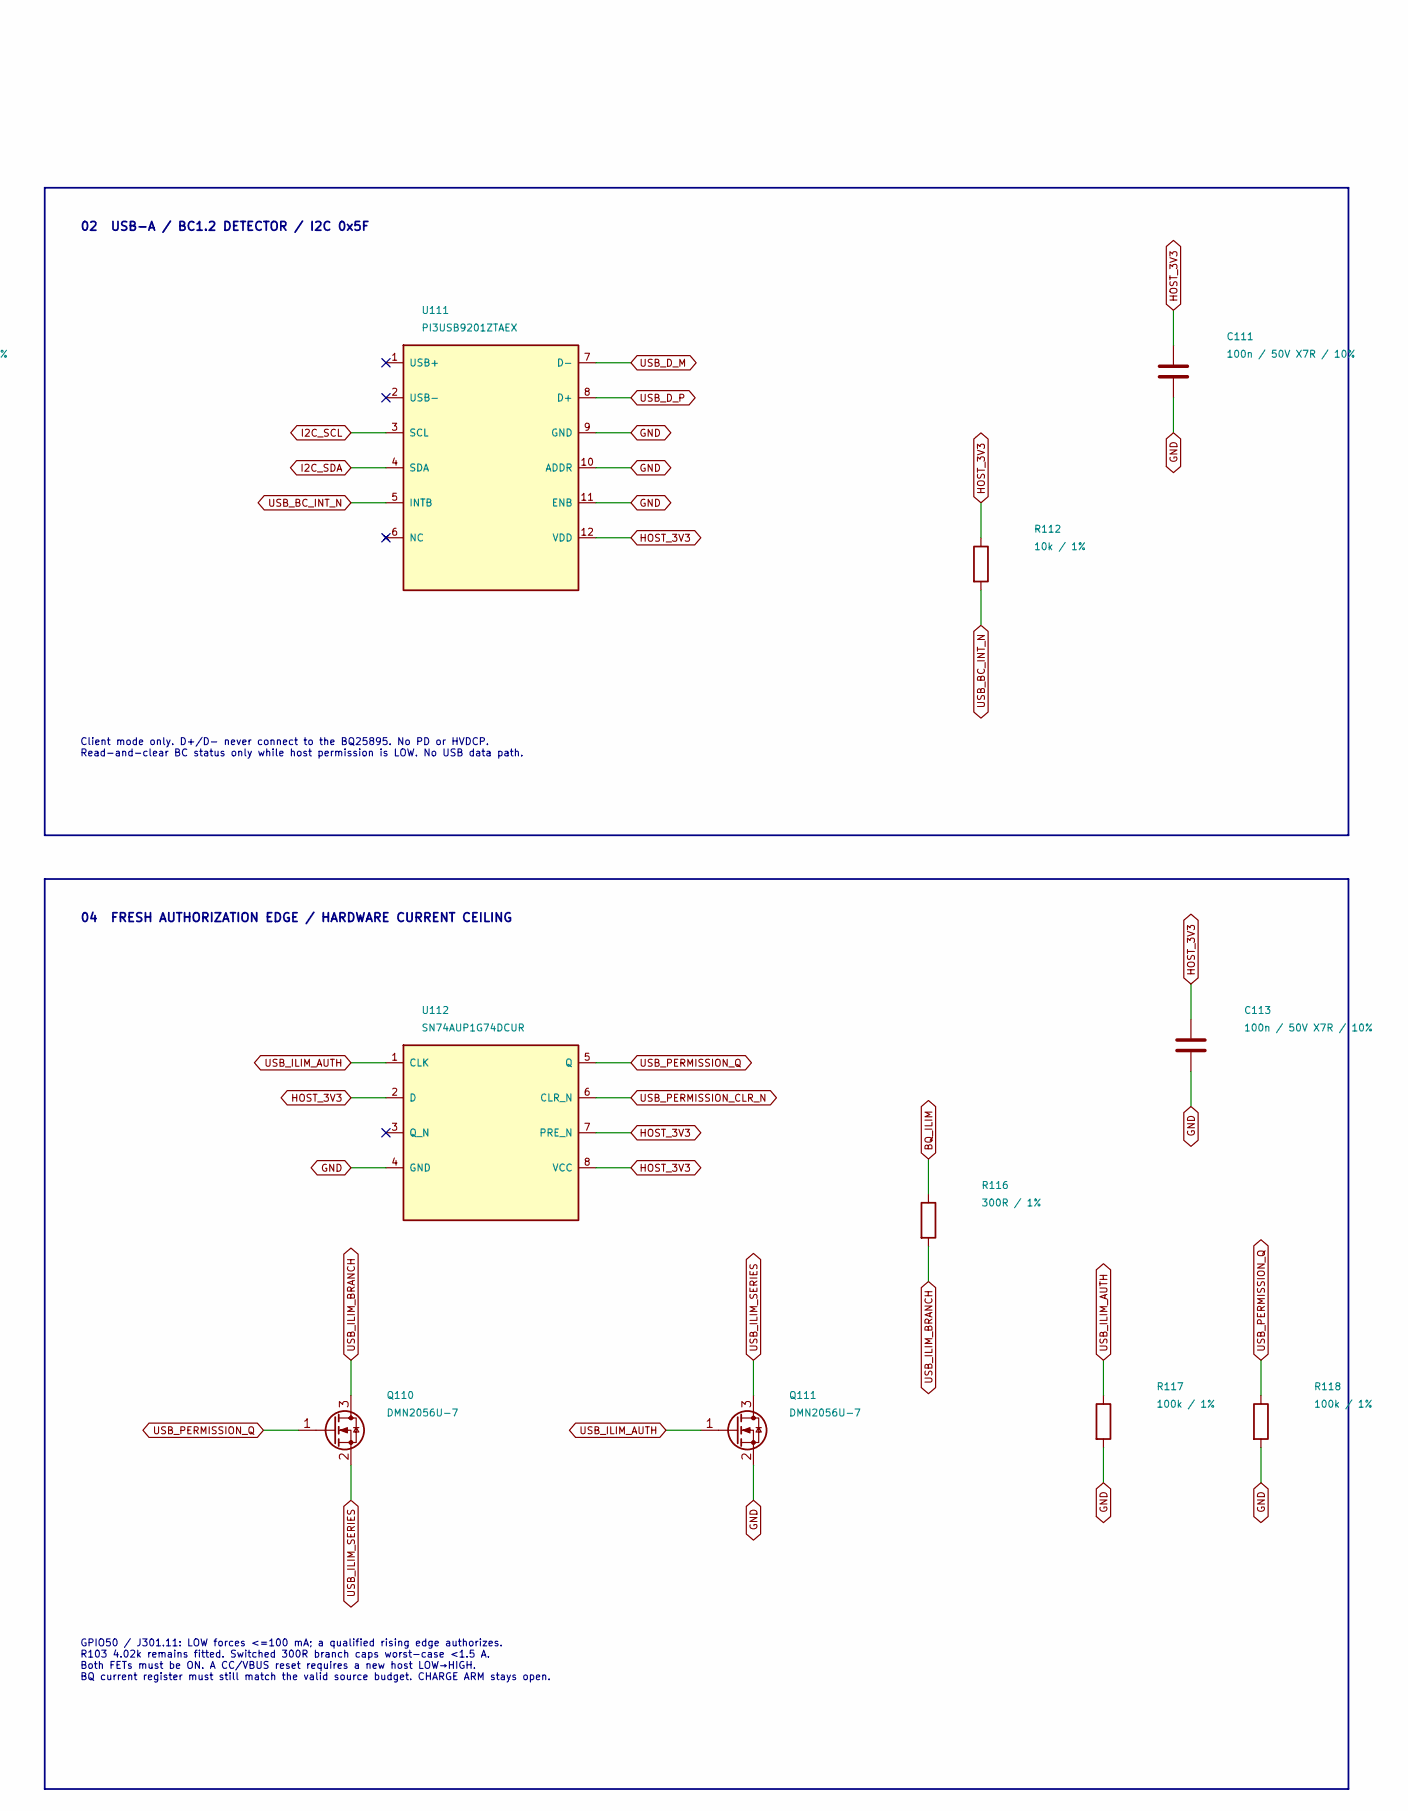
[picture p294: schematic USB_Source_Control.kicad_sch, part in row 1, column 2]

Parts:
C110, C111, C112, C113: 100n / 50V X7R / 10%; C_0603_1608Metric; MPN C1608X7R1H104K080AA
Q110, Q111: DMN2056U-7; SOT-23; MPN DMN2056U-7
R110: 887k / 1%; R_0603_1608Metric; MPN RC0603FR-07887KL
R111, R112, R115: 10k / 1%; R_0603_1608Metric; MPN RC0603FR-0710KL
R113: 97.6k / 0.1%; R_0603_1608Metric; MPN RT0603BRD0797K6L
R114: 10k / 0.1%; R_0603_1608Metric; MPN RT0603BRD0710KL
R116: 300R / 1%; R_0603_1608Metric; MPN RC0603FR-07300RL
R117, R118: 100k / 1%; R_0603_1608Metric; MPN RC0603FR-07100KL
U110: TUSB320LAIRWBR; Texas_X2QFN-12_1.6x1.6mm_P0.4mm; MPN TUSB320LAIRWBR
U111: PI3USB9201ZTAEX; PI3USB9201_UQFN2020_12_TypeC; MPN PI3USB9201ZTAEX
U112: SN74AUP1G74DCUR; VSSOP-8_2.3x2mm_P0.5mm; MPN SN74AUP1G74DCUR
U113: TPS3808G01DBVR; SOT-23-6; MPN TPS3808G01DBVR

Connections:
BQ_ILIM: R116.1
GND: C110.2, C111.2, C112.2, C113.2, Q111.2 (S), R114.2, R117.2, R118.2, U110.3 (PORT), U110.5 (ADDR), U110.10 (GND), U110.11 (EN_N), U111.9 (GND), U111.10 (ADDR), U111.11 (ENB), U112.4 (GND), U113.2 (GND)
HOST_3V3: C110.1, C111.1, C112.1, C113.1, R111.1, R112.1, R115.1, U110.12 (VDD), U111.12 (VDD), U112.2 (D), U112.7 (PRE_N), U112.8 (VCC), U113.6 (VDD)
I2C_SCL: U110.8 (SCL), U111.3 (SCL)
I2C_SDA: U110.7 (SDA), U111.4 (SDA)
USB_5V: R110.1, R113.1
USB_BC_INT_N: R112.2, U111.5 (INTB)
USB_CC1: U110.1 (CC1)
USB_CC2: U110.2 (CC2)
USB_CC_INT_N: R111.2, U110.6 (INT_N), U113.3 (MR)
USB_D_M: U111.7 (D-)
USB_D_P: U111.8 (D+)
USB_ILIM_AUTH: Q111.1 (G), R117.1, U112.1 (CLK)
USB_ILIM_BRANCH: Q110.3 (D), R116.2
USB_ILIM_SERIES: Q110.2 (S), Q111.3 (D)
USB_PERMISSION_CLR_N: R115.2, U112.6 (CLR_N), U113.1 (RESET)
USB_PERMISSION_Q: Q110.1 (G), R118.1, U112.5 (Q)
USB_VBUS_DET: R110.2, U110.4 (VBUS_DET)
USB_VBUS_SENSE: R113.2, R114.1, U113.5 (SENSE)

Notes on the sheet:
USB SOURCE QUALIFICATION — 5 V ONLY
100 mA hardware default. Higher input permission requires a qualified source and a fresh host authorization edge.
01 USB-C SINK / INTERNAL Rd / I2C 0x47
R901/R902 on the USB board are DNP: U110 supplies both Rd terminations. Unpowered CC pins retain dead-battery Rd. PORT/ADDR/EN_N are hard-grounded.
02 USB-A / BC1.2 DETECTOR / I2C 0x5F
Client mode only. D+/D- never connect to the BQ25895. No PD or HVDCP. Read-and-clear BC status only while host permission is LOW. No USB data path.
03 INDEPENDENT VBUS LOSS + CC RESET + STARTUP
TPS3808 is powered by HOST_3V3, separately senses USB VBUS. Nominal falling threshold 4.358 V; corner threshold calculation in review. CT open: release delay 12–28 ms. Wait at least 30 ms after CC IRQ clear. Loss/CC change forces Q low even if the host GPIO remains stuck high. Power-up RESET is ass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
04 FRESH AUTHORIZATION EDGE / HARDWARE CURRENT CEILING
GPIO50 / J301.11: LOW forces <=100 mA; a qualified rising edge authorizes. R103 4.02k remains fitted. Switched 300R branch caps worst-case <1.5 A. Both FETs must be ON. A CC/VBUS reset requires a new host LOW→HIGH. BQ current register must still match the valid source budget. CHARGE ARM stays open.
