magnus188/trimix-analysator/hardware/system-review/electrical/before-ldo-upgrade/Helium.kicad_sch

## KiCad design hardware/system-review/electrical/before-ldo-upgrade/Helium.kicad_sch (2026-09-09)

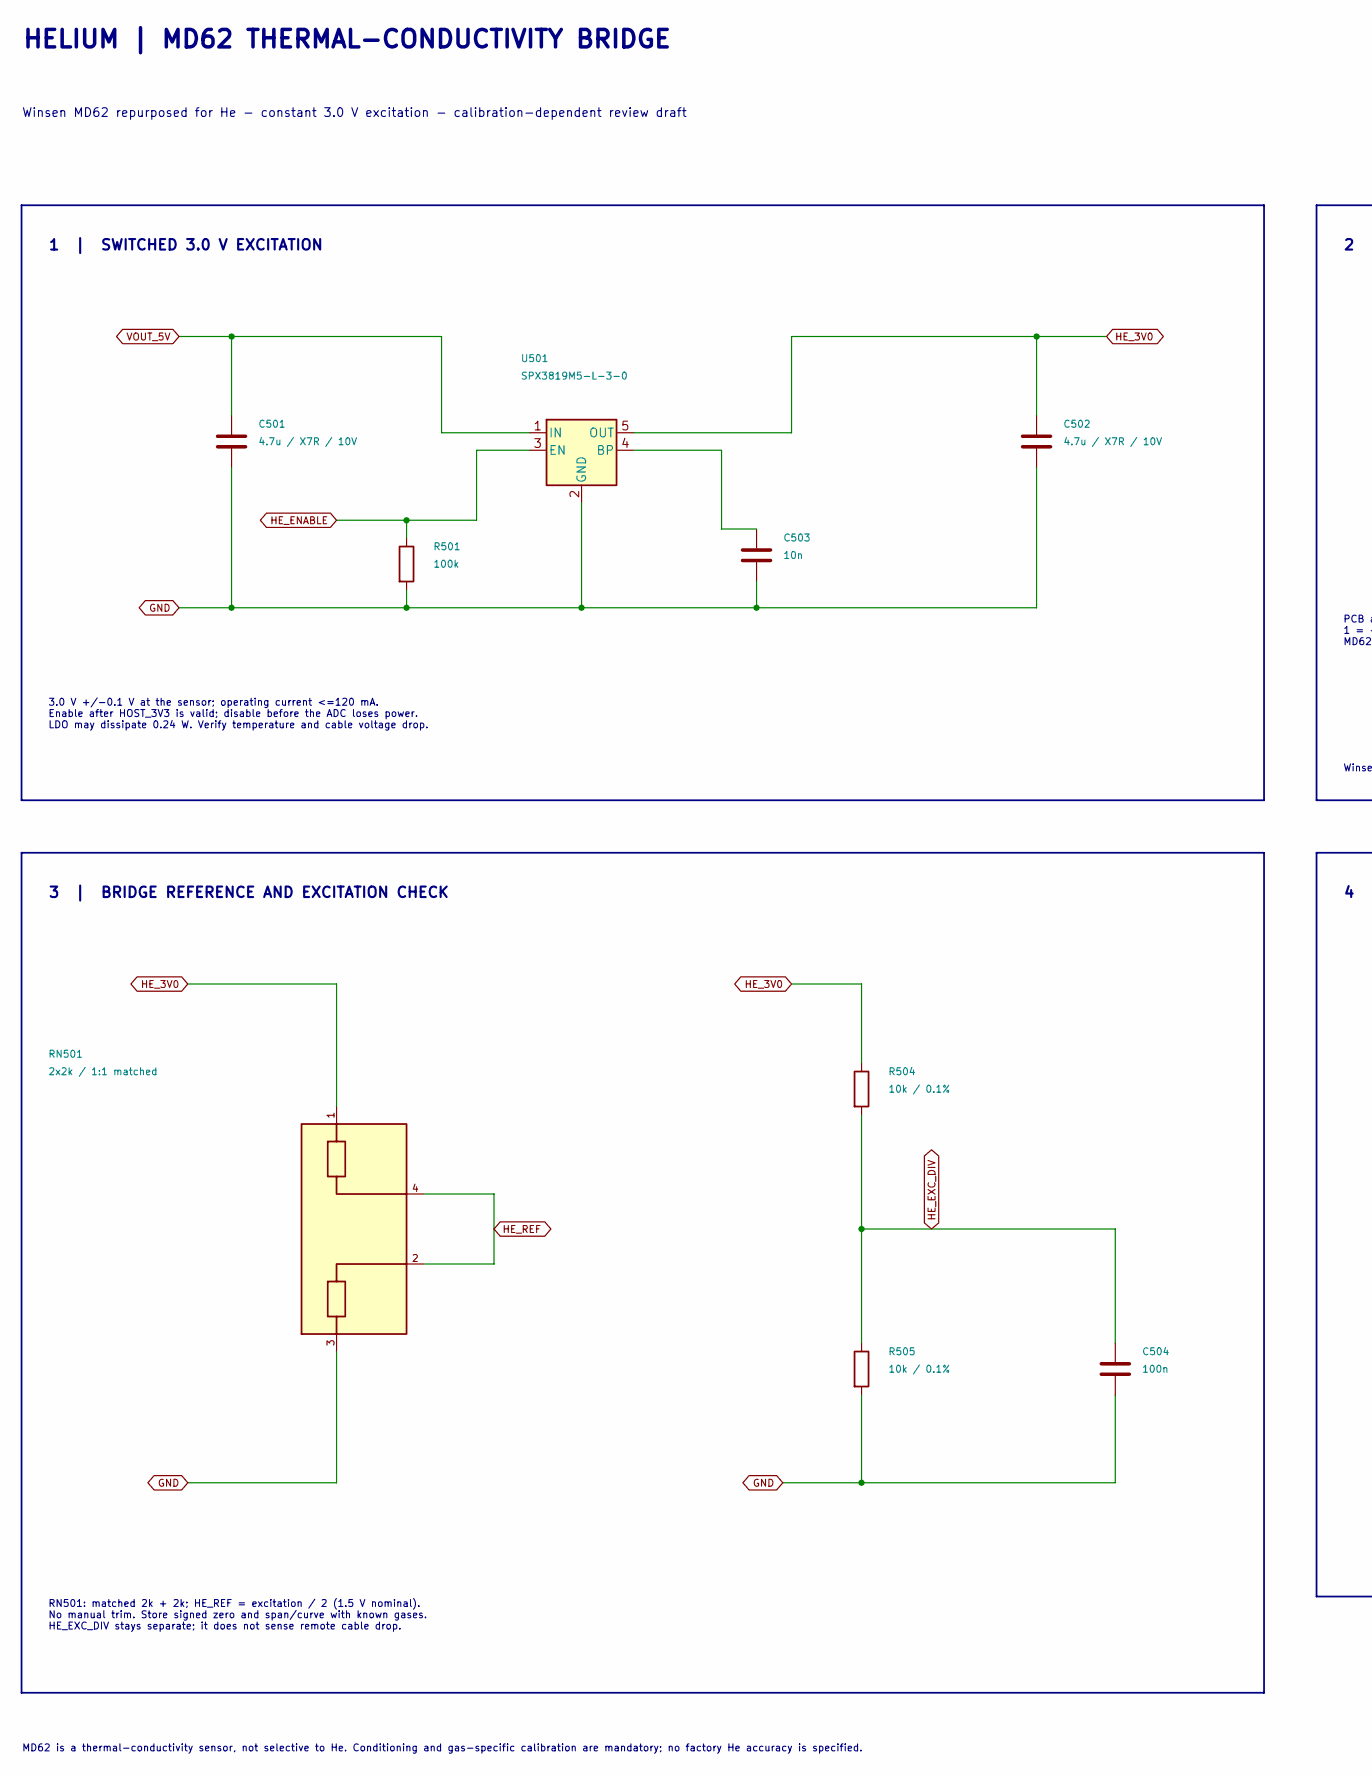
[picture p295: schematic Helium.kicad_sch, part in row 1, column 1]

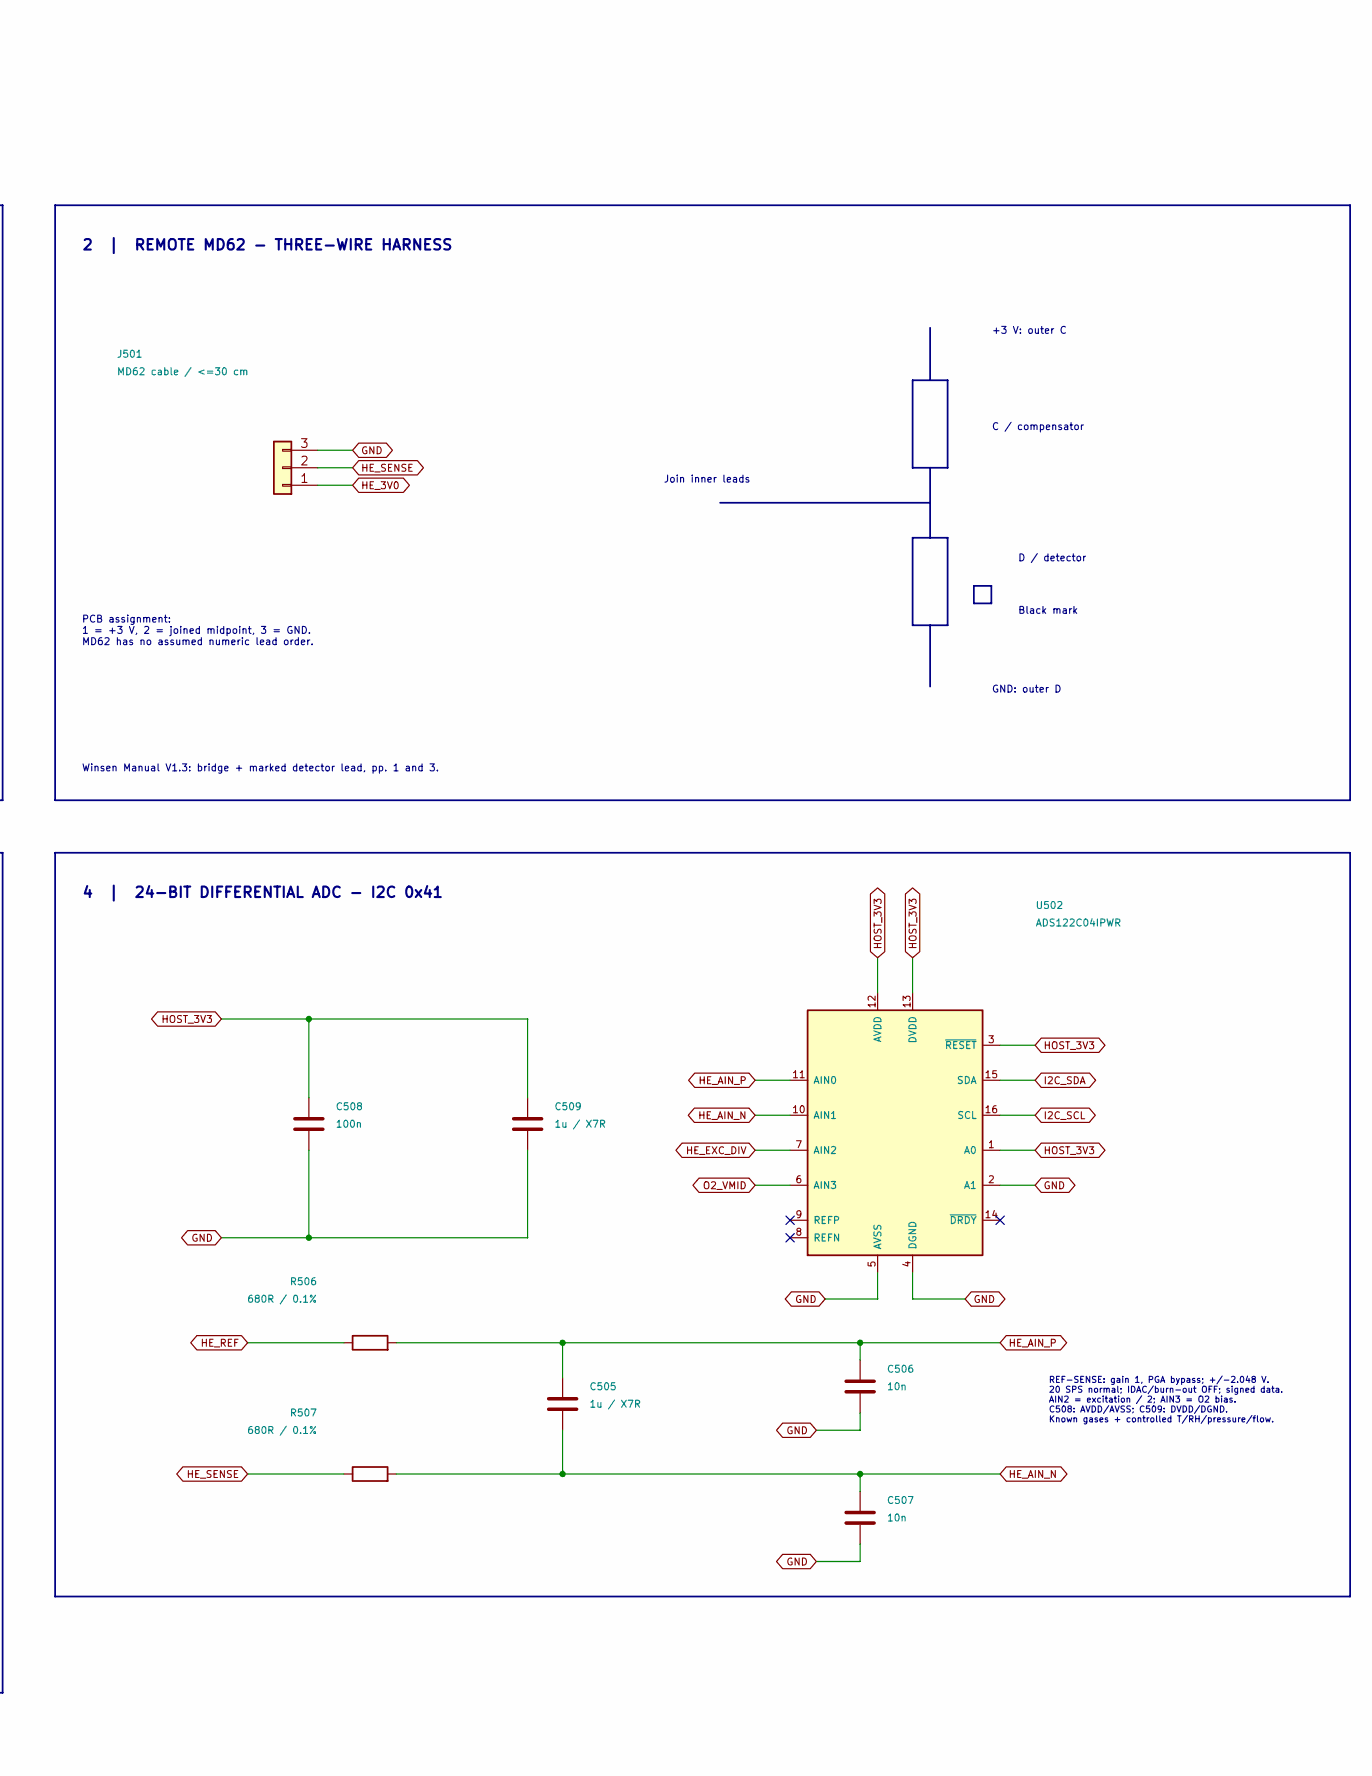
[picture p296: schematic Helium.kicad_sch, part in row 1, column 2]

Parts:
C501, C502: 4.7u / X7R / 10V; C_0603_1608Metric
C503, C506, C507: 10n; C_0603_1608Metric
C504, C508: 100n; C_0603_1608Metric
C505, C509: 1u / X7R; C_0603_1608Metric
J501: MD62 cable / <=30 cm; PinHeader_1x03_P2.54mm_Vertical
R501: 100k; R_0603_1608Metric
R504, R505: 10k / 0.1%; R_0603_1608Metric
R506, R507: 680R / 0.1%; R_0603_1608Metric
RN501: 2x2k / 1:1 matched; Vishay_ACAS0606_AT_IEC; MPN ACASN2001U2001P1AT
U501: SPX3819M5-L-3-0; SOT-23-5
U502: ADS122C04IPWR; TSSOP-16_4.4x5mm_P0.65mm; MPN ADS122C04IPWR

Connections:
GND: C501.2, C502.2, C503.2, C504.2, C506.2, C507.2, C508.2, C509.2, J501.3, R501.2, R505.2, RN501.3 (R2.2), U501.2 (GND), U502.2 (A1), U502.4 (DGND), U502.5 (AVSS)
HE_3V0: C502.1, J501.1, R504.1, RN501.1 (R1.1), U501.5 (OUT)
HE_AIN_N: C505.2, C507.1, R507.2, U502.10 (AIN1)
HE_AIN_P: C505.1, C506.1, R506.2, U502.11 (AIN0)
HE_ENABLE: R501.1, U501.3 (EN)
HE_EXC_DIV: C504.1, R504.2, R505.1, U502.7 (AIN2)
HE_REF: R506.1, RN501.2 (R2.1), RN501.4 (R1.2)
HE_SENSE: J501.2, R507.1
HOST_3V3: C508.1, C509.1, U502.1 (A0), U502.3 (~RESET), U502.12 (AVDD), U502.13 (DVDD)
I2C_SCL: U502.16 (SCL)
I2C_SDA: U502.15 (SDA)
unnamed: C503.1, U501.4 (BP)
O2_VMID: U502.6 (AIN3)
VOUT_5V: C501.1, U501.1 (IN)

Notes on the sheet:
3.0 V +/-0.1 V at the sensor; operating current <=120 mA. Enable after HOST_3V3 is valid; disable before the ADC loses power. LDO may dissipate 0.24 W. Verify temperature and cable voltage drop.
D / detector
Black mark
REF-SENSE: gain 1, PGA bypass; +/-2.048 V. 20 SPS normal; IDAC/burn-out OFF; signed data. AIN2 = excitation / 2; AIN3 = O2 bias. C508: AVDD/AVSS; C509: DVDD/DGND. Known gases + controlled T/RH/pressure/flow.
RN501: matched 2k + 2k; HE_REF = excitation / 2 (1.5 V nominal). No manual trim. Store signed zero and span/curve with known gases. HE_EXC_DIV stays separate; it does not sense remote cable drop.
Winsen MD62 repurposed for He - constant 3.0 V excitation - calibration-dependent review draft
Join inner leads
C / compensator
2 | REMOTE MD62 - THREE-WIRE HARNESS
4 | 24-BIT DIFFERENTIAL ADC - I2C 0x41
MD62 is a thermal-conductivity sensor, not selective to He. Conditioning and gas-specific calibration are mandatory; no factory He accuracy is specified.
+3 V: outer C
PCB assignment: 1 = +3 V, 2 = joined midpoint, 3 = GND. MD62 has no assumed numeric lead order.
HELIUM | MD62 THERMAL-CONDUCTIVITY BRIDGE
GND: outer D
1 | SWITCHED 3.0 V EXCITATION
Winsen Manual V1.3: bridge + marked detector lead, pp. 1 and 3.
3 | BRIDGE REFERENCE AND EXCITATION CHECK
