magnus188/trimix-analysator/hardware/system-review/electrical/before-ovp/USB_Input_Limiter.kicad_sch

## KiCad design hardware/system-review/electrical/before-ovp/USB_Input_Limiter.kicad_sch (2026-09-09)

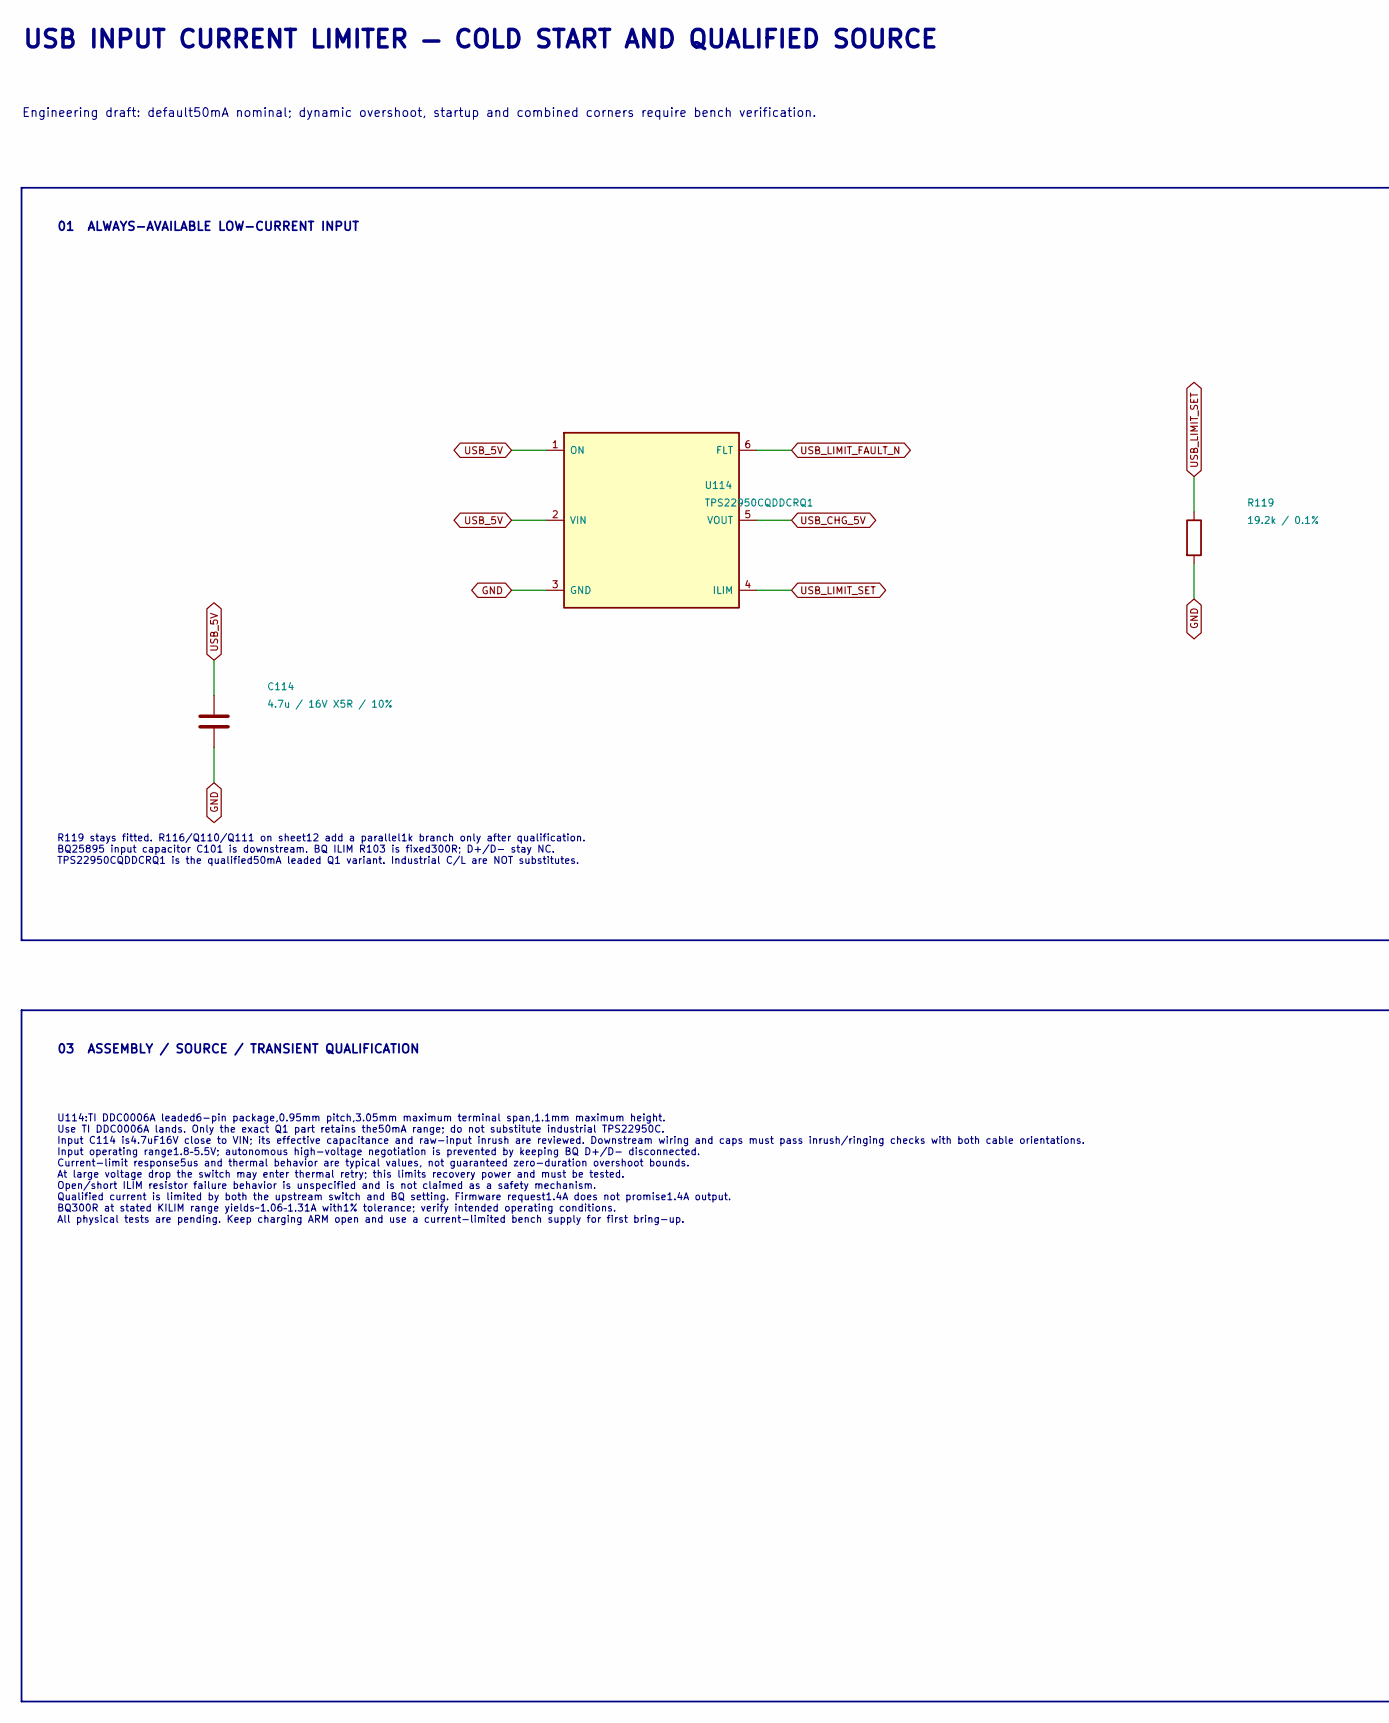
[picture p298: schematic USB_Input_Limiter.kicad_sch, part in row 1, column 1]


Parts:
C114: 4.7u / 16V X5R / 10%; C_0603_1608Metric; MPN C1608X5R1C475K080AC
R119: 19.2k / 0.1%; R_0603_1608Metric; MPN RT0603BRD0719K2L
R120: 10k / 1%; R_0603_1608Metric; MPN RC0603FR-0710KL
U114: TPS22950CQDDCRQ1; TI_DDC0006A; MPN TPS22950CQDDCRQ1

Connections:
GND: C114.2, R119.2, U114.3 (GND)
HOST_3V3: R120.1
USB_5V: C114.1, U114.1 (ON), U114.2 (VIN)
USB_CHG_5V: U114.5 (VOUT)
USB_LIMIT_FAULT_N: R120.2, U114.6 (FLT)
USB_LIMIT_SET: R119.1, U114.4 (ILIM)

Notes on the sheet:
USB INPUT CURRENT LIMITER — COLD START AND QUALIFIED SOURCE
Engineering draft: default50mA nominal; dynamic overshoot, startup and combined corners require bench verification.
01 ALWAYS-AVAILABLE LOW-CURRENT INPUT
R119 stays fitted. R116/Q110/Q111 on sheet12 add a parallel1k branch only after qualification. BQ25895 input capacitor C101 is downstream. BQ ILIM R103 is fixed300R; D+/D- stay NC. TPS22950CQDDCRQ1 is the qualified50mA leaded Q1 variant. Industrial C/L are NOT substitutes.
02 DEFAULT INPUT AND RECOVERY SEQUENCE
Default:34/50/66mA at19.2k in TI table. 0.1% resistor adds finite tolerance. No formula for guaranteed extrema is supplied. The sizeable100mA margin is an engineering assessment; verify complete-board input draw. Once cells and NTC are qualified, device OFF allows slow depleted-pack recovery before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
03 ASSEMBLY / SOURCE / TRANSIENT QUALIFICATION
U114:TI DDC0006A leaded6-pin package,0.95mm pitch,3.05mm maximum terminal span,1.1mm maximum height. Use TI DDC0006A lands. Only the exact Q1 part retains the50mA range; do not substitute industrial TPS22950C. Input C114 is4.7uF16V close to VIN; its effective capacitance and raw-input inrush are re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
