magnus188/trimix-analysator/hardware/system-review/electrical/before-standard-parts/Environment.kicad_sch

## KiCad design hardware/system-review/electrical/before-standard-parts/Environment.kicad_sch (2026-09-07)

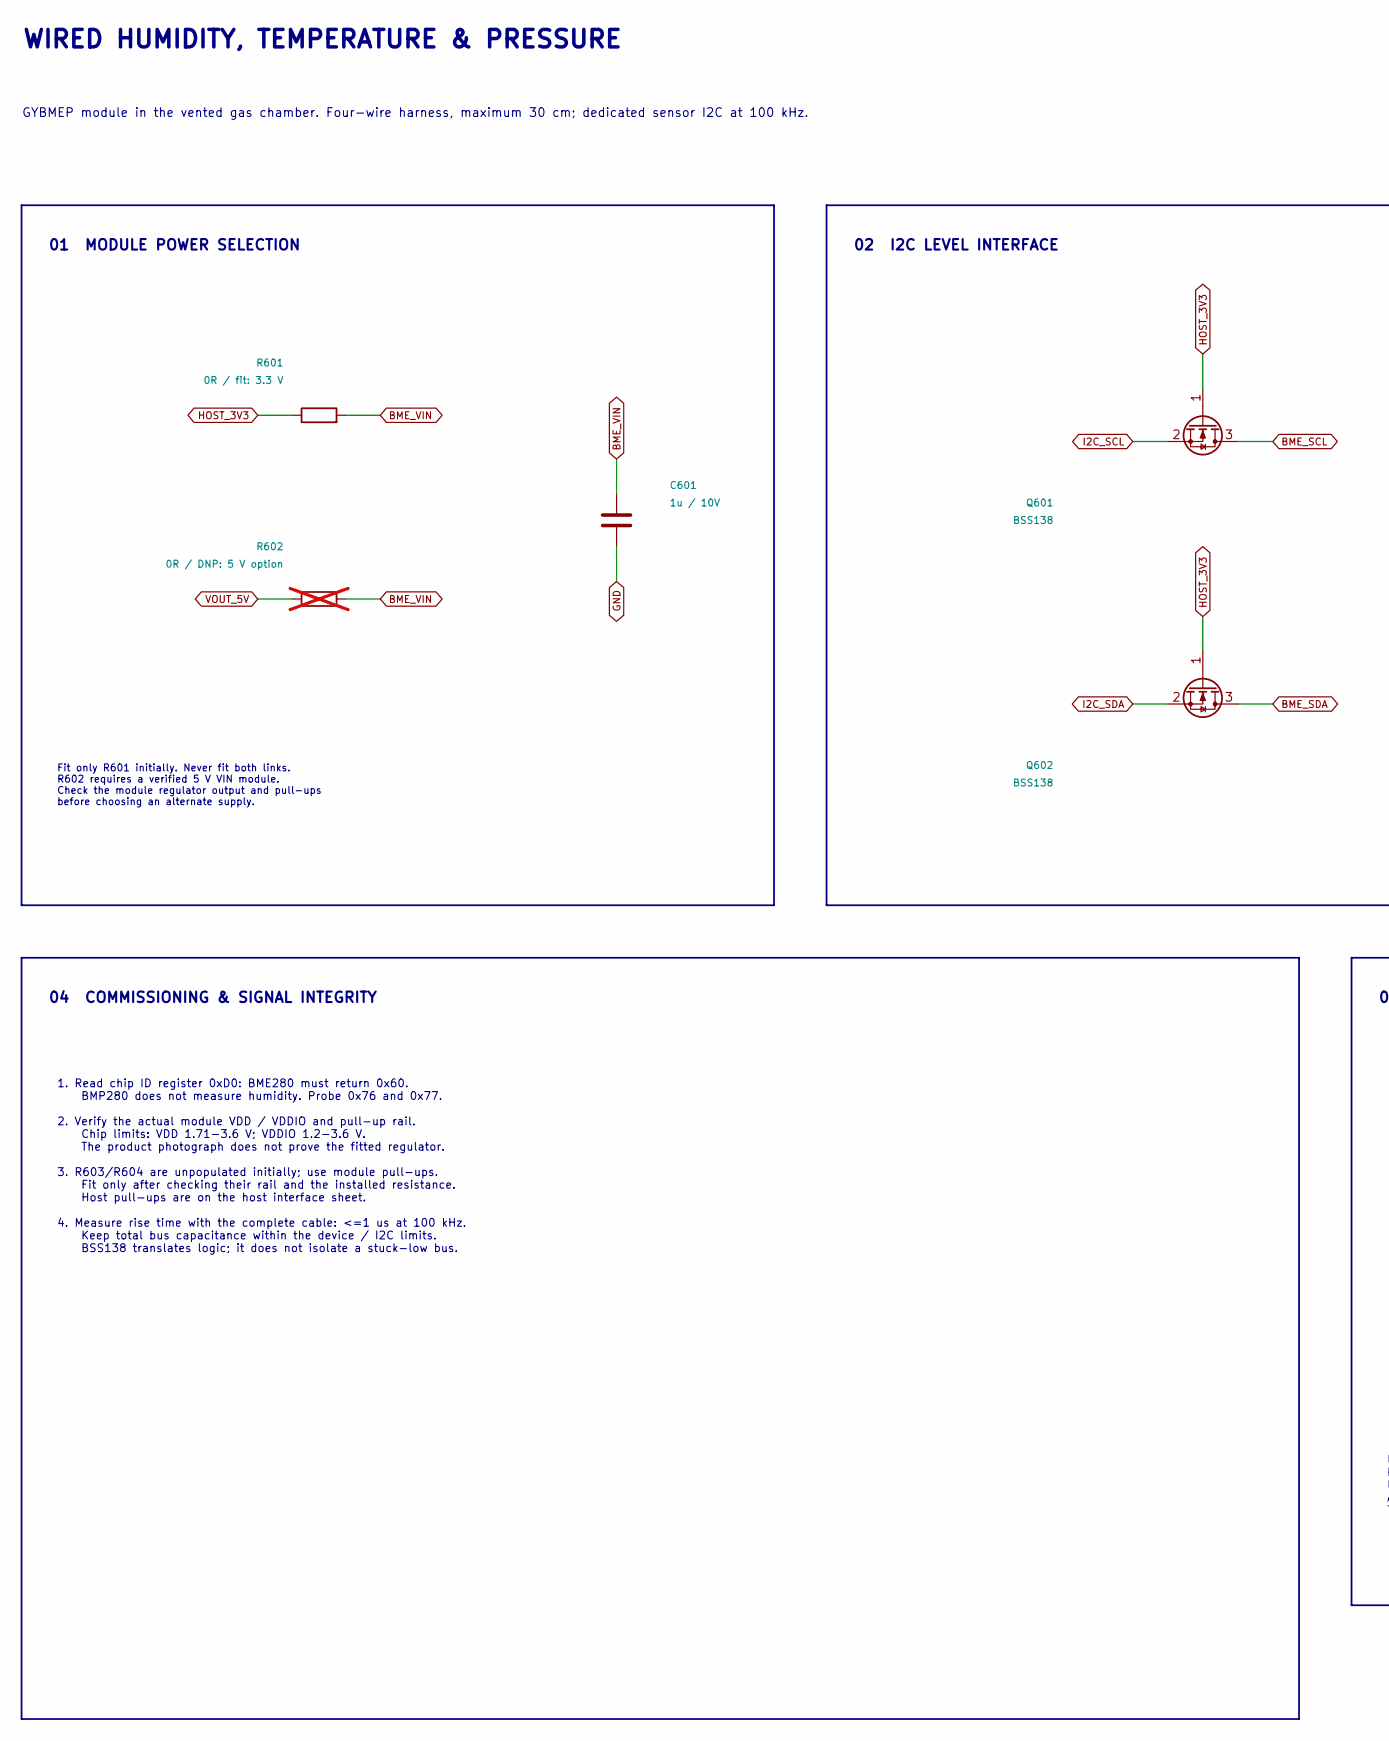
[picture p299: schematic Environment.kicad_sch, part in row 1, column 1]


Parts:
C601: 1u / 10V; C_0805_2012Metric
J601: BME280 harness; JST_XH_B4B-XH-A_1x04_P2.50mm_Vertical
Q601, Q602: BSS138; SOT-23
R601: 0R / fit: 3.3 V; R_0603_1608Metric
R602: 0R / DNP: 5 V option; R_0603_1608Metric; not fitted
R603, R604: 4.7k / DNP; R_0603_1608Metric; not fitted
U601: GYBMEP / BME280-5V

Connections:
BME_SCL: J601.3 (SCL), Q601.3 (D), R603.2, U601.3 (SCL)
BME_SDA: J601.4 (SDA), Q602.3 (D), R604.2, U601.4 (SDA)
BME_VIN: C601.1, J601.1 (VIN), R601.2, R602.2, R603.1, R604.1, U601.1 (VIN)
GND: C601.2, J601.2 (GND), U601.2 (GND)
HOST_3V3: Q601.1 (G), Q602.1 (G), R601.1
I2C_SCL: Q601.2 (S)
I2C_SDA: Q602.2 (S)
VOUT_5V: R602.1

Notes on the sheet:
02 I2C LEVEL INTERFACE
GYBMEP module in the vented gas chamber. Four-wire harness, maximum 30 cm; dedicated sensor I2C at 100 kHz.
03 PCB HARNESS CONNECTION
05 REMOTE MODULE IN THE CHAMBER
Main PCB: JST-XH, 2.50 mm, 4 positions. Wire to the module labels, not its board colour. VIN / GND / SCL / SDA, as photographed. Use strain relief at both cable ends.
Fit only R601 initially. Never fit both links. R602 requires a verified 5 V VIN module. Check the module regulator output and pull-ups before choosing an alternate supply.
U601 is off-board; only J601 is mounted on the main PCB. Keep the sensor away from the MD62 heater and regulator. Use a regulated, vented chamber near atmospheric pressure. Allow gas contact with the sensor opening; prevent condensation. This chamber sensor does not replace the battery thermistor.
1. Read chip ID register 0xD0: BME280 must return 0x60. BMP280 does not measure humidity. Probe 0x76 and 0x77. 2. Verify the actual module VDD / VDDIO and pull-up rail. Chip limits: VDD 1.71-3.6 V; VDDIO 1.2-3.6 V. The product photograph does not prove the fitted regulator. 3. R603/R604 are unpopul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
WIRED HUMIDITY, TEMPERATURE & PRESSURE
04 COMMISSIONING & SIGNAL INTEGRITY
01 MODULE POWER SELECTION
