magnus188/trimix-analysator/hardware/system-review/electrical/before-standard-parts/Gauge_Interface.kicad_sch

## KiCad design hardware/system-review/electrical/before-standard-parts/Gauge_Interface.kicad_sch (2026-09-09)

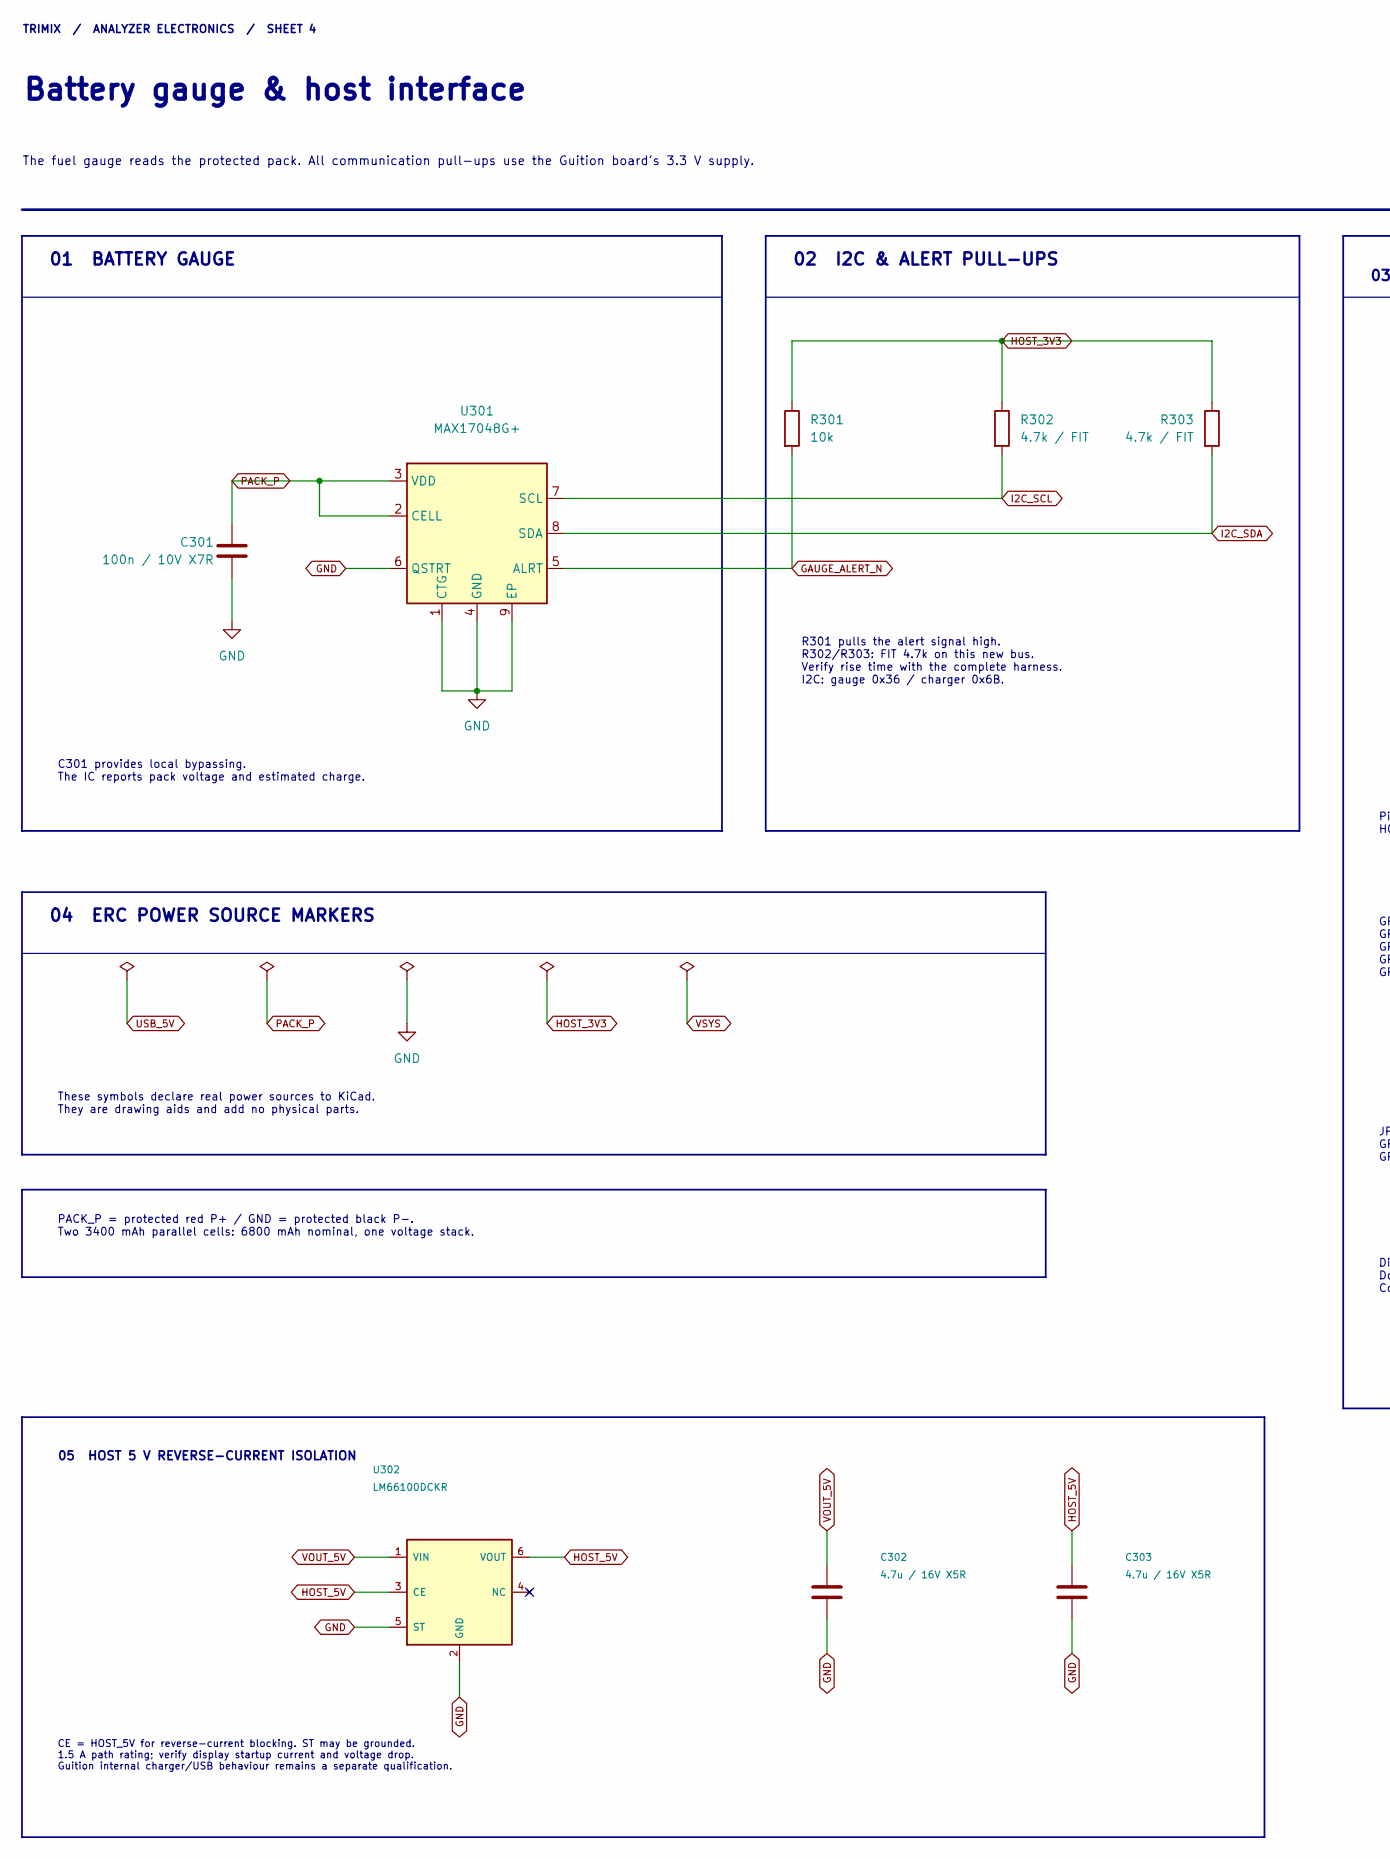
[picture p300: schematic Gauge_Interface.kicad_sch, part in row 1, column 1]


Parts:
C301: 100n / 10V X7R; C_0805_2012Metric
C302, C303: 4.7u / 16V X5R; C_0603_1608Metric; MPN C1608X5R1C475K080AC
J301: GUITION JP1 / 2x13; PinHeader_2x13_P2.54mm_Vertical
R301: 10k; R_0603_1608Metric
R302, R303: 4.7k / FIT; R_0603_1608Metric
U301: MAX17048G+; TDFN-8-1EP_2x2mm_P0.5mm_EP0.8x1.2mm
U302: LM66100DCKR; SOT-363_SC-70-6; MPN LM66100DCKR

Connections:
CHG_INT_N: J301.13
CO_UART_EN: J301.9
CO_UART_RX: J301.10
CO_UART_TX: J301.12
GAUGE_ALERT_N: R301.2, U301.5 (ALRT)
GND: C301.2, C302.2, C303.2, J301.5, J301.6, J301.16, U301.1 (CTG), U301.4 (GND), U301.6 (QSTRT), U301.9 (EP), U302.2 (GND), U302.5 (ST)
HE_ENABLE: J301.17
HOST_3V3: J301.1, J301.3, J301.18, R301.1, R302.1, R303.1
HOST_5V: C303.1, J301.2, J301.4, U302.3 (CE), U302.6 (VOUT)
I2C_SCL: J301.14, R302.2, U301.7 (SCL)
I2C_SDA: J301.21, R303.2, U301.8 (SDA)
PACK_P: C301.1, U301.2 (CELL), U301.3 (VDD)
POWER_INT_N: J301.19
POWER_KILL_N: J301.8
USB_ILIM_AUTH: J301.11
VOUT_5V: C302.1, U302.1 (VIN)

Notes on the sheet:
Pin numbers match the vendor JP1 drawing. Confirm the physical mating view. HOST_5V flows through U302 TO Guition; HOST_3V3 returns FROM its regulator.
C301 provides local bypassing. The IC reports pack voltage and estimated charge.
TRIMIX / ANALYZER ELECTRONICS / SHEET 4
The fuel gauge reads the protected pack. All communication pull-ups use the Guition board's 3.3 V supply.
04 ERC POWER SOURCE MARKERS
03 GUITION JP1 — POWER & SIGNALS
Battery gauge & host interface
These symbols declare real power sources to KiCad. They are drawing aids and add no physical parts.
GPIO28 / pin21 = I2C SDA GPIO29 / pin14 = I2C SCL GPIO30 / pin12 = CO TX GPIO31 / pin10 = CO RX (host perspective) GPIO32 / pin19 = power INT GPIO33 / pin8 = power KILL GPIO34 / pin17 = He enable GPIO49 / pin13 = charger INT GPIO50 / pin11 = USB current AUTH GPIO51 / pin9 = CO UART enable
01 BATTERY GAUGE
R301 pulls the alert signal high. R302/R303: FIT 4.7k on this new bus. Verify rise time with the complete harness. I2C: gauge 0x36 / charger 0x6B.
02 I2C & ALERT PULL-UPS
JP1 pins 23/25 belong to the existing GPIO7/8 touch bus and are unused here. GPIO35 (BOOT), GPIO52 and ESP32-C6 pins are deliberately unconnected. GPIO28/29 I2C is implemented; physical harness and rise time remain to be tested.
PACK_P = protected red P+ / GND = protected black P-. Two 3400 mAh parallel cells: 6800 mAh nominal, one voltage stack.
Disconnect Guition USB power for the button to switch the device fully off. Do not connect the protected pack to Guition CN4 / its onboard charger. Connector pitch, mechanical mate and cable ampacity remain to be verified.
05 HOST 5 V REVERSE-CURRENT ISOLATION
CE = HOST_5V for reverse-current blocking. ST may be grounded. 1.5 A path rating; verify display startup current and voltage drop. Guition internal charger/USB behaviour remains a separate qualification.
