magnus188/trimix-analysator/hardware/system-review/electrical/before-standard-parts/Oxygen.kicad_sch

## KiCad design hardware/system-review/electrical/before-standard-parts/Oxygen.kicad_sch (2026-09-09)

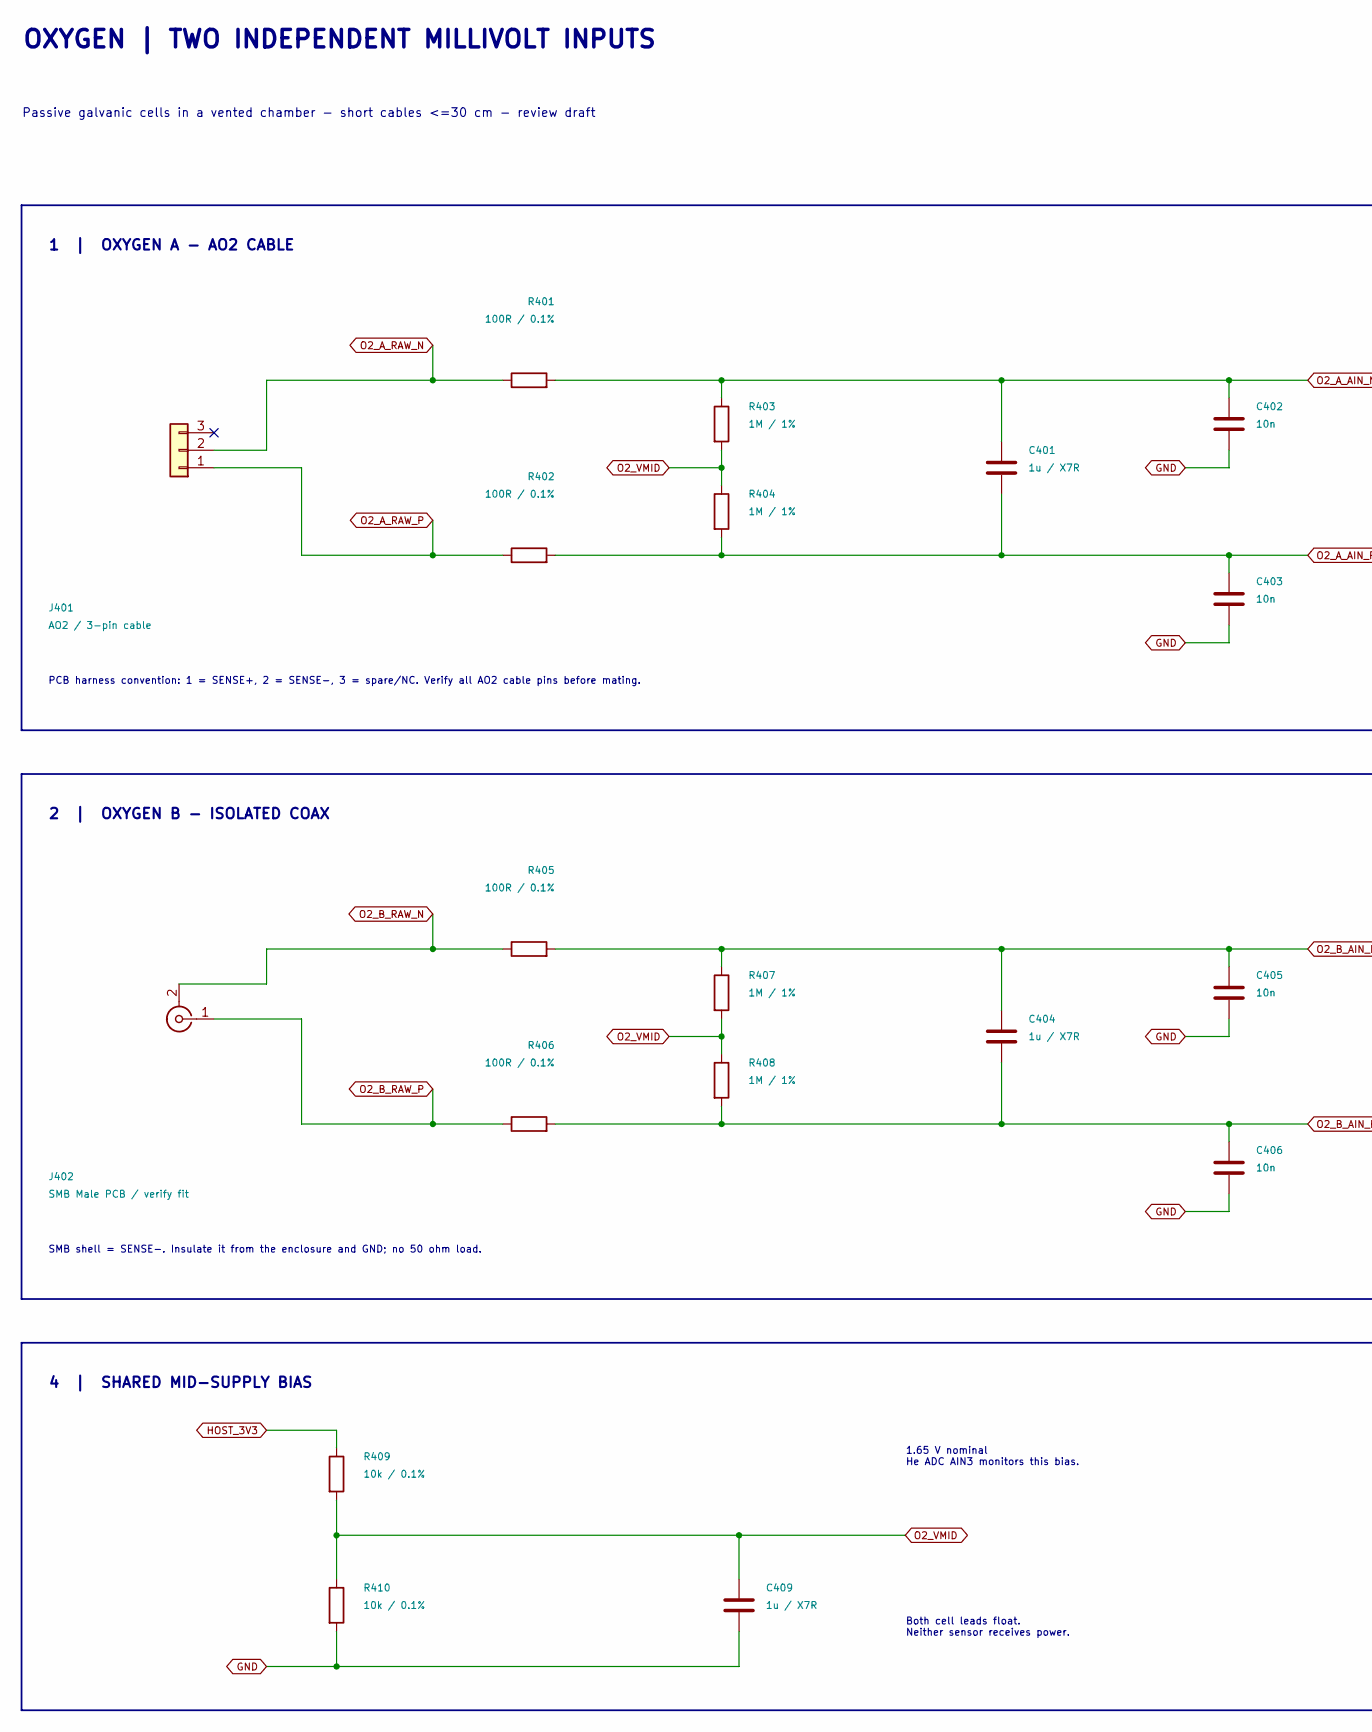
[picture p301: schematic Oxygen.kicad_sch, part in row 1, column 1]

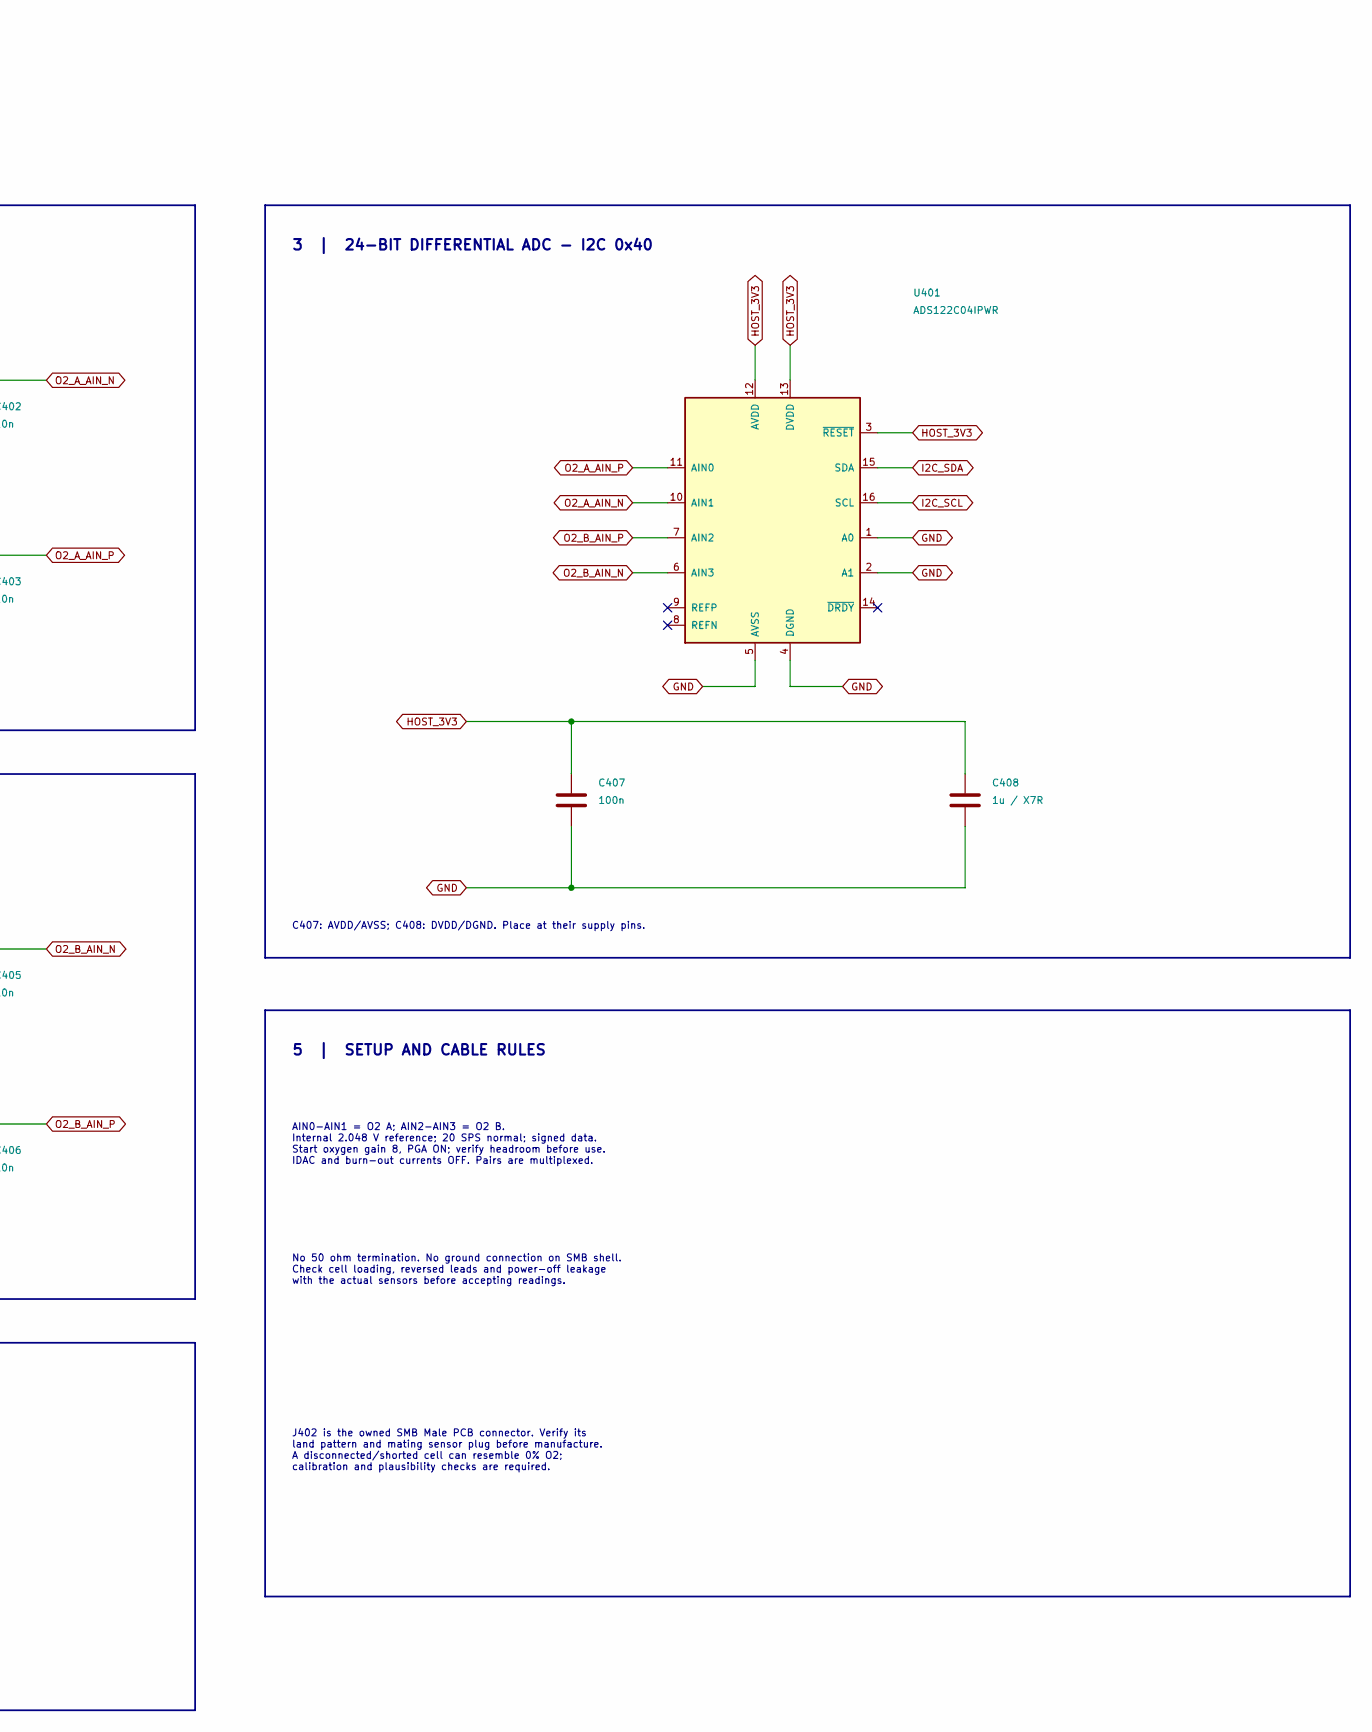
[picture p302: schematic Oxygen.kicad_sch, part in row 1, column 2]

Parts:
C401, C404, C408, C409: 1u / X7R; C_0603_1608Metric
C402, C403, C405, C406: 10n; C_0603_1608Metric
C407: 100n; C_0603_1608Metric
J401: AO2 / 3-pin cable; PinHeader_1x03_P2.54mm_Vertical
J402: SMB Male PCB / verify fit; SMB_Jack_Vertical
R401, R402, R405, R406: 100R / 0.1%; R_0603_1608Metric
R403, R404, R407, R408: 1M / 1%; R_0603_1608Metric
R409, R410: 10k / 0.1%; R_0603_1608Metric
U401: ADS122C04IPWR; TSSOP-16_4.4x5mm_P0.65mm; MPN ADS122C04IPWR

Connections:
GND: C402.2, C403.2, C405.2, C406.2, C407.2, C408.2, C409.2, R410.2, U401.1 (A0), U401.2 (A1), U401.4 (DGND), U401.5 (AVSS)
HOST_3V3: C407.1, C408.1, R409.1, U401.3 (~RESET), U401.12 (AVDD), U401.13 (DVDD)
I2C_SCL: U401.16 (SCL)
I2C_SDA: U401.15 (SDA)
O2_A_AIN_N: C401.1, C402.1, R401.2, R403.1, U401.10 (AIN1)
O2_A_AIN_P: C401.2, C403.1, R402.2, R404.2, U401.11 (AIN0)
O2_A_RAW_N: J401.2, R401.1
O2_A_RAW_P: J401.1, R402.1
O2_B_AIN_N: C404.1, C405.1, R405.2, R407.1, U401.6 (AIN3)
O2_B_AIN_P: C404.2, C406.1, R406.2, R408.2, U401.7 (AIN2)
O2_B_RAW_N: J402.2 (Ext), R405.1
O2_B_RAW_P: J402.1 (In), R406.1
O2_VMID: C409.1, R403.2, R404.1, R407.2, R408.1, R409.2, R410.1

Notes on the sheet:
PCB harness convention: 1 = SENSE+, 2 = SENSE-, 3 = spare/NC. Verify all AO2 cable pins before mating.
SMB shell = SENSE-. Insulate it from the enclosure and GND; no 50 ohm load.
2 | OXYGEN B - ISOLATED COAX
No 50 ohm termination. No ground connection on SMB shell. Check cell loading, reversed leads and power-off leakage with the actual sensors before accepting readings.
4 | SHARED MID-SUPPLY BIAS
Both cell leads float. Neither sensor receives power.
1 | OXYGEN A - AO2 CABLE
AIN0-AIN1 = O2 A; AIN2-AIN3 = O2 B. Internal 2.048 V reference; 20 SPS normal; signed data. Start oxygen gain 8, PGA ON; verify headroom before use. IDAC and burn-out currents OFF. Pairs are multiplexed.
3 | 24-BIT DIFFERENTIAL ADC - I2C 0x40
5 | SETUP AND CABLE RULES
Passive galvanic cells in a vented chamber - short cables <=30 cm - review draft
C407: AVDD/AVSS; C408: DVDD/DGND. Place at their supply pins.
J402 is the owned SMB Male PCB connector. Verify its land pattern and mating sensor plug before manufacture. A disconnected/shorted cell can resemble 0% O2; calibration and plausibility checks are required.
OXYGEN | TWO INDEPENDENT MILLIVOLT INPUTS
1.65 V nominal He ADC AIN3 monitors this bias.
