magnus188/trimix-analysator/hardware/system-review/electrical/before-standard-parts/Power_Control.kicad_sch

## KiCad design hardware/system-review/electrical/before-standard-parts/Power_Control.kicad_sch (2026-09-07)

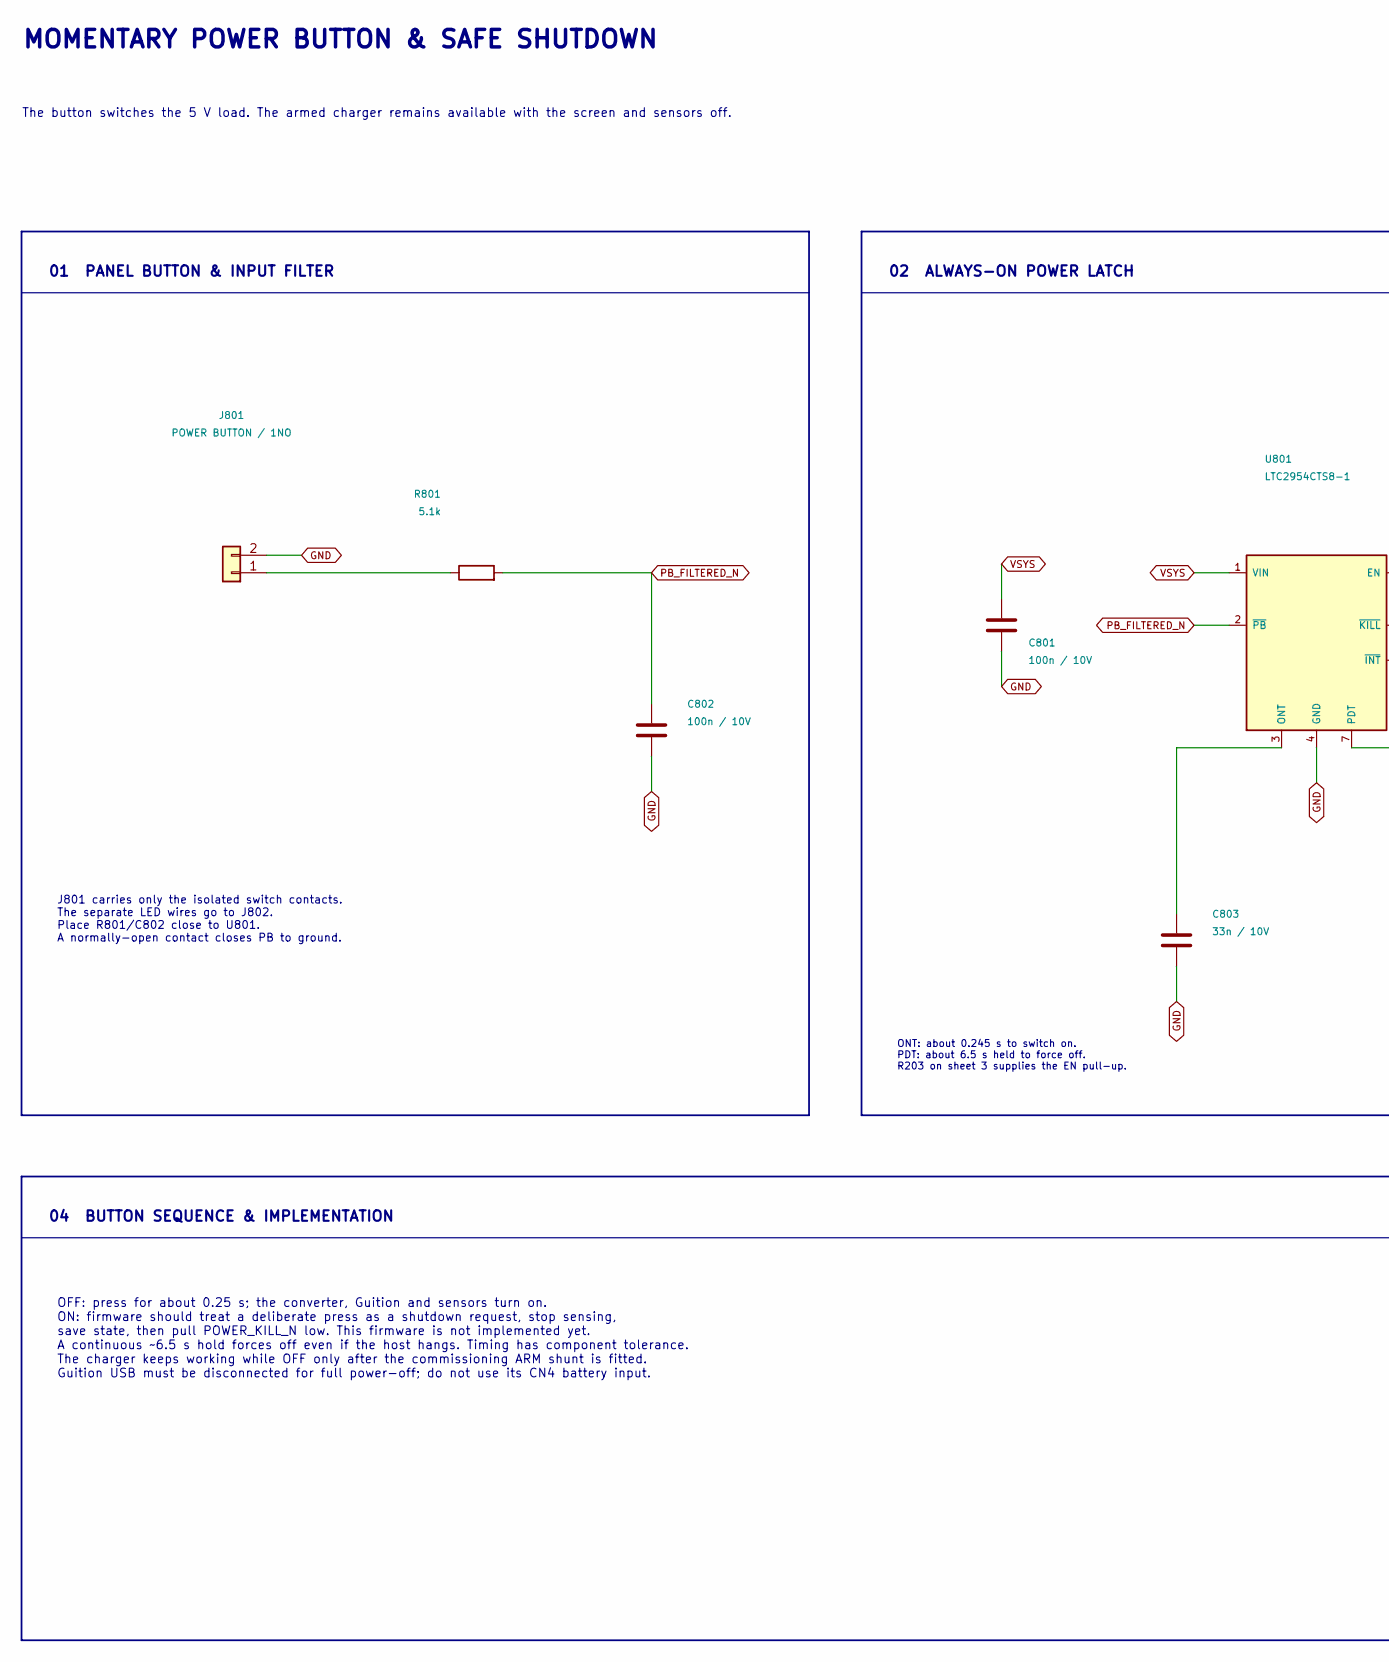
[picture p303: schematic Power_Control.kicad_sch, part in row 1, column 1]

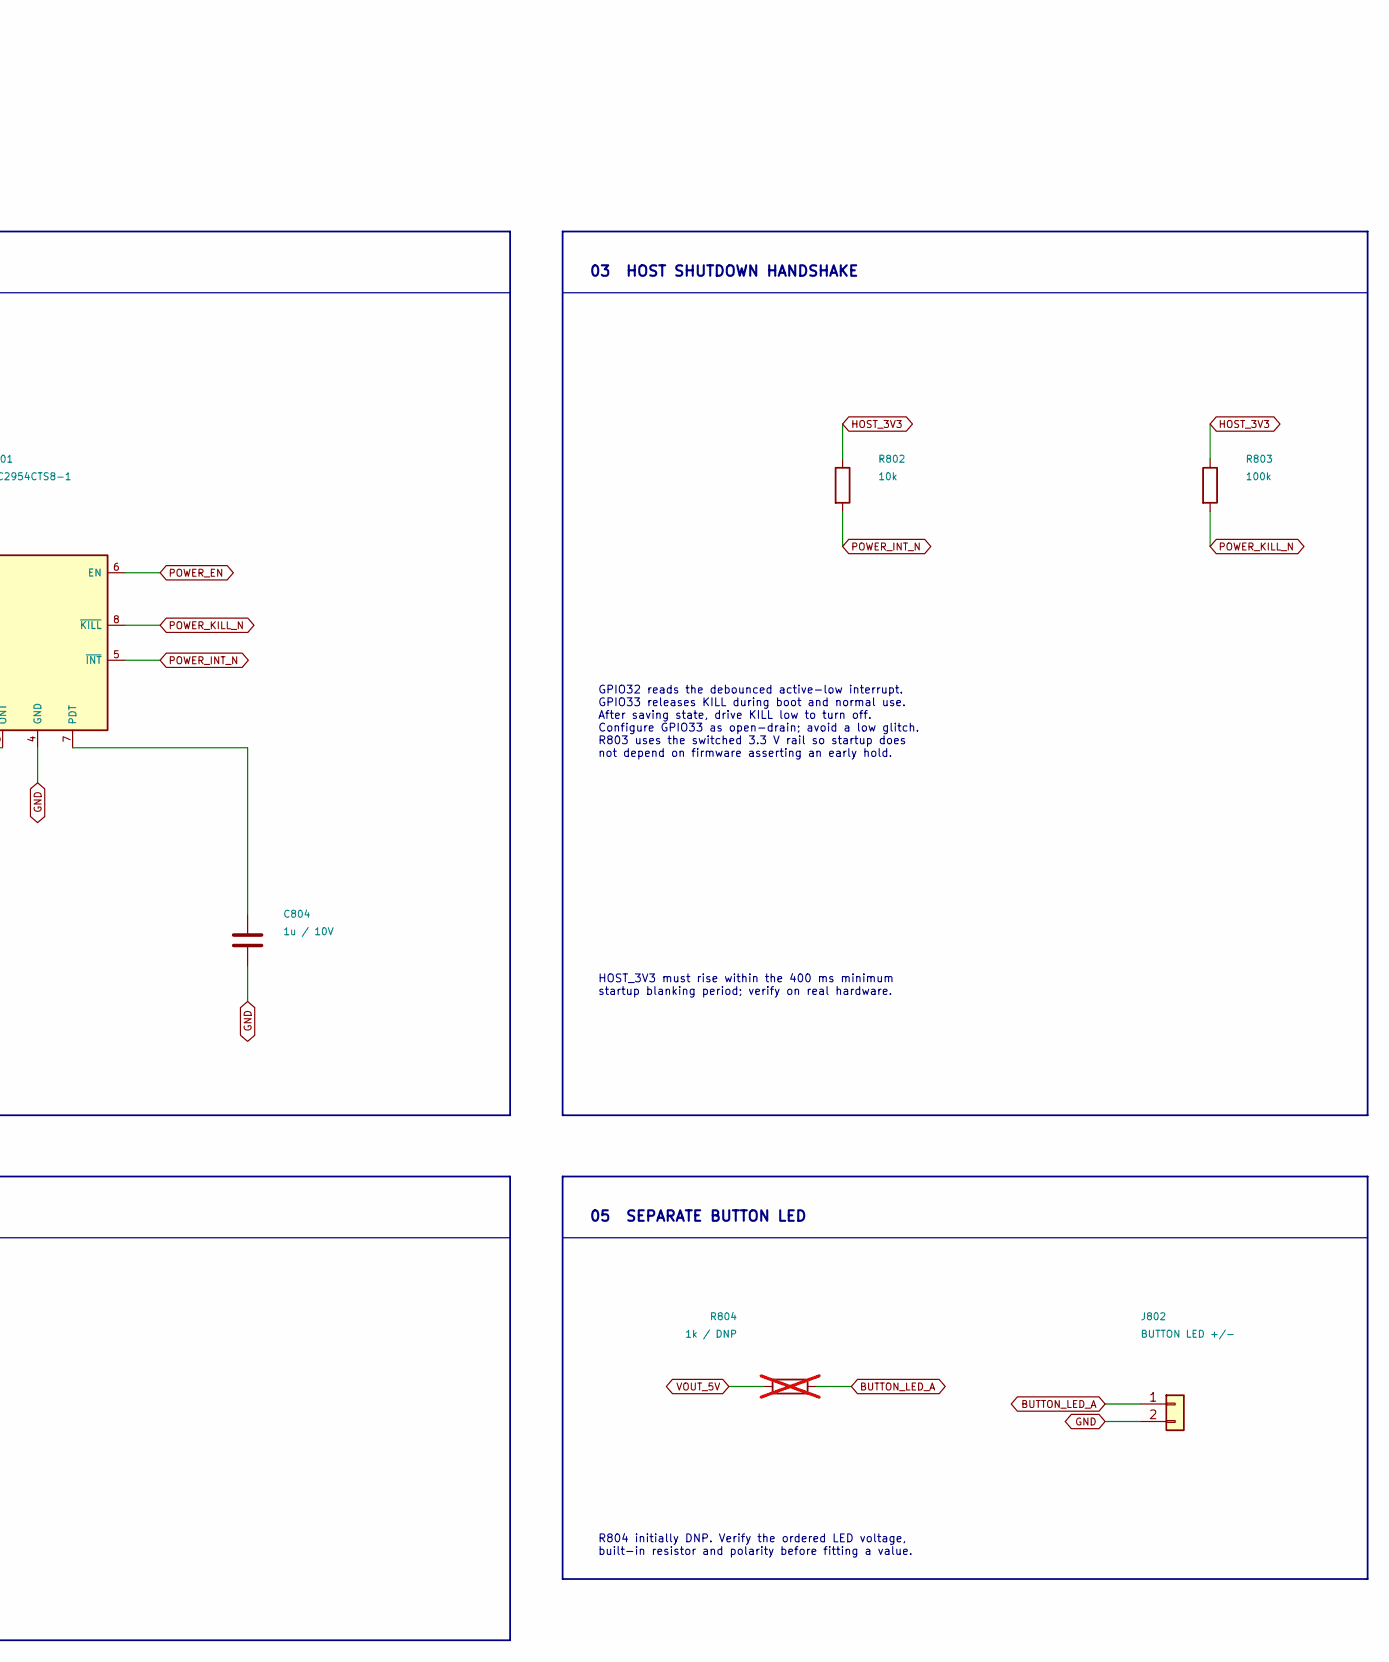
[picture p304: schematic Power_Control.kicad_sch, part in row 1, column 2]

Parts:
C801, C802: 100n / 10V; C_0805_2012Metric
C803: 33n / 10V; C_0805_2012Metric
C804: 1u / 10V; C_0805_2012Metric
J801: POWER BUTTON / 1NO; PinHeader_1x02_P2.54mm_Vertical
J802: BUTTON LED +/-; PinHeader_1x02_P2.54mm_Vertical
R801: 5.1k; R_0603_1608Metric
R802: 10k; R_0603_1608Metric
R803: 100k; R_0603_1608Metric
R804: 1k / DNP; R_0603_1608Metric; not fitted
U801: LTC2954CTS8-1; TSOT-23-8

Connections:
BUTTON_LED_A: J802.1, R804.2
GND: C801.2, C802.2, C803.2, C804.2, J801.2, J802.2, U801.4 (GND)
HOST_3V3: R802.1, R803.1
unnamed: C803.1, U801.3 (ONT)
unnamed: C804.1, U801.7 (PDT)
unnamed: J801.1, R801.1
PB_FILTERED_N: C802.1, R801.2, U801.2 (~PB)
POWER_EN: U801.6 (EN)
POWER_INT_N: R802.2, U801.5 (~INT)
POWER_KILL_N: R803.2, U801.8 (~KILL)
VOUT_5V: R804.1
VSYS: C801.1, U801.1 (VIN)

Notes on the sheet:
02 ALWAYS-ON POWER LATCH
01 PANEL BUTTON & INPUT FILTER
The button switches the 5 V load. The armed charger remains available with the screen and sensors off.
04 BUTTON SEQUENCE & IMPLEMENTATION
J801 carries only the isolated switch contacts. The separate LED wires go to J802. Place R801/C802 close to U801. A normally-open contact closes PB to ground.
05 SEPARATE BUTTON LED
MOMENTARY POWER BUTTON & SAFE SHUTDOWN
GPIO32 reads the debounced active-low interrupt. GPIO33 releases KILL during boot and normal use. After saving state, drive KILL low to turn off. Configure GPIO33 as open-drain; avoid a low glitch. R803 uses the switched 3.3 V rail so startup does not depend on firmware asserting an early hold.
HOST_3V3 must rise within the 400 ms minimum startup blanking period; verify on real hardware.
03 HOST SHUTDOWN HANDSHAKE
OFF: press for about 0.25 s; the converter, Guition and sensors turn on. ON: firmware should treat a deliberate press as a shutdown request, stop sensing, save state, then pull POWER_KILL_N low. This firmware is not implemented yet. A continuous ~6.5 s hold forces off even if the host hangs. Timing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
R804 initially DNP. Verify the ordered LED voltage, built-in resistor and polarity before fitting a value.
ONT: about 0.245 s to switch on. PDT: about 6.5 s held to force off. R203 on sheet 3 supplies the EN pull-up.
