magnus188/trimix-analysator/hardware/system-review/electrical/before-standard-parts/USB_Input_Limiter.kicad_sch

## KiCad design hardware/system-review/electrical/before-standard-parts/USB_Input_Limiter.kicad_sch (2026-09-09)

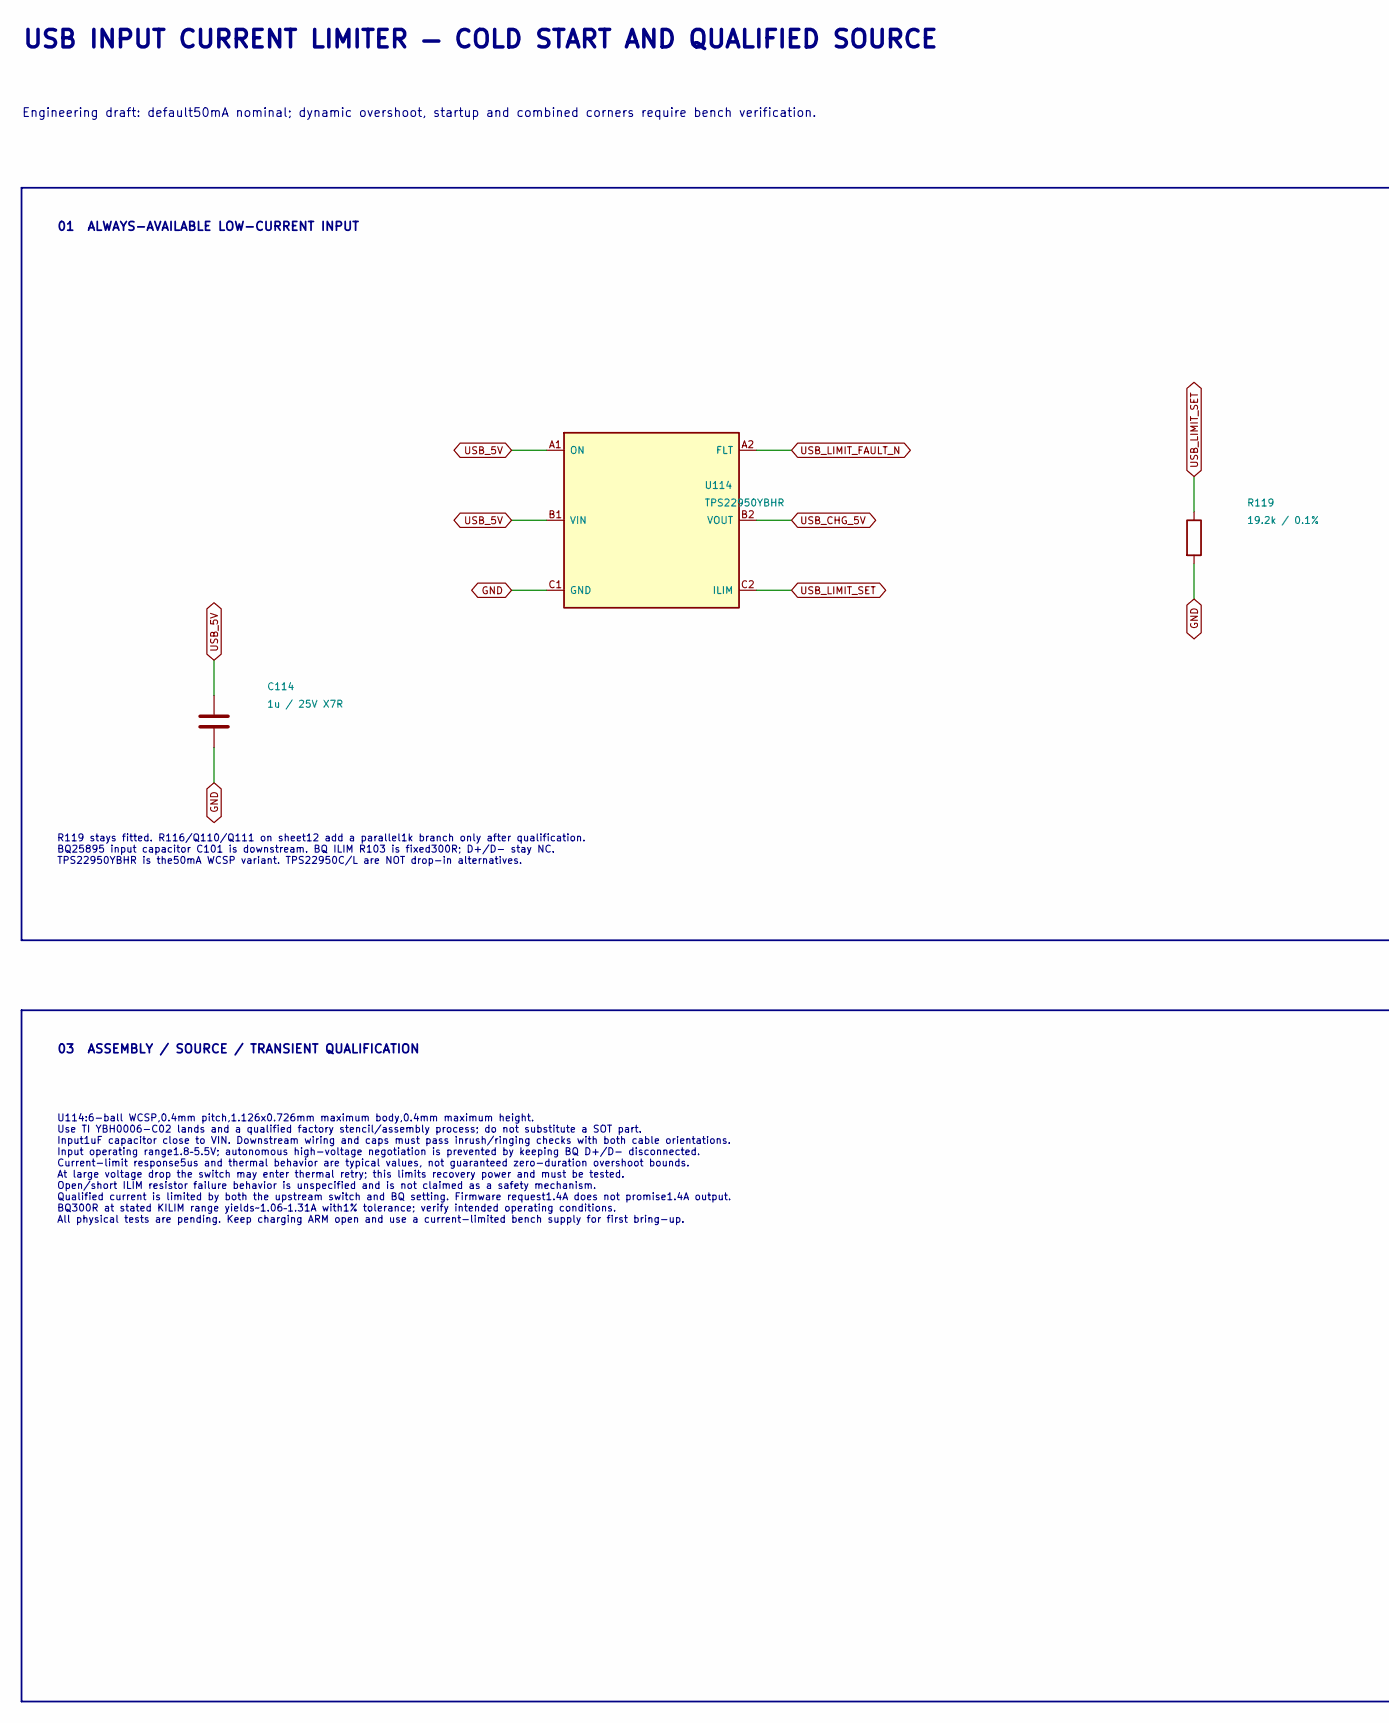
[picture p306: schematic USB_Input_Limiter.kicad_sch, part in row 1, column 1]


Parts:
C114: 1u / 25V X7R; C_0805_2012Metric; MPN C2012X7R1E105K125AB
R119: 19.2k / 0.1%; R_0603_1608Metric
R120: 10k / 1%; R_0603_1608Metric
U114: TPS22950YBHR; TPS22950_YBH6; MPN TPS22950YBHR

Connections:
GND: C114.2, R119.2, U114.C1 (GND)
HOST_3V3: R120.1
USB_5V: C114.1, U114.A1 (ON), U114.B1 (VIN)
USB_CHG_5V: U114.B2 (VOUT)
USB_LIMIT_FAULT_N: R120.2, U114.A2 (FLT)
USB_LIMIT_SET: R119.1, U114.C2 (ILIM)

Notes on the sheet:
USB INPUT CURRENT LIMITER — COLD START AND QUALIFIED SOURCE
Engineering draft: default50mA nominal; dynamic overshoot, startup and combined corners require bench verification.
01 ALWAYS-AVAILABLE LOW-CURRENT INPUT
R119 stays fitted. R116/Q110/Q111 on sheet12 add a parallel1k branch only after qualification. BQ25895 input capacitor C101 is downstream. BQ ILIM R103 is fixed300R; D+/D- stay NC. TPS22950YBHR is the50mA WCSP variant. TPS22950C/L are NOT drop-in alternatives.
02 DEFAULT INPUT AND RECOVERY SEQUENCE
Default:34/50/66mA at19.2k in TI table. 0.1% resistor adds finite tolerance. No formula for guaranteed extrema is supplied. The sizeable100mA margin is an engineering assessment; verify complete-board input draw. Once cells and NTC are qualified, device OFF allows slow depleted-pack recovery before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
03 ASSEMBLY / SOURCE / TRANSIENT QUALIFICATION
U114:6-ball WCSP,0.4mm pitch,1.126x0.726mm maximum body,0.4mm maximum height. Use TI YBH0006-C02 lands and a qualified factory stencil/assembly process; do not substitute a SOT part. Input1uF capacitor close to VIN. Downstream wiring and caps must pass inrush/ringing checks with both cable orientat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
