magnus188/trimix-analysator/hardware/system-review/electrical/before-usb-source/USB_Input.kicad_sch

## KiCad design hardware/system-review/electrical/before-usb-source/USB_Input.kicad_sch (2026-09-07)



Parts:
J901: GCT USB4720-03-A; USB_C_GCT_USB4720-03-A_A3; MPN USB4720-03-A
J902: TO MAIN PCB J101; SolderWire-0.25sqmm_1x02_P4.2mm_D0.65mm_OD1.7mm
R901, R902: 5.1k / 1%; R_0603_1608Metric

Connections:
GND: J901.A1 (GND), J901.A12 (GND), J901.B1 (GND), J901.B12 (GND), J901.SH (SHIELD), J902.2, R901.2, R902.2
USB_5V: J901.A4 (VBUS), J901.A9 (VBUS), J901.B4 (VBUS), J901.B9 (VBUS), J902.1
USB_CC1: J901.A5 (CC1), R901.1
USB_CC2: J901.B5 (CC2), R902.1

Notes on the sheet:
USB INPUT | GCT USB4720-03-A DAUGHTERBOARD
5 V charging from USB-A or USB-C. Separate 0.60 mm USB PCB; main charger PCB remains 1.60 mm.
01 GCT SOCKET + TWO CC RESISTORS
02 TWO-WIRE OUTPUT TO CHARGER
03 CABLES, ORIENTATION & CURRENT
04 MECHANICS & VERIFICATION
CC1 and CC2 stay separate; fit both resistors. All four VBUS and all four GND contacts are connected. Data / SBU pins are unused. Shield connects to GND. This is a passive 5 V sink, with no PD controller.
J902 pin 1 -> positive wire -> J101 pin 1 J902 pin 2 -> return wire -> J101 pin 2
J901 / R901 / R902 / J902 belong to the USB PCB. The main charger retains its two-wire input. Use soldered leads with enclosure strain relief; wire size and final mounting remain to be checked.
USB-C charger + C-to-C cable: separate Rd on CC1 / CC2 allows source attachment in either plug orientation. Test both ends flipped, including an electronically marked cable. USB-A charging adapter + A-to-C cable uses the same input. The compliant legacy cable supplies Rp; do not add Rp here. BQ2589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
GCT drawing: 0.60 +/- 0.10 mm PCB and edge cutout. Do not fit USB4720 directly to the 1.60 mm main board. Provide rigid support against cable insertion forces. IP67 connector does not certify the enclosure; charge dry. Before power: verify CC1-GND and CC2-GND ~5.1k. With ARM OPEN: verify 5 V in all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
