magnus188/trimix-analysator/main/services/backlight_service.h

#pragma once

#include <cstdint>

#ifdef __cplusplus
extern "C" {
#endif

/**
 * Initialize the backlight PWM controller
 * Call this once at startup
 */
void backlight_init(void);

/**
 * Set backlight brightness
 * @param percent Brightness level 0-100 (0 = off, 100 = full)
 */
void backlight_set(uint8_t percent);

/**
 * Get current backlight brightness
 * @return Current brightness level 0-100
 */
uint8_t backlight_get(void);

#ifdef __cplusplus
}
#endif
